nsynet/electronics_project2/Medtronic_PB560呼吸机开源资料(3D图纸_原理图_说明书_软件代码等)/Medtronic PB560 ventilator-system-file-set-1/Electrical Schematics/PB560 - Electrical Schematics/4096600E03001_CPU BOARD SCH.pdf

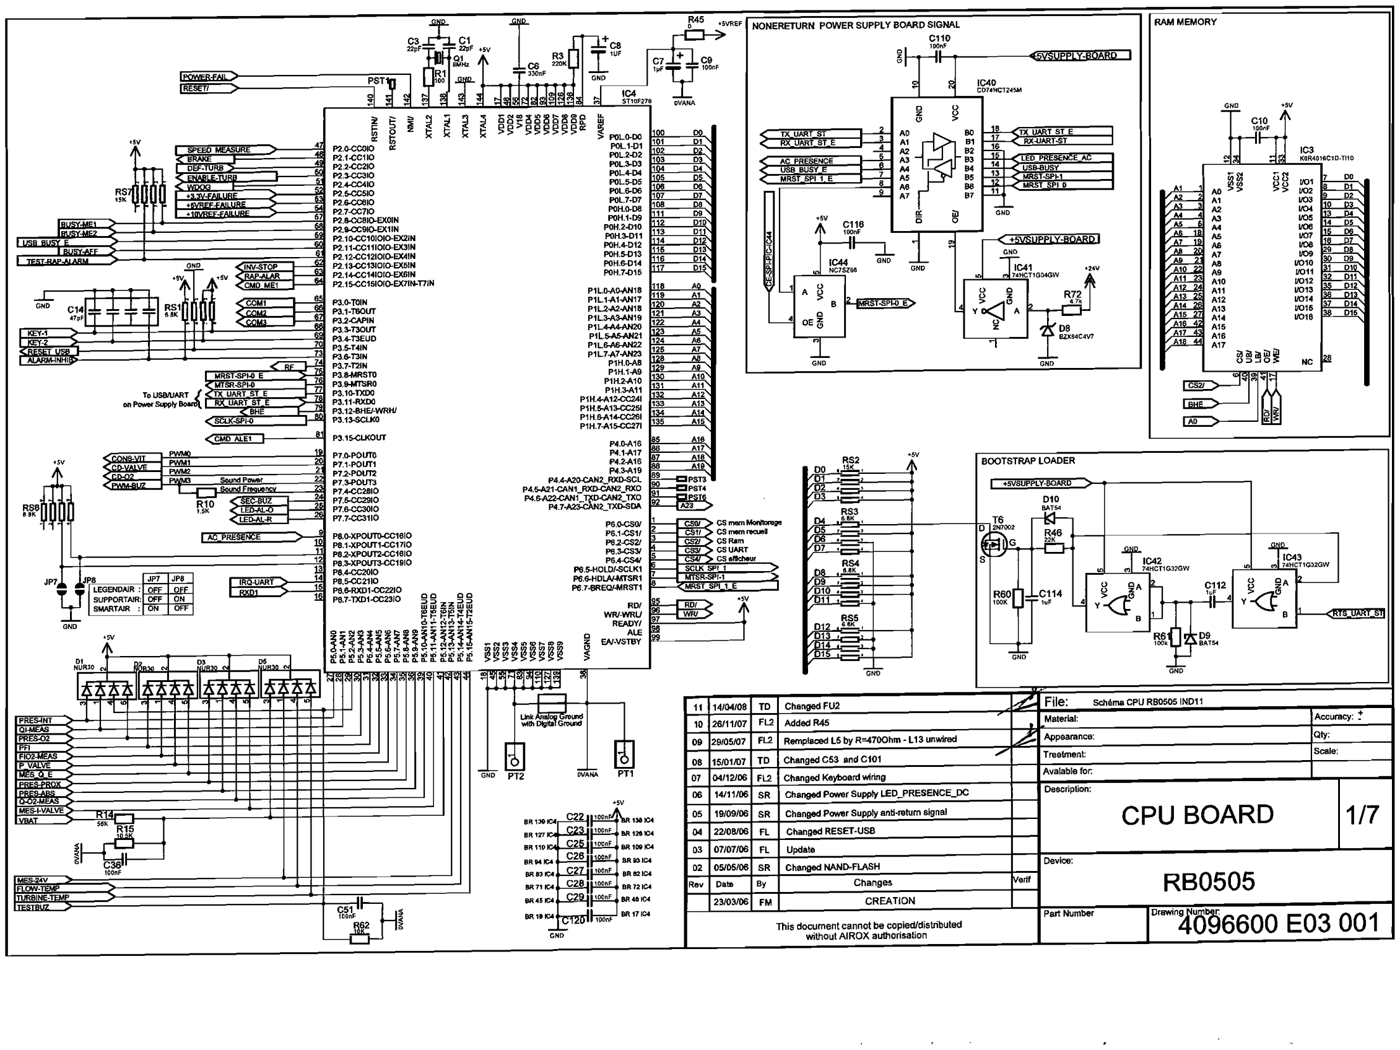
[picture p3: page 1]
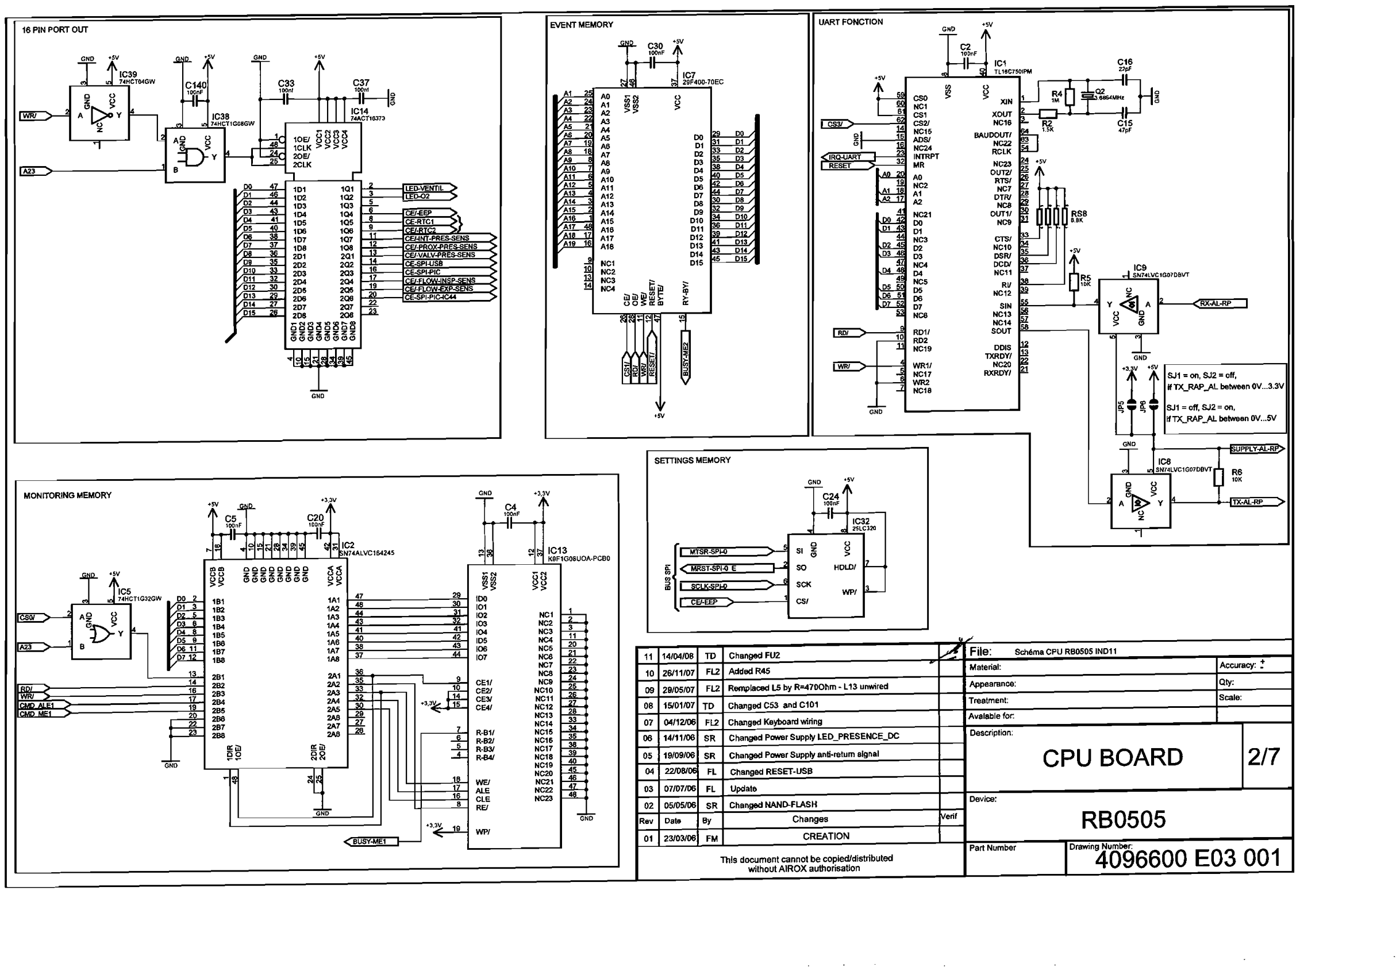
[picture p4: page 2]

1 100
105 lQ5
lm | | 1-
107 lQ7
108 | 108 201 | 2Ql
202 2-
203 | 2Q3 2 | 200
205 2W

MONITORING MEMORY

# CPU BOARD

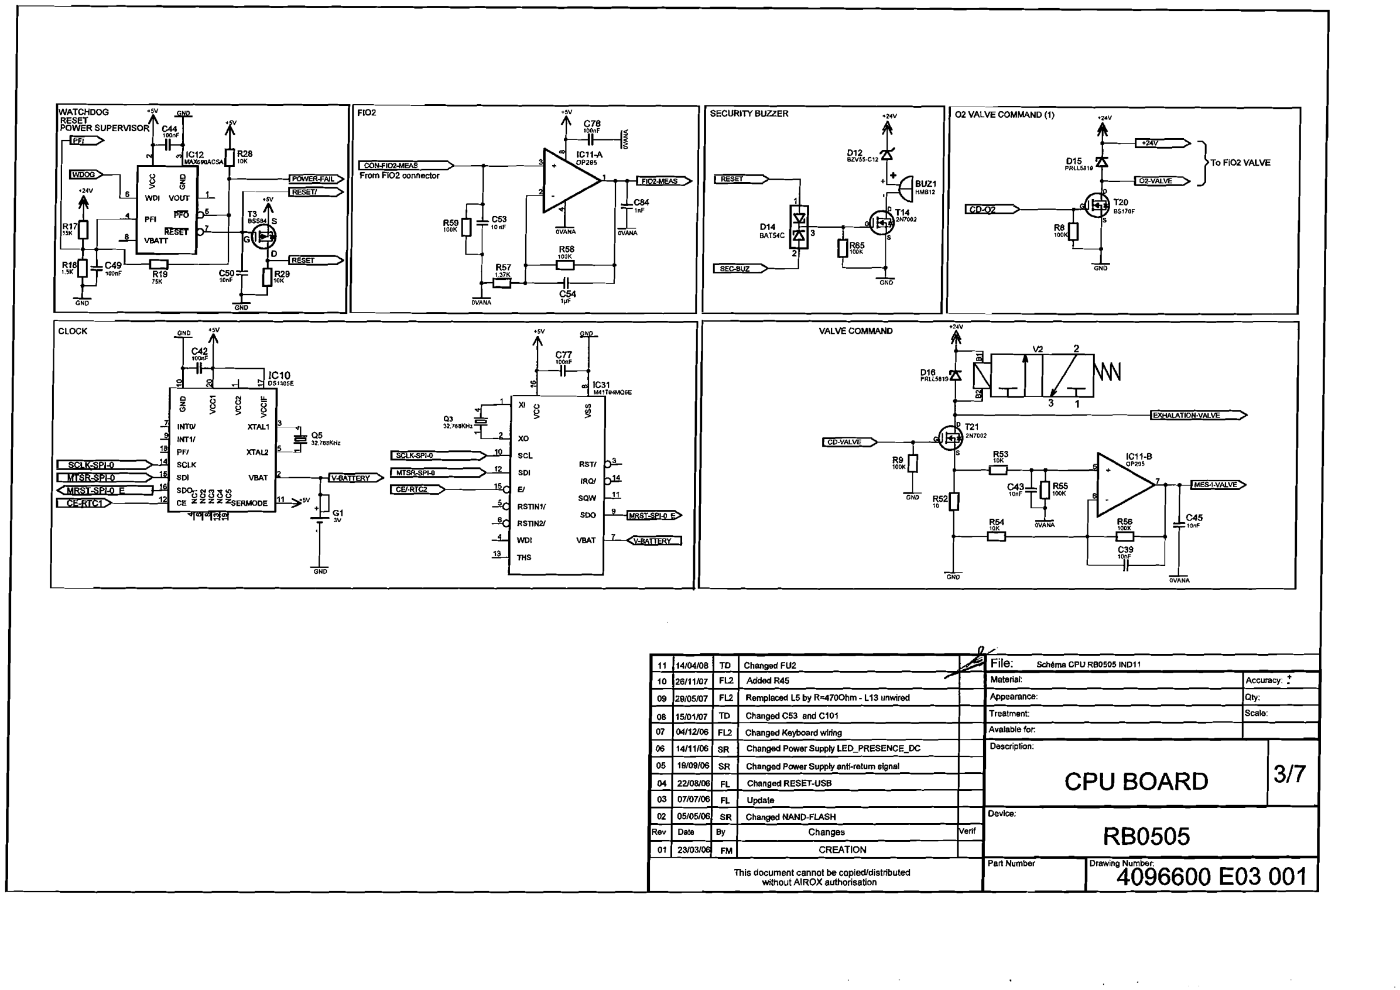
[picture p5: page 3]
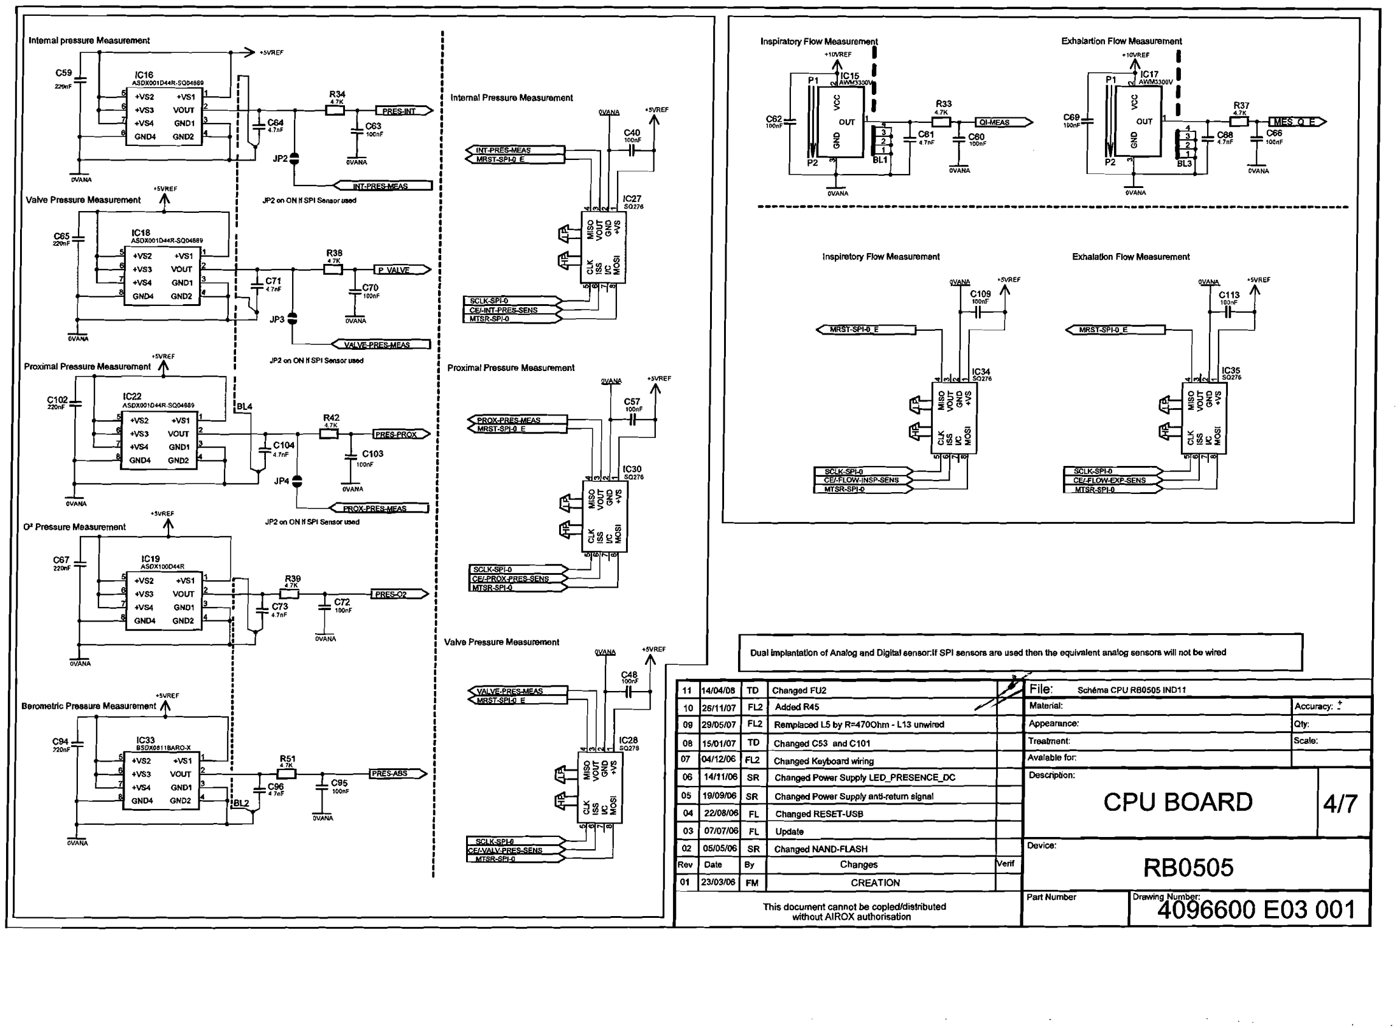
[picture p6: page 4]
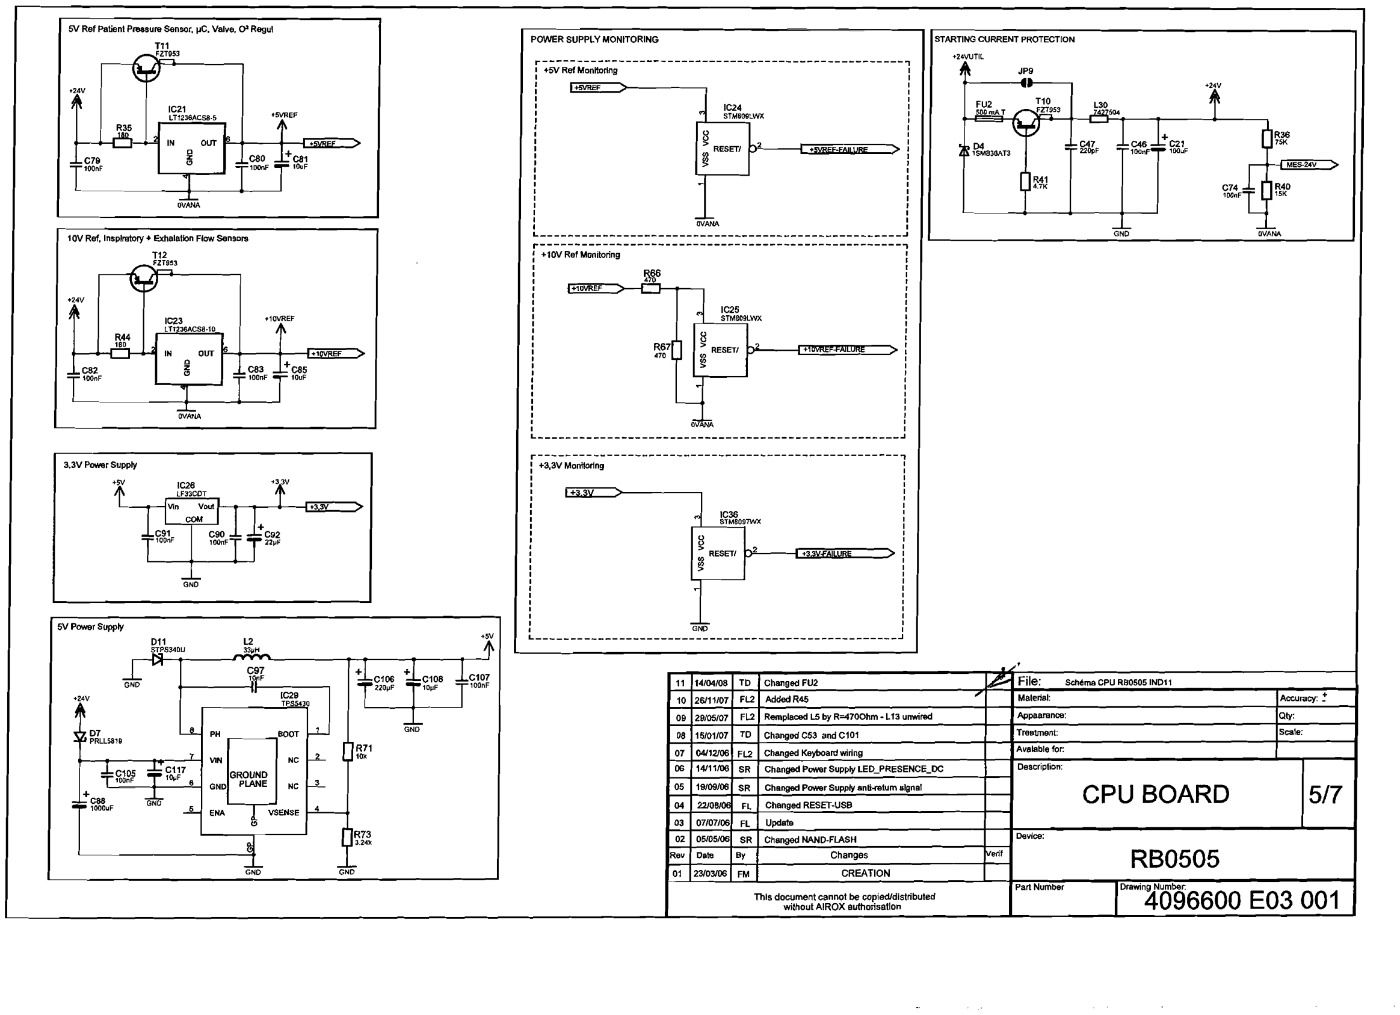
[picture p7: page 5]

( | 1 SV Rwf Paânt P-um | Senwrr. pC. Valve. W Rwgul | I
I I | I
1OV Rd. lnsplmtory + Exhalabn Flow Sanson | I
I | GND

POWER SUPPLY MONITORING

r----------------------------------------------------
: +1OV Re1 Monitoring | I

/?
File: | sdieme cpu ~eosos INDII
Maletisl: | (~ccuraq: f
OB 2BMSlo7 FL2 Remplad L5 by R4700hm - LI3 vmired | Appaaranm: | QtV:
08 15101107 TD Changed C53 and Cl01 | Trestmwnt: | Scdle:
07 04112106 FU | Chsnged Keyboaniwillng | Avalable for:
ffi lWlltC8 SR | Changed Paver Svpply LED-PRESENCE-DC | Description:
05 191081ffi SR | ChsM Power Supply anti-tum slgnsl
M WOBIffi FI. | Changed RESET-US0 | CPU BOARD | 517 -
03 07/07106 FL | UpdSl8 | 1 02 OWWffi SR Changed WD-FLASH | Cevice:
RBV Osie | By | Changes | vsdf
01 2YOYffi FM | CREATION
RB0505 Pari Number | Drawing Number

This document cannot be wpiedldistributed

without AIROX suihorisatlon | 1 4096600 E03 001

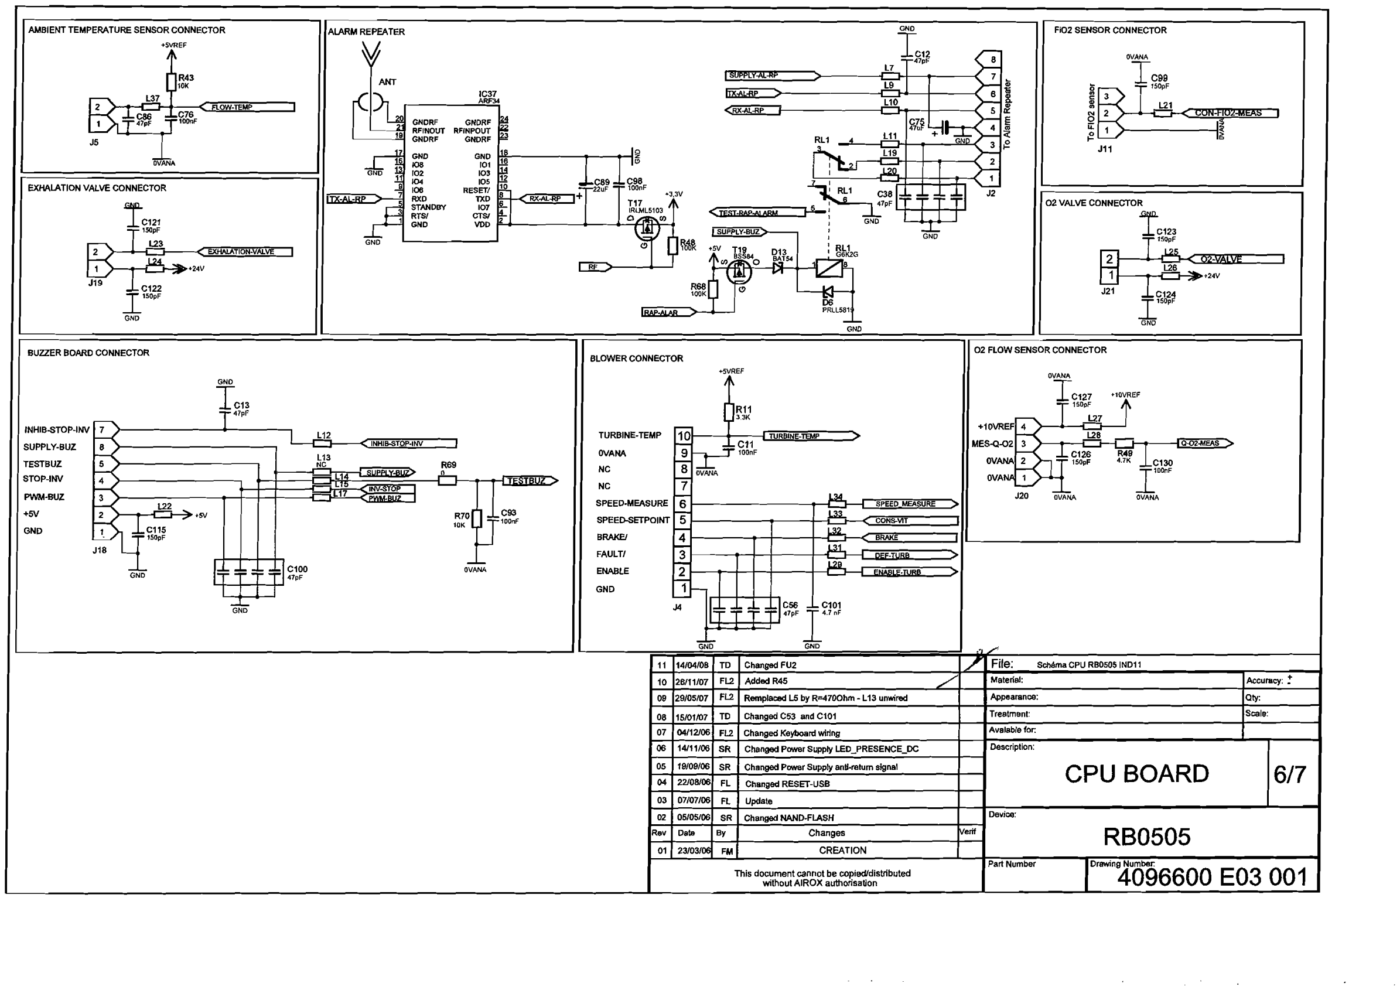
[picture p8: page 6]
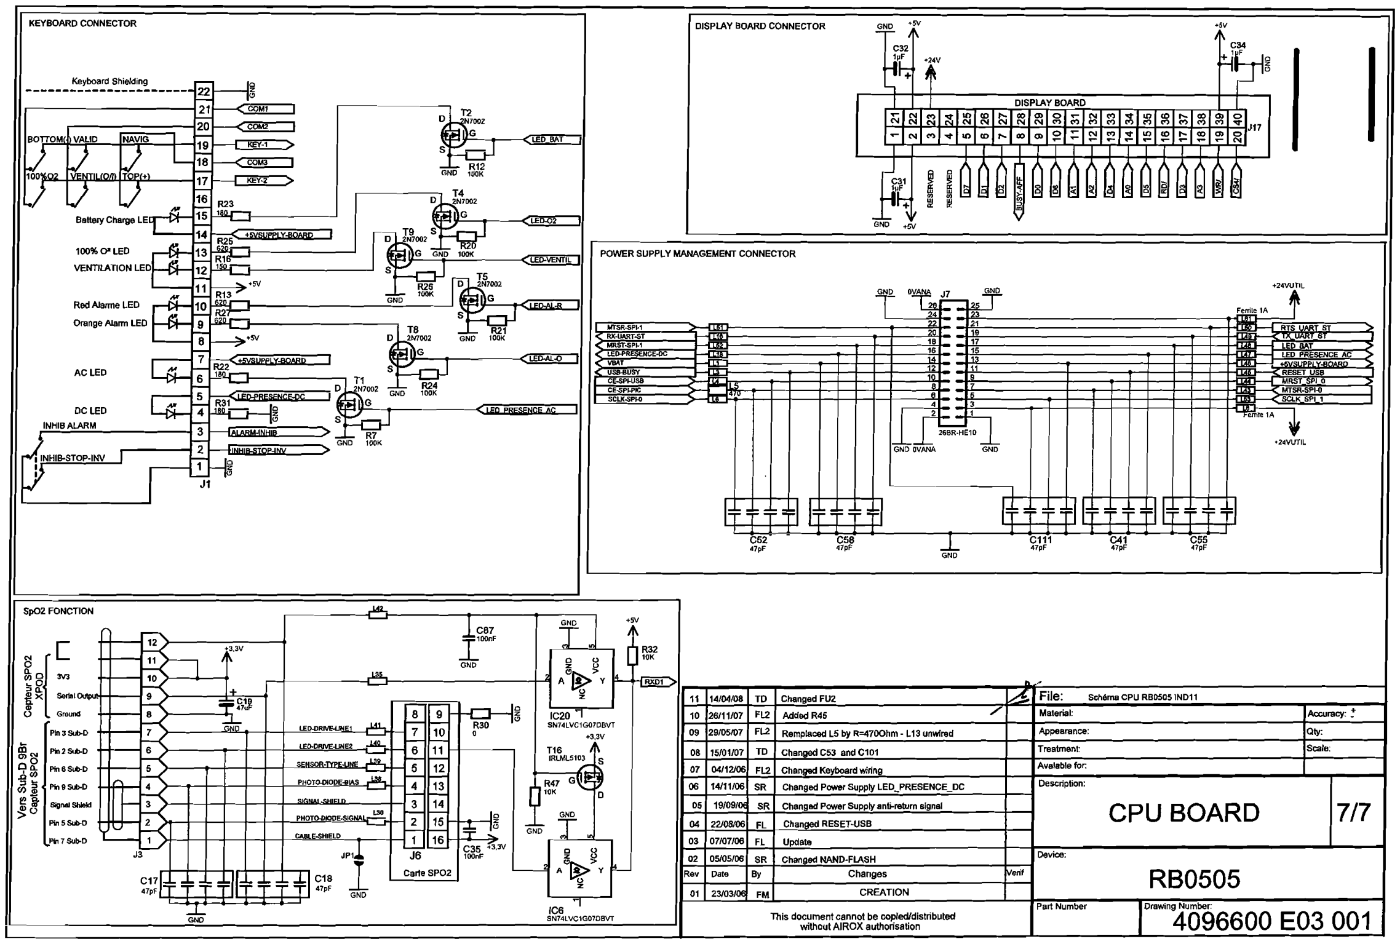
[picture p9: page 7]
