nsynet/electronics_project2/Medtronic_PB560呼吸机开源资料(3D图纸_原理图_说明书_软件代码等)/medtronic-pb560-ventilator-system-file-set-2/Electronic PCBAs/GR106769_CPU_PCBA/PCB/GR106772A00/Read-me.xls

 | Customer : |  | COVIDIEN
 | Designation : |  | CPU BOARD
 | Schem No :
 | Board No : |  | GR106772 | Ind. / Rev. | A
 | FEE File No : |  | CN004 | Ind. / Rev. | A
 | Artwork : Extended GERBER
 | Layers |  | Files
 | Parts Top |  | GR106772-A-CST.phd
 | Silkscreen Top |  | GR106772-A-SST.(phd,pdf)
 | Solder Paste Top |  | GR106772-A-SPT.phd
 | Solder Mask Top |  | GR106772-A-SMT.phd
 | Copper Top |  | GR106772-A-CLT.phd
 | Internal Copper 2 |  | GR106772-A-CL2.phd
 | Internal Copper 3 |  | GR106772-A-CL3.phd
 | Internal Copper 4 |  | GR106772-A-CL4.phd
 | Internal Copper 5 |  | GR106772-A-CL5.phd
 | Internal Copper 6
 | Internal Copper 7
 | Internal Copper 8
 | Internal Copper 9
 | Internal Copper 10
 | Internal Copper 11
 | Copper Bottom |  | GR106772-A-CLB.phd
 | Solder Mask Bottom |  | GR106772-A-SMB.phd
 | Solder Paste Bottom |  | GR106772-A-SPB.phd
 | Silkscreen Bottom |  | GR106772-A-SSB.(phd,pdf)
 | Parts Bottom |  | GR106772-A-CSB.phd
 | Outline |  | GR106772-A-OUT.phd
 | Holes |  | Non Plated Holes | Plated Holes
 | EXCELLON drill file |  | GR106772-A-NPTH.drd | GR106772-A-PTH.drd
 | Drill tool list |  | GR106772-A-NPTH.drl | GR106772-A-PTH.drl
 | Manufacturing |  | Files
 | Drill drawing |  | GR106772-PPD-A.(pdf,hpg,dxf)
 | Assembly drawing |  | GR106772-PEQ-A.(pdf,hpg,dxf)
 | Partlist |  | GR106772-A-partlist.doc
 | ASCII data |  | GR106772-A.(pcf,ftf)
 | IDF data |  | GR106772-A.(pro,brd)
 | Archive file Name : |  | GR106772-AI-A.zip
 |  | Files for manufacturing printed circuit |  |  | 2014-03-19
 |  |  |  |  | Page : 1/1
 |  | GR106772-A
France Etudes Electroniques Rue Jules Ferry 24130 - PRIGONRIEUX Tél: 05.53.24.63.11 Fax: 05.53.24.67.28 E-mail : fee@fee.fr
