nsynet/electronics_project2/Medtronic_PB560呼吸机开源资料(3D图纸_原理图_说明书_软件代码等)/medtronic-pb560-ventilator-system-file-set-2/Mechanical Part Drawings/4-007303-00/4-007303-00F00.pdf

REVISIONS

REV | DESCRIPTION
F | RELEASE/CHANGE PER EC107420

PROPRIETARY & CONFIDENTIAL: THIS DOCUMENT MAY NOT BE COPIED, DISCLOSED, OR USED IN WHOLE OR IN PART WITHOUT THE CONSENT OF MEDTRONIC
TITLE: DESCRIPTION SPECIFICATION BAG,8 X 10, PROTECTIVE | MEDTRONIC 6 1 3 5 G u n b a r r e l A v e n u e B o u l d e r , C o l o r a d o 8 0 3 0 1 © 2 018 M E D T R O N I C A L L R I G H T S R E S E R V E D .
DEC. | DEC. | DEC. | DRAWN: Karla Garcia DATE: 11/06/09 | SIZE | DRAWING NUMBER | REV.
.X ± | .XX ± | .XXX ± | CHECKED: J. Martinez DATE: 11/06/09 | A | 4-007303-00 | F
.1 | .01 | .001 | APPROVED: J. Martinez DATE: 11/06/09 | | SHEET 1 OF 1

GENERAL DIMENSIONAL
TOLERANCES

Template 10026665 Rev 200

## SPECIFICATION:

## BAG,8 X 10, PROTECTIVE

Description: BAG,8 X 10, PROTECTIVE

Material: Polyethylene bag

- Inside Dimensions: 8” (+/- 0.125”) x 10” (+/- 0.1875”)

Thickness: .00132” (+/- .000264”)

Skirt: 0.25” (+/-0.1875”)

Color: Clear

*Packaging:1750 Bags per roll
*Note: The precut is perform from corner to corner of the bag.

*Validated Suppliers for the Poly Bag:
Primary vendor: Southland Flex Products Corporation Secondary vendor: Automated PKG. systems.

The notes marked with the symbol *added in the specification for the TJ site.
- Key Inspection dimensions
