nsynet/electronics_project2/Medtronic_PB560呼吸机开源资料(3D图纸_原理图_说明书_软件代码等)/medtronic-pb560-ventilator-system-file-set-2/Electronic PCBAs/GR106769_CPU_PCBA/PCB/GR106772A00.pdf

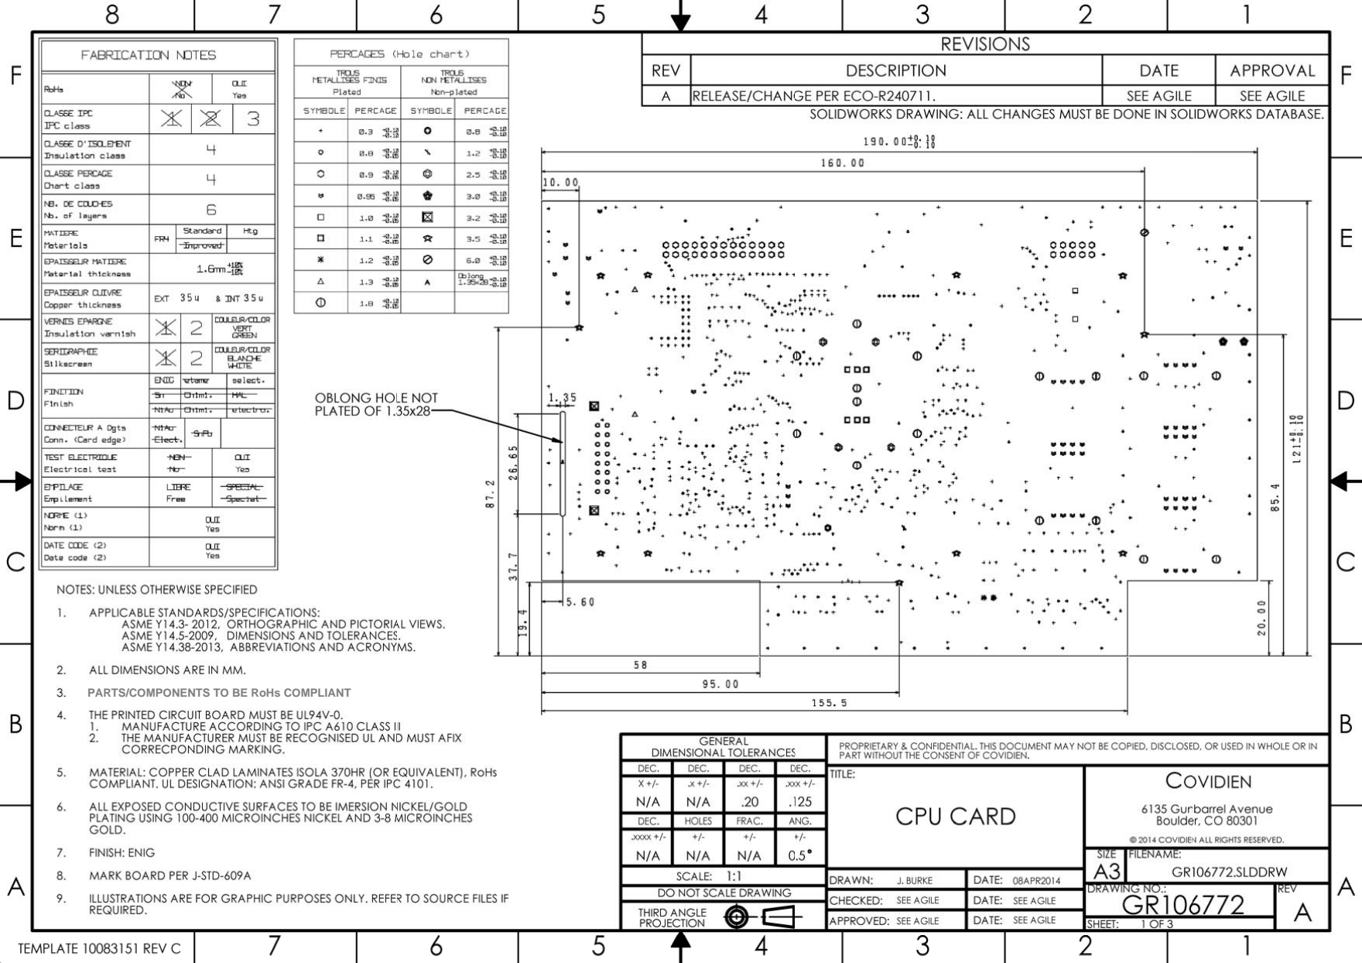
[picture p10: page 1]
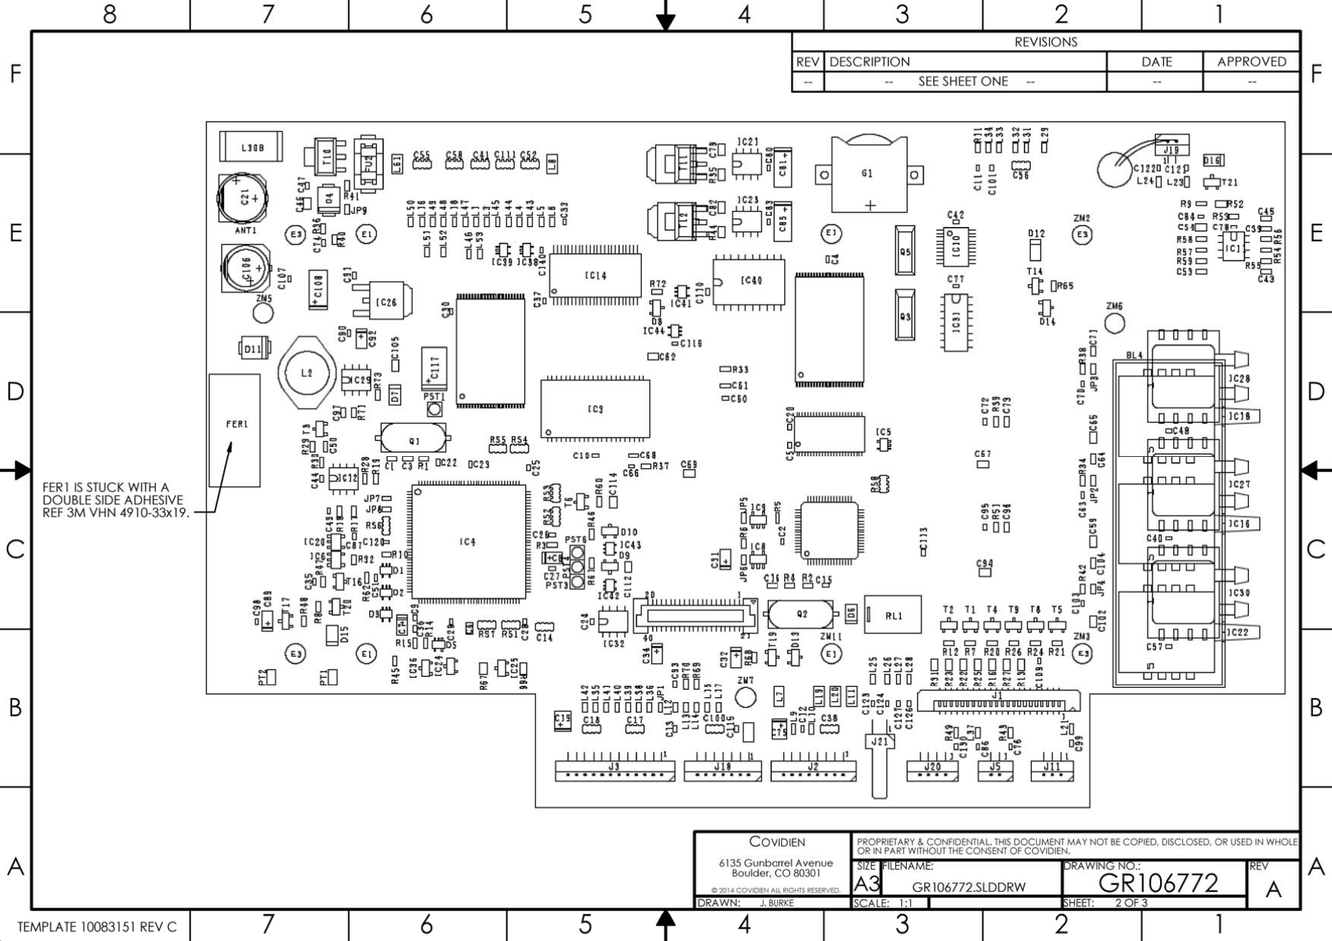
[picture p11: page 2]
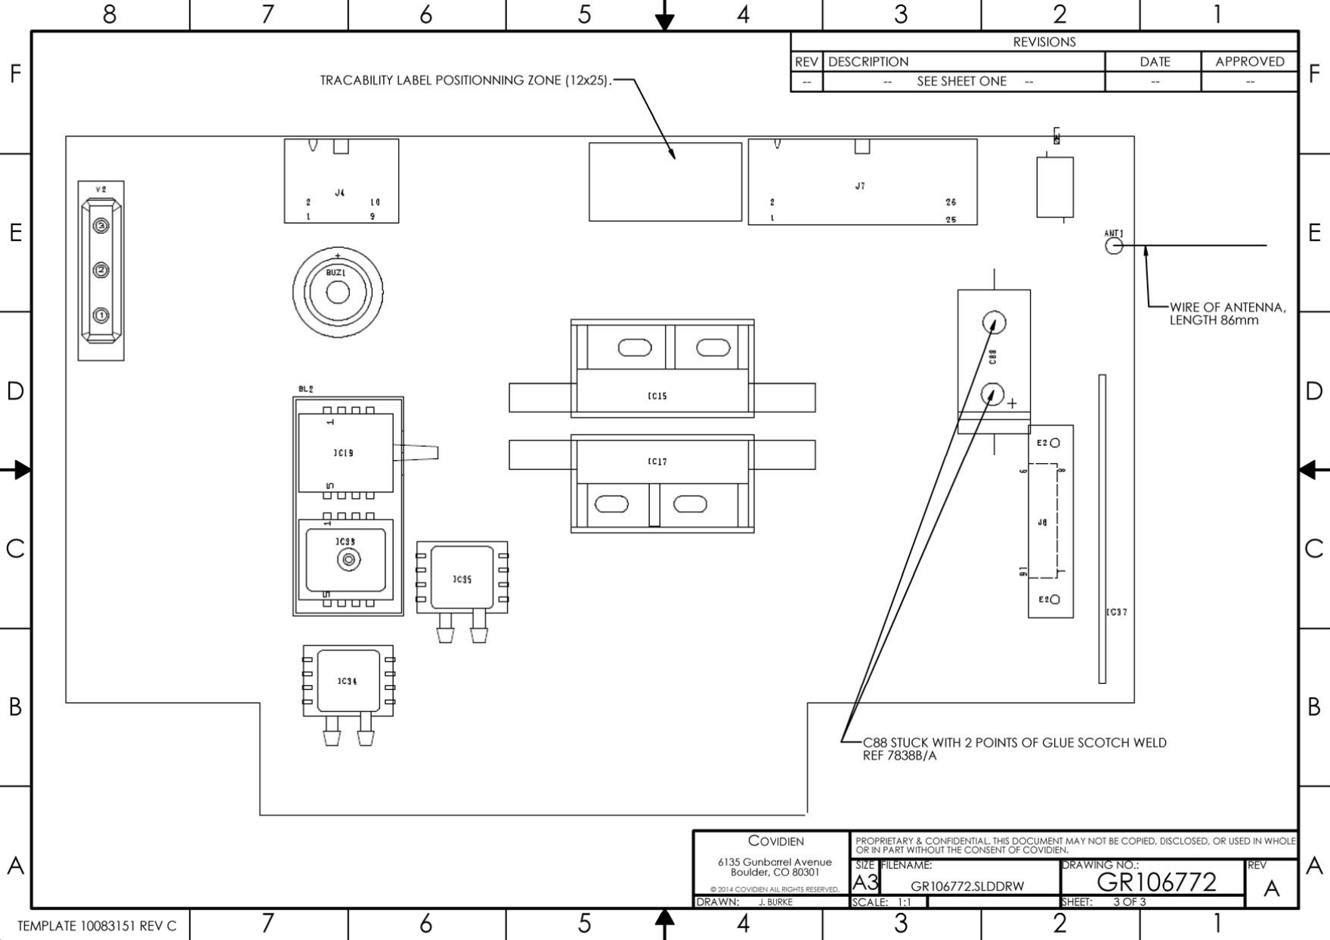
[picture p12: page 3]
