nsynet/electronics_project2/Medtronic_PB560呼吸机开源资料(3D图纸_原理图_说明书_软件代码等)/medtronic-pb560-ventilator-system-file-set-2/Electronic PCBAs/GR106769_CPU_PCBA/BOM/GR106769_CPU_PCBA_BOM.xls

Creator | Jenaro | Julio
Type
Description
Title Block
Item Number | Description | Subclass | Lifecycle Phase | Rev | Rev Incorp Date | Rev Release Date | Effectivity Date
GR106769 | CPU CARD | Part | Production | B ECO-R251873 | 20/Nov/2014 06:32:05 PM GMT | 25/Nov/2014 04:14:03 PM GMT | 30/Apr/2015 07:00:00 AM BST
Page Two
UOM | Additional Categories Part | Alternate Part(s) | Alternate FG Part(s) | Restricted Access | Vendor User Group | Data Classification | Attachment Destination | Created By | Create Date | Legacy Data Source | Divesture Destination
Each | PART CATEGORY|Pc Board |  |  |  |  | Confidential |  | Schilling, Sheila | 13/Feb/2014 03:52:48 PM GMT | Agile RMS
Page Three
Product Family(s) | Item Type | Lot Serial Control | Document Number | RoHS Compliant | Bio Approval Number | Integration Description | Project(s) | Notes | Handling/Storage | Legacy Number
 | Customized | None | NODOCUMENT | Unknown |  | CPU CARD | RSP - PB560-520 | Product Family : RSP - VENTILATOR SYSTEMS, Commodity Code: BPCS Add-Updt : FC02.17, Country of Origin: BPCS Add : FR = FRANCE, Shelf Life Days:BPCS Add-Updt : 0, Must Single Issue: BPCS Add : NO, Item Class: BPCS Add-Updt : GL-66 PB500 Series Ventilators/Gen 1, Controlled AML? : YES
BOM
Level | Attachments (Image) | Manufacturer (Image) | Pending Changes (Image) | Has Been Redlined (Image) | Has Quality(Image) | Bubble Number | Item Number | Item Description | Item Rev | Qty | UOM | Item Lifecycle Phase | BOM Notes | Ref Des | Component Effective From | Component Discontinue Date | Alternate Part(s) | Alternate FG Part(s) | Alternate Document(s) | Subclass | Sites | Planned? | Scrap Factor | OP # | Thumbnail | Attachments(Image) | Manufacture Part Has Redline | Mfr. Name | Mfr. Part Number | Mfr. Part Description | Mfr. Part Lifecycle Phase | Preferred Status | Sites | Reference Notes | RoHS Compliant? | RoHS Compliance Statement
1 | true | true | false | false | false | 0 | 10020993 | QUARTZ, 8 MHZ, 100PPM,SMD | C ECO-R252636 | 1 | Each | Production |  | Q1 |  |  |  |  |  | Part | CBRM |  | 1 |  |  | true | false | IQD | LFXTAL003151REEL |  | Active | Preferred |  |  | Yes | Legacy Inventory Status: Cleared
1 | true | true | false | false | false | 0 | 10020994 | DIODE ZENER, 500MW, 12V, SOD-80C | C ECO-R252636 | 1 | Each | Production |  | D12 |  |  |  |  |  | Part | CBRM |  | 1 |  |  | true | false | NXP SEMICONDUCTORS_RMS1 | BZV55-C12,115 |  | Active | Preferred |  | ROHS EXEMPT : 7(C)1 AND 5 (A) | Yes - by exemption | Legacy Inventory Status: Cleared
 |  |  |  |  |  |  |  |  |  |  |  |  |  |  |  |  |  |  |  |  |  |  |  |  |  | true | false | NXP SEMICONDUCTORS_RMS1 | BZV55-C12 | VOLTAGE REGULATOR DIODE | Active | Preferred |  | ROHS EXEMPT : 7(C)1 AND 5 (A) | Yes - by exemption | Legacy Inventory Status: Cleared
1 | true | true | true | false | false | 0 | 10022135 | CAPACITOR CERAMIC, 100NF, +/-10%, 50V, X7R,0805 | C ECO-R252633 | 6 | Each | Production |  | C46,C62,C69,C79,C82,C105 |  |  |  |  |  | Part | CBRM |  | 1 |  |  | true | false | YAGEO_RMS1 | 223858055649 | CAPACITOR, CERAMIC, MULTILAYER, 50 V, X7R, 0.1 UF, SURFACE MOUNT, 0805 | Active | Preferred |  | BRAND: PHYCOMP | Yes | Legacy Inventory Status: Cleared
 |  |  |  |  |  |  |  |  |  |  |  |  |  |  |  |  |  |  |  |  |  |  |  |  |  | true | false | MURATA MANUFACTURING CO., LTD. | GRM21BR71H104KA01L | MONOLITHIC CERAMIC CAPACITOR | Active | Preferred |  |  | Yes | Legacy Inventory Status: Cleared
 |  |  |  |  |  |  |  |  |  |  |  |  |  |  |  |  |  |  |  |  |  |  |  |  |  | true | false | YAGEO_RMS1 | 223858015649 | CAPACITOR, CERAMIC, MULTILAYER, 50 V, X7R, 0.1 UF, SURFACE MOUNT, 0805 | Active | Preferred |  | BRAND: PHYCOMP | Yes | Legacy Inventory Status: Cleared
 |  |  |  |  |  |  |  |  |  |  |  |  |  |  |  |  |  |  |  |  |  |  |  |  |  | true | false | SAMSUNG_RMS1 | CL21B104KBCNNNC | MULTILAYER CERAMIC CAPACITOR | Active | Preferred |  |  | Yes | Legacy Inventory Status: Cleared
 |  |  |  |  |  |  |  |  |  |  |  |  |  |  |  |  |  |  |  |  |  |  |  |  |  | true | false | YAGEO_RMS1 | CC0805KRX7R9BB104 | CAP CER .1UF 50V 10% X7R 0805 | Active | Preferred |  |  | Yes | Legacy Inventory Status: Cleared
 |  |  |  |  |  |  |  |  |  |  |  |  |  |  |  |  |  |  |  |  |  |  |  |  |  | true | false | AVX_RMS1 | 08055C104KAT2A | CAPACITOR CERAMIC, 100NF, +/-10%, 50V, X7R,0805, X7R DIELECTRIC | Active | Preferred |  |  | Yes | Legacy Inventory Status: Cleared
1 | true | true | false | false | false | 0 | 10022157 | TRANSISTOR, P CHANNEL, 50V, 0.13A, 5 OHM, SOT23 | C ECO-R252636 | 2 | Each | Production |  | T3,T19 |  |  |  |  |  | Part | CBRM |  | 1 |  |  | true | false | NXP SEMICONDUCTORS_RMS1 | BSS84 | MOSFET P CHANNEL | Active | Preferred |  |  | Yes | Legacy Inventory Status: Cleared
 |  |  |  |  |  |  |  |  |  |  |  |  |  |  |  |  |  |  |  |  |  |  |  |  |  | true | false | ON SEMICONDUCTOR_RMS1 | BSS84LT1G | POWER MOSFET | Active | Preferred |  |  | Yes | Legacy Inventory Status: Cleared
 |  |  |  |  |  |  |  |  |  |  |  |  |  |  |  |  |  |  |  |  |  |  |  |  |  | true | false | NXP SEMICONDUCTORS_RMS1 | BSS84,215 |  | Active | Preferred |  |  | Yes | Legacy Inventory Status: Cleared
1 | true | true | false | false | false | 0 | 10022505 | UART, LQFP64 | B ECO-R252636 | 1 | Each | Production |  | IC1 |  |  |  |  |  | Part | CBRM |  | 1 |  |  | true | false | TEXAS INSTRUMENTS_RMS1 | TL16C750IPM | UART | Active | Preferred |  | ROHS EXEMPT: 15 | Yes - by exemption | Legacy Inventory Status: Cleared
1 | true | true | true | false | false | 0 | 10022508 | CAPACITOR CERAMIC,10NF,+/-10%,50V,0603 | C ECO-R252633 | 6 | Each | Production |  | C39,C43,C45,C50,C53,C97 |  |  |  |  |  | Part | CBRM |  | 1 |  |  | true | false | YAGEO_RMS1 | 223858615636 | CAPACITOR, CERAMIC, MULTILAYER, 50 V, X7R, 0.01 UF, SURFACE MOUNT, 0603 | Active | Preferred |  | BRAND: PHYCOMP | Yes | Legacy Inventory Status: Cleared
 |  |  |  |  |  |  |  |  |  |  |  |  |  |  |  |  |  |  |  |  |  |  |  |  |  | true | false | YAGEO_RMS1 | 223858615536 | CAPACITOR, CERAMIC, MULTILAYER, 50 V, X7R, 0.01 UF, SURFACE MOUNT, 0603 | Active | Preferred |  | BRAND: PHYCOMP | Yes | Legacy Inventory Status: Cleared
 |  |  |  |  |  |  |  |  |  |  |  |  |  |  |  |  |  |  |  |  |  |  |  |  |  | true | false | KEMET_RMS1 | C0603C103K5RACTU | CERAMIC CHIP CAPACITOR | Active | Preferred |  |  | Yes | Legacy Inventory Status: Cleared
 |  |  |  |  |  |  |  |  |  |  |  |  |  |  |  |  |  |  |  |  |  |  |  |  |  | true | false | YAGEO_RMS1 | CC0603KRX7R9BB103 | CAPACITOR, CERAMIC, MULTILAYER, 50 V, X7R, 0.01 UF, SURFACE MOUNT, 0603 | Active | Preferred |  |  | Yes | Legacy Inventory Status: Cleared
1 | true | true | true | false | false | 0 | 10022510 | CAPACITOR,330NF,+/-10%,16V,0805,X7R | C ECO-R252633 | 1 | Each | Production |  | C6 |  |  |  |  |  | Part | CBRM |  | 1 |  |  | true | false | YAGEO_RMS1 | 222278015556 | CAPACITOR, CERAMIC, MULTILAYER, 16 V, X7R, 0.33 UF, SURFACE MOUNT, 0805 | Active | Preferred |  | BRAND: PHYCOMP | Yes | Legacy Inventory Status: Cleared
 |  |  |  |  |  |  |  |  |  |  |  |  |  |  |  |  |  |  |  |  |  |  |  |  |  | true | false | TDK_RMS1 | C2012X7R1C334KT | CERAMIC MULTILAYER CAPACITOR | Active | Preferred |  |  | Yes | Legacy Inventory Status: Cleared
 |  |  |  |  |  |  |  |  |  |  |  |  |  |  |  |  |  |  |  |  |  |  |  |  |  | true | false | KEMET_RMS1 | C0805C334K4RACTU | CERAMIC SURFACE MOUNT - X7R DIELECTRIC | Active | Preferred |  |  | Yes | Legacy Inventory Status: Cleared
 |  |  |  |  |  |  |  |  |  |  |  |  |  |  |  |  |  |  |  |  |  |  |  |  |  | true | false | YAGEO_RMS1 | 222278015656 | CAPACITOR, CERAMIC, MULTILAYER, 16 V, X7R, 0.33 UF, SURFACE MOUNT, 0805 | Active | Preferred |  | BRAND: PHYCOMP | Yes | Legacy Inventory Status: Cleared
 |  |  |  |  |  |  |  |  |  |  |  |  |  |  |  |  |  |  |  |  |  |  |  |  |  | true | false | YAGEO_RMS1 | CC0805KKX7R7BB334 | CAPACITOR, CERAMIC, MULTILAYER, 16 V, X7R, 0.33 UF, SURFACE MOUNT, 0805 | Active | Preferred |  |  | Yes | Legacy Inventory Status: Cleared
1 | true | true | false | false | false | 0 | 10022511 | TRANSCEIVER, 3.3V TO 5V,TSSOP | C ECO-R252636 | 1 | Each | Production |  | IC2 |  |  |  |  |  | Part | CBRM |  | 1 |  |  | true | false | TEXAS INSTRUMENTS_RMS1 | SN74ALVC164245DGGR |  | Active | Preferred |  | ROHS EXEMPT-15 | Yes - by exemption | Legacy Inventory Status: Cleared
 |  |  |  |  |  |  |  |  |  |  |  |  |  |  |  |  |  |  |  |  |  |  |  |  |  | true | false | TEXAS INSTRUMENTS_RMS1 | 74ALVC164245DGGTE4 | TRANSCEIVER | Active | Preferred |  | ROHS EXEMPT-15 | Yes - by exemption | Legacy Inventory Status: Cleared
 |  |  |  |  |  |  |  |  |  |  |  |  |  |  |  |  |  |  |  |  |  |  |  |  |  | true | false | TEXAS INSTRUMENTS_RMS1 | SN74ALVC164245DGGT | TRANSCEIVER 3.3V TO 5V | Active | Preferred |  | ROHS EXEMPT-15 | Yes - by exemption | Legacy Inventory Status: Cleared
 |  |  |  |  |  |  |  |  |  |  |  |  |  |  |  |  |  |  |  |  |  |  |  |  |  | true | false | TEXAS INSTRUMENTS_RMS1 | 74ALVC164245DGGRG4 |  | Active | Alternate |  | ROHS EXEMPT-15 | Yes - by exemption | Legacy Inventory Status: Cleared
1 | true | true | true | false | false | 0 | 10022542 | CONNECTOR, O2 VALVE, 2 CONTACTS | C ECO-R252633 | 1 | Each | Production |  | J21 |  |  |  |  |  | Part | CBRM |  | 1 |  |  | true | false | MOLEX_RMS1 | 22057028 |  | Active | Preferred |  |  | Yes | Legacy Inventory Status: Cleared
1 | true | true | false | false | false | 0 | 10022544 | RESISTOR, 470 OHM, 0.063W, +/-5% | C ECO-R252636 | 1 | Each | Production |  | L5 |  |  |  |  |  | Part | CBRM |  | 1 |  |  | true | false | YAGEO_RMS1 | 232270260471 | RESISTOR, METAL GLAZE/THICK FILM, 0.1 W, 5 %, 100 PPM, 470 OHM, SURFACE MOUNT, 0603 | Active | Preferred |  | BRAND: PHYCOMP. ROHS EXEMPT: 7(C)-1 | Yes - by exemption | Legacy Inventory Status: Cleared
 |  |  |  |  |  |  |  |  |  |  |  |  |  |  |  |  |  |  |  |  |  |  |  |  |  | true | false | VISHAY_RMS1 | CRCW0603470RJNEA | RESISTOR | Active | Preferred |  | ROHS EXEMPT: 7(C)-1 | Yes - by exemption | Legacy Inventory Status: Cleared
 |  |  |  |  |  |  |  |  |  |  |  |  |  |  |  |  |  |  |  |  |  |  |  |  |  | true | false | YAGEO_RMS1 | 232270260471L | RESISTOR, METAL GLAZE/THICK FILM, 0.1 W, 5 %, 100 PPM, 470 OHM, SURFACE MOUNT, 0603 | Active | Preferred |  | BRAND: PHYCOMP.ROHS EXEMPT: 7(C)-1 | Yes - by exemption | Legacy Inventory Status: Cleared
 |  |  |  |  |  |  |  |  |  |  |  |  |  |  |  |  |  |  |  |  |  |  |  |  |  | true | false | ASJ | CR16-471JL | THICK FILM CHIP RESISTOR | Active | Preferred |  | ROHS EXEMPT: 7(C)-1 | Yes - by exemption | Legacy Inventory Status: Cleared
 |  |  |  |  |  |  |  |  |  |  |  |  |  |  |  |  |  |  |  |  |  |  |  |  |  | true | false | YAGEO_RMS1 | RC0603JR-07470RL | RESISTOR, METAL GLAZE/THICK FILM, 0.1 W, 5 %, 100 PPM, 470 OHM, SURFACE MOUNT, 0603 | Active | Preferred |  | ROHS EXEMPT: 7(C)-1 | Yes - by exemption | Legacy Inventory Status: Cleared
1 | true | true | false | false | false | 0 | 10022607 | CAPACITOR,100NF,16V,+/-10%,X7R,0402 | D EC113997 | 45 | Each | Production |  | C2,C4,C5,C9,C10,C11,C20,C22,C23,C24,C25,C26,C27,C28,C29,C30,C33,C36,C37,C42,C44,C49,C51,C60,C63,C66,C70,C74,C76,C77,C78,C80,C83,C87,C90,C91,C93,C95,C98,C103,C107,C110,C116,C120,C140 |  |  |  |  |  | Part | CBRM |  | 1 |  |  | true | false | MURATA | GRM155R71C104JA88J | CAPACITOR, CERAMIC, MULTILAYER, 16V, X7R, 0.1UF, 0402 | Active | Preferred |  |  | Yes | CLEARED
 |  |  |  |  |  |  |  |  |  |  |  |  |  |  |  |  |  |  |  |  |  |  |  |  |  | true | false | YAGEO_RMS1 | CC0402KRX7R7BB104 | CAP CER 0.1uF 16V X7R 10% 0402 | Active | Preferred |  |  | RoHS3 Compliant | Cleared
 |  |  |  |  |  |  |  |  |  |  |  |  |  |  |  |  |  |  |  |  |  |  |  |  |  | true | false | YAGEO_RMS1 | 223878715649 | CAPACITOR, CERAMIC, MULTILAYER, 16 V, X7R, 0.1 UF, SURFACE MOUNT, 0402 | Active | Preferred |  | BRAND: PHYCOMP | Yes | Legacy Inventory Status: Cleared
 |  |  |  |  |  |  |  |  |  |  |  |  |  |  |  |  |  |  |  |  |  |  |  |  |  | true | false | MURATA MANUFACTURING CO., LTD. | GRM155R71C104KA88D | MONOLITHIC CERAMIC CAPACITOR | Active | Preferred |  |  | Yes | Legacy Inventory Status: Cleared
1 | false | true | false | false | false | 0 | 10022608 | CAPACITOR TANTALUM, 10UF, 25V, +/-10% | D EC074855 | 3 | Each | Production |  | C81,C85,C108 |  |  |  |  |  | Part | CBRM |  | 1 |  |  | true | false | KEMET | T491C106K025AT | Cap, Tantalum, Polarized, 25V, 10% +/-Tol, 10uF, Surface Mount, 2312 (Case C), EIA Metric 6032 | Active | Alternate |  |  | Yes | Cleared
 |  |  |  |  |  |  |  |  |  |  |  |  |  |  |  |  |  |  |  |  |  |  |  |  |  | true | false | KEMET | T495C106K025ATE275 | Cap, Tantalum, Polarized, 25V, 10% +/-Tol, 10uF, Surface Mount, 2312 (Case C), EIA Metric 6032 | Active | Preferred |  |  | Yes | Cleared
1 | true | true | false | false | false | 0 | 10022612 | MICROCONTROLLER, 16BITS, 512BYTE FLASH, 320KBYTE XFLASH | B ECO-R252636 | 1 | Each | Production |  | IC4 |  |  |  |  |  | Part | CBRM |  | 1 |  |  | true | false | STMICROELECTRONICS | ST10F276Z5T3 | 16-BIT MCU WITH MAC UNIT,832 KBYTE FLASH MEMORY,68 KBYTE RAM | Active | Preferred |  |  | Yes | Legacy Inventory Status: Cleared
1 | true | true | false | false | false | 0 | 10022613 | CAPACITOR CERAMIC,4.7NF,+/-10%,50V,0603 | C ECO-R252636 | 6 | Each | Production |  | C61,C64,C68,C71,C96,C104 |  |  |  |  |  | Part | CBRM |  | 1 |  |  | true | false | KEMET_RMS1 | C0603C472K5RACTU | CAP 4700PF 50V CERAMIC X7R 0603 | Active | Alternate |  |  | Yes | Legacy Inventory Status: Cleared
 |  |  |  |  |  |  |  |  |  |  |  |  |  |  |  |  |  |  |  |  |  |  |  |  |  | true | false | YAGEO_RMS1 | CC0603KRX7R9BB472 |  | Active | Preferred |  |  | Yes | Legacy Inventory Status: Cleared
1 | true | true | false | false | false | 0 | 10022617 | RESISTOR, 4.7 K OHM, 0.063W +/-5% | C ECO-R252636 | 8 | Each | Production |  | R33,R34,R37,R38,R41,R42,R51,R72 |  |  |  |  |  | Part | CBRM |  | 1 |  |  | true | false | ASJ | CR16-472JL | THICK FILM CHIP RESISTOR | Active | Preferred |  | ROHS EXEMPTION ; 7(C)-1 | Yes - by exemption | Legacy Inventory Status: Cleared
 |  |  |  |  |  |  |  |  |  |  |  |  |  |  |  |  |  |  |  |  |  |  |  |  |  | true | false | YAGEO_RMS1 | 232270260472L | RESISTOR, METAL GLAZE/THICK FILM, 0.1 W, 5 %, 100 PPM, 4700 OHM, SURFACE MOUNT, 0603 | Active | Preferred |  | BRAND: PHYCOMP.ROHS EXEMPTION ; 7(C)-1 | Yes - by exemption | Legacy Inventory Status: Cleared
 |  |  |  |  |  |  |  |  |  |  |  |  |  |  |  |  |  |  |  |  |  |  |  |  |  | true | false | YAGEO_RMS1 | RC0603JR-074K7L | RESISTOR, METAL GLAZE/THICK FILM, 0.1 W, 5 %, 100 PPM, 4700 OHM, SURFACE MOUNT, 0603 | Active | Preferred |  | ROHS EXEMPTION ; 7(C)-1 | Yes - by exemption | Legacy Inventory Status: Cleared
 |  |  |  |  |  |  |  |  |  |  |  |  |  |  |  |  |  |  |  |  |  |  |  |  |  | true | false | YAGEO_RMS1 | 232270260472 | RESISTOR, METAL GLAZE/THICK FILM, 0.1 W, 5 %, 100 PPM, 4700 OHM, SURFACE MOUNT, 0603 | Active | Preferred |  | BRAND: PHYCOMP.ROHS EXEMPTION ; 7(C)-1 | Yes - by exemption | Legacy Inventory Status: Cleared
1 | true | true | false | false | false | 0 | 10022622 | CAPACITOR ELECTROLYTIC, 220UF,16V+/-20% | C ECO-R252636 | 1 | Each | Production |  | C106 |  |  |  |  |  | Part | CBRM |  | 1 |  |  | true | false | PANASONIC_RMS1 | EEEFK1C221P | ALUMINUM ELETROLYTIC CAPACITORS/FK | Active | Preferred |  |  | Yes | Legacy Inventory Status: Cleared
 |  |  |  |  |  |  |  |  |  |  |  |  |  |  |  |  |  |  |  |  |  |  |  |  |  | true | false | ELNA AMERICA, INC. | RVD-16V221MG68U-R |  | Active | Preferred |  |  | Yes | Legacy Inventory Status: Cleared
 |  |  |  |  |  |  |  |  |  |  |  |  |  |  |  |  |  |  |  |  |  |  |  |  |  | true | false | ELNA AMERICA, INC. | RVZ-16V221MG68U | CHIP TYPE, LOW IMPEDANCE CAP. | Active | Preferred |  |  | Yes | Legacy Inventory Status: Cleared
1 | true | true | false | false | false | 0 | 10022623 | CAPACITOR,47 PF,+/-5%,50V,0402 | C ECO-R252636 | 4 | Each | Production |  | C12,C13,C15,C86 |  |  |  |  |  | Part | CBRM |  | 1 |  |  | true | false | SAMSUNG_RMS1 | CL05C470JB5NNNC | CAP CER 47PF 50V 5% NP0 0402 | Active | Preferred |  |  | Yes | Legacy Inventory Status: Cleared
 |  |  |  |  |  |  |  |  |  |  |  |  |  |  |  |  |  |  |  |  |  |  |  |  |  | true | false | KEMET_RMS1 | C0402C470J5GACTU | CAP,CER,SMT,0402,5%,50V,47PF | Active | Preferred |  | TAPE & REEL | Yes | Legacy Inventory Status: Cleared
 |  |  |  |  |  |  |  |  |  |  |  |  |  |  |  |  |  |  |  |  |  |  |  |  |  | true | false | MURATA MANUFACTURING CO., LTD. | GRM1555C1H470JZ01D | MONOLITHIC CERAMIC CAPACITOR | Active | Preferred |  |  | Yes | Legacy Inventory Status: Cleared
 |  |  |  |  |  |  |  |  |  |  |  |  |  |  |  |  |  |  |  |  |  |  |  |  |  | true | false | KEMET_RMS1 | C0402C470J5GAC | CAP,CER,SMT,0402,5%,50V,47PF | Active | Preferred |  |  | Yes | Legacy Inventory Status: Cleared
 |  |  |  |  |  |  |  |  |  |  |  |  |  |  |  |  |  |  |  |  |  |  |  |  |  | true | false | MURATA MANUFACTURING CO., LTD. | GRM1555C1H470JA01D | CAP CER 47PF 50V 5% NP0 0402 | Active | Preferred |  |  | Yes | Legacy Inventory Status: Cleared
1 | true | true | false | false | false | 0 | 10022632 | CAPACITOR CERAMIC,22PF,+/-5%,50V,0603 | C ECO-R252636 | 3 | Each | Production |  | C1,C3,C16 |  |  |  |  |  | Part | CBRM |  | 1 |  |  | true | false | SAMSUNG_RMS1 | CL10C220JB8NNNC | MULTILAYER CERAMIC CAPACITOR | Active | Preferred |  |  | Yes | Legacy Inventory Status: Cleared
 |  |  |  |  |  |  |  |  |  |  |  |  |  |  |  |  |  |  |  |  |  |  |  |  |  | true | false | YAGEO_RMS1 | CC0603JRNPO9BN220 | CAP CER 22PF 50V C0G 5% 0603 | Active | Preferred |  |  | RoHS3 Compliant | Cleared
 |  |  |  |  |  |  |  |  |  |  |  |  |  |  |  |  |  |  |  |  |  |  |  |  |  | true | false | YAGEO_RMS1 | 223886715229 | CAPACITOR, CERAMIC, MULTILAYER, 50 V, C0G, 0.000022 UF, SURFACE MOUNT, 0603 | Active | Preferred |  | BRAND: PHYCOMP | Yes | Legacy Inventory Status: Cleared
1 | true | true | false | false | false | 0 | 10022652 | DIODE SCHOTTKY, 30V, 200MA | C ECO-R252636 | 3 | Each | Production |  | D9,D10,D13 |  |  |  |  |  | Part | CBRM |  | 1 |  |  | true | false | NXP SEMICONDUCTORS_RMS1 | BAT54,215 |  | Active | Preferred |  |  | Yes | Legacy Inventory Status: Cleared
 |  |  |  |  |  |  |  |  |  |  |  |  |  |  |  |  |  |  |  |  |  |  |  |  |  | true | false | NXP SEMICONDUCTORS_RMS1 | BAT54 | SCHOTTKY BARRIER DOUBLE DIODE | Active | Preferred |  |  | Yes | Legacy Inventory Status: Cleared
1 | true | true | false | false | false | 0 | 10022653 | DIODE SCHOTTKY DOUBLE,30V, 200MA,SOT23 | C ECO-R252636 | 1 | Each | Production |  | D14 |  |  |  |  |  | Part | CBRM |  | 1 |  |  | true | false | NXP SEMICONDUCTORS_RMS1 | BAT54C,215 |  | Active | Preferred |  |  | Yes | Legacy Inventory Status: Cleared
 |  |  |  |  |  |  |  |  |  |  |  |  |  |  |  |  |  |  |  |  |  |  |  |  |  | true | false | NXP SEMICONDUCTORS_RMS1 | BAT54C | SCHOTTKY BARRIER DOUBLE DIODE | Active | Preferred |  |  | Yes | Legacy Inventory Status: Cleared
1 | true | true | false | false | false | 0 | 10022654 | DIODE TRANSIENT 600W,36V | C EC093850 | 1 | Each | Production |  | D4 |  |  |  |  |  | Part | CBRM |  | 1 |  |  | true | false | LITTLEFUSE | 1SMB36AT3G | ZENER TRANSIENT VOLTAGE SUPPRESSORS | Active | Preferred |  |  | Yes - by exemption | Cleared - Exemption 7a
 |  |  |  |  |  |  |  |  |  |  |  |  |  |  |  |  |  |  |  |  |  |  |  |  |  | true | false | ON SEMICONDUCTOR_RMS1 | 1SMB36AT3G | ZENER TRANSIENT VOLTAGE SUPPRESSORS | Active | Preferred |  | ROHS EXEMPT : 7(A) | Yes - by exemption | Legacy Inventory Status: Cleared
 |  |  |  |  |  |  |  |  |  |  |  |  |  |  |  |  |  |  |  |  |  |  |  |  |  | true | false | LITTLEFUSE | SZ1SMB36AT3G | ZENER TRANSIENT VOLTAGE SUPPRESSORS | Active | Preferred |  |  | Yes | Cleared
1 | true | true | false | false | false | 0 | 10022655 | DIODE ZENER, 0.35W,4.7V | C ECO-R252636 | 1 | Each | Production |  | D8 |  |  |  |  |  | Part | CBRM |  | 1 |  |  | true | false | NXP SEMICONDUCTORS_RMS1 | BZX84-C4V7 | VOLTAGE REGULATOR DIODE | Active | Preferred |  |  | Yes | Legacy Inventory Status: Cleared
 |  |  |  |  |  |  |  |  |  |  |  |  |  |  |  |  |  |  |  |  |  |  |  |  |  | true | false | NXP SEMICONDUCTORS_RMS1 | BZX84-C4V7,215 |  | Active | Preferred |  |  | Yes | Legacy Inventory Status: Cleared
1 | true | true | false | false | false | 0 | 10022656 | DIODE SCHOTTKY, 3A, 40V | B ECO-R252636 | 1 | Each | Production |  | D11 |  |  |  |  |  | Part | CBRM |  | 1 |  |  | true | false | STMICROELECTRONICS | STPS340U | POWER SCHOTTKY RECTIFIER | Active | Preferred |  | ROHS EXEMPT: 7(A) | Yes - by exemption | Legacy Inventory Status: Cleared
1 | true | true | false | false | false | 0 | 10022697 | RESISTOR,470 OHM, 0.125W,+/-1%, 0805 | C ECO-R252636 | 2 | Each | Production |  | R66,R67 |  |  |  |  |  | Part | CBRM |  | 1 |  |  | true | false | YAGEO_RMS1 | 232273464701L | RESISTOR, METAL GLAZE/THICK FILM, 0.125 W, 1 %, 100 PPM, 470 OHM, SURFACE MOUNT, 0805 | Active | Preferred |  | BRAND: PHYCOMP. ROHS EXEMPTION: 7(C)-1 | Yes - by exemption | Legacy Inventory Status: Cleared
 |  |  |  |  |  |  |  |  |  |  |  |  |  |  |  |  |  |  |  |  |  |  |  |  |  | true | false | VISHAY_RMS1 | CRCW0805470RFKEA | THICK FILM RECTANGULAR CHIP RESISTOR | Active | Preferred |  | ROHS EXEMPTION: 7(C)-1 | Yes - by exemption | Legacy Inventory Status: Cleared
 |  |  |  |  |  |  |  |  |  |  |  |  |  |  |  |  |  |  |  |  |  |  |  |  |  | true | false | YAGEO_RMS1 | 232273464701 | RESISTOR, METAL GLAZE/THICK FILM, 0.125 W, 1 %, 100 PPM, 470 OHM, SURFACE MOUNT, 0805 | Active | Preferred |  | BRAND: PHYCOMP.ROHS EXEMPTION: 7(C)-1 | Yes - by exemption | Legacy Inventory Status: Cleared
 |  |  |  |  |  |  |  |  |  |  |  |  |  |  |  |  |  |  |  |  |  |  |  |  |  | true | false | YAGEO_RMS1 | RC0805FR-07470RL | RESISTOR, METAL GLAZE/THICK FILM, 0.125 W, 1 %, 100 PPM, 470 OHM, SURFACE MOUNT, 0805 | Active | Preferred |  | ROHS EXEMPTION: 7(C)-1 | Yes - by exemption | Legacy Inventory Status: Cleared
 |  |  |  |  |  |  |  |  |  |  |  |  |  |  |  |  |  |  |  |  |  |  |  |  |  | true | false | ASJ | CR21-4700FL | THICK FILM CHIP RESISTOR | Active | Preferred |  | ROHS EXEMPTION: 7(C)-1 | Yes - by exemption | Legacy Inventory Status: Cleared
1 | true | true | false | false | false | 0 | 10022700 | RESISTOR,1.5K OHM,0.063W,+/-1%,0603 | C ECO-R252636 | 1 | Each | Production |  | R18 |  |  |  |  |  | Part | CBRM |  | 1 |  |  | true | false | YAGEO_RMS1 | 232270461502 | RESISTOR, METAL GLAZE/THICK FILM, 0.1 W, 1 %, 100 PPM, 1500 OHM, SURFACE MOUNT, 0603 | Active | Preferred |  | BRAND: PHYCOMP.ROHS EXEMPT: 7(C)-1 | Yes - by exemption | Legacy Inventory Status: Cleared
 |  |  |  |  |  |  |  |  |  |  |  |  |  |  |  |  |  |  |  |  |  |  |  |  |  | true | false | YAGEO_RMS1 | 232270461502L | RESISTOR, METAL GLAZE/THICK FILM, 0.1 W, 1 %, 100 PPM, 1500 OHM, SURFACE MOUNT, 0603 | Active | Preferred |  | BRAND: PHYCOMP.ROHS EXEMPT: 7(C)-1 | Yes - by exemption | Legacy Inventory Status: Cleared
 |  |  |  |  |  |  |  |  |  |  |  |  |  |  |  |  |  |  |  |  |  |  |  |  |  | true | false | KOA SPEER | RK73H1JTTD1501F | THICK FILM CHIP RESISTOR | Active | Preferred |  | ROHS EXEMPT : 5(A) | Yes - by exemption | Legacy Inventory Status: Cleared
 |  |  |  |  |  |  |  |  |  |  |  |  |  |  |  |  |  |  |  |  |  |  |  |  |  | true | false | YAGEO_RMS1 | RC0603FR-071K5L | RESISTOR, METAL GLAZE/THICK FILM, 0.1 W, 1 %, 100 PPM, 1500 OHM, SURFACE MOUNT, 0603 | Active | Preferred |  | ROHS EXEMPT: 7(C)-1 | Yes - by exemption | Legacy Inventory Status: Cleared
1 | true | true | false | false | false | 0 | 10022703 | FUSE, 500MA | B ECO-R252636 | 1 | Each | Production |  | FU2 |  |  |  |  |  | Part | CBRM |  | 1 |  |  | true | false | LITTELFUSE_RMS1 | 0154.500DRT | VERY FAST ACTING FUSE | Active | Preferred |  | ROHS EXEMPT 7(A) | Yes - by exemption | Legacy Inventory Status: Cleared
1 | true | true | false | false | false | 0 | 10022705 | IC,16 BIT D TYPE 3STATE OP, LATCHES,SSOP | C ECO-R252636 | 1 | Each | Production |  | IC14 |  |  |  |  |  | Part | CBRM |  | 1 |  |  | true | false | TEXAS INSTRUMENTS_RMS1 | 74ACT16373DLR |  | Active | Preferred |  | ROHS EXEMPT: 15 | Yes - by exemption | Legacy Inventory Status: Cleared
 |  |  |  |  |  |  |  |  |  |  |  |  |  |  |  |  |  |  |  |  |  |  |  |  |  | true | false | TEXAS INSTRUMENTS_RMS1 | 74ACT16373DL | 16BIT D TYPE TRANSPARENT LATCHES | Active | Preferred |  | ROHS EXEMPT: 15 | Yes - by exemption | Legacy Inventory Status: Cleared
1 | true | true | false | false | false | 0 | 10022706 | IC AIR FLOW SENSOR,(0-1 LITRE) | A ECO-R252636 | 2 | Each | Production |  | IC15,IC17 |  |  |  |  |  | Part | CBRM |  | 1 |  |  | true | false | HONEYWELL_RMS1 | AWM3300V | AIRFLOW SENSOR | Active | Preferred |  |  | Yes | Legacy Inventory Status: Cleared
 |  |  |  |  |  |  |  |  |  |  |  |  |  |  |  |  |  |  |  |  |  |  |  |  |  | true | false | HONEYWELL_RMS1 | FBAL001DU | AIR FLOW SENSOR | Active | Preferred |  | CUSTOMISED | Yes | Legacy Inventory Status: Cleared
1 | true | true | false | false | false | 0 | 10022731 | RESISTOR,3.3K OHM,0.063W,+/-1%,0603 | C ECO-R252636 | 1 | Each | Production |  | R11 |  |  |  |  |  | Part | CBRM |  | 1 |  |  | true | false | YAGEO_RMS1 | RC0603FR-073K3L | RESISTOR, METAL GLAZE/THICK FILM, 0.1 W, 1 %, 100 PPM, 3300 OHM, SURFACE MOUNT, 0603 | Active | Preferred |  | ROHS EXEMPT : 7(C)-1 | Yes - by exemption | Legacy Inventory Status: Cleared
 |  |  |  |  |  |  |  |  |  |  |  |  |  |  |  |  |  |  |  |  |  |  |  |  |  | true | false | YAGEO_RMS1 | 232270463302 | RESISTOR, METAL GLAZE/THICK FILM, 0.1 W, 1 %, 100 PPM, 3300 OHM, SURFACE MOUNT, 0603 | Active | Preferred |  | BRAND: PHYCOMP. ROHS EXEMPT : 7(C)-1 | Yes - by exemption | Legacy Inventory Status: Cleared
 |  |  |  |  |  |  |  |  |  |  |  |  |  |  |  |  |  |  |  |  |  |  |  |  |  | true | false | BOURNS_RMS1 | CR0603-FX-3301ELF | CHIP RESISTOR | Active | Preferred |  | ROHS EXEMPT : 7(C)-1 | Yes - by exemption | Legacy Inventory Status: Cleared
 |  |  |  |  |  |  |  |  |  |  |  |  |  |  |  |  |  |  |  |  |  |  |  |  |  | true | false | YAGEO_RMS1 | 232270463302L | RESISTOR, METAL GLAZE/THICK FILM, 0.1 W, 1 %, 100 PPM, 3300 OHM, SURFACE MOUNT, 0603 | Active | Preferred |  | BRAND: PHYCOMP.ROHS EXEMPT : 7(C)-1 | Yes - by exemption | Legacy Inventory Status: Cleared
1 | true | true | false | false | false | 0 | 10022732 | RESISTOR,100 K OHM, 0.063W +/-5% | C ECO-R252636 | 16 | Each | Production |  | R7,R8,R9,R12,R20,R21,R24,R26,R48,R55,R56,R59,R60,R61,R65,R68 |  |  |  |  |  | Part | CBRM |  | 1 |  |  | true | false | YAGEO_RMS1 | 232270260104L | RESISTOR, METAL GLAZE/THICK FILM, 0.1 W, 5 %, 100 PPM, 100000 OHM, SURFACE MOUNT, 0603 | Active | Preferred |  | BRAND: PHYCOMP.ROHS EXEMPT : 7(C)-1 | Yes - by exemption | Legacy Inventory Status: Cleared
 |  |  |  |  |  |  |  |  |  |  |  |  |  |  |  |  |  |  |  |  |  |  |  |  |  | true | false | YAGEO_RMS1 | 232270260104 | RESISTOR, METAL GLAZE/THICK FILM, 0.1 W, 5 %, 100 PPM, 100000 OHM, SURFACE MOUNT, 0603 | Active | Preferred |  | BRAND: PHYCOMP.ROHS EXEMPT : 7(C)-1 | Yes - by exemption | Legacy Inventory Status: Cleared
 |  |  |  |  |  |  |  |  |  |  |  |  |  |  |  |  |  |  |  |  |  |  |  |  |  | true | false | YAGEO_RMS1 | RC0603JR-07100KL | RESISTOR, METAL GLAZE/THICK FILM, 0.1 W, 5 %, 100 PPM, 100000 OHM, SURFACE MOUNT, 0603 | Active | Preferred |  | ROHS EXEMPT : 7(C)-1 | Yes - by exemption | 2011/65/EU compliant with 7(c)-I exemption and the exemption will expired in 21 July 2021 for medical devices.
 |  |  |  |  |  |  |  |  |  |  |  |  |  |  |  |  |  |  |  |  |  |  |  |  |  | true | false | PANASONIC_RMS1 | ERJ3GEYJ104V | THICK FILM CHIP RESISTOR | Active | Preferred |  | ROHS EXEMPT : 7(C)-1 | Yes | Legacy Inventory Status: Cleared
1 | true | true | false | false | false | 0 | 10022736 | RESISTOR,1M OHM,0.063W,+/-1%,0603 | C ECO-R252636 | 1 | Each | Production |  | R4 |  |  |  |  |  | Part | CBRM |  | 1 |  |  | true | false | YAGEO_RMS1 | 232270461005L | RESISTOR, METAL GLAZE/THICK FILM, 0.1 W, 1 %, 100 PPM, 1000000 OHM, SURFACE MOUNT, 0603 | Active | Preferred |  | BRAND: PHYCOMP.ROHS EXEMPT 7(C)-1 | Yes - by exemption | Legacy Inventory Status: Cleared
 |  |  |  |  |  |  |  |  |  |  |  |  |  |  |  |  |  |  |  |  |  |  |  |  |  | true | false | YAGEO_RMS1 | RC0603FR-071ML | RESISTOR, METAL GLAZE/THICK FILM, 0.1 W, 1 %, 100 PPM, 1000000 OHM, SURFACE MOUNT, 0603 | Active | Preferred |  | ROHS EXEMPT 7(C)-1 | Yes | Legacy Inventory Status: Cleared
 |  |  |  |  |  |  |  |  |  |  |  |  |  |  |  |  |  |  |  |  |  |  |  |  |  | true | false | VISHAY_RMS1 | CRCW06031M00FKEA | THICK FILM RECTANGULAR CHIP RESISTOR | Active | Preferred |  | ROHS EXEMPT 7(C)-1 | Yes | Legacy Inventory Status: Cleared
 |  |  |  |  |  |  |  |  |  |  |  |  |  |  |  |  |  |  |  |  |  |  |  |  |  | true | false | YAGEO_RMS1 | 232270461005 | RESISTOR, METAL GLAZE/THICK FILM, 0.1 W, 1 %, 100 PPM, 1000000 OHM, SURFACE MOUNT, 0603 | Active | Preferred |  | BRAND: PHYCOMP.ROHS EXEMPT 7(C)-1 | Yes - by exemption | Legacy Inventory Status: Cleared
1 | true | true | false | false | false | 0 | 10022879 | OCTAL BUS TRANSCEIVER | C ECO-R252636 | 1 | Each | Production |  | IC40 |  |  |  |  |  | Part | CBRM |  | 1 |  |  | true | false | TEXAS INSTRUMENTS_RMS1 | CD74HCT245M96 |  | Active | Preferred |  | ROHS EXEMPTION : 15 | Yes - by exemption | Legacy Inventory Status: Cleared
 |  |  |  |  |  |  |  |  |  |  |  |  |  |  |  |  |  |  |  |  |  |  |  |  |  | true | false | TEXAS INSTRUMENTS_RMS1 | CD74HCT245M | CMOS LOGIC OCTAL-BUS TRANSCEIVER | Active | Preferred |  | ROHS EXEMPTION : 15 | Yes - by exemption | Legacy Inventory Status: Cleared
1 | true | true | false | false | false | 0 | 10022884 | LITHIUM, 3V, 35MAH | C ECO-R252636 | 1 | Each | Production |  | G1 |  |  |  |  |  | Part | CBRM |  | 1 |  |  | true | false | SONY_RMS1 | CR1220-B1A | COIN CELL BATTERY | Active | Preferred |  | ROHS OUT OF SCOPE.NO ROHS EVIDENCE REQUIRED. | N/A | Legacy Inventory Status: Cleared
 |  |  |  |  |  |  |  |  |  |  |  |  |  |  |  |  |  |  |  |  |  |  |  |  |  | true | false | MAXELL | CR1220 |  | Active | Preferred |  | ROHS OUT OF SCOPE.NO ROHS EVIDENCE REQUIRED. | Yes | Legacy Inventory Status: Cleared
 |  |  |  |  |  |  |  |  |  |  |  |  |  |  |  |  |  |  |  |  |  |  |  |  |  | true | false | VARTA (917650) | CR 1220 | BATTERY | Active | Preferred |  | ROHS OUT OF SCOPE.NO ROHS EVIDENCE REQUIRED. | N/A | Legacy Inventory Status: Cleared
1 | true | true | false | false | false | 0 | 10022892 | REGULATOR 3.3 V 2% 500MA LOW DROPOUT,DPACK | B ECO-R252636 | 1 | Each | Production |  | IC26 |  |  |  |  |  | Part | CBRM |  | 1 |  |  | true | false | ST MICROELECTRONIC | LF33CDT | VERY LOW DROP VOLTAGE REGULATOR | Active | Preferred |  | ROHS EXEMPT : 7A | Yes - by exemption | Legacy Inventory Status: Cleared
 |  |  |  |  |  |  |  |  |  |  |  |  |  |  |  |  |  |  |  |  |  |  |  |  |  | true | false | STMICROELECTRONICS | LF33CDT-TR | VERY LOW DROP VOLTAGE REGULATOR | Active | Preferred |  | ROHS EXEMPT : 7A | Yes - by exemption | Legacy Inventory Status: Cleared
1 | true | true | false | false | false | 0 | 10022895 | REGULATOR, 5.5V TO 36V,3A | C ECO-R252636 | 1 | Each | Production |  | IC29 |  |  |  |  |  | Part | CBRM |  | 1 |  |  | true | false | TEXAS INSTRUMENTS_RMS1 | TPS 5430 DDA | 3A, WIDE INPUT RANGE, CONVERTER | Active | Preferred |  | ROHS EXEMPT 15 | Yes - by exemption | Legacy Inventory Status: Cleared
 |  |  |  |  |  |  |  |  |  |  |  |  |  |  |  |  |  |  |  |  |  |  |  |  |  | true | false | TEXAS INSTRUMENTS_RMS1 | TPS5430DDAR |  | Active | Preferred |  | ROHS EXEMPT 15 | Yes - by exemption | Legacy Inventory Status: Cleared
1 | true | true | false | false | false | 0 | 10022905 | IC,BUS SWITCH,SC70 | B ECO-R252636 | 1 | Each | Production |  | IC44 |  |  |  |  |  | Part | CBRM |  | 1 |  |  | true | false | FAIRCHILD SEMICONDUCTOR_RMS1 | NC7SZ66P5X | BUS SWITCH | Active | Preferred |  |  | Yes | Legacy Inventory Status: Cleared
1 | true | true | false | false | false | 0 | 10022907 | SMD FERRITE 200MA | B ECO-R252636 | 36 | Each | Production |  | L1,L3,L4,L6,L9,L10,L12,L14,L15,L16,L17,L18,L21,L23,L24,L25,L26,L29,L31,L32,L33,L34,L35,L37,L42,L43,L44,L45,L46,L47,L48,L49,L50,L51,L52,L53 |  |  |  |  |  | Part | CBRM |  | 1 |  |  | true | false | WURTH ELEKTRONIK GMBH | 74279266 | MULTILAYER-SMD-FERRITE | Active | Preferred |  | ROHS EXEMPT : 7(C)-1 | Yes | Legacy Inventory Status: Cleared
1 | true | true | false | false | false | 0 | 10022908 | INDUCTOR,33UH +/-10% | B ECO-R252636 | 1 | Each | Production |  | L2 |  |  |  |  |  | Part | CBRM |  | 1 |  |  | true | false | WURTH ELEKTRONIK GMBH | 74456133 | POWER CHOKE | Active | Preferred |  | ROHS EXEMPT: 7(C)-1 | Yes - by exemption | Legacy Inventory Status: Cleared
1 | true | true | false | false | false | 0 | 10022911 | SMD FERRITE, 1A,1206 | B ECO-R252636 | 7 | Each | Production |  | L7,L8,L11,L19,L20,L22,L61 |  |  |  |  |  | Part | CBRM |  | 1 |  |  | true | false | WURTH ELEKTRONIK GMBH | 74279218 | MULTILAYER-SMD-FERRITE | Active | Preferred |  | ROHS EXEMPT: 7(C)-1 | Yes | Legacy Inventory Status: Cleared
1 | true | true | true | false | false | 0 | 10022924 | TEST POINT | B ECO-R252633 | 2 | Each | Production |  | PT1,PT2 |  |  |  |  |  | Part | CBRM |  | 1 |  |  | true | false | NICOMATIC_RMS1 | C12000B | TEST POINT | Active | Preferred |  |  | Yes | Legacy Inventory Status: Cleared
 |  |  |  |  |  |  |  |  |  |  |  |  |  |  |  |  |  |  |  |  |  |  |  |  |  | true | false | KEYSTONE ELECTRONICS CORP | 5015 | PC TEST POINT MINIATURE SMT | Active | Preferred |  |  | Yes | Legacy Inventory Status: Cleared
1 | true | true | false | false | false | 0 | 10022933 | RSPTRANSISTOR MOSFET, P CHANNEL, 30V,0.6A | B ECO-R252636 | 1 | Each | Production |  | T17 |  |  |  |  |  | Part | CBRM |  | 1 |  |  | true | false | INTERNATIONAL RECTIFIER_RMS1 | IRLML5103TRPBF | POWER MOSFET | Active | Preferred |  | TAPE & REEL. ROHS EXEMPT: 7 (A) | Yes - by exemption | Legacy Inventory Status: Cleared
1 | true | true | false | false | false | 0 | 10022956 | TRANSISTOR, MOSFET, N-CHANNEL, 60V, 0.5A.SOT23 | B ECO-R252636 | 1 | Each | Production |  | T20 |  |  |  |  |  | Part | CBRM |  | 1 |  |  | true | false | FAIRCHILD SEMICONDUCTOR_RMS1 | MMBF170 | MOSFET N-CH 60V 500MA SOT-23 | Active | Preferred |  |  | Yes | Legacy Inventory Status: Cleared
 |  |  |  |  |  |  |  |  |  |  |  |  |  |  |  |  |  |  |  |  |  |  |  |  |  | true | false | DIODES INC_RMS1 | MMBF170-7-F | N-CHANNEL MOSFET | Active | Preferred |  | ROHS EXEMPT: 7(A) | Yes - by exemption | Legacy Inventory Status: Cleared
1 | false | true | false | false | false | 0 | 10022959 | CAPACITOR TANTALUM, 1UF,35V, +/-10% | D EC074855 | 5 | Each | Production |  | C7,C8,C31,C32,C34 |  |  |  |  |  | Part | CBRM |  | 1 |  |  | true | false | KEMET | T491A105M035AT | Cap, Tantalum, Polarized, 35V, 20% +/-Tol, 1uF, Surface Mount, 1206 (Case A), EIA Metric 3216 | Active | Alternate |  |  | Yes | Cleared
 |  |  |  |  |  |  |  |  |  |  |  |  |  |  |  |  |  |  |  |  |  |  |  |  |  | true | false | KEMET | T495A105K035ATE3K0 | Cap, Tantalum, Polarized, 35V, 10% +/-Tol, 1uF, Surface Mount, 1206 (Case A), EIA Metric 3216 | Active | Preferred |  |  | Yes | Cleared
1 | true | true | false | false | false | 0 | 10022960 | IC, 2 INPUT OR-GATE,SOT353 | C ECO-R252636 | 3 | Each | Production |  | IC5,IC42,IC43 |  |  |  |  |  | Part | CBRM |  | 1 |  |  | true | false | NXP SEMICONDUCTORS_RMS1 | 74HCT1G32GW | 2 INPUT OR-GATE | Active | Preferred |  |  | Yes | Legacy Inventory Status: Cleared
 |  |  |  |  |  |  |  |  |  |  |  |  |  |  |  |  |  |  |  |  |  |  |  |  |  | true | false | NXP SEMICONDUCTORS_RMS1 | 74HCT1G32GW,125 |  | Active | Preferred |  |  | Yes | Legacy Inventory Status: Cleared
1 | false | true | false | false | false | 0 | 10022961 | IC, FLASH MEMORY,TSOP48 | B ECO-R261408 | 1 | Each | Production |  | IC7 |  |  |  |  |  | Part | CBRM |  | 1 |  |  | true | false | Macronix | MX29F400CBTI-70GTR | FLASH MEMORY 5V | Active | Preferred |  |  | Yes | CLEARED
 |  |  |  |  |  |  |  |  |  |  |  |  |  |  |  |  |  |  |  |  |  |  |  |  |  | true | false | Macronix | MX29F400CBTI-70G | FLASH MEMORY 5V | Active | Preferred |  |  | Yes | CLEARED
 |  |  |  |  |  |  |  |  |  |  |  |  |  |  |  |  |  |  |  |  |  |  |  |  |  | true | false | STMICROELECTRONICS | M29F400BB-70N6F | FLASH MEMORY | Active | Preferred |  |  | Yes | Legacy Inventory Status: Cleared
 |  |  |  |  |  |  |  |  |  |  |  |  |  |  |  |  |  |  |  |  |  |  |  |  |  | true | false | SPANSION LLC | AM29F400BB-70EF | CMOS 5 VOLT BOOT SECTOR FLASH MEMORY | Active | Preferred |  |  | Yes | Legacy Inventory Status: Cleared
 |  |  |  |  |  |  |  |  |  |  |  |  |  |  |  |  |  |  |  |  |  |  |  |  |  | true | false | STMICROELECTRONICS | M29F400BB-70N6E | FLASH MEMORY | Active | Preferred |  |  | Yes | Legacy Inventory Status: Cleared
 |  |  |  |  |  |  |  |  |  |  |  |  |  |  |  |  |  |  |  |  |  |  |  |  |  | true | false | SPANSION LLC | AM29F400BB-70EK | CMOS 5V BOOT SECTOR FLASH MEMORY | Active | Preferred |  |  | Yes | Legacy Inventory Status: Cleared
1 | false | true | false | false | false | 0 | 10022962 | CAPACITOR TANALUM, 47UF, 10V +/-10% | C EC074855 | 2 | Each | Production |  | C19,C75 |  |  |  |  |  | Part | CBRM |  | 1 |  |  | true | false | KEMET | T495B476K010ATE500 | Cap, Tantalum, Polarized, 10V, 10% +/-Tol, 47uF, Surface Mount, Case B, EIA Metric 3528 | Active | Preferred |  |  | Yes | Cleared
1 | true | true | false | false | false | 0 | 10022963 | CAPACITOR ELECTROLYTIC, 100UF, 35V +/-20% | B ECO-R252636 | 1 | Each | Production |  | C21 |  |  |  |  |  | Part | CBRM |  | 1 |  |  | true | false | MULTICOMP (920630) | MCRH35V107M8X11 | ELECTROLYTIC CAPACITOR | Active | Preferred |  |  | Yes | Legacy Inventory Status: Cleared
 |  |  |  |  |  |  |  |  |  |  |  |  |  |  |  |  |  |  |  |  |  |  |  |  |  | true | false | LELON | RXW101M1V-SA-0811 | ALUMINIUM ELECTROLYTIC CAPACITOR | Active | Preferred |  |  | Yes | Legacy Inventory Status: Cleared
1 | true | true | false | false | false | 0 | 10022964 | BUFFER WITH OPEN DRAIN OUTPUT,SOT23 | C ECO-R252636 | 3 | Each | Production |  | IC8,IC9,IC20 |  |  |  |  |  | Part | CBRM |  | 1 |  |  | true | false | TEXAS INSTRUMENTS_RMS1 | SN74LVC1G07DBVT | SINGLE BUFFER DRIVER | Active | Preferred |  | ROHS EXEMPT-15 | Yes - by exemption | Legacy Inventory Status: Cleared
 |  |  |  |  |  |  |  |  |  |  |  |  |  |  |  |  |  |  |  |  |  |  |  |  |  | true | false | NXP SEMICONDUCTORS_RMS1 | 74LVC1G07GV,125 |  | Active | Preferred |  |  | Yes | Legacy Inventory Status: Cleared
 |  |  |  |  |  |  |  |  |  |  |  |  |  |  |  |  |  |  |  |  |  |  |  |  |  | true | false | NXP SEMICONDUCTORS_RMS1 | 74LVC1G07GV | BUFFER WITH OPEN DRAIN OUTPUT | Active | Preferred |  |  | Yes | Legacy Inventory Status: Cleared
1 | true | true | false | false | false | 0 | 10022965 | IC,REALTIMECLOCK, TSSOP | C ECO-R252636 | 1 | Each | Production |  | IC10 |  |  |  |  |  | Part | CBRM |  | 1 |  |  | true | false | MAXIM_RMS1 | DS1305E+ |  | Active | Alternate |  |  | Yes | Legacy Inventory Status: Cleared
 |  |  |  |  |  |  |  |  |  |  |  |  |  |  |  |  |  |  |  |  |  |  |  |  |  | true | false | MAXIM_RMS1 | DS1305E+T&R |  | Active | Preferred |  |  | Yes | Legacy Inventory Status: Cleared
1 | true | true | false | false | false | 0 | 10022966 | CAPACITOR CERAMIC, 220PF, 50V,+/-5%, NPO,0402 | C ECO-R252636 | 1 | Each | Production |  | C47 |  |  |  |  |  | Part | CBRM |  | 1 |  |  | true | false | YAGEO_RMS1 | 223886915221 | CAPACITOR, CERAMIC, MULTILAYER, 50 V, C0G, 0.00022 UF, SURFACE MOUNT, 0402 | Active | Preferred |  | BRAND: PHYCOMP | Yes | Legacy Inventory Status: Cleared
 |  |  |  |  |  |  |  |  |  |  |  |  |  |  |  |  |  |  |  |  |  |  |  |  |  | true | false | MURATA MANUFACTURING CO., LTD. | GRM1555C1H221JA01D | MONOLITHIC CERAMIC CAPACITOR | Active | Preferred |  |  | Yes | Legacy Inventory Status: Cleared
 |  |  |  |  |  |  |  |  |  |  |  |  |  |  |  |  |  |  |  |  |  |  |  |  |  | true | false | YAGEO_RMS1 | CC0402JRNPO9BN221 | CAPACITOR, CERAMIC, MULTILAYER, 50 V, C0G, 0.00022 UF, SURFACE MOUNT, 0402 | Active | Preferred |  |  | Yes | Legacy Inventory Status: Cleared
1 | true | true | false | false | false | 0 | 10022967 | CAPACITOR CERAMIC,1UF,16V,+/-10%, 0805 | D ECO-R252636 | 3 | Each | Production |  | C54,C112,C114 |  |  |  |  |  | Part | CBRM |  | 1 |  |  | true | false | KEMET_RMS1 | C0805C105Z4VACTU | CERAMIC CHIP CAPACITOR | Active | Preferred |  |  | Yes | Legacy Inventory Status: Cleared
 |  |  |  |  |  |  |  |  |  |  |  |  |  |  |  |  |  |  |  |  |  |  |  |  |  | true | false | KEMET_RMS1 | C0805C105Z4VAC | CERAMIC SURFACE MOUNT | Active | Preferred |  |  | Yes | Legacy Inventory Status: Cleared
 |  |  |  |  |  |  |  |  |  |  |  |  |  |  |  |  |  |  |  |  |  |  |  |  |  | true | false | YAGEO_RMS1 | CC0805ZRY5V7BB105 | CAPACITOR, CERAMIC, MULTILAYER, 16 V, Y5V, 1 UF, SURFACE MOUNT, 0805 | Active | Preferred |  |  | Yes | Legacy Inventory Status: Cleared
 |  |  |  |  |  |  |  |  |  |  |  |  |  |  |  |  |  |  |  |  |  |  |  |  |  | true | false | MURATA_RMS1 | GRM216B31C105KA87D | MONOLITHIC CERAMIC CAPACITOR | Active | Preferred |  |  | Yes | Legacy Inventory Status: Cleared
1 | true | true | false | false | false | 0 | 10022968 | CAP CERAMIC,220NF,25V,X7R,+/-10%,0805 | B ECO-R252636 | 4 | Each | Production |  | C59,C65,C94,C102 |  |  |  |  |  | Part | CBRM |  | 1 |  |  | true | false | AVX_RMS1 | 08053C224KAZ2A | SMT MULTILAYER CAPACITOR | Active | Preferred |  |  | Yes | Legacy Inventory Status: Cleared
 |  |  |  |  |  |  |  |  |  |  |  |  |  |  |  |  |  |  |  |  |  |  |  |  |  | true | false | KEMET_RMS1 | C0805C224K3RAC | CERAMIC CHIP CAPACITOR | Active | Preferred |  |  | Yes | Legacy Inventory Status: Cleared
 |  |  |  |  |  |  |  |  |  |  |  |  |  |  |  |  |  |  |  |  |  |  |  |  |  | true | false | AVX_RMS1 | 08053C224KAT2A | X7R DIELECTRIC | Active | Preferred |  |  | Yes | Legacy Inventory Status: Cleared
 |  |  |  |  |  |  |  |  |  |  |  |  |  |  |  |  |  |  |  |  |  |  |  |  |  | true | false | KEMET_RMS1 | C0805C224K3RACTU | CERAMIC CHIP CAPACITOR | Active | Preferred |  |  | Yes | Legacy Inventory Status: Cleared
1 | true | true | false | false | false | 0 | 10022969 | DOUBLE AMPLIFIER RAIL TO RAIL, SO8 | C ECO-R252636 | 1 | Each | Production |  | IC11 |  |  |  |  |  | Part | CBRM |  | 1 |  |  | true | false | ANALOG DEVICES, INC. | OP295GSZ-REEL7 | IC OPAMP GP R-R 85KHZ DUAL 8SOIC | Active | Preferred |  |  | Yes | Legacy Inventory Status: Cleared
 |  |  |  |  |  |  |  |  |  |  |  |  |  |  |  |  |  |  |  |  |  |  |  |  |  | true | false | ANALOG DEVICES, INC. | OP295GSZ | IC OPAMP DUAL RAIL-RAIL 8SOIC | Active | Preferred |  |  | Yes | Legacy Inventory Status: Cleared
1 | true | true | false | false | false | 0 | 10022970 | IC,MICROPROCESSOR SUPERVISOR CIRCUIT,SO8 | C ECO-R252636 | 1 | Each | Production |  | IC12 |  |  |  |  |  | Part | CBRM |  | 1 |  |  | true | false | MAXIM_RMS1 | MAX690ACSA+T |  | Active | Preferred |  |  | Yes | Legacy Inventory Status: Cleared
 |  |  |  |  |  |  |  |  |  |  |  |  |  |  |  |  |  |  |  |  |  |  |  |  |  | true | false | MAXIM_RMS1 | MAX690ACSA+ | MICROPROCESSOR SUPERVISORY CIRCUIT | Active | Alternate |  |  | Yes | Legacy Inventory Status: Cleared
1 | true | true | false | false | false | 0 | 10022971 | CAPACITOR CERAMIC, 1NF,50V,+/-10%, 0402 | C ECO-R252636 | 1 | Each | Production |  | C84 |  |  |  |  |  | Part | CBRM |  | 1 |  |  | true | false | YAGEO_RMS1 | CC0402KRX7R9BB102* | CAPACITOR, CERAMIC, MULTILAYER, 50 V, X7R, 0.001 UF, SURFACE MOUNT, 0402 | Active | Preferred |  |  | Yes | Legacy Inventory Status: Cleared
 |  |  |  |  |  |  |  |  |  |  |  |  |  |  |  |  |  |  |  |  |  |  |  |  |  | true | false | YAGEO_RMS1 | 223858715623 | CAPACITOR, CERAMIC, MULTILAYER, 50 V, X7R, 0.001 UF, SURFACE MOUNT, 0402 | Active | Preferred |  | BRAND: PHYCOMP | Yes | Legacy Inventory Status: Cleared
 |  |  |  |  |  |  |  |  |  |  |  |  |  |  |  |  |  |  |  |  |  |  |  |  |  | true | false | KEMET_RMS1 | C0402C102K5RACTU | CAP, CER, 0.001UF, 50V, 10%, X7R, 0402 | Active | Preferred |  |  | Yes | Legacy Inventory Status: Cleared
 |  |  |  |  |  |  |  |  |  |  |  |  |  |  |  |  |  |  |  |  |  |  |  |  |  | true | false | YAGEO_RMS1 | 223858715523 | CAPACITOR, CERAMIC, MULTILAYER, 50 V, X7R, 0.001 UF, SURFACE MOUNT, 0402 | Active | Preferred |  | BRAND: PHYCOMP | Yes | Legacy Inventory Status: Cleared
1 | false | true | false | false | false | 0 | 10022973 | CAPACITOR TANTALUM, 22UF, 10V,+/-10% | C EC074855 | 2 | Each | Production |  | C89,C92 |  |  |  |  |  | Part | CBRM |  | 1 |  |  | true | false | KEMET | T495A226K010ATE1K2 | Cap, Tantalum, Polarized, 10V, 10% +/-Tol, 22uF, Surface Mount, Case A, EIA Metric 3216 | Active | Preferred |  |  | Yes | Cleared
1 | true | true | false | false | false | 0 | 10022974 | RESET CIRCUIT, SUPERVISOR VOLTAGE 5V,SOT23 | B ECO-R252636 | 2 | Each | Production |  | IC24,IC25 |  |  |  |  |  | Part | CBRM |  | 1 |  |  | true | false | STMICROELECTRONICS | STM809LWX6F | RESET CIRCUIT | Active | Preferred |  |  | Yes | Legacy Inventory Status: Cleared
1 | true | true | false | false | false | 0 | 10022975 | CAPACITOR CERAMIC, 150PF,50V,+/-5,NPO, 0402 | C ECO-R252636 | 6 | Each | Production |  | C99,C115,C121,C122,C123,C124 |  |  |  |  |  | Part | CBRM |  | 1 |  |  | true | false | YAGEO_RMS1 | CC0402JRNPO9BN151 | CAP CER 150PF 50V C0G/NPO 0402 | Active | Preferred |  |  | Yes | Cleared
 |  |  |  |  |  |  |  |  |  |  |  |  |  |  |  |  |  |  |  |  |  |  |  |  |  | true | false | KEMET_RMS1 | C0402C151J5GACTU | CERAMIC CHIP CAPACITOR | Active | Preferred |  |  | Yes | Legacy Inventory Status: Cleared
 |  |  |  |  |  |  |  |  |  |  |  |  |  |  |  |  |  |  |  |  |  |  |  |  |  | true | false | YAGEO_RMS1 | 223886915151 | CAPACITOR, CERAMIC, MULTILAYER, 50 V, C0G, 0.00015 UF, SURFACE MOUNT, 0402 | Active | Preferred |  | BRAND: PHYCOMP | Yes | Legacy Inventory Status: Cleared
1 | true | true | false | false | false | 0 | 10022976 | CAPACITOR CERAMIC,4.7NF,25V,+/-10%,0402 | B ECO-R252636 | 1 | Each | Production |  | C101 |  |  |  |  |  | Part | CBRM |  | 1 |  |  | true | false | KYOCERA_RMS1 | CM05X7R472K25AT | MULTILAYER CERAMIC CAPACITOR | Active | Preferred |  |  | Yes | Legacy Inventory Status: Cleared
 |  |  |  |  |  |  |  |  |  |  |  |  |  |  |  |  |  |  |  |  |  |  |  |  |  | true | false | KEMET_RMS1 | C0402C472K3RACTU | CERAMIC CHIP CAPACITOR | Active | Preferred |  |  | Yes | Legacy Inventory Status: Cleared
 |  |  |  |  |  |  |  |  |  |  |  |  |  |  |  |  |  |  |  |  |  |  |  |  |  | true | false | AVX_RMS1 | 04023C472KAT2A | CERAMIC CAPACITOR X7R | Active | Preferred |  |  | Yes | Legacy Inventory Status: Cleared
1 | false | true | false | false | false | 0 | 10022978 | CAPACITOR TANTALUM,10UF, 50V,+/-10% | D EC074855 | 1 | Each | Production |  | C117 |  |  |  |  |  | Part | CBRM |  | 1 |  |  | true | false | AVX CORPORATION | TAJD106K050RNJ | CAPACITOR TANTALUM,10UF, 50V,+/-10% | Active | Preferred |  |  | Yes | Cleared
1 | true | true | false | false | false | 0 | 10023039 | IC,REFERENCE VOLTAGE 5V FIXED - 10 MA,SO8 | B ECO-R252636 | 1 | Each | Production |  | IC21 |  |  |  |  |  | Part | CBRM |  | 1 |  |  | true | false | LINEAR TECHNOLOGY_RMS1 | LT1236CCS8-5#TRPBF | PRECISION REFERENCE | Active | Preferred |  |  | Yes | Legacy Inventory Status: Cleared
1 | true | true | false | false | false | 0 | 10023040 | IC,REFERENCE VOLTAGE 10V FIXED - 10 MA,SO8 | B ECO-R252636 | 1 | Each | Production |  | IC23 |  |  |  |  |  | Part | CBRM |  | 1 |  |  | true | false | LINEAR TECHNOLOGY_RMS1 | LT1236CCS8-10#TRPBF | PRECISION REFERENCE | Active | Preferred |  |  | Yes | Legacy Inventory Status: Cleared
1 | true | true | false | false | false | 0 | 10023041 | IC, SUPERVISOR VOLTAGE 3.3 V,SOT23 | B ECO-R252636 | 1 | Each | Production |  | IC36 |  |  |  |  |  | Part | CBRM |  | 1 |  |  | true | false | STMICROELECTRONICS | STM809TWX6F | RESET CIRCUIT | Active | Preferred |  |  | Yes | Legacy Inventory Status: Cleared
1 | true | true | false | false | false | 0 | 10023117 | IC, PRESSURE TRANSDUCER,(-10/+100 MBAR) | B ECO-R252636 | 3 | Each | Production |  | IC16,IC18,IC22 |  |  |  |  |  | Part | CBRM |  | 1 |  |  | true | false | SENSYM_RMS1 | ASDX001D44R-SQ04689 | PRESSURE TRANSDUCER | Active | Preferred |  |  | Yes | Legacy Inventory Status: Cleared
 |  |  |  |  |  |  |  |  |  |  |  |  |  |  |  |  |  |  |  |  |  |  |  |  |  | true | false | HONEYWELL_RMS1 | XZ209766-ASDX | IC DIFFERENTIAL PRESSURE SENSOR WITH ANALOGUE OUTPUT -10 TO 100 MBAR | Active | Alternate |  |  | Yes | Legacy Inventory Status: Cleared
1 | true | true | false | false | false | 0 | 10023118 | IC, INVERTER,SOT353 | C ECO-R252636 | 2 | Each | Production |  | IC39,IC41 |  |  |  |  |  | Part | CBRM |  | 1 |  |  | true | false | NXP SEMICONDUCTORS_RMS1 | 74HCT1G04GW,125 |  | Active | Preferred |  |  | Yes | Legacy Inventory Status: Cleared
 |  |  |  |  |  |  |  |  |  |  |  |  |  |  |  |  |  |  |  |  |  |  |  |  |  | true | false | NXP SEMICONDUCTORS_RMS1 | 74HCT1G04GW | INVERTER | Active | Preferred |  |  | Yes | Legacy Inventory Status: Cleared
1 | true | true | false | false | false | 0 | 10023119 | 2 INPUT AND-GATE,SOT353 | C ECO-R252636 | 1 | Each | Production |  | IC38 |  |  |  |  |  | Part | CBRM |  | 1 |  |  | true | false | NXP SEMICONDUCTORS_RMS1 | 74HCT1G08GW,125 |  | Active | Preferred |  |  | Yes | Legacy Inventory Status: Cleared
 |  |  |  |  |  |  |  |  |  |  |  |  |  |  |  |  |  |  |  |  |  |  |  |  |  | true | false | NXP SEMICONDUCTORS_RMS1 | 74HCT1G08GW | 2-INPUT AND-GATE | Active | Preferred |  |  | Yes | Legacy Inventory Status: Cleared
1 | true | true | false | false | false | 0 | 10023158 | EEPROM, SOIC8 | A ECO-R252636 | 1 | Each | Production |  | IC32 |  |  |  |  |  | Part | CBRM |  | 1 |  |  | true | false | MICROCHIP TECHNOLOGY_RMS1 | 25LC320-I/SN | EEPROM | Active | Preferred |  | ROHS COMPLIANT | Yes | Legacy Inventory Status: Cleared
 |  |  |  |  |  |  |  |  |  |  |  |  |  |  |  |  |  |  |  |  |  |  |  |  |  | true | false | MICROCHIP TECHNOLOGY_RMS1 | 25LC320T-E/SN | EEPROM | Active | Preferred |  | ROHS COMPLIANT | Yes | Legacy Inventory Status: Cleared
 |  |  |  |  |  |  |  |  |  |  |  |  |  |  |  |  |  |  |  |  |  |  |  |  |  | true | false | MICROCHIP TECHNOLOGY_RMS1 | 25LC320T-I/SN | EEPROM | Active | Preferred |  | ROHS COMPLIANT | Yes | Legacy Inventory Status: Cleared
 |  |  |  |  |  |  |  |  |  |  |  |  |  |  |  |  |  |  |  |  |  |  |  |  |  | true | false | MICROCHIP TECHNOLOGY_RMS1 | 25LC320-E/SN | EEPROM | Active | Preferred |  | ROHS COMPLIANT | Yes | Legacy Inventory Status: Cleared
1 | true | true | false | false | false | 0 | 10023159 | IC, BAROMETRIC PRESSURE SENSOR | B ECO-R252636 | 1 | Each | Production |  | IC33 |  |  |  |  |  | Part | CBRM |  | 1 |  |  | true | false | HONEYWELL_RMS1 | XZ209330-ASDX | IC ABSOLUTE PRESSURE SENSOR WITH ANALOGUE OUTPUT 600 TO 1100 MBAR | Active | Preferred |  |  | Yes | Legacy Inventory Status: Cleared
 |  |  |  |  |  |  |  |  |  |  |  |  |  |  |  |  |  |  |  |  |  |  |  |  |  | true | false | SENSORTECHNICS | BSDX0611BARO-X | PRESSURE TRANSDUCER | Active | Preferred |  |  | Yes | Legacy Inventory Status: Cleared
1 | true | true | false | false | false | 0 | 10023185 | RESISTANCE, 0 OHM,0603 | C ECO-R252636 | 4 | Each | Production |  | JP1,JP6,R45,R69 |  |  |  |  |  | Part | CBRM |  | 1 |  |  | true | false | YAGEO_RMS1 | RC0603JR-070RL | RES 0.0 OHM 1/10W 0603 SMD | Active | Preferred |  | ROHS EXEMPT: 7(C)-1 | RoHS3 Compliant with exemptions | RoHS3 Compliant with exemptions
 |  |  |  |  |  |  |  |  |  |  |  |  |  |  |  |  |  |  |  |  |  |  |  |  |  | true | false | YAGEO_RMS1 | 232270296001 | JUMPER, METAL GLAZE/THICK FILM, 0.1 W, 0 OHM, SURFACE MOUNT, 0603 | Active | Preferred |  | BRAND: PHYCOMP.ROHS EXEMPT: 7(C)-1 | Yes - by exemption | Legacy Inventory Status: Cleared
 |  |  |  |  |  |  |  |  |  |  |  |  |  |  |  |  |  |  |  |  |  |  |  |  |  | true | false | YAGEO_RMS1 | 232270296001L | JUMPER, METAL GLAZE/THICK FILM, 0.1 W, 0 OHM, SURFACE MOUNT, 0603 | Active | Preferred |  | BRAND: PHYCOMP. ROHS EXEMPT: 7(C)-1 | RoHS3 Compliant with exemptions | RoHS3 Compliant with exemptions
 |  |  |  |  |  |  |  |  |  |  |  |  |  |  |  |  |  |  |  |  |  |  |  |  |  | true | false | ASJ | CR16000ZL | THICK FILM CHIP RESISTOR | Active | Preferred |  | ROHS EXEMPT: 7(C)-1 | Yes - by exemption | Legacy Inventory Status: Cleared
 |  |  |  |  |  |  |  |  |  |  |  |  |  |  |  |  |  |  |  |  |  |  |  |  |  | true | false | KAMAYA (049580) | RMC1/16JPTP | JUMPER | Active | Preferred |  | ROHS EXEMPT: 7(C)-1 | Yes - by exemption | Legacy Inventory Status: Cleared
1 | true | true | false | false | false | 0 | 10023186 | FERRITE, 2.5, 3A | B ECO-R252636 | 1 | Each | Production |  | L30 |  |  |  |  |  | Part | CBRM |  | 1 |  |  | true | false | WURTH ELEKTRONIK GMBH | 7427512 | 5 HOLE SMD FERRITE BEAD | Active | Preferred |  | ROHS EXEMPT: 7(C)-1 | Yes - by exemption | Legacy Inventory Status: Cleared
 |  |  |  |  |  |  |  |  |  |  |  |  |  |  |  |  |  |  |  |  |  |  |  |  |  | true | false | WURTH ELEKTRONIK GMBH | 7427504 | 6 HOLE FERRITE BEAD | Obsolete | Preferred |  | ROHS EXEMPT: 7(C)-1 | Yes - by exemption | Legacy Inventory Status: Cleared
1 | true | true | false | false | false | 0 | 10023187 | RESISTOR 1.5K OHM, 0603, +/-5% | C ECO-R252636 | 2 | Each | Production |  | R2,R10 |  |  |  |  |  | Part | CBRM |  | 1 |  |  | true | false | YAGEO_RMS1 | 232270260152L | RESISTOR, METAL GLAZE/THICK FILM, 0.1 W, 5 %, 100 PPM, 1500 OHM, SURFACE MOUNT, 0603 | Active | Preferred |  | BRAND: PHYCOMP. ROHS EXEMPT: 7(C)-1 | Yes - by exemption | Legacy Inventory Status: Cleared
 |  |  |  |  |  |  |  |  |  |  |  |  |  |  |  |  |  |  |  |  |  |  |  |  |  | true | false | YAGEO_RMS1 | 232270260152 | RESISTOR, METAL GLAZE/THICK FILM, 0.1 W, 5 %, 100 PPM, 1500 OHM, SURFACE MOUNT, 0603 | Active | Preferred |  | BRAND: PHYCOMP. ROHS EXEMPT: 7(C)-1 | Yes - by exemption | Legacy Inventory Status: Cleared
 |  |  |  |  |  |  |  |  |  |  |  |  |  |  |  |  |  |  |  |  |  |  |  |  |  | true | false | YAGEO_RMS1 | RC0603JR-071K5L | RESISTOR, METAL GLAZE/THICK FILM, 0.1 W, 5 %, 100 PPM, 1500 OHM, SURFACE MOUNT, 0603 | Active | Preferred |  | ROHS EXEMPT: 7(C)-1 | Yes - by exemption | Legacy Inventory Status: Cleared
 |  |  |  |  |  |  |  |  |  |  |  |  |  |  |  |  |  |  |  |  |  |  |  |  |  | true | false | KOA SPEER | RK73B1JTTD152J | THICK FILM CHIP RESISTOR | Active | Preferred |  | ROHS EXEMPT: 5A | Yes | Legacy Inventory Status: Cleared
1 | true | true | false | false | false | 0 | 10023188 | RESISTOR, 220 K OHM, 0603,+/-5% | C ECO-R252636 | 1 | Each | Production |  | R3 |  |  |  |  |  | Part | CBRM |  | 1 |  |  | true | false | YAGEO_RMS1 | 232270260224 | RESISTOR, METAL GLAZE/THICK FILM, 0.1 W, 5 %, 100 PPM, 220000 OHM, SURFACE MOUNT, 0603 | Active | Preferred |  | BRAND: PHYCOMP.ROHS EXEMPT : 7(C)-1 | Yes - by exemption | Legacy Inventory Status: Cleared
 |  |  |  |  |  |  |  |  |  |  |  |  |  |  |  |  |  |  |  |  |  |  |  |  |  | true | false | YAGEO_RMS1 | 232270260224L | RESISTOR, METAL GLAZE/THICK FILM, 0.1 W, 5 %, 100 PPM, 220000 OHM, SURFACE MOUNT, 0603 | Active | Preferred |  | BRAND: PHYCOMP.ROHS EXEMPT : 7(C)-1 | Yes - by exemption | Legacy Inventory Status: Cleared
 |  |  |  |  |  |  |  |  |  |  |  |  |  |  |  |  |  |  |  |  |  |  |  |  |  | true | false | KOA SPEER | RK73B1JTTD224J | THICK FILM CHIP RESISTOR | Active | Preferred |  | ROHS EXEMPT : 5(A) | Yes - by exemption | Legacy Inventory Status: Cleared
 |  |  |  |  |  |  |  |  |  |  |  |  |  |  |  |  |  |  |  |  |  |  |  |  |  | true | false | YAGEO_RMS1 | RC0603JR-07220KL | RESISTOR, METAL GLAZE/THICK FILM, 0.1 W, 5 %, 100 PPM, 220000 OHM, SURFACE MOUNT, 0603 | Active | Preferred |  | ROHS EXEMPT : 7(C)-1 | Yes - by exemption | Legacy Inventory Status: Cleared
1 | true | true | false | false | false | 0 | 10023189 | RESISTOR, 100 OHM, 0.063W +/-5% | C ECO-R252636 | 1 | Each | Production |  | R1 |  |  |  |  |  | Part | CBRM |  | 1 |  |  | true | false | YAGEO_RMS1 | RC0603JR-07100RL | RES 100 OHM 1/10W 5% 0603 SMD | Active | Preferred |  | ROHS EXEMPT : 7(C)-1 | Yes - by exemption | 2011/65/EU compliant with 7(c)-I exemption and the exemption will expired in 21 July 2021 for medical devices.
 |  |  |  |  |  |  |  |  |  |  |  |  |  |  |  |  |  |  |  |  |  |  |  |  |  | true | false | YAGEO_RMS1 | 232270260101 | RESISTOR, METAL GLAZE/THICK FILM, 0.1 W, 5 %, 100 PPM, 100 OHM, SURFACE MOUNT, 0603 | Active | Preferred |  | BRAND: PHYCOMP. ROHS EXEMPT : 7(C)-1 | Yes - by exemption | Legacy Inventory Status: Cleared
 |  |  |  |  |  |  |  |  |  |  |  |  |  |  |  |  |  |  |  |  |  |  |  |  |  | true | false | ASJ | CR16-101JL | THICK FILM CHIP RESISTOR | Active | Preferred |  | ROHS EXEMPT : 7(C)-1 | Yes - by exemption | Legacy Inventory Status: Cleared
 |  |  |  |  |  |  |  |  |  |  |  |  |  |  |  |  |  |  |  |  |  |  |  |  |  | true | false | YAGEO_RMS1 | 232270260101L | RESISTOR, METAL GLAZE/THICK FILM, 0.1 W, 5 %, 100 PPM, 100 OHM, SURFACE MOUNT, 0603 | Active | Preferred |  | BRAND: PHYCOMP. ROHS EXEMPT : 7(C)-1 | Yes - by exemption | Legacy Inventory Status: Cleared
1 | true | true | false | false | false | 0 | 10023190 | RESISTOR, 620 OHM, 0.125W,+/-5%,0805 | B ECO-R252636 | 3 | Each | Production |  | R13,R25,R27 |  |  |  |  |  | Part | CBRM |  | 1 |  |  | true | false | MULTICOMP (920630) | MC 0.1W 0805 5% 620R | THICK FILM CHIP RESISTOR | Active | Preferred |  |  | Yes | Legacy Inventory Status: Cleared
1 | true | true | false | false | false | 0 | 10023235 | RESISTOR, 56K OHM, 0603, +/-1% | C ECO-R252636 | 1 | Each | Production |  | R14 |  |  |  |  |  | Part | CBRM |  | 1 |  |  | true | false | YAGEO_RMS1 | 232270465603 | RESISTOR, METAL GLAZE/THICK FILM, 0.1 W, 1 %, 100 PPM, 56000 OHM, SURFACE MOUNT, 0603 | Active | Preferred |  | BRAND: PHYCOMP. ROHS EXEMPT : 7(C)-1 | Yes - by exemption | Legacy Inventory Status: Cleared
 |  |  |  |  |  |  |  |  |  |  |  |  |  |  |  |  |  |  |  |  |  |  |  |  |  | true | false | ASJ | CR16-5602FL | THICK FILM CHIP RESISTOR | Active | Preferred |  | ROHS EXEMPT : 7(C)-1 | Yes - by exemption | Legacy Inventory Status: Cleared
 |  |  |  |  |  |  |  |  |  |  |  |  |  |  |  |  |  |  |  |  |  |  |  |  |  | true | false | YAGEO_RMS1 | 232270465603L | RESISTOR, METAL GLAZE/THICK FILM, 0.1 W, 1 %, 100 PPM, 56000 OHM, SURFACE MOUNT, 0603 | Active | Preferred |  | BRAND: PHYCOMP. ROHS EXEMPT : 7(C)-1 | Yes - by exemption | Legacy Inventory Status: Cleared
 |  |  |  |  |  |  |  |  |  |  |  |  |  |  |  |  |  |  |  |  |  |  |  |  |  | true | false | YAGEO_RMS1 | RC0603FR-0756KL | RESISTOR, METAL GLAZE/THICK FILM, 0.1 W, 1 %, 100 PPM, 56000 OHM, SURFACE MOUNT, 0603 | Active | Preferred |  | ROHS EXEMPT : 7(C)-1 | Yes - by exemption | Legacy Inventory Status: Cleared
1 | true | true | false | false | false | 0 | 10023237 | RESISTOR, 150 OHM, 0805, +/-5% | C ECO-R252636 | 1 | Each | Production |  | R16 |  |  |  |  |  | Part | CBRM |  | 1 |  |  | true | false | YAGEO_RMS1 | 232273061151 | RESISTOR, METAL GLAZE/THICK FILM, 0.125 W, 5 %, 100 PPM, 150 OHM, SURFACE MOUNT, 0805 | Active | Preferred |  | BRAND: PHYCOMP. ROHS EXEMPT : 7(C)-1 | Yes - by exemption | Legacy Inventory Status: Cleared
 |  |  |  |  |  |  |  |  |  |  |  |  |  |  |  |  |  |  |  |  |  |  |  |  |  | true | false | YAGEO_RMS1 | 232273061151L | RESISTOR, METAL GLAZE/THICK FILM, 0.125 W, 5 %, 100 PPM, 150 OHM, SURFACE MOUNT, 0805 | Active | Preferred |  | BRAND: PHYCOMP. ROHS EXEMPT : 7(C)-1 | Yes - by exemption | Legacy Inventory Status: Cleared
 |  |  |  |  |  |  |  |  |  |  |  |  |  |  |  |  |  |  |  |  |  |  |  |  |  | true | false | ASJ | CR21-151JL | THICK FILM CHIP RESISTOR | Active | Preferred |  | ROHS EXEMPT : 7(C)-1 | Yes - by exemption | Legacy Inventory Status: Cleared
 |  |  |  |  |  |  |  |  |  |  |  |  |  |  |  |  |  |  |  |  |  |  |  |  |  | true | false | YAGEO_RMS1 | RC0805JR-07150RL | RESISTOR, METAL GLAZE/THICK FILM, 0.125 W, 5 %, 100 PPM, 150 OHM, SURFACE MOUNT, 0805 | Active | Preferred |  | ROHS EXEMPT : 7(C)-1 | Yes - by exemption | Legacy Inventory Status: Cleared
1 | true | true | false | false | false | 0 | 10023238 | RESISTOR, 15K OHM, 0603, +/-1% | D ECO-R252636 | 2 | Each | Production |  | R17,R40 |  |  |  |  |  | Part | CBRM |  | 1 |  |  | true | false | ASJ | CR16153FL |  | Active | Preferred |  | ROHS EXEMPT : 7(C)1 | Yes - by exemption | Legacy Inventory Status: Cleared
 |  |  |  |  |  |  |  |  |  |  |  |  |  |  |  |  |  |  |  |  |  |  |  |  |  | true | false | VISHAY_RMS1 | CRCW060315K0FKEA | THICK FILM RECTANGULAR CHIP RESISTOR | Active | Preferred |  | ROHS EXEMPT : 7(C)1 | Yes | Legacy Inventory Status: Cleared
 |  |  |  |  |  |  |  |  |  |  |  |  |  |  |  |  |  |  |  |  |  |  |  |  |  | true | false | YAGEO_RMS1 | 232270461503L | RESISTOR, METAL GLAZE/THICK FILM, 0.1 W, 1 %, 100 PPM, 15000 OHM, SURFACE MOUNT, 0603 | Active | Preferred |  | BRAND: PHYCOMP. ROHS EXEMPT : 7(C)1 | Yes - by exemption | Legacy Inventory Status: Cleared
 |  |  |  |  |  |  |  |  |  |  |  |  |  |  |  |  |  |  |  |  |  |  |  |  |  | true | false | YAGEO_RMS1 | RC0603FR-0715KL | RESISTOR, METAL GLAZE/THICK FILM, 0.1 W, 1 %, 100 PPM, 15000 OHM, SURFACE MOUNT, 0603 | Active | Preferred |  | ROHS EXEMPT : 7(C)1 | Yes - by exemption | Legacy Inventory Status: Cleared
 |  |  |  |  |  |  |  |  |  |  |  |  |  |  |  |  |  |  |  |  |  |  |  |  |  | true | false | YAGEO_RMS1 | 232270461503 | RESISTOR, METAL GLAZE/THICK FILM, 0.1 W, 1 %, 100 PPM, 15000 OHM, SURFACE MOUNT, 0603 | Active | Preferred |  | BRAND: PHYCOMP. ROHS EXEMPT : 7(C)1 | Yes - by exemption | Legacy Inventory Status: Cleared
1 | true | true | false | false | false | 0 | 10023239 | RESISTOR, 75K OHM, 0603, +/-1% | B ECO-R252636 | 2 | Each | Production |  | R19,R36 |  |  |  |  |  | Part | CBRM |  | 1 |  |  | true | false | MULTICOMP (920630) | MC 0.063W 0603 1% 75K | THICK FILM CHIP RESISTOR | Active | Preferred |  |  | Yes | Legacy Inventory Status: Cleared
1 | true | true | false | false | false | 0 | 10023240 | RESISTOR, 180 OHM, 0805, +/-5% | C ECO-R252636 | 5 | Each | Production |  | R22,R23,R31,R35,R44 |  |  |  |  |  | Part | CBRM |  | 1 |  |  | true | false | YAGEO_RMS1 | 232273061181 | RESISTOR, METAL GLAZE/THICK FILM, 0.125 W, 5 %, 100 PPM, 180 OHM, SURFACE MOUNT, 0805 | Active | Preferred |  | BRAND: PHYCOMP. ROHS EXEMPT: 7(C)-1 | Yes - by exemption | Legacy Inventory Status: Cleared
 |  |  |  |  |  |  |  |  |  |  |  |  |  |  |  |  |  |  |  |  |  |  |  |  |  | true | false | KOA SPEER | RK73B2ATTD181J | THICK FILM CHIP RESISTOR | Active | Preferred |  | ROHS EXEMPT: 5(A) | Yes - by exemption | Legacy Inventory Status: Cleared
 |  |  |  |  |  |  |  |  |  |  |  |  |  |  |  |  |  |  |  |  |  |  |  |  |  | true | false | YAGEO_RMS1 | 232273061181L | RESISTOR, METAL GLAZE/THICK FILM, 0.125 W, 5 %, 100 PPM, 180 OHM, SURFACE MOUNT, 0805 | Active | Preferred |  | BRAND: PHYCOMP. ROHS EXEMPT: 7(C)-1 | Yes - by exemption | Legacy Inventory Status: Cleared
 |  |  |  |  |  |  |  |  |  |  |  |  |  |  |  |  |  |  |  |  |  |  |  |  |  | true | false | YAGEO_RMS1 | RC0805JR-07180RL | RESISTOR, METAL GLAZE/THICK FILM, 0.125 W, 5 %, 100 PPM, 180 OHM, SURFACE MOUNT, 0805 | Active | Preferred |  | ROHS EXEMPT: 7(C)-1 | Yes - by exemption | Legacy Inventory Status: Cleared
1 | true | true | false | false | false | 0 | 10023242 | RESISTOR 10 OHM, 0.125W, +/-5%,0805 | C ECO-R252636 | 1 | Each | Production |  | R52 |  |  |  |  |  | Part | CBRM |  | 1 |  |  | true | false | YAGEO_RMS1 | RC0805JR-0710RL | RESISTOR, METAL GLAZE/THICK FILM, 0.125 W, 5 %, 200 PPM, 10 OHM, SURFACE MOUNT, 0805 | Active | Preferred |  | ROHS EXEMPT: 7(C)-1 | Yes - by exemption | Legacy Inventory Status: Cleared
 |  |  |  |  |  |  |  |  |  |  |  |  |  |  |  |  |  |  |  |  |  |  |  |  |  | true | false | KOA SPEER | RK73B2ATTD100J | THICK FILM CHIP RESISTOR | Active | Preferred |  | ROHS EXEMPT: 5 (A) | Yes | Legacy Inventory Status: Cleared
 |  |  |  |  |  |  |  |  |  |  |  |  |  |  |  |  |  |  |  |  |  |  |  |  |  | true | false | YAGEO_RMS1 | 232273061109L | RESISTOR, METAL GLAZE/THICK FILM, 0.125 W, 5 %, 200 PPM, 10 OHM, SURFACE MOUNT, 0805 | Active | Preferred |  | BRAND: PHYCOMP. ROHS EXEMPT: 7(C)-1 | Yes - by exemption | Legacy Inventory Status: Cleared
 |  |  |  |  |  |  |  |  |  |  |  |  |  |  |  |  |  |  |  |  |  |  |  |  |  | true | false | YAGEO_RMS1 | 232273061109 | RESISTOR, METAL GLAZE/THICK FILM, 0.125 W, 5 %, 200 PPM, 10 OHM, SURFACE MOUNT, 0805 | Active | Preferred |  | BRAND: PHYCOMP. ROHS EXEMPT: 7(C)-1 | Yes - by exemption | Legacy Inventory Status: Cleared
1 | true | true | false | false | false | 0 | 10023243 | RSP TRANSISTOR, BIPOLAR, PNP, 100V, 5A, SOT223 | B ECO-R252636 | 3 | Each | Production |  | T10,T11,T12 |  |  |  |  |  | Part | CBRM |  | 1 |  |  | true | false | ZETEX | FZT953 | 60 TO 100V PNP TRANSISTOR | Active | Preferred |  | ROHS EXEMPT: 7(A) | Yes - by exemption | Legacy Inventory Status: Cleared
 |  |  |  |  |  |  |  |  |  |  |  |  |  |  |  |  |  |  |  |  |  |  |  |  |  | true | false | ZETEX | FZT953TA | TRANSISTOR | Active | Preferred |  | ROHS EXEMPT: 7(A) | Yes - by exemption | Legacy Inventory Status: Cleared
1 | true | true | false | false | false | 0 | 10023244 | BUZZER, 12V, 30MA, 85DB | B ECO-R252636 | 1 | Each | Production |  | BUZ1 |  |  |  |  |  | Part | CBRM |  | 1 |  |  | true | false | STAR MICRONICS INC. | HMB-12 | MAGNETIC BUZZER | Active | Preferred |  |  | Yes | Legacy Inventory Status: Cleared
1 | true | true | false | false | false | 0 | 10023250 | CRYSTAL QUARTZ 32.768KHZ | C ECO-R252636 | 1 | Each | Production |  | Q5 |  |  |  |  |  | Part | CBRM |  | 1 |  |  | true | false | IQD | LFXTAL003000REEL | CRYSTAL QUARTZ 32.768KHZ | Active | Preferred |  |  | Yes | Legacy Inventory Status: Cleared
1 | true | true | false | false | false | 0 | 10023251 | MEMORY NAND FLASH, 1G, 2.7 TO 3.6V, BUS X 8,TSOP | E ECO-R252636 | 1 | Each | Production |  | IC13 |  |  |  |  |  | Part | CBRM |  | 1 |  |  | true | false | SAMSUNG_RMS1 | K9F1G08U0C-PIB0T |  | Active | Preferred |  | ROHS COMPLIANT | Yes | Legacy Inventory Status: Cleared
 |  |  |  |  |  |  |  |  |  |  |  |  |  |  |  |  |  |  |  |  |  |  |  |  |  | true | false | SAMSUNG_RMS1 | K9F1G08U0C-PCB0T00 |  | Active | Preferred |  | ROHS COMPLIANT | Yes | Legacy Inventory Status: Cleared
 |  |  |  |  |  |  |  |  |  |  |  |  |  |  |  |  |  |  |  |  |  |  |  |  |  | true | false | SAMSUNG_RMS1 | K9F1G08U0C-PCB0T |  | Active | Preferred |  | ROHS COMPLIANT | Yes | Legacy Inventory Status: Cleared
 |  |  |  |  |  |  |  |  |  |  |  |  |  |  |  |  |  |  |  |  |  |  |  |  |  | true | false | NUMONYX_RMS1 | NAND01GW3B2BN6F |  | Active | Alternate |  | ROHS COMPLIANT | Yes | Legacy Inventory Status: Cleared
1 | true | true | false | false | false | 0 | 10023252 | RELAY,LOW VOLTAGE 1A COIL 5VDC | D ECO-R252636 | 1 | Each | Production |  | RL1 |  |  |  |  |  | Part | CBRM |  | 1 |  |  | true | false | OMRON ELECTRONICS INC | G6K-2G-TR 5 VDC |  | Active | Preferred |  |  | Yes | Legacy Inventory Status: Cleared
 |  |  |  |  |  |  |  |  |  |  |  |  |  |  |  |  |  |  |  |  |  |  |  |  |  | true | false | OMRON ELECTRONICS INC | G6K-2G 5 VDC |  | Active | Alternate |  |  | Yes | Legacy Inventory Status: Cleared
1 | true | true | false | false | false | 0 | 10023253 | RESISTOR ARRAY, 6.8K OHM, +/-5%, 1206 | D ECO-R252636 | 6 | Each | Production |  | RS1,RS3,RS4,RS5,RS6,RS8 |  |  |  |  |  | Part | CBRM |  | 1 |  |  | true | false | BI TECHNOLOGIES CORPORATION | BCN164AB682J7 | RESISTOR ARRAY | Active | Preferred |  | ROHS EXEMPT: 7(C)-1 | Yes - by exemption | Legacy Inventory Status: Cleared
 |  |  |  |  |  |  |  |  |  |  |  |  |  |  |  |  |  |  |  |  |  |  |  |  |  | true | false | YAGEO_RMS1 | TC164-JR-076K8L | RESISTOR, NETWORK, FILM, ISOLATED, 0.0625 W, SURFACE MOUNT | Active | Preferred |  | ROHS EXEMPT: 7(C)-1 | Yes - by exemption | Legacy Inventory Status: Cleared
 |  |  |  |  |  |  |  |  |  |  |  |  |  |  |  |  |  |  |  |  |  |  |  |  |  | true | false | YAGEO_RMS1 | 235003410682 | RESISTOR, NETWORK, FILM, ISOLATED, SURFACE MOUNT | Active | Preferred |  | BRAND: PHYCOMP. ROHS EXEMPT: 7(C)-1 | Yes - by exemption | Legacy Inventory Status: Cleared
 |  |  |  |  |  |  |  |  |  |  |  |  |  |  |  |  |  |  |  |  |  |  |  |  |  | true | false | BOURNS_RMS1 | CAY16-682J4LF | CHIP RESISTOR ARRAY | Active | Preferred |  | ROHS EXEMPT: 7(C)-1 | Yes - by exemption | Legacy Inventory Status: Cleared
 |  |  |  |  |  |  |  |  |  |  |  |  |  |  |  |  |  |  |  |  |  |  |  |  |  | true | false | YAGEO_RMS1 | 235003410682L | RESISTOR, NETWORK, FILM, ISOLATED, 0.0625 W, SURFACE MOUNT | Active | Preferred |  | BRAND: PHYCOMP.ROHS EXEMPT: 7(C)-1 | Yes - by exemption | Legacy Inventory Status: Cleared
1 | true | true | false | false | false | 0 | 10023254 | RSP RESISTOR ARRAY, 15K OHM,+/-5%, 1206 | C ECO-R252636 | 2 | Each | Production |  | RS2,RS7 |  |  |  |  |  | Part | CBRM |  | 1 |  |  | true | false | BOURNS_RMS1 | CAY16-153J4LF | CHIP RESISTOR ARRAY | Active | Preferred |  | ROHS EXEMPT: 7(C)-1 | Yes - by exemption | Legacy Inventory Status: Cleared
 |  |  |  |  |  |  |  |  |  |  |  |  |  |  |  |  |  |  |  |  |  |  |  |  |  | true | false | YAGEO_RMS1 | 235003510153L | RESISTOR, NETWORK, FILM, ISOLATED, 0.0625 W, SURFACE MOUNT | Active | Preferred |  | BRAND: PHYCOMP.ROHS EXEMPT: 7(C)-1 | Yes - by exemption | Legacy Inventory Status: Cleared
 |  |  |  |  |  |  |  |  |  |  |  |  |  |  |  |  |  |  |  |  |  |  |  |  |  | true | false | YAGEO_RMS1 | 235003510153 | RESISTOR, NETWORK, FILM, ISOLATED, SURFACE MOUNT | Active | Preferred |  | BRAND: PHYCOMP. ROHS EXEMPT: 7(C)-1 | Yes - by exemption | Legacy Inventory Status: Cleared
 |  |  |  |  |  |  |  |  |  |  |  |  |  |  |  |  |  |  |  |  |  |  |  |  |  | true | false | BI TECHNOLOGIES CORPORATION | BCN164AB153J7 | CHIP RESISTOR ARRAY | Active | Preferred |  | ROHS EXEMPT: 7(C)-1 | Yes - by exemption | Legacy Inventory Status: Cleared
 |  |  |  |  |  |  |  |  |  |  |  |  |  |  |  |  |  |  |  |  |  |  |  |  |  | true | false | YAGEO_RMS1 | YC164-JR-0715KL | RESISTOR, NETWORK, FILM, ISOLATED, 0.0625 W, SURFACE MOUNT | Active | Preferred |  | ROHS EXEMPT: 7(C)-1 | Yes - by exemption | Legacy Inventory Status: Cleared
1 | true | true | false | false | false | 0 | 10023291 | CRYSTAL, QUARTZ, 3.6864MHZ | D ECO-R252636 | 1 | Each | Production |  | Q2 |  |  |  |  |  | Part | CBRM |  | 1 |  |  | true | false | IQD | LFXTAL003260REEL |  | Active | Preferred |  |  | Yes | Legacy Inventory Status: Cleared
1 | true | true | false | false | false | 0 | 10023295 | FLAT FERRITE CORE | B ECO-R252636 | 1 | Each | Production |  | FER1 |  |  |  |  |  | Part | CBRM |  | 1 |  |  | true | false | WURTH ELEKTRONIK GMBH | 7427221 | FLAT FERRITE CORE | Active | Preferred |  | ROHS EXEMPTION:-7(C)-1 | Yes - by exemption | Legacy Inventory Status: Cleared
1 | true | true | false | false | false | 0 | 10025112 | 3 WAY, PROPORTIONAL VALVE | B ECO-R252636 | 1 | Each | Production |  | V2 |  |  |  |  |  | Part | CBRM |  | 1 |  |  | true | false | FAS | S142.0048A | 3 WAY PROPORTIONAL VALVE | Active | Preferred |  |  | Yes | Legacy Inventory Status: Cleared
1 | true | true | false | false | false | 0 | 10052329 | HEADER CONNECTOR, RIGHT ANGLE, 10 PINS | B ECO-R252636 | 1 | Each | Production |  | J4 |  |  |  |  |  | Part | CBRM |  | 1 |  |  | true | false | FCI/BERG | 75867-101LF |  | Active | Preferred |  |  | Yes | Legacy Inventory Status: Cleared
 |  |  |  |  |  |  |  |  |  |  |  |  |  |  |  |  |  |  |  |  |  |  |  |  |  | true | false | FCI/BERG | 88874-010LF |  | Active | Preferred |  |  | Yes | Legacy Inventory Status: Cleared
1 | true | true | false | false | false | 0 | 10052331 | HEADER CONNECTOR, RIGHT ANGLE, 26 PINS | B ECO-R252636 | 1 | Each | Production |  | J7 |  |  |  |  |  | Part | CBRM |  | 1 |  |  | true | false | FCI/BERG | 75867-105LF |  | Active | Preferred |  |  | Yes | Legacy Inventory Status: Cleared
 |  |  |  |  |  |  |  |  |  |  |  |  |  |  |  |  |  |  |  |  |  |  |  |  |  | true | false | FCI/BERG | 88874-026LF |  | Active | Preferred |  |  | Yes | Legacy Inventory Status: Cleared
1 | true | true | true | false | false | 0 | 10095973 | CAPACITOR ARRAY, 47PF, 50V, +/-10%,NPO,0612 | A ECO-R252633 | 11 | Each | Production |  | C14,C17,C18,C38,C41,C52,C55,C56,C58,C100,C111 |  |  |  |  |  | Part | CBRM |  | 1 |  |  | true | false | YAGEO_RMS1 | 225514611532 | ISOLATED C NETWORK, 50V, C0G, 0.000047UF, SURFACE MOUNT, CHIP-8 | Active | Preferred |  | BRAND: PHYCOMP | Yes | Legacy Inventory Status: Cleared
1 | true | true | true | false | false | 0 | 10095983 | RESISTOR, 22 K OHM,0.063W, +/-1%,0603 | A ECO-R252633 | 1 | Each | Production |  | R46 |  |  |  |  |  | Part | CBRM |  | 1 |  |  | true | false | YAGEO_RMS1 | RC0603FR-0722KL | RESISTOR, METAL GLAZE/THICK FILM, 0.1 W, 1 %, 100 PPM, 22000 OHM, SURFACE MOUNT, 0603 | Active | Preferred |  | ROHS EXEMPTION: 7( C )-1 ELECTRICAL AND ELECTRONIC COMPONENTS CONTAINING LEAD IN A GLASS. | Yes | Legacy Inventory Status: Cleared
 |  |  |  |  |  |  |  |  |  |  |  |  |  |  |  |  |  |  |  |  |  |  |  |  |  | true | false | ASJ | CR16-2202FL | THICK FILM CHIP RESISTOR | Active | Preferred |  | ROHS EXEMPTION: 7( C )-1 ELECTRICAL AND ELECTRONIC COMPONENTS CONTAINING LEAD IN A GLASS. | Yes - by exemption | Legacy Inventory Status: Cleared
 |  |  |  |  |  |  |  |  |  |  |  |  |  |  |  |  |  |  |  |  |  |  |  |  |  | true | false | YAGEO_RMS1 | 232270462203L* | RESISTOR, METAL GLAZE/THICK FILM, 0.1 W, 1 %, 100 PPM, 22000 OHM, SURFACE MOUNT, 0603 | Active | Preferred |  | BRAND: PHYCOMP. ROHS EXEMPTION: 7( C )-1 ELECTRICAL AND ELECTRONIC COMPONENTS CONTAINING LEAD IN A GLASS. | Yes - by exemption | Legacy Inventory Status: Cleared
1 | true | true | false | false | false | 0 | 10097252 | CAPACITOR ELECTROLYTIC, 1000UF,35V,+/-20% | A ECO-R252636 | 1 | Each | Production |  | C88 |  |  |  |  |  | Part | CBRM |  | 1 |  |  | true | false | ILLINOIS CAPACITOR, INC. | 108TTA035M |  | Active | Preferred |  |  | Yes | Legacy Inventory Status: Cleared
 |  |  |  |  |  |  |  |  |  |  |  |  |  |  |  |  |  |  |  |  |  |  |  |  |  | true | false | MULTICOMP (920630) | MCLV102M1VB-1327-RH |  | Active | Preferred |  |  | Yes | Legacy Inventory Status: Cleared
1 | true | true | false | false | false | 0 | 10097253 | DIODE SCHOTTKY, 40V, 1A | A ECO-R252636 | 4 | Each | Production |  | D6,D7,D15,D16 |  |  |  |  |  | Part | CBRM |  | 1 |  |  | true | false | DIODES INC_RMS1 | 1N5819HW-7-F | SURFACE MOUNT SCHOTTKY BARRIER RECTIFIER | Active | Preferred |  | ROHS EXEMPT: 7(A) | Yes | Legacy Inventory Status: Cleared
1 | true | true | false | false | false | 0 | 10097255 | STATIC RAM, 256K X 16 BIT, TSOP2 | A ECO-R252636 | 1 | Each | Production |  | IC3 |  |  |  |  |  | Part | CBRM |  | 1 |  |  | true | false | SAMSUNG_RMS1 | K6R4016C1D-UI10T | ASYNC FAST SRAM | Active | Preferred |  |  | Yes | Legacy Inventory Status: Cleared
1 | true | true | false | false | false | 0 | 10097256 | CONNECTOR, 22 CONTACTS | B ECO-R252636 | 1 | Each | Production |  | J1 |  |  |  |  |  | Part | CBRM |  | 1 |  |  | true | false | MOLEX_RMS1 | 0526102272 | CONNECTOR | Active | Preferred |  |  | Yes | Legacy Inventory Status: Cleared
 |  |  |  |  |  |  |  |  |  |  |  |  |  |  |  |  |  |  |  |  |  |  |  |  |  | true | false | MOLEX_RMS1 | 0526102271 | CONNECTOR | Active | Preferred |  |  | Yes | Legacy Inventory Status: Cleared
1 | true | true | false | false | false | 0 | 10097257 | CONNECTOR, 8 CONTACTS | A ECO-R252636 | 1 | Each | Production |  | J2 |  |  |  |  |  | Part | CBRM |  | 1 |  |  | true | false | J.S.T. CORPORATION | B8B-ZR-SM4-TF (LF)(SN) | CONNECTOR | Active | Preferred |  |  | Yes | Legacy Inventory Status: Cleared
1 | true | true | false | false | false | 0 | 10097259 | CONNECTOR, SPO2, 12 CONTACTS | A ECO-R252636 | 1 | Each | Production |  | J3 |  |  |  |  |  | Part | CBRM |  | 1 |  |  | true | false | J.S.T. CORPORATION | B12B-ZR-SM4-TF (LF)(SN) | CONNECTOR | Active | Preferred |  |  | Yes | Legacy Inventory Status: Cleared
1 | true | true | false | false | false | 0 | 10097260 | CONNECTOR, TEMPERATURE MEASURE, 2 CONTACTS | A ECO-R252636 | 2 | Each | Production |  | J5,J19 |  |  |  |  |  | Part | CBRM |  | 1 |  |  | true | false | J.S.T. CORPORATION | B2B-ZR-SM4-TF (LF)(SN) | CONNECTOR | Active | Preferred |  |  | Yes | Legacy Inventory Status: Cleared
1 | true | true | false | false | false | 0 | 10097262 | CONNECTOR,FIO2, 3 CONTACTS | A ECO-R252636 | 1 | Each | Production |  | J11 |  |  |  |  |  | Part | CBRM |  | 1 |  |  | true | false | J.S.T. CORPORATION | B3B-ZR-SM4-TF (LF)(SN) | ZH CONNECTOR | Active | Preferred |  |  | Yes | Legacy Inventory Status: Cleared
1 | true | true | false | false | false | 0 | 10097263 | CONNECTOR, 40 CONTACTS | A ECO-R252636 | 1 | Each | Production |  | J17 |  |  |  |  |  | Part | CBRM |  | 1 |  |  | true | false | TYCO ELECTRONICS | 5177983-1 | 0.8MM FREE HEIGHT CONNECTOR | Active | Preferred |  |  | Yes | Legacy Inventory Status: Cleared
 |  |  |  |  |  |  |  |  |  |  |  |  |  |  |  |  |  |  |  |  |  |  |  |  |  | true | false | TYCO ELECTRONICS | 5177985-1 |  | Active | Alternate |  |  | Yes | Legacy Inventory Status: Cleared
1 | true | true | false | false | false | 0 | 10097265 | CONNECTOR, BUZZER CARD, 7 CONTACTS | A ECO-R252636 | 1 | Each | Production |  | J18 |  |  |  |  |  | Part | CBRM |  | 1 |  |  | true | false | J.S.T. CORPORATION | B7B-ZR-SM4-TF (LF)(SN) | ZH CONNECTOR | Active | Preferred |  |  | Yes | Legacy Inventory Status: Cleared
1 | true | true | false | false | false | 0 | 10097266 | RESISTOR,10K OHM, 0.063W,+/-5%,0603 | A ECO-R252636 | 10 | Each | Production |  | R5,R6,R28,R29,R32,R43,R53,R54,R62,R70 |  |  |  |  |  | Part | CBRM |  | 1 |  |  | true | false | YAGEO_RMS1 | 232270260103L | RESISTOR, METAL GLAZE/THICK FILM, 0.1 W, 5 %, 100 PPM, 10000 OHM, SURFACE MOUNT, 0603 | Active | Preferred |  | BRAND: PHYCOMP.ROHS EXMEPT: 7(C)-1 | Yes - by exemption | Legacy Inventory Status: Cleared
 |  |  |  |  |  |  |  |  |  |  |  |  |  |  |  |  |  |  |  |  |  |  |  |  |  | true | false | YAGEO_RMS1 | 232270260103 | RESISTOR, METAL GLAZE/THICK FILM, 0.1 W, 5 %, 100 PPM, 10000 OHM, SURFACE MOUNT, 0603 | Active | Preferred |  | BRAND: PHYCOMP.ROHS EXMEPT: 7(C)-1 | Yes - by exemption | Legacy Inventory Status: Cleared
 |  |  |  |  |  |  |  |  |  |  |  |  |  |  |  |  |  |  |  |  |  |  |  |  |  | true | false | VISHAY_RMS1 | CRCW060310K0JNEA | THICK FILM RECTANGULAR CHIP RESISTOR | Active | Preferred |  | ROHS EXMEPT: 7(C)-1 | Yes - by exemption | Legacy Inventory Status: Cleared
 |  |  |  |  |  |  |  |  |  |  |  |  |  |  |  |  |  |  |  |  |  |  |  |  |  | true | false | ASJ | CR16-103JL | THICK FILM CHIP RESISTOR | Active | Preferred |  | ROHS EXMEPT: 7(C)-1 | Yes - by exemption | Legacy Inventory Status: Cleared
 |  |  |  |  |  |  |  |  |  |  |  |  |  |  |  |  |  |  |  |  |  |  |  |  |  | true | false | YAGEO_RMS1 | RC0603JR-0710KL | RESISTOR, METAL GLAZE/THICK FILM, 0.1 W, 5 %, 100 PPM, 10000 OHM, SURFACE MOUNT, 0603 | Active | Preferred |  | ROHS EXMEPT: 7(C)-1 | Yes - by exemption | Legacy Inventory Status: Cleared
1 | true | true | false | false | false | 0 | 10097268 | RESISTOR, 10.5K OHM, 0603, +/-0.1% | A ECO-R252636 | 1 | Each | Production |  | R15 |  |  |  |  |  | Part | CBRM |  | 1 |  |  | true | false | SUSUMU CO. | RG1608P-1052-B-T5 |  | Active | Preferred |  |  | Yes | Legacy Inventory Status: Cleared
 |  |  |  |  |  |  |  |  |  |  |  |  |  |  |  |  |  |  |  |  |  |  |  |  |  | true | false | WELWYN | PCF0603R-10K5BI | PRECISION SURFACE MOUNT RESISTOR | Active | Preferred |  |  | Yes | Legacy Inventory Status: Cleared
1 | true | true | false | false | false | 0 | 10097270 | RESISTOR,1.37K OHM,0.063W,+/-0.1%,0603 | A ECO-R252636 | 1 | Each | Production |  | R57 |  |  |  |  |  | Part | CBRM |  | 1 |  |  | true | false | SUSUMU CO. | RG1608P-1371-B-T5 |  | Active | Preferred |  |  | Yes | Legacy Inventory Status: Cleared
 |  |  |  |  |  |  |  |  |  |  |  |  |  |  |  |  |  |  |  |  |  |  |  |  |  | true | false | TYCO ELECTRONICS | 3-1879219-4 | THIN FILM PRECISION CHIP RESISTOR | Active | Preferred |  |  | Yes | Legacy Inventory Status: Cleared
 |  |  |  |  |  |  |  |  |  |  |  |  |  |  |  |  |  |  |  |  |  |  |  |  |  | true | false | TYCO ELECTRONICS | CPF0603B-1K37E | THIN FILM PRECISION CHIP RESISTOR | Active | Preferred |  |  | Yes | Legacy Inventory Status: Cleared
 |  |  |  |  |  |  |  |  |  |  |  |  |  |  |  |  |  |  |  |  |  |  |  |  |  | true | false | VISHAY_RMS1 | TNPW06031K37BEEA | PRECISION CHIP RESISTOR | Active | Preferred |  | ROHS EXEMPT: 7(C)-1 | Yes - by exemption | Legacy Inventory Status: Cleared
 |  |  |  |  |  |  |  |  |  |  |  |  |  |  |  |  |  |  |  |  |  |  |  |  |  | true | false | WELWYN | PCF0603R-1K37BI | PRECISION SURFACE MOUNT RESISTOR | Active | Preferred |  |  | Yes | Legacy Inventory Status: Cleared
1 | true | true | false | false | false | 0 | 10097271 | RESISTOR, 100K OHM, 0.063W,+/-0.1%,0603 | A ECO-R252636 | 1 | Each | Production |  | R58 |  |  |  |  |  | Part | CBRM |  | 1 |  |  | true | false | SUSUMU CO. | RG1608P-104-B-T5 | RES SMD 100K OHM 0.1% 1/10W 0603 | Active | Preferred |  |  | RoHS3 Compliant | Legacy Inventory Status: Cleared
 |  |  |  |  |  |  |  |  |  |  |  |  |  |  |  |  |  |  |  |  |  |  |  |  |  | true | false | WELWYN | PCF0603R-100KBI | LOW VALUE FLAT CHIP RESISTOR | Active | Preferred |  |  | Yes | Legacy Inventory Status: Cleared
 |  |  |  |  |  |  |  |  |  |  |  |  |  |  |  |  |  |  |  |  |  |  |  |  |  | true | false | YAGEO_RMS1 | RT0603BRD07100KL | RESISTOR, THIN FILM, 0.1 W, 0.1 %, 25 PPM, 100000 OHM, SURFACE MOUNT, 0603 | Active | Preferred |  | ROHS EXEMPT: 7(C)-1 | Yes - by exemption | Legacy Inventory Status: Cleared
1 | true | true | false | false | false | 0 | 10097272 | RESISTOR, PRECISION,10K OHM, 0.063W,+/-0.1%,0603 | A ECO-R252636 | 1 | Each | Production |  | R71 |  |  |  |  |  | Part | CBRM |  | 1 |  |  | true | false | SUSUMU CO | RG1608P-103-B-T5 | RES 10.0K OHM 1/10W .1% 0603 SMD | Active | Preferred |  |  | Yes | Legacy Inventory Status: Cleared
 |  |  |  |  |  |  |  |  |  |  |  |  |  |  |  |  |  |  |  |  |  |  |  |  |  | true | false | WELWYN | PCF0603R-10KBI | PRECISION SURFACE MOUNT RESISTOR | Active | Preferred |  |  | Yes | Legacy Inventory Status: Cleared
 |  |  |  |  |  |  |  |  |  |  |  |  |  |  |  |  |  |  |  |  |  |  |  |  |  | true | false | YAGEO_RMS1 | RT0603BRB0710K |  | Active | Preferred |  | ROHS EXEMPT:7(C)-1 | Yes - by exemption | Legacy Inventory Status: Cleared
 |  |  |  |  |  |  |  |  |  |  |  |  |  |  |  |  |  |  |  |  |  |  |  |  |  | true | false | YAGEO_RMS1 | RT0603BRB0710KL |  | Active | Preferred |  | ROHS EXEMPT:7(C)-1 | Yes - by exemption | Legacy Inventory Status: Cleared
1 | true | true | false | false | false | 0 | 10097273 | RESISTOR,PRECISION, 3.24K OHM, 0.063W,+/-0.1%,0603 | A ECO-R252636 | 1 | Each | Production |  | R73 |  |  |  |  |  | Part | CBRM |  | 1 |  |  | true | false | SUSUMU CO | RG1608P-3241-B-T5 |  | Active | Preferred |  |  | Yes | Legacy Inventory Status: Cleared
 |  |  |  |  |  |  |  |  |  |  |  |  |  |  |  |  |  |  |  |  |  |  |  |  |  | true | false | WELWYN | PCF0603R-3K24BI | PRECISION SURFACE MOUNT RESISTOR | Active | Preferred |  |  | Yes | Legacy Inventory Status: Cleared
 |  |  |  |  |  |  |  |  |  |  |  |  |  |  |  |  |  |  |  |  |  |  |  |  |  | true | false | WELWYN | PCF0603R-3K24BT1 | PRECISION SURFACE MOUNT RESISTOR | Active | Preferred |  |  | Yes | Legacy Inventory Status: Cleared
 |  |  |  |  |  |  |  |  |  |  |  |  |  |  |  |  |  |  |  |  |  |  |  |  |  | true | false | YAGEO_RMS1 | RT0603BRD073K24L |  | Active | Preferred |  | ROHS EXMEPT: 7(C)-1 | Yes - by exemption | Legacy Inventory Status: Cleared
1 | true | true | false | false | false | 0 | 10097274 | TRANSISTOR MOSFET N CHANNEL 60V, 0.18A | A ECO-R252636 | 9 | Each | Production |  | T1,T2,T4,T5,T6,T8,T9,T14,T21 |  |  |  |  |  | Part | CBRM |  | 1 |  |  | true | false | ON SEMICONDUCTOR_RMS1 | 2N7002LT1G | SMALL SIGNAL MOSFET | Active | Preferred |  |  | RoHS3 Compliant | Cleared
 |  |  |  |  |  |  |  |  |  |  |  |  |  |  |  |  |  |  |  |  |  |  |  |  |  | true | false | NXP SEMICONDUCTORS_RMS1 | 2N7002,215 |  | Active | Preferred |  |  | Yes | Legacy Inventory Status: Cleared
 |  |  |  |  |  |  |  |  |  |  |  |  |  |  |  |  |  |  |  |  |  |  |  |  |  | true | false | NXP SEMICONDUCTORS_RMS1 | 2N7002 | N-CHANNEL TRENCHMOS FET | Active | Preferred |  |  | Yes | Legacy Inventory Status: Cleared
1 | true | true | false | false | false | 0 | 10099516 | LARGE CYLINDRICAL HEAD DOMED 6 LOBES INTERNAL STAINLESS M3X5 | A ECO-R252636 | 8 | Each | Production |  |  |  |  |  |  |  | Part | CBRM |  | 1 |  |  | true | false | BOSSARD | 3061604 |  | Active | Preferred |  |  | Yes | Legacy Inventory Status: Cleared
1 | true | true | false | false | false | 0 | 10099517 | SCREW,LG CYLNDRL HEAD DOMED,6 LOBES,STNLS,M3*8 | A ECO-R252636 | 8 | Each | Production |  |  |  |  |  |  |  | Part | CBRM |  | 1 |  |  | true | false | BOSSARD | 1983385 |  | Active | Preferred |  |  | Yes | Legacy Inventory Status: Cleared
1 | true | true | false | false | false | 0 | 10099518 | WASHER, NFE 25513, 3X6 | A ECO-R252636 | 4 | Each | Production |  |  |  |  |  |  |  | Part | CBRM |  | 1 |  |  | true | false | BOSSARD | 8026807 |  | Active | Preferred |  |  | Yes | Legacy Inventory Status: Cleared
1 | true | true | false | false | false | 0 | 10099519 | SCREW,LG CYLNDRL HEAD DOMED,6 LOBES,STNLS,M2,5*8 | A ECO-R252636 | 4 | Each | Production |  |  |  |  |  |  |  | Part | CBRM |  | 1 |  |  | true | false | BOSSARD | 3108703 |  | Active | Preferred |  |  | Yes | Legacy Inventory Status: Cleared
1 | true | true | false | false | false | 0 | 10099520 | STAINLESS STEEL HEXAGONAL NUT, M2.5 | A ECO-R252636 | 4 | Each | Production |  |  |  |  |  |  |  | Part | CBRM |  | 1 |  |  | true | false | BOSSARD | 1241427 |  | Active | Preferred |  |  | Yes | Legacy Inventory Status: Cleared
1 | true | true | false | false | false | 0 | 10099521 | TOOTH LOCK WASHER, DEC 2.5 | A ECO-R252636 | 4 | Each | Production |  |  |  |  |  |  |  | Part | CBRM |  | 1 |  |  | true | false | BOSSARD | 1228919 |  | Active | Preferred |  |  | Yes | Legacy Inventory Status: Cleared
1 | true | true | false | false | false | 0 | 10103067 | TAMPER PROOF VARNISH, ROHS | A ECO-R252636 | 1 | Each | Production |  |  |  |  |  |  |  | Part | CBRM |  | 1 |  |  | true | false | LOCTITE (HENKEL CORPORATION) | 7400 |  | Active | Alternate |  |  | Yes | Legacy Inventory Status: Cleared
1 | true | false | false | false | false | 0 | 10125623 | SCHEMATIC DIAGRAM CPU CARD | A ECO-R256396 | 1 |  | Production |  |  |  |  |  |  |  | Document | CBRM |  | 1
1 | true | true | false | false | false | 0 | 4096600.M00.002 | EMC CASING - CASE 2 PRESSURE SENSORS | A ECO-R252636 | 1 | Each | Production |  | BL2 |  |  |  |  |  | Part | CBRM |  | 1 |  |  | true | false | SUZHOU ACE SHEET MATEL MANUFACTURING CO., LTD | 4096600.M00.002 | EMC CASING - CASE 2 PRESSURE SENSORS (CUSTOM PART) | Active | Preferred |  | CUSTOM PART PER COVIDIEN DRAWING 4096600.M00.002 | Yes | Legacy Inventory Status: Cleared
1 | true | true | false | false | false | 0 | 4096600.M00.003 | EMC CASING - CASE 3 PRESSURE SENSORS | A ECO-R252636 | 1 | Each | Production |  | BL4 |  |  |  |  |  | Part | CBRM |  | 1 |  |  | true | false | SUZHOU ACE SHEET MATEL MANUFACTURING CO., LTD | 4096600.M00.003 | EMC CASING - CASE 3 PRESSURE SENSORS (CUSTOM PART) | Active | Preferred |  | CUSTOM PART PER COVIDIEN DRAWING 4096600.M00.003 | Yes | Legacy Inventory Status: Cleared
1 | true | true | false | false | false | 0 | 4096600.M00.023 | EMC,FLOW SENSOR HOUSING,IC15 & IC17 | A ECO-R252636 | 2 | Each | Production |  | BL1,BL3 |  |  |  |  |  | Part | CBRM |  | 1 |  |  | true | false | SUZHOU ACE SHEET MATEL MANUFACTURING CO., LTD | 4096600.M00.023 | EMC,FLOW SENSOR HOUSING,IC15 & IC17 (CUSTOM PART) | Active | Preferred |  | CUSTOM PART PER COVIDIEN DRAWING 4096600.M00.023 | Yes | Legacy Inventory Status: Cleared
1 | true | true | false | false | false | 0 | GR106772 | PRINTED CIRCUIT, CPU BOARD RB0505 | A MC002637 | 1 | Each | Production |  |  |  |  |  |  |  | Part | CBRM |  | 1 |  |  | true | false | TTM | GR106772 |  | Active | Preferred |  |  | Yes | Legacy Inventory Status: Cleared
1 | true | true | false | false | false | 1 | 10025113 | DOUBLE SIDED TAPE, ADHESIVE, 0.01M | C ECO-R252636 | 1 | Meter | Production |  |  |  |  |  |  |  | Part | CBRM |  | 1 |  |  | true | false | 3M_RMS1 | VHB4910-33X19 | ACRYLIC FOAM TAPE | Active | Preferred |  |  | Yes | Legacy Inventory Status: Cleared
1 | true | true | false | false | false | 2 | 10023293 | PLASTIC SPACER 2M3 LG8 | C ECO-R252636 | 4 | Each | Production |  |  |  |  |  |  |  | Part | CBRM |  | 1 |  |  | true | false | SKIFFY LTD | 302 3080 599 35 | HEXAGONAL SPACER | Active | Preferred |  |  | Yes | Legacy Inventory Status: Cleared
 |  |  |  |  |  |  |  |  |  |  |  |  |  |  |  |  |  |  |  |  |  |  |  |  |  | true | false | RICHCO INC._RMS1 | HTSN-M3-8-6-1 | PLASTIC SPACER 2M3 LG8 | Active | Preferred |  |  | Yes | Legacy Inventory Status: Cleared
1 | true | true | false | false | false | 4 | 10023294 | PLASTIC SPACER, 2 M3 LG12 | B ECO-R252636 | 4 | Each | Production |  |  |  |  |  |  |  | Part | CBRM |  | 1 |  |  | true | false | SKIFFY LTD | 302 3120 599 35 | HEXAGONAL SPACER | Active | Preferred |  |  | Yes | Legacy Inventory Status: Cleared
 |  |  |  |  |  |  |  |  |  |  |  |  |  |  |  |  |  |  |  |  |  |  |  |  |  | true | false | RICHCO, INC. | HTSN-M3-12-6-1 | PLASTIC SPACER | Active | Preferred |  |  | Yes | Legacy Inventory Status: Cleared
1 | true | true | false | false | false | 11 | 10022161 | ADHESIVE | A ECO-R252636 | 1 | Each | Production |  |  |  |  |  |  |  | Part | CBRM |  | 1 |  |  | true | false | 3M_RMS1 | 7838 B/A | STRUCTURAL ADHESIVE | Active | Preferred |  |  | Yes | Legacy Inventory Status: Cleared
1 | true | true | true | false | false | 12 | 3838600 | PC BOARD TRACABILITY LABEL | C ECO-R252633 | 1 | Each | Production |  |  |  |  |  |  |  | Part | CBRM |  | 1 |  |  | true | false | BRADY_RMS1 | 3838600-H | B-727 LABEL, POLYIMIDE, GLOSSY WHITE THERMAL TRANSFER PRINTABLE LABEL STOCK | Active | Preferred |  | CUSTOM LABEL PER COVIDIEN DRAWING 3838600 | Yes | Legacy Inventory Status: Cleared
1 | true | true | false | false | false | 13 | 10022885 | COIN CELL BATTERY RETAINER | B ECO-R252636 | 1 | Each | Production |  |  |  |  |  |  |  | Part | CBRM |  | 1 |  |  | true | false | KEYSTONE ELECTRONICS CORP | 3000 | LITHIUM COIN CELL BATTERY RETAINER | Active | Preferred |  |  | Yes | Legacy Inventory Status: Cleared
1 | true | true | false | false | false | 14 | 3821600 | DISPLAY ASSEMBLY | D ECO-R252636 | 1 | Each | Production |  |  |  |  |  |  |  | Part | CBRM |  | 1 |  |  | true | false | CLAIRITEC | 3821600 | DISPLAY ASSEMBLY (CUSTOM PART) | Active | Preferred |  | CUSTOM PART PER COVIDIEN DRAWING 3821600 | Yes | Legacy Inventory Status: Cleared
1 | true | true | false | false | false | 15 | 10029086 | LOW STATIC POLYIMIDE FILM TAPE, REF: 5419 | C ECO-R252636 | 50 | Millimeter | Production |  |  |  |  |  |  |  | Part | CBRM |  | 1 |  |  | true | false | 3M_RMS1 | 5419 |  | Active | Preferred |  |  | Yes | Legacy Inventory Status: Cleared
Manufacturers
Attachments(Image) | Manufacture Part Has Redline | Mfr. Name | Mfr. Part Number | Mfr. Part Description | Mfr. Part Lifecycle Phase | Preferred Status | Sites | Reference Notes | RoHS Compliant? | RoHS Compliance Statement
true | false | JABIL SUPPLIER - SHANGHAI UPP CO.,LTD.(LOC) | GR106769 |  | Active | Preferred |  | CUSTOM PART PER COVIDIEN P/N GR106769 | Yes | Legacy Inventory Status: Cleared
Attachments
Is Checked Out | Has Been Redlined | Filename | File Description | File Size | File Type | Attachment Type | Modified Date | Last View Date | Checkout User | Checkout Date | Checkout Location | Checkin User | Folder Number | Folder Version
false | false | GR106769A00.pdf | Redlines From Rev A to B | 100801 | pdf |  | 13/Jun/2015 12:31:02 PM BST | 13/Jun/2015 12:31:02 PM BST |  |  |  | Migration, Data | FF0006927423 | 1
false | false | GR106769_B_ECO-R251873.pdf | RMS Historical PDF - ECO-R251873 | 123533 | pdf |  | 18/Aug/2015 01:00:55 PM BST | 18/Aug/2015 01:00:55 PM BST |  |  |  | Migration, Data | FF0009980892 | 1
false | false | GR106769B00.pdf | Approved Rev B | 91078 | pdf |  | 13/Jun/2015 12:31:03 PM BST | 22/Jul/2015 10:41:27 AM BST |  |  |  | Migration, Data | FF0006927424 | 1
false | false | GR106769B00.zip | Approved Rev B - Source Files | 7273921 | zip |  | 13/Jun/2015 12:31:03 PM BST | 13/Jun/2015 12:31:03 PM BST |  |  |  | Migration, Data | FF0006927425 | 1
