nsynet/electronics_project2/Medtronic_PB560呼吸机开源资料(3D图纸_原理图_说明书_软件代码等)/medtronic-pb560-ventilator-system-file-set-2/3D CAD Models/PB560 Assy/702-09 Entretoise AV Legendair.SLDPRT

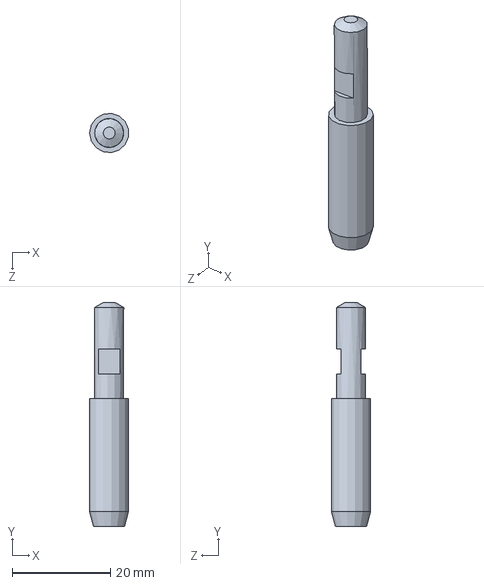
[picture p27: CAD file, 2023-12-02]
Medtronic_PB560呼吸机开源资料(3D图纸_原理图_说明书_软件代码等)/medtronic-pb560-ventilator-system-file-set-2/3D CAD Models/PB560 Assy/702-09 Entretoise AV Legendair.SLDPRT
7.91 x 45.5 x 7.96 mm
