nsynet/electronics_project2/Medtronic_PB560呼吸机开源资料(3D图纸_原理图_说明书_软件代码等)/medtronic-pb560-ventilator-system-file-set-2/3D CAD Models/PB560 Assy/Extruded housing.SLDPRT

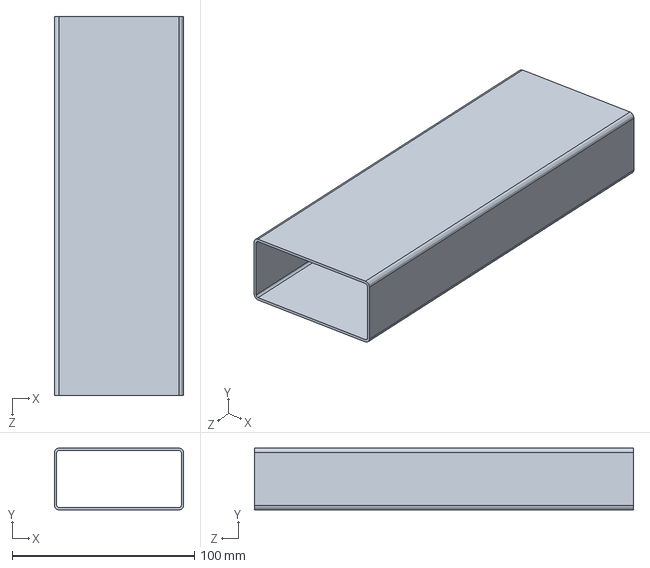
[picture p29: CAD file, 2023-12-02]
Medtronic_PB560呼吸机开源资料(3D图纸_原理图_说明书_软件代码等)/medtronic-pb560-ventilator-system-file-set-2/3D CAD Models/PB560 Assy/Extruded housing.SLDPRT
71.0 x 34.0 x 208.0 mm
