nsynet/electronics_project2/Medtronic_PB560呼吸机开源资料(3D图纸_原理图_说明书_软件代码等)/medtronic-pb560-ventilator-system-file-set-2/3D CAD Models/PB560 Assy/transfo.SLDPRT

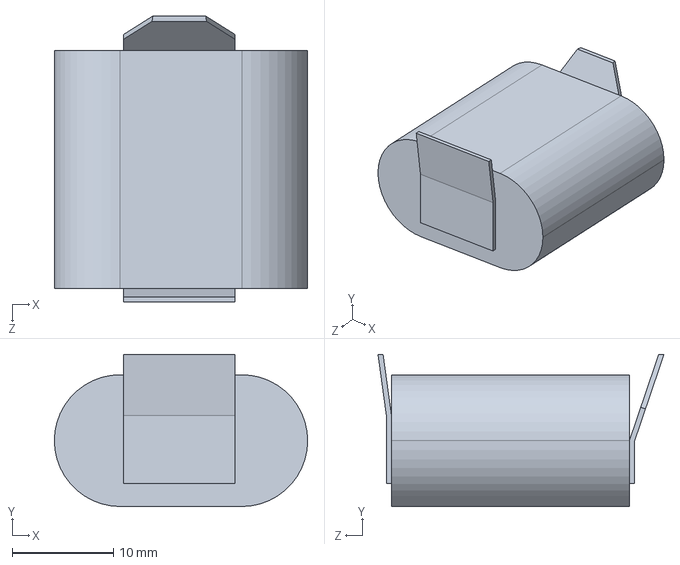
[picture p30: CAD file, 2023-12-02]
Medtronic_PB560呼吸机开源资料(3D图纸_原理图_说明书_软件代码等)/medtronic-pb560-ventilator-system-file-set-2/3D CAD Models/PB560 Assy/transfo.SLDPRT
25.0 x 15.0 x 28.2 mm
