nsynet/electronics_project2/Medtronic_PB560呼吸机开源资料(3D图纸_原理图_说明书_软件代码等)/medtronic-pb560-ventilator-system-file-set-2/Electronic PCBAs/GR106769_CPU_PCBA/3D_Model/GR106769B00/condensateur C88.SLDPRT

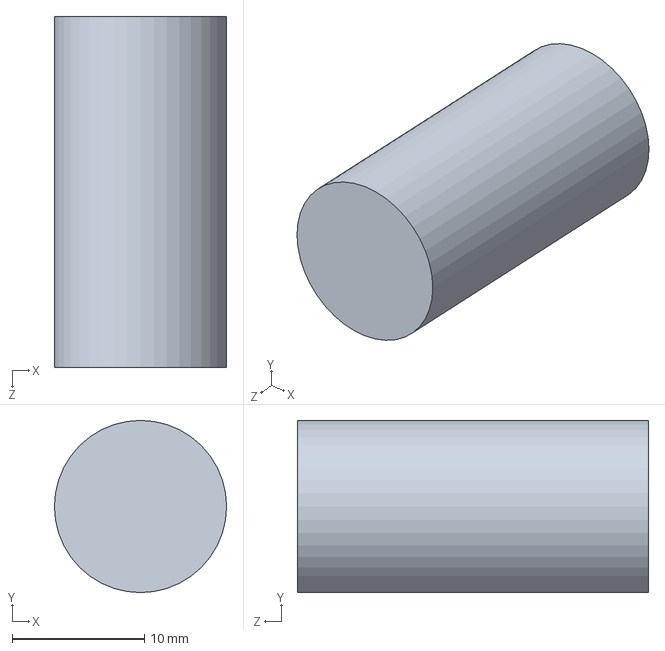
[picture p31: CAD file, 2023-12-02]
Medtronic_PB560呼吸机开源资料(3D图纸_原理图_说明书_软件代码等)/medtronic-pb560-ventilator-system-file-set-2/Electronic PCBAs/GR106769_CPU_PCBA/3D_Model/GR106769B00/condensateur C88.SLDPRT
13.0 x 13.0 x 26.5 mm
