nsynet/electronics_project2/Medtronic_PB560呼吸机开源资料(3D图纸_原理图_说明书_软件代码等)/medtronic-pb560-ventilator-system-file-set-2/Electronic PCBAs/GR106769_CPU_PCBA/3D_Model/GR106769B00/capteurpressionASDX001D44R.SLDPRT

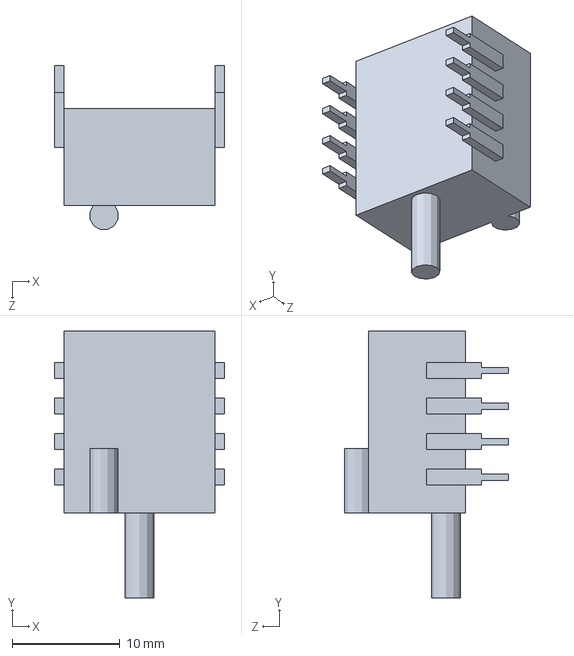
[picture p33: CAD file, 2023-12-02]
Medtronic_PB560呼吸机开源资料(3D图纸_原理图_说明书_软件代码等)/medtronic-pb560-ventilator-system-file-set-2/Electronic PCBAs/GR106769_CPU_PCBA/3D_Model/GR106769B00/capteurpressionASDX001D44R.SLDPRT
15.8 x 24.8 x 15.2 mm
