nsynet/electronics_project2/Medtronic_PB560呼吸机开源资料(3D图纸_原理图_说明书_软件代码等)/medtronic-pb560-ventilator-system-file-set-2/3D CAD Models/PB560 Assy/tuyau pression prox1.6x4.8.SLDPRT

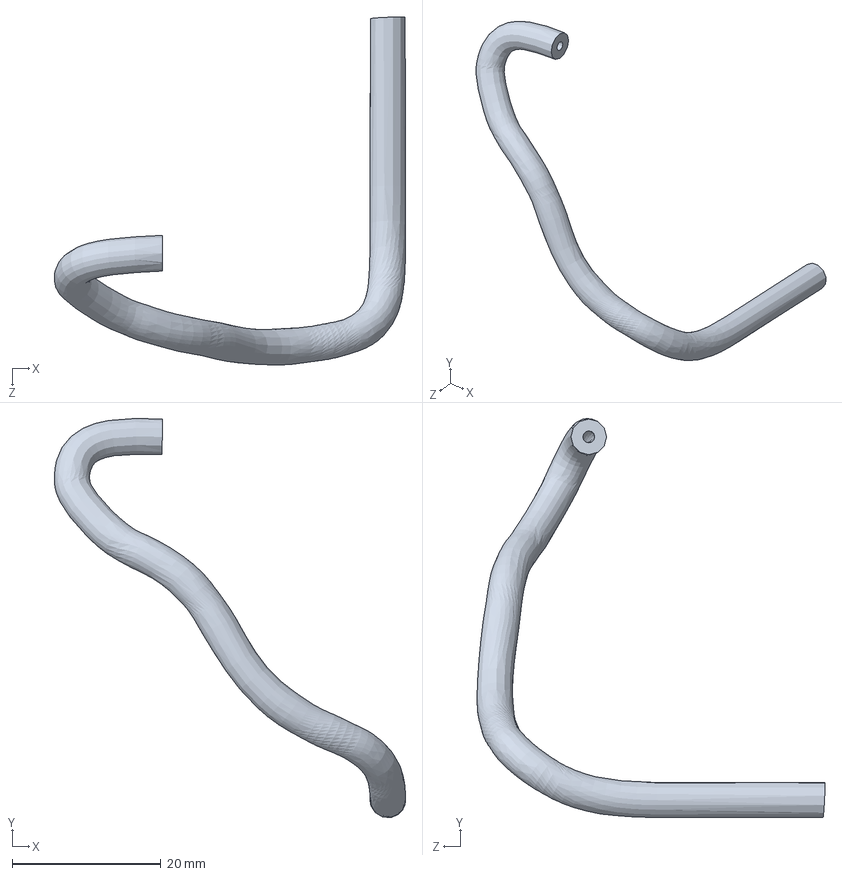
[picture p36: CAD file, 2023-12-02]
Medtronic_PB560呼吸机开源资料(3D图纸_原理图_说明书_软件代码等)/medtronic-pb560-ventilator-system-file-set-2/3D CAD Models/PB560 Assy/tuyau pression prox1.6x4.8.SLDPRT
47.2 x 53.6 x 46.8 mm
