nsynet/electronics_project2/Medtronic_PB560呼吸机开源资料(3D图纸_原理图_说明书_软件代码等)/medtronic-pb560-ventilator-system-file-set-2/3D CAD Models/PB560 Assy/Vis TCB M3-12 hexalobes acier zingué.sldprt

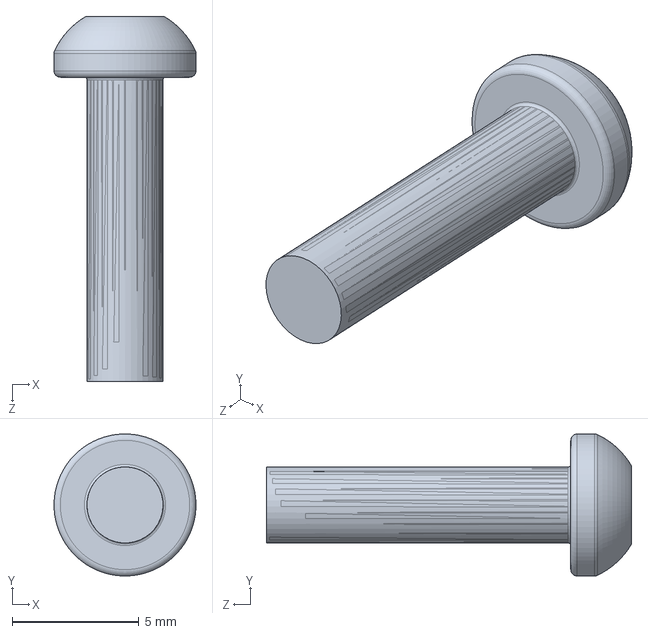
[picture p52: CAD file, 2023-12-02]
Medtronic_PB560呼吸机开源资料(3D图纸_原理图_说明书_软件代码等)/medtronic-pb560-ventilator-system-file-set-2/3D CAD Models/PB560 Assy/Vis TCB M3-12 hexalobes acier zingué.sldprt
5.60 x 5.60 x 14.4 mm
