nsynet/electronics_project2/Medtronic_PB560呼吸机开源资料(3D图纸_原理图_说明书_软件代码等)/medtronic-pb560-ventilator-system-file-set-2/3D CAD Models/PB560 Assy/tuyau sortie vanne pilot1.6x4.8.SLDPRT

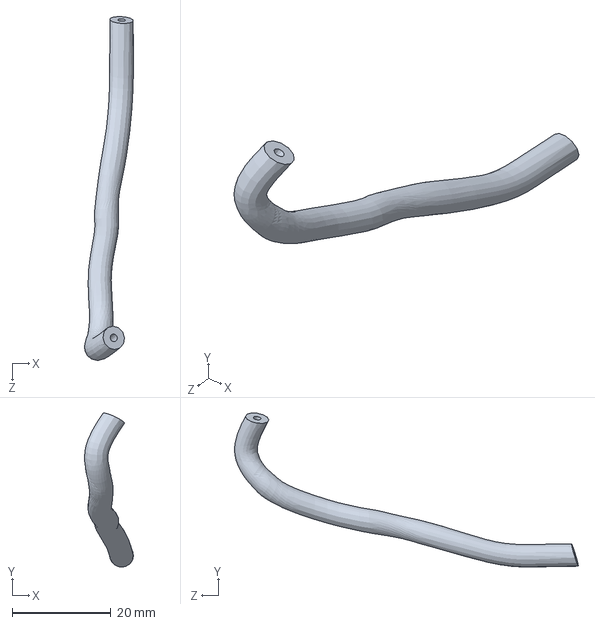
[picture p60: CAD file, 2023-12-02]
Medtronic_PB560呼吸机开源资料(3D图纸_原理图_说明书_软件代码等)/medtronic-pb560-ventilator-system-file-set-2/3D CAD Models/PB560 Assy/tuyau sortie vanne pilot1.6x4.8.SLDPRT
9.88 x 31.1 x 69.5 mm
