nsynet/electronics_project2/Medtronic_PB560呼吸机开源资料(3D图纸_原理图_说明书_软件代码等)/medtronic-pb560-ventilator-system-file-set-2/3D CAD Models/PB560 Assy/PRECI-DIP 811-S1-002-30-014101.SLDPRT

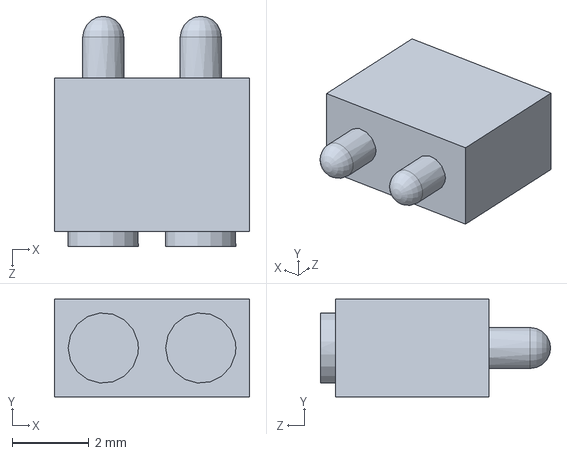
[picture p79: CAD file, 2023-12-02]
Medtronic_PB560呼吸机开源资料(3D图纸_原理图_说明书_软件代码等)/medtronic-pb560-ventilator-system-file-set-2/3D CAD Models/PB560 Assy/PRECI-DIP 811-S1-002-30-014101.SLDPRT
5.08 x 2.54 x 6.00 mm
