nsynet/electronics_project2/Medtronic_PB560呼吸机开源资料(3D图纸_原理图_说明书_软件代码等)/medtronic-pb560-ventilator-system-file-set-2/3D CAD Models/PB560 Assy/INGUN GKS 913 305 230 A 15 02 S.SLDPRT

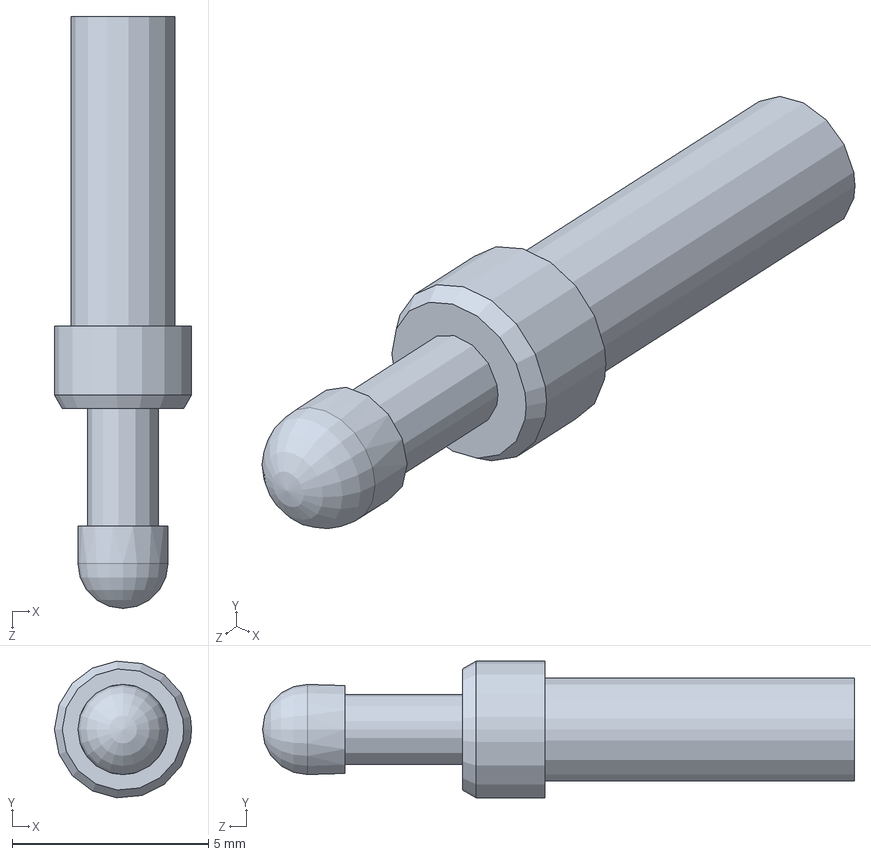
[picture p99: CAD file, 2023-12-02]
Medtronic_PB560呼吸机开源资料(3D图纸_原理图_说明书_软件代码等)/medtronic-pb560-ventilator-system-file-set-2/3D CAD Models/PB560 Assy/INGUN GKS 913 305 230 A 15 02 S.SLDPRT
3.50 x 3.49 x 15.1 mm
