nsynet/electronics_project2/Medtronic_PB560呼吸机开源资料(3D图纸_原理图_说明书_软件代码等)/medtronic-pb560-ventilator-system-file-set-2/Mechanical Part Drawings/10079556/10079556B00.PDF

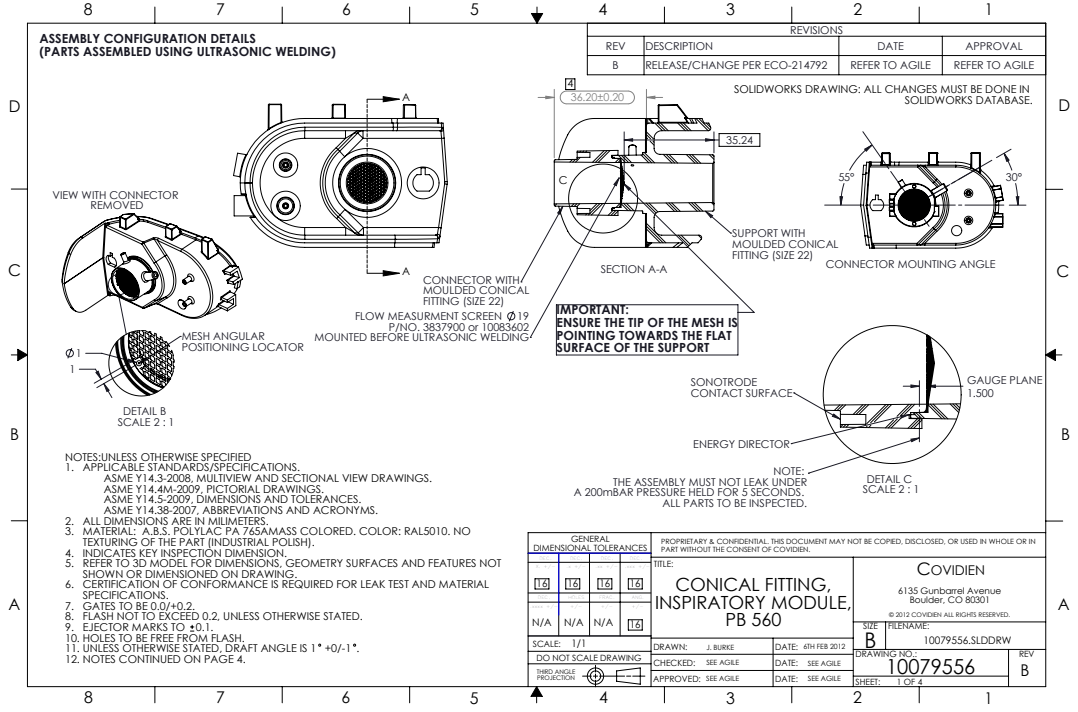
[picture p112: page 1]
SECTION A-A; CONNECTOR WITH MOULDED CONICAL FITTING (SIZE 22); SUPPORT WITH MOULDED CONICAL FITTING (SIZE 22); DETAIL B SCALE 2 : 1; MESH ANGULAR POSITIONING LOCATOR; GAUGE PLANE; DETAIL C SCALE 2 : 1; CONTACT SURFACE; ENERGY DIRECTOR; SOLIDWORKS DATABASE.; 9. EJECTOR MARKS TO; J. BURKE; 6TH FEB 2012; THIRD ANGLE; SHEET:; DATE:; DRAWING NO.:; SEE AGILE; .xxxx +/-

ASSEMBLY CONFIGURATION DETAILS
(PARTS ASSEMBLED USING ULTRASONIC WELDING)

REVISIONS

REV | DESCRIPTION | DATE | APPROVAL
B | RELEASE/CHANGE PER ECO-214792 | REFER TO AGILE | REFER TO AGILE

SOLIDWORKS DRAWING: ALL CHANGES MUST BE DONE IN

VIEW WITH CONNECTOR
REMOVED

CONNECTOR MOUNTING ANGLE

IMPORTANT:
ENSURE THE TIP OF THE MESH IS
POINTING TOWARDS THE FLAT
SURFACE OF THE SUPPORT

FLOW MEASURMENT SCREEN 19
MOUNTED BEFORE ULTRASONIC WELDING

NOTES:UNLESS OTHERWISE SPECIFIED
1. APPLICABLE STANDARDS/SPECIFICATIONS.
ASME Y14.3-2008, MULTIVIEW AND SECTIONAL VIEW DRAWINGS.
ASME Y14.4M-2009, PICTORIAL DRAWINGS.
ASME Y14.5-2009, DIMENSIONS AND TOLERANCES.
ASME Y14.38-2007, ABBREVIATIONS AND ACRONYMS.
2. ALL DIMENSIONS ARE IN MILIMETERS.
3. MATERIAL: A.B.S. POLYLAC PA 765AMASS COLORED. COLOR: RAL5010. NO
TEXTURING OF THE PART (INDUSTRIAL POLISH).
4. INDICATES KEY INSPECTION DIMENSION.
5. REFER TO 3D MODEL FOR DIMENSIONS, GEOMETRY SURFACES AND FEATURES NOT
SHOWN OR DIMENSIONED ON DRAWING.
6. CERTIFICATION OF CONFORMANCE IS REQUIRED FOR LEAK TEST AND MATERIAL
SPECIFICATIONS.
7. GATES TO BE 0.0/+0.2.
8. FLASH NOT TO EXCEED 0.2, UNLESS OTHERWISE STATED.
10. HOLES TO BE FREE FROM FLASH.
11. UNLESS OTHERWISE STATED, DRAFT ANGLE IS 1 +0/-1 . 12. NOTES CONTINUED ON PAGE 4.

THE ASSEMBLY MUST NOT LEAK UNDER
A 200mBAR PRESSURE HELD FOR 5 SECONDS.

ALL PARTS TO BE INSPECTED.

GENERAL DIMENSIONAL TOLERANCES | PROPRIETARY & CONFIDENTIAL. THIS DOCUMENT MAY NOT BE COPIED, DISCLOSED, OR USED IN WHOLE OR IN PART WITHOUT THE CONSENT OF COVIDIEN.

DEC. X. +/- | DEC. DEC. DEC. .x +/-.xx +/-.xxx +/-

TITLE: CONICAL FITTING, INSPIRATORY MODULE, PB 560 | COVIDIEN 6135 Gunbarrel Avenue Boulder, CO 80301 © 2012 COVIDIEN ALL RIGHTS RESERVED.

SIZE B | FILENAME: 10079556.SLDDRW

DO NOT SCALE DRAWING | | REV B

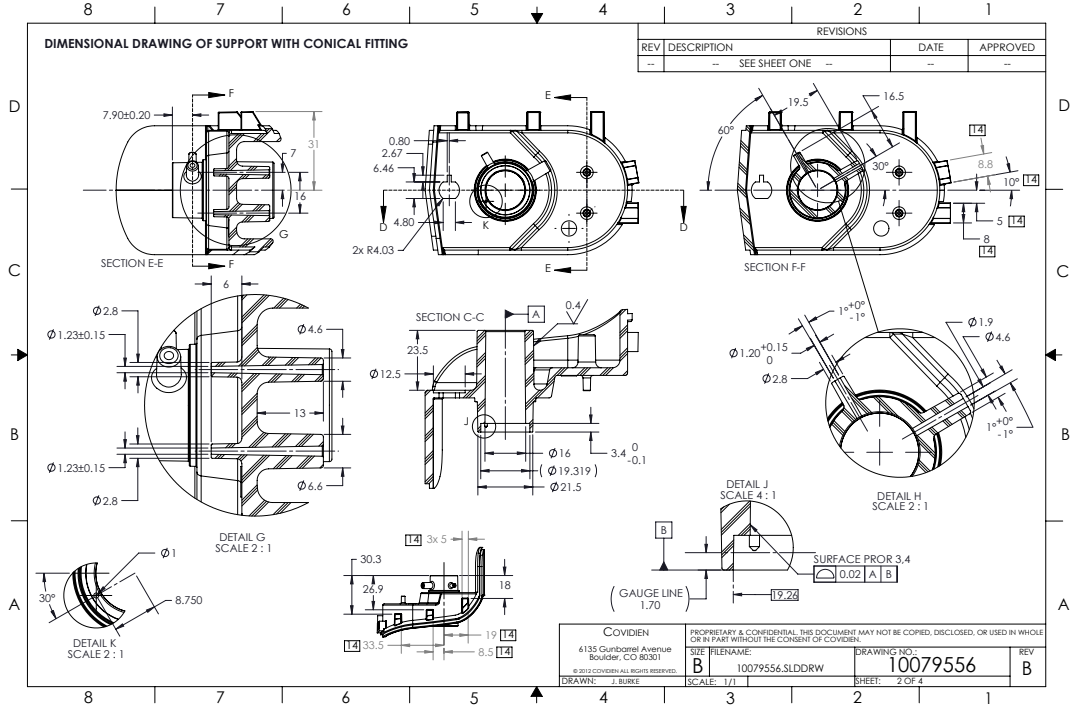
[picture p113: page 2]
SECTION C-C; SECTION E-E; SECTION F-F; DETAIL G SCALE 2 : 1; DETAIL H SCALE 2 : 1; GAUGE LINE; DETAIL J SCALE 4 : 1; SURFACE PROR 3,4; DETAIL K SCALE 2 : 1

DIMENSIONAL DRAWING OF SUPPORT WITH CONICAL FITTING

REV | DESCRIPTION | DATE | APPROVED
-- | --SEE SHEET ONE -- | -- | --

COVIDIEN 6135 Gunbarrel Avenue Boulder, CO 80301 © 2012 COVIDIEN ALL RIGHTS RESERVED. | PROPRIETARY & CONFIDENTIAL. THIS DOCUMENT MAY NOT BE COPIED, DISCLOSED, OR USED IN WHOLE OR IN PART WITHOUT THE CONSENT OF COVIDIEN.

SIZE | FILENAME: 10079556.SLDDRW | DRAWING NO.: | REV B

DRAWN: J. BURKE | SCALE: 1/1 | | SHEET: 2 OF 4

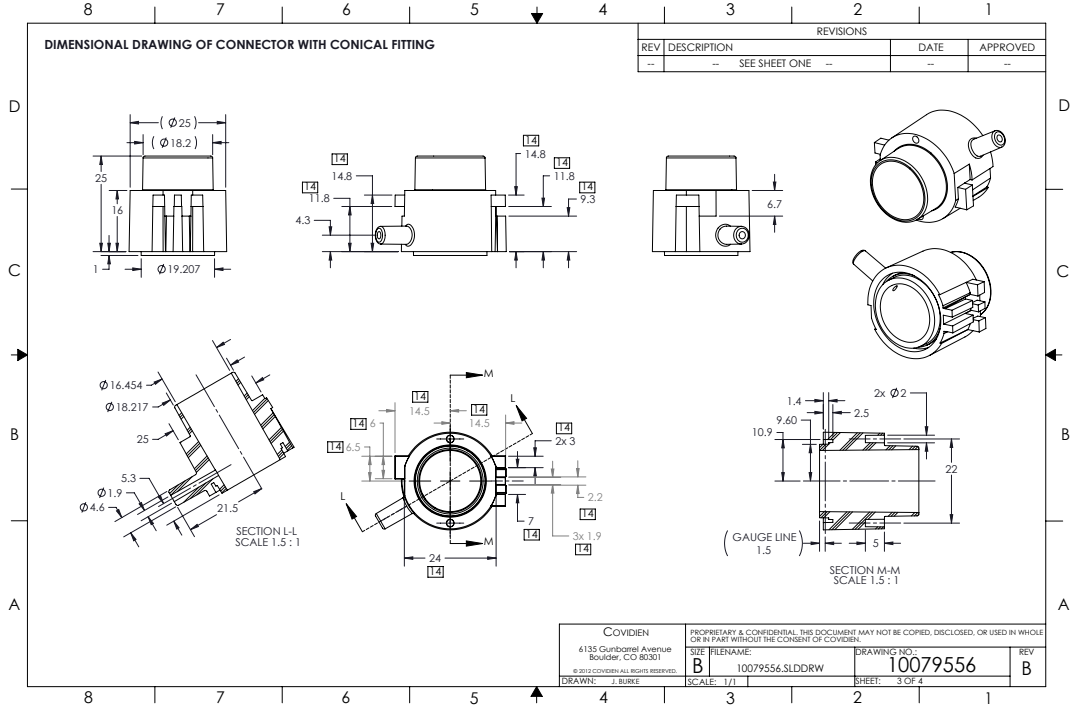
[picture p114: page 3]
SEE SHEET ONE --; GAUGE LINE; SECTION M-M SCALE 1.5 : 1; SECTION L-L SCALE 1.5 : 1

DIMENSIONAL DRAWING OF CONNECTOR WITH CONICAL FITTING

COVIDIEN 6135 Gunbarrel Avenue | PROPRIETARY & CONFIDENTIAL. THIS DOCUMENT MAY NOT BE COPIED, DISCLOSED, OR USED IN WHOLE OR IN PART WITHOUT THE CONSENT OF COVIDIEN.

SIZE | FILENAME: | DRAWING NO.: | REV

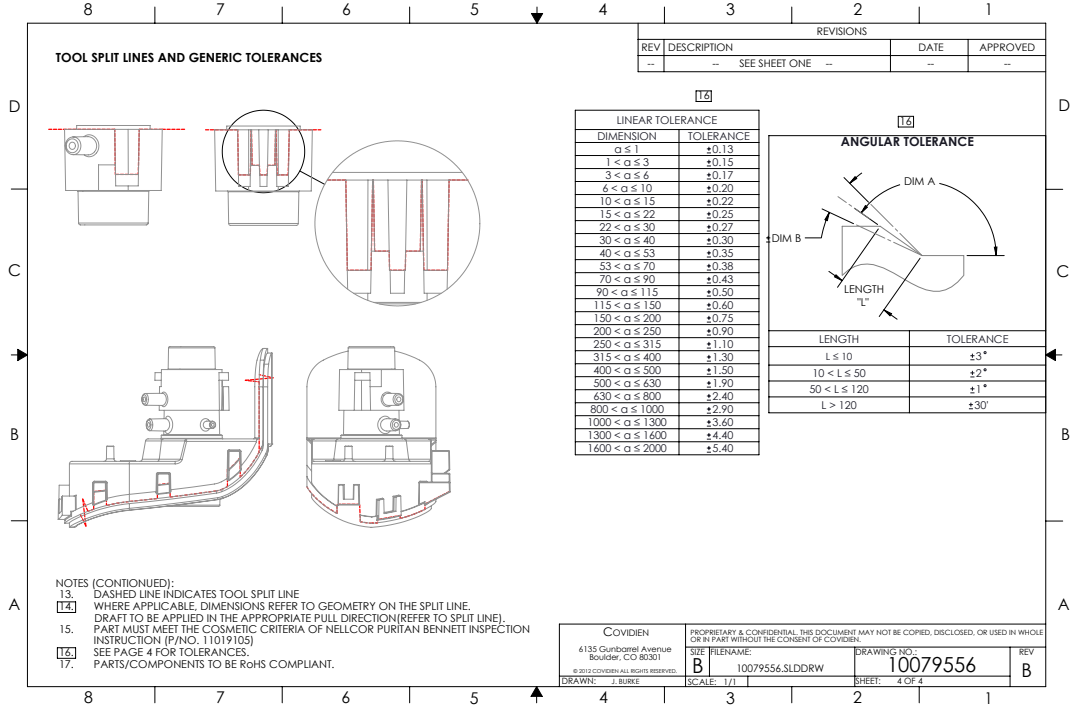
[picture p115: page 4]
DIM A; DIM B; SEE SHEET ONE --; LINEAR TOLERANCE; ANGULAR TOLERANCE

TOOL SPLIT LINES AND GENERIC TOLERANCES

NOTES (CONTIONUED):
13. DASHED LINE INDICATES TOOL SPLIT LINE

14. WHERE APPLICABLE, DIMENSIONS REFER TO GEOMETRY ON THE SPLIT LINE.
DRAFT TO BE APPLIED IN THE APPROPRIATE PULL DIRECTION(REFER TO SPLIT LINE).
15. PART MUST MEET THE COSMETIC CRITERIA OF NELLCOR PURITAN BENNETT INSPECTION
INSTRUCTION (P/NO. 11019105)
16. SEE PAGE 4 FOR TOLERANCES.
17. PARTS/COMPONENTS TO BE RoHS COMPLIANT.

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

SIZE | FILENAME: | DRAWING NO.: | REV
