nsynet/electronics_project2/Medtronic_PB560呼吸机开源资料(3D图纸_原理图_说明书_软件代码等)/medtronic-pb560-ventilator-system-file-set-2/Mechanical Part Drawings/3822800/3822800A00.PDF

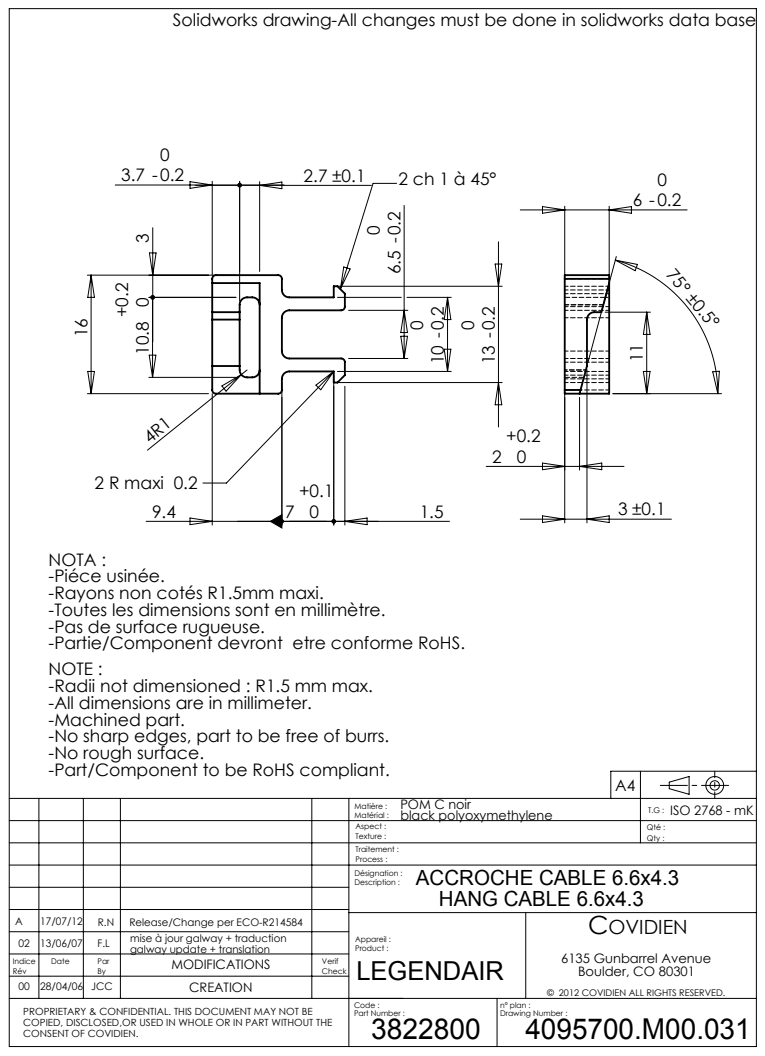
[picture p136: page 1]
6135 Gunbarrel Avenue Boulder, CO 80301; 2 R maxi 0.2; Texture :; Aspect :; ISO 2768 - mK; Qty :; Qté :; Process :; Drawing Number :; n° plan :; Part Number :; Product :; Description :; Matérial :; 17/07/12 R.N Release/Change per ECO-R214584; POM C noir; Code :; Appareil :; Désignation :; Traitement :; Matière :; ACCROCHE CABLE 6.6x4.3; black polyoxymethylene; HANG CABLE 6.6x4.3

Solidworks drawing-All changes must be done in solidworks data base

NOTA :
-Piéce usinée.
-Rayons non cotés R1.5mm maxi.
-Toutes les dimensions sont en millimètre.
-Pas de surface rugueuse.
-Partie/Component devront etre conforme RoHS.
NOTE :
-Radii not dimensioned : R1.5 mm max.
-All dimensions are in millimeter.
-Machined part.
-No sharp edges, part to be free of burrs.
-No rough surface.
-Part/Component to be RoHS compliant.

mise à jour galway + traduction 02 13/06/07 F.L
00 28/04/06 JCC
PROPRIETARY & CONFIDENTIAL. THIS DOCUMENT MAY NOT BE
COPIED, DISCLOSED,OR USED IN WHOLE OR IN PART WITHOUT THE
CONSENT OF COVIDIEN.

galway update + translation

© 2012 COVIDIEN ALL RIGHTS RESERVED.
