nsynet/electronics_project2/Medtronic_PB560呼吸机开源资料(3D图纸_原理图_说明书_软件代码等)/medtronic-pb560-ventilator-system-file-set-2/Mechanical Part Drawings/3823200/3823200B00.PDF

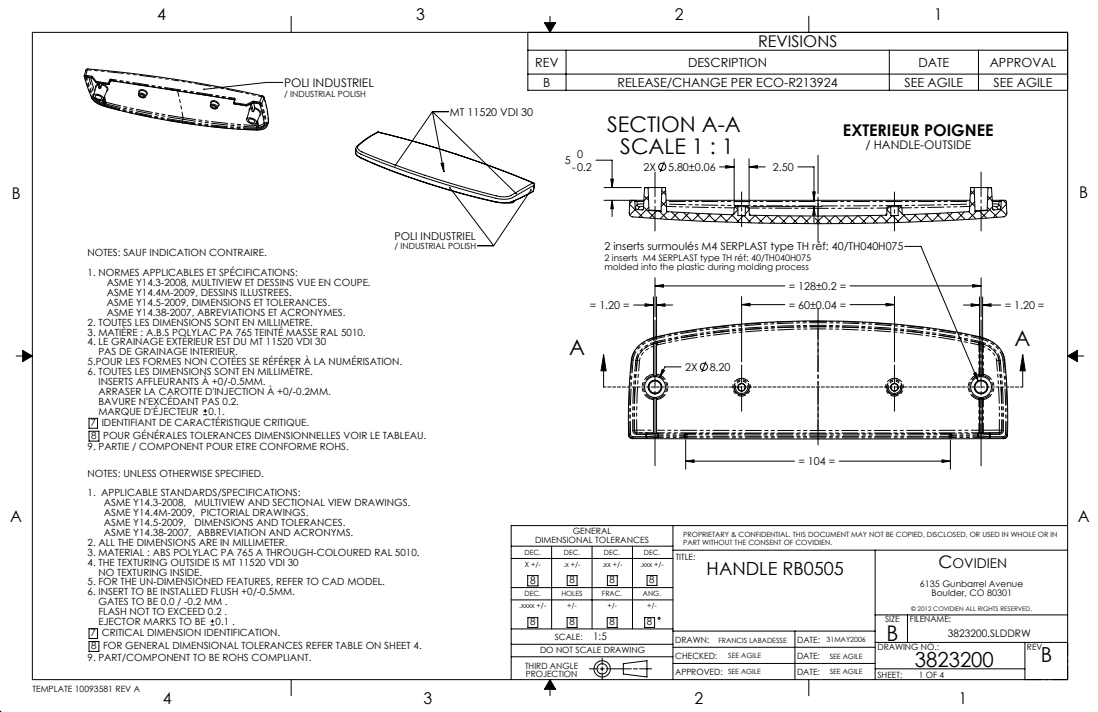
[picture p138: page 1]
SECTION A-A SCALE 1 : 1; POLI INDUSTRIEL / INDUSTRIAL POLISH; MT 11520 VDI 30; EXTERIEUR POIGNEE / HANDLE-OUTSIDE; MARQUE D'ÉJECTEUR; IDENTIFIANT DE CARACTÉRISTIQUE CRITIQUE.; POUR GÉNÉRALES TOLERANCES DIMENSIONNELLES VOIR LE TABLEAU.; EJECTOR MARKS TO BE; CRITICAL DIMENSION IDENTIFICATION.; FOR GENERAL DIMENSIONAL TOLERANCES REFER TABLE ON SHEET 4.; 2 TEMPLATE 10093581 REV A; .xxxx +/-; THIRD ANGLE; .xxx +/-; SHEET:; DATE:; DRAWING NO.:; DIMENSIONAL TOLERANCES

REVISIONS

REV | DESCRIPTION | DATE | APPROVAL
B | RELEASE/CHANGE PER ECO-R213924 | SEE AGILE | SEE AGILE

2 inserts surmoulés M4 SERPLAST type TH réf: 40/TH040H075
2 inserts M4 SERPLAST type TH réf: 40/TH040H075
molded into the plastic during molding process

NOTES: SAUF INDICATION CONTRAIRE.
1. NORMES APPLICABLES ET SPÉCIFICATIONS:
ASME Y14.3-2008, MULTIVIEW ET DESSINS VUE EN COUPE.
ASME Y14.4M-2009, DESSINS ILLUSTREES.
ASME Y14.5-2009, DIMENSIONS ET TOLERANCES.
ASME Y14.38-2007, ABREVIATIONS ET ACRONYMES.
2. TOUTES LES DIMENSIONS SONT EN MILLIMETRE.
3. MATIÈRE : A.B.S POLYLAC PA 765 TEINTÉ MASSE RAL 5010.
4. LE GRAINAGE EXTÉRIEUR EST DU MT 11520 VDI 30
PAS DE GRAINAGE INTERIEUR.
5.POUR LES FORMES NON COTÉES SE RÉFÉRER À LA NUMÉRISATION.
6. TOUTES LES DIMENSIONS SONT EN MILLIMÈTRE.
INSERTS AFFLEURANTS À +0/-0.5MM.
ARRASER LA CAROTTE D'INJECTION À +0/-0.2MM.
BAVURE N'EXCÉDANT PAS 0.2.
9. PARTIE / COMPONENT POUR ETRE CONFORME ROHS.

NOTES: UNLESS OTHERWISE SPECIFIED.
1. APPLICABLE STANDARDS/SPECIFICATIONS:
ASME Y14.3-2008, MULTIVIEW AND SECTIONAL VIEW DRAWINGS.
ASME Y14.4M-2009, PICTORIAL DRAWINGS.
ASME Y14.5-2009, DIMENSIONS AND TOLERANCES.
ASME Y14.38-2007, ABBREVIATION AND ACRONYMS.
2. ALL THE DIMENSIONS ARE IN MILLIMETER.
3. MATERIAL : ABS POLYLAC PA 765 A THROUGH-COLOURED RAL 5010.
4. THE TEXTURING OUTSIDE IS MT 11520 VDI 30
NO TEXTURING INSIDE.
5. FOR THE UN-DIMENSIONED FEATURES, REFER TO CAD MODEL.
6. INSERT TO BE INSTALLED FLUSH +0/-0.5MM.
GATES TO BE 0.0 / -0.2 MM .
FLASH NOT TO EXCEED 0.2 .
9. PART/COMPONENT TO BE ROHS COMPLIANT.

PROPRIETARY & CONFIDENTIAL. THIS DOCUMENT MAY NOT BE COPIED, DISCLOSED, OR USED IN WHOLE OR IN
PART WITHOUT THE CONSENT OF COVIDIEN.

TITLE: HANDLE RB0505 | COVIDIEN 6135 Gunbarrel Avenue Boulder, CO 80301 © 2012 COVIDIEN ALL RIGHTS RESERVED. B 8

SIZE | FILENAME: 3823200.SLDDRW

1:5 SCALE: | DRAWN: FRANCIS LABADESSE CHECKED: SEE AGILE APPROVED: SEE AGILE | 31MAY2006 DATE: SEE AGILE DATE: SEE AGILE
DO NOT SCALE DRAWING | | | 3823200 | REV B

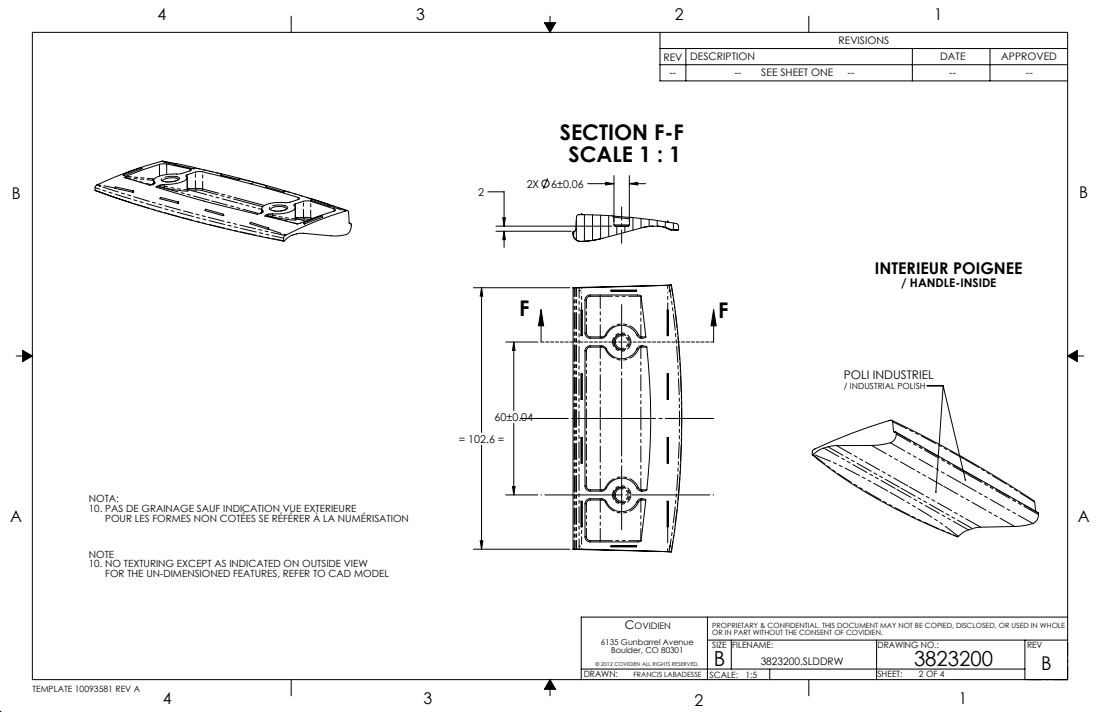
[picture p139: page 2]
SECTION F-F SCALE 1 : 1; POLI INDUSTRIEL / INDUSTRIAL POLISH; INTERIEUR POIGNEE / HANDLE-INSIDE; TEMPLATE 10093581 REV A

REV | DESCRIPTION | DATE | APPROVED
-- | --SEE SHEET ONE -- | -- | --

NOTA:
10. PAS DE GRAINAGE SAUF INDICATION VUE EXTERIEURE
POUR LES FORMES NON COTÉES SE RÉFÉRER À LA NUMÉRISATION

NOTE
10. NO TEXTURING EXCEPT AS INDICATED ON OUTSIDE VIEW
FOR THE UN-DIMENSIONED FEATURES, REFER TO CAD MODEL

COVIDIEN 6135 Gunbarrel Avenue Boulder, CO 80301 © 2012 COVIDIEN ALL RIGHTS RESERVED. | PROPRIETARY & CONFIDENTIAL. THIS DOCUMENT MAY NOT BE COPIED, DISCLOSED, OR USED IN WHOLE OR IN PART WITHOUT THE CONSENT OF COVIDIEN.

SIZE B | FILENAME: 3823200.SLDDRW | DRAWING NO.: 3823200 | REV B

DRAWN: FRANCIS LABADESSE | SCALE: 1:5 | | SHEET: 2 OF 4

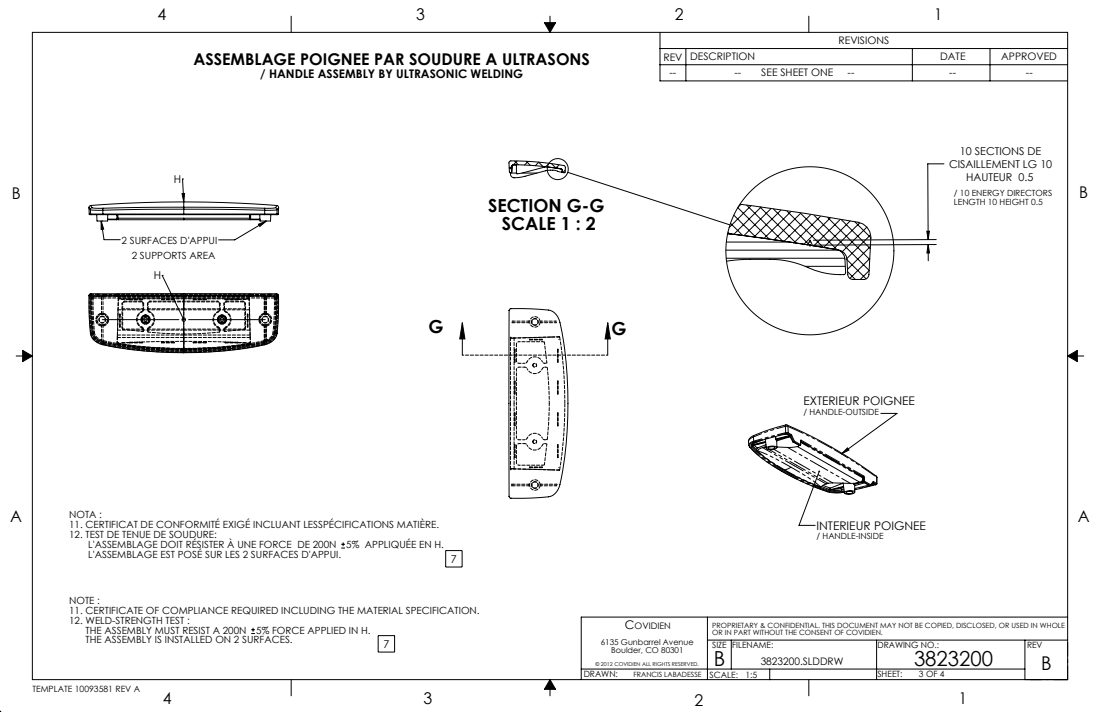
[picture p140: page 3]
SECTION G-G SCALE 1 : 2; HAUTEUR 0.5; 10 SECTIONS DE CISAILLEMENT LG 10; / 10 ENERGY DIRECTORS LENGTH 10 HEIGHT 0.5; EXTERIEUR POIGNEE / HANDLE-OUTSIDE; INTERIEUR POIGNEE / HANDLE-INSIDE; 2 SURFACES D'APPUI 2 SUPPORTS AREA; THE ASSEMBLY MUST RESIST A 200N; 5% FORCE APPLIED IN H.; L'ASSEMBLAGE DOIT RÉSISTER À UNE FORCE DE 200N; 5% APPLIQUÉE EN H.; L'ASSEMBLAGE EST POSÉ SUR LES 2 SURFACES D'APPUI.; SEE SHEET ONE --

ASSEMBLAGE POIGNEE PAR SOUDURE A ULTRASONS

/ HANDLE ASSEMBLY BY ULTRASONIC WELDING

NOTA :
11. CERTIFICAT DE CONFORMITÉ EXIGÉ INCLUANT LESSPÉCIFICATIONS MATIÈRE.
12. TEST DE TENUE DE SOUDURE:

NOTE :
11. CERTIFICATE OF COMPLIANCE REQUIRED INCLUDING THE MATERIAL SPECIFICATION.
12. WELD-STRENGTH TEST :
THE ASSEMBLY IS INSTALLED ON 2 SURFACES.

COVIDIEN 6135 Gunbarrel Avenue Boulder, CO 80301 | PROPRIETARY & CONFIDENTIAL. THIS DOCUMENT MAY NOT BE COPIED, DISCLOSED, OR USED IN WHOLE OR IN PART WITHOUT THE CONSENT OF COVIDIEN.

SIZE B | FILENAME: | DRAWING NO.: 3823200 | REV

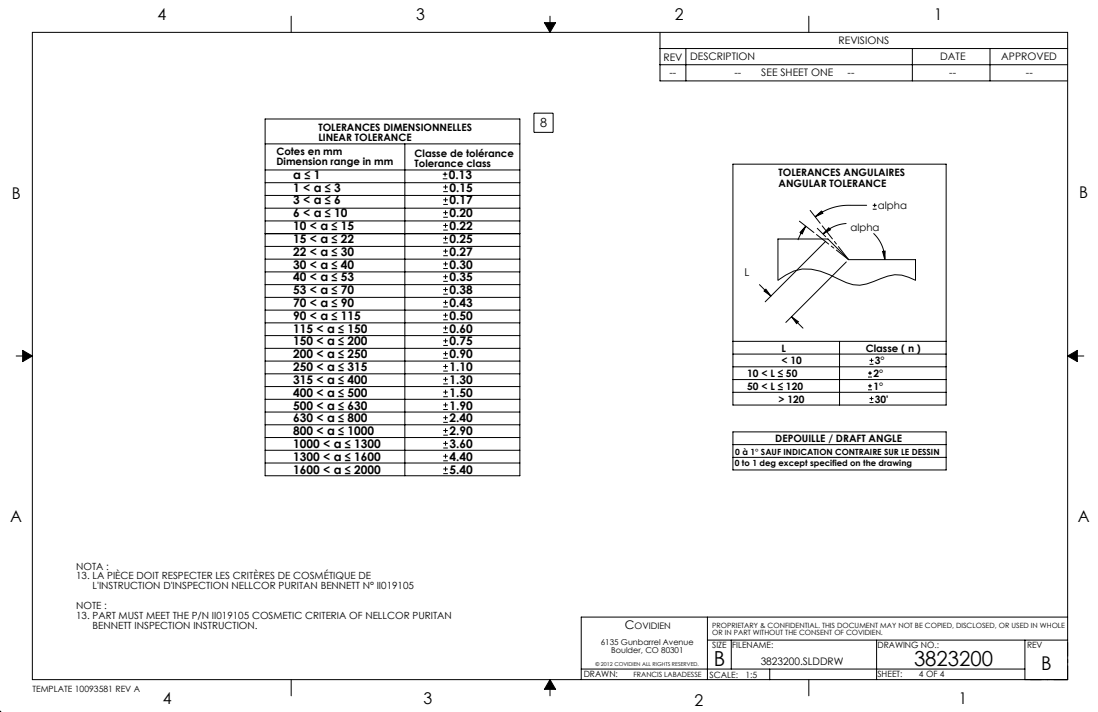
[picture p141: page 4]
L Classe ( n ); TOLERANCES ANGULAIRES ANGULAR TOLERANCE; SEE SHEET ONE --

TOLERANCES DIMENSIONNELLES
LINEAR TOLERANCE
Cotes en mm
Dimension range in mm

Classe de tolérance
Tolerance class

DEPOUILLE / DRAFT ANGLE

0 à 1° SAUF INDICATION CONTRAIRE SUR LE DESSIN
0 to 1 deg except specified on the drawing

NOTA :
13. LA PIÈCE DOIT RESPECTER LES CRITÈRES DE COSMÉTIQUE DE
L'INSTRUCTION D'INSPECTION NELLCOR PURITAN BENNETT N° II019105
NOTE :
13. PART MUST MEET THE P/N II019105 COSMETIC CRITERIA OF NELLCOR PURITAN
BENNETT INSPECTION INSTRUCTION.

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

SIZE B | FILENAME: | DRAWING NO.: 3823200 | REV
