nsynet/electronics_project2/Medtronic_PB560呼吸机开源资料(3D图纸_原理图_说明书_软件代码等)/medtronic-pb560-ventilator-system-file-set-2/Mechanical Part Drawings/3827900/3827900B00.PDF

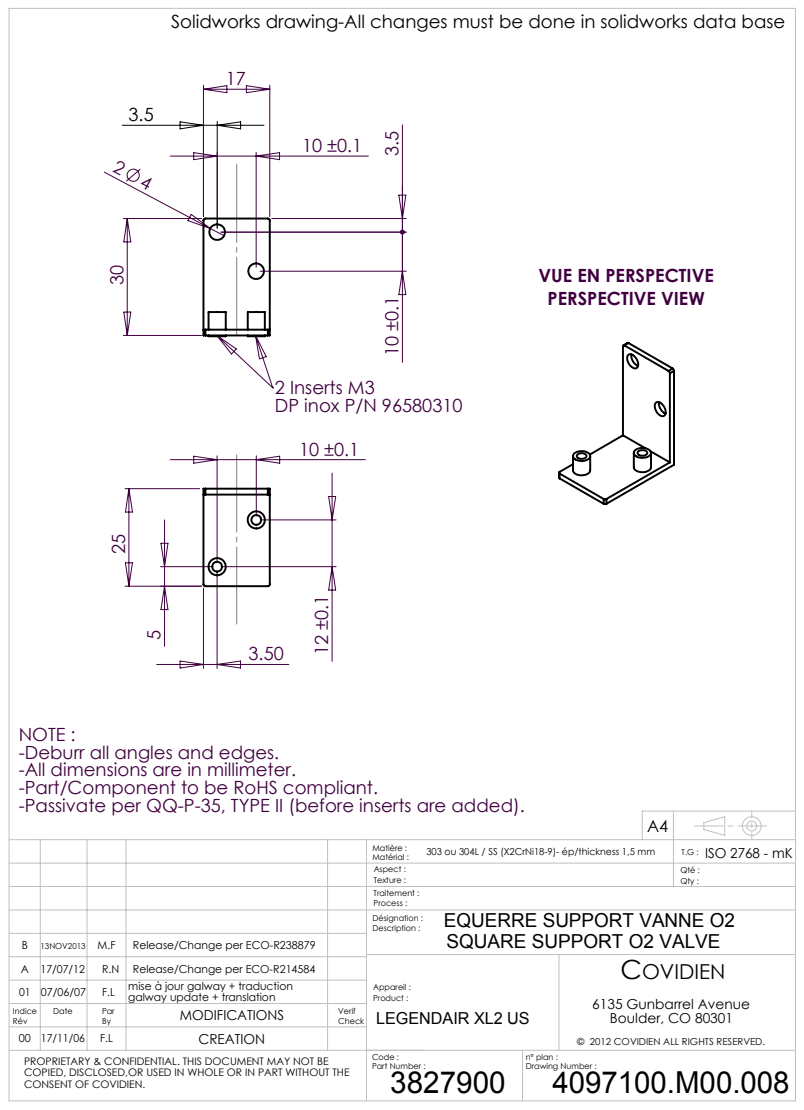
[picture p153: page 1]
6135 Gunbarrel Avenue Boulder, CO 80301; 2 Inserts M3 DP inox P/N 96580310 10 ±0.1 12 ±0.1; EQUERRE SUPPORT VANNE O2; LEGENDAIR XL2 US; Matière :; Traitement :; Désignation :; Appareil :; Code :; Matérial :; Description :; Product :; Part Number :; n° plan : Drawing Number :; Process :; Qté : Qty :; ISO 2768 - mK; Aspect : Texture :; Release/Change per ECO-R238879; SQUARE SUPPORT O2 VALVE

Solidworks drawing-All changes must be done in solidworks data base

VUE EN PERSPECTIVE
PERSPECTIVE VIEW

NOTE :
-Deburr all angles and edges.
-All dimensions are in millimeter.
-Part/Component to be RoHS compliant.
-Passivate per QQ-P-35, TYPE II (before inserts are added).

303 ou 304L / SS (X2CrNi18-9)- ép/thickness 1,5 mm

B 13NOV2013 M.F
01 07/06/07 F.L mise à jour galway + traduction
PROPRIETARY & CONFIDENTIAL. THIS DOCUMENT MAY NOT BE
COPIED, DISCLOSED,OR USED IN WHOLE OR IN PART WITHOUT THE
CONSENT OF COVIDIEN.

Release/Change per ECO-R214584
galway update + translation
Par

© 2012 COVIDIEN ALL RIGHTS RESERVED.
