nsynet/electronics_project2/Medtronic_PB560呼吸机开源资料(3D图纸_原理图_说明书_软件代码等)/medtronic-pb560-ventilator-system-file-set-2/Mechanical Part Drawings/3829000/3829000C00.PDF

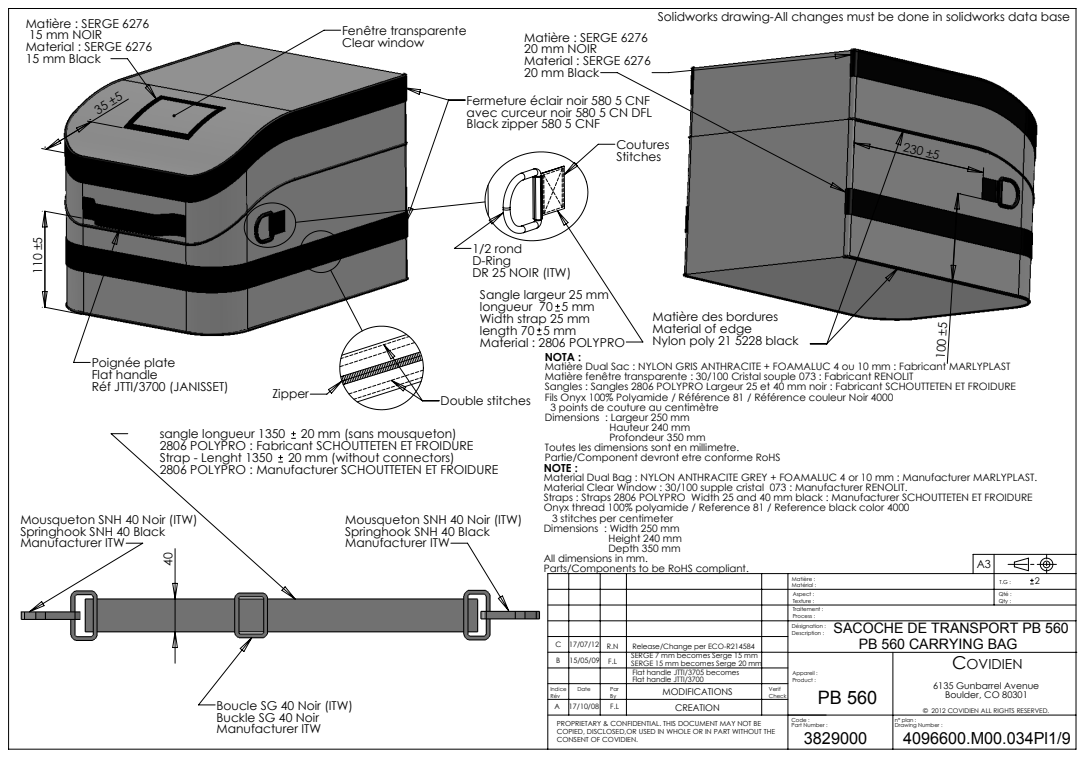
[picture p154: page 1]
Matière : SERGE 6276 15 mm NOIR Material : SERGE 6276 15 mm Black; Fenêtre transparente Clear window; Matière : SERGE 6276 20 mm NOIR Material : SERGE 6276 20 mm Black; sangle longueur 1350; 20 mm (sans mousqueton); Strap - Lenght 1350; 20 mm (without connectors); longueur 70; length 70; Height 240 mm Depth 350 mm; Hauteur 240 mm Profondeur 350 mm; Désignation :; Release/Change per ECO-R214584; Description :; Qté : Qty :

Solidworks drawing-All changes must be done in solidworks data base

Fermeture éclair noir 580 5 CNF
avec curceur noir 580 5 CN DFL
Black zipper 580 5 CNF

1/2 rond
D-Ring
DR 25 NOIR (ITW)
Sangle largeur 25 mm
Width strap 25 mm
Material : 2806 POLYPRO

Matière des bordures
Material of edge
Nylon poly 21 5228 black

NOTA :
Matière Dual Sac : NYLON GRIS ANTHRACITE + FOAMALUC 4 ou 10 mm : Fabricant MARLYPLAST
Matière fenêtre transparente : 30/100 Cristal souple 073 : Fabricant RENOLIT
Sangles : Sangles 2806 POLYPRO Largeur 25 et 40 mm noir : Fabricant SCHOUTTETEN ET FROIDURE
Fils Onyx 100% Polyamide / Référence 81 / Référence couleur Noir 4000
3 points de couture au centimètre
Dimensions : Largeur 250 mm

Poignée plate
Flat handle
Réf JTTI/3700 (JANISSET)

Double stitches Zipper

2806 POLYPRO : Fabricant SCHOUTTETEN ET FROIDURE
2806 POLYPRO : Manufacturer SCHOUTTETEN ET FROIDURE

Toutes les dimensions sont en millimetre.
Partie/Component devront etre conforme RoHS
NOTE :
Material Dual Bag : NYLON ANTHRACITE GREY + FOAMALUC 4 or 10 mm : Manufacturer MARLYPLAST.
Material Clear Window : 30/100 supple cristal 073 : Manufacturer RENOLIT.
Straps : Straps 2806 POLYPRO Width 25 and 40 mm black : Manufacturer SCHOUTTETEN ET FROIDURE
Onyx thread 100% polyamide / Reference 81 / Reference black color 4000
3 stitches per centimeter
Dimensions : Width 250 mm

Mousqueton SNH 40 Noir (ITW)
Springhook SNH 40 Black
Manufacturer ITW

All dimensions in mm.
Parts/Components to be RoHS compliant.

Matière :
Matérial :
Aspect :
Texture :
Traitement :
Process :
SACOCHE DE TRANSPORT PB 560
PB 560 CARRYING BAG

SERGE 7 mm becomes Serge 15 mm
SERGE 15 mm becomes Serge 20 mm
Flat handle JTTI/3705 becomes
Flat handle JTTI/3700
Par

Appareil : Product : PB 560 | COVIDIEN 6135 Gunbarrel Avenue Boulder, CO 80301 © 2012 COVIDIEN ALL RIGHTS RESERVED.

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

Boucle SG 40 Noir (ITW)
Buckle SG 40 Noir

Code : Part Number : 3829000 | n° plan : Drawing Number : 4096600.M00.034Pl1/9

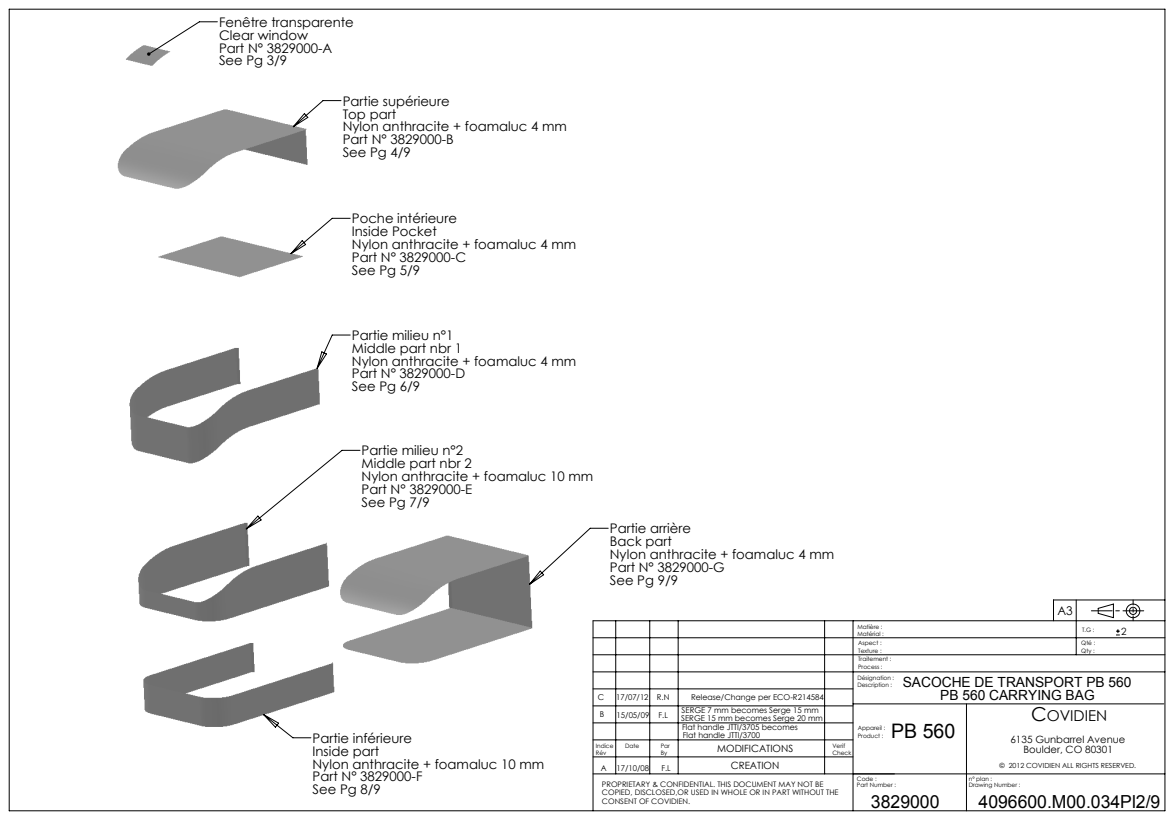
[picture p155: page 2]
6135 Gunbarrel Avenue Boulder, CO 80301; Fenêtre transparente Clear window Part N° 3829000-A See Pg 3/9; Désignation :; Appareil :; Release/Change per ECO-R214584; Description :; Product :; Qté : Qty :

Partie supérieure
Top part
Nylon anthracite + foamaluc 4 mm
Part N° 3829000-B
See Pg 4/9

Poche intérieure
Inside Pocket
Part N° 3829000-C
See Pg 5/9

Partie milieu n°1
Middle part nbr 1
Part N° 3829000-D
See Pg 6/9

Partie milieu n°2
Middle part nbr 2
Nylon anthracite + foamaluc 10 mm
Part N° 3829000-E
See Pg 7/9

Partie arrière
Back part
Part N° 3829000-G
See Pg 9/9

Matière :
Matérial :
Aspect :
Texture :
Traitement :
Process :
SACOCHE DE TRANSPORT PB 560
PB 560 CARRYING BAG

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

Partie inférieure
Inside part
Part N° 3829000-F
See Pg 8/9

© 2012 COVIDIEN ALL RIGHTS RESERVED.

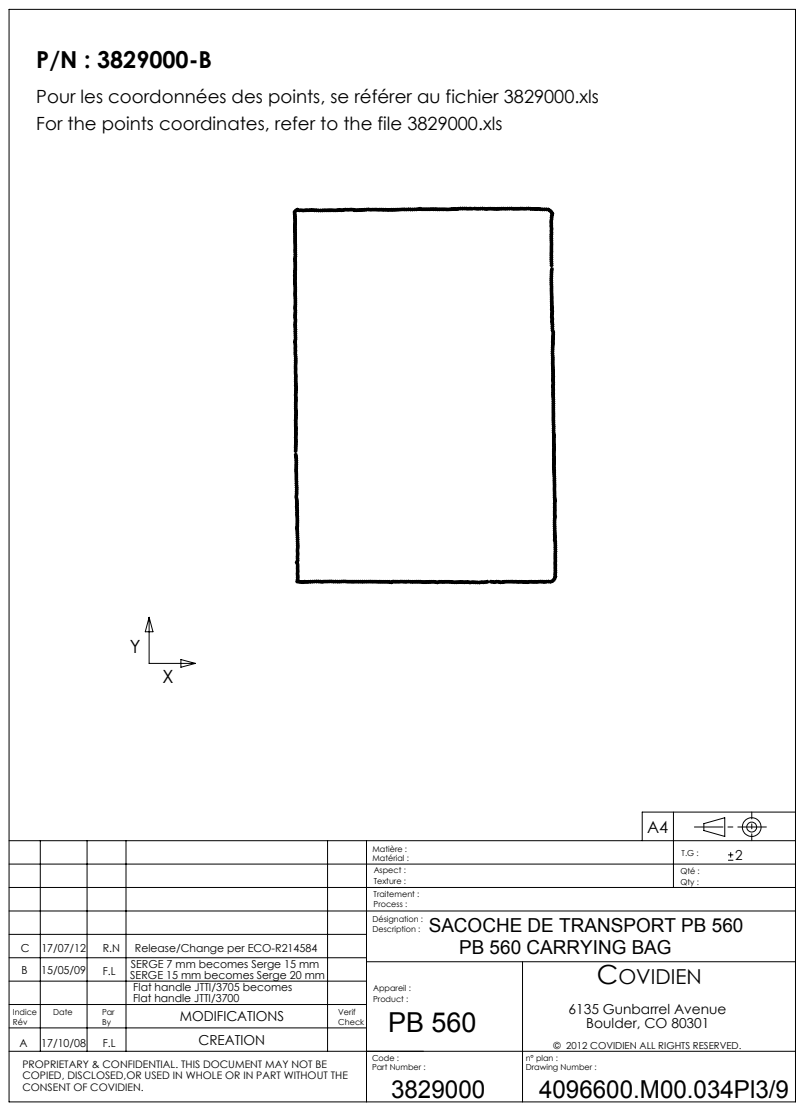
[picture p156: page 3]
6135 Gunbarrel Avenue Boulder, CO 80301; Désignation :; Appareil :; Description :; Product :; Qté : Qty :

Pour les coordonnées des points, se référer au fichier 3829000.xls
For the points coordinates, refer to the file 3829000.xls

Matière :
Matérial :
Aspect :
Texture :
Traitement :
Process :
SACOCHE DE TRANSPORT PB 560
PB 560 CARRYING BAG

C 17/07/12 R.N Release/Change per ECO-R214584

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

© 2012 COVIDIEN ALL RIGHTS RESERVED.

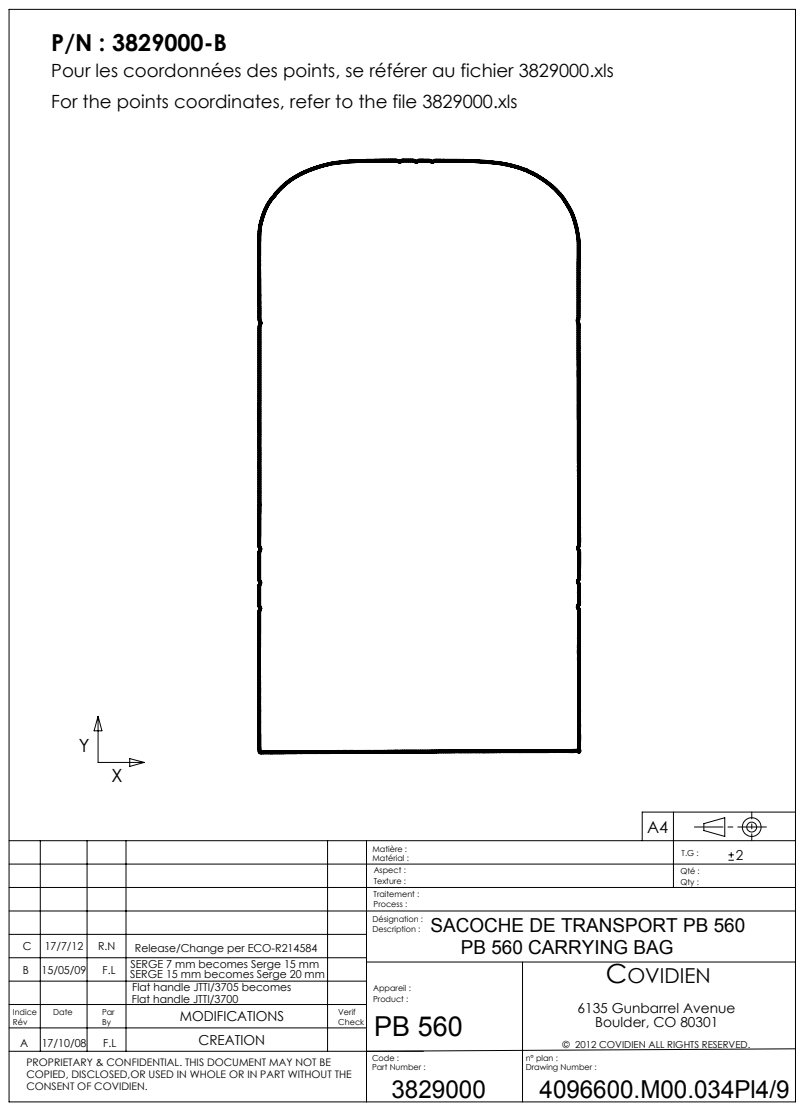
[picture p157: page 4]
6135 Gunbarrel Avenue Boulder, CO 80301; Désignation :; Appareil :; Release/Change per ECO-R214584; Description :; Product :; Qté : Qty :

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

Matière :
Matérial :
Aspect :
Texture :
Traitement :
Process :
SACOCHE DE TRANSPORT PB 560
PB 560 CARRYING BAG

SERGE 7 mm becomes Serge 15 mm B 15/05/09 F.L

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

© 2012 COVIDIEN ALL RIGHTS RESERVED.

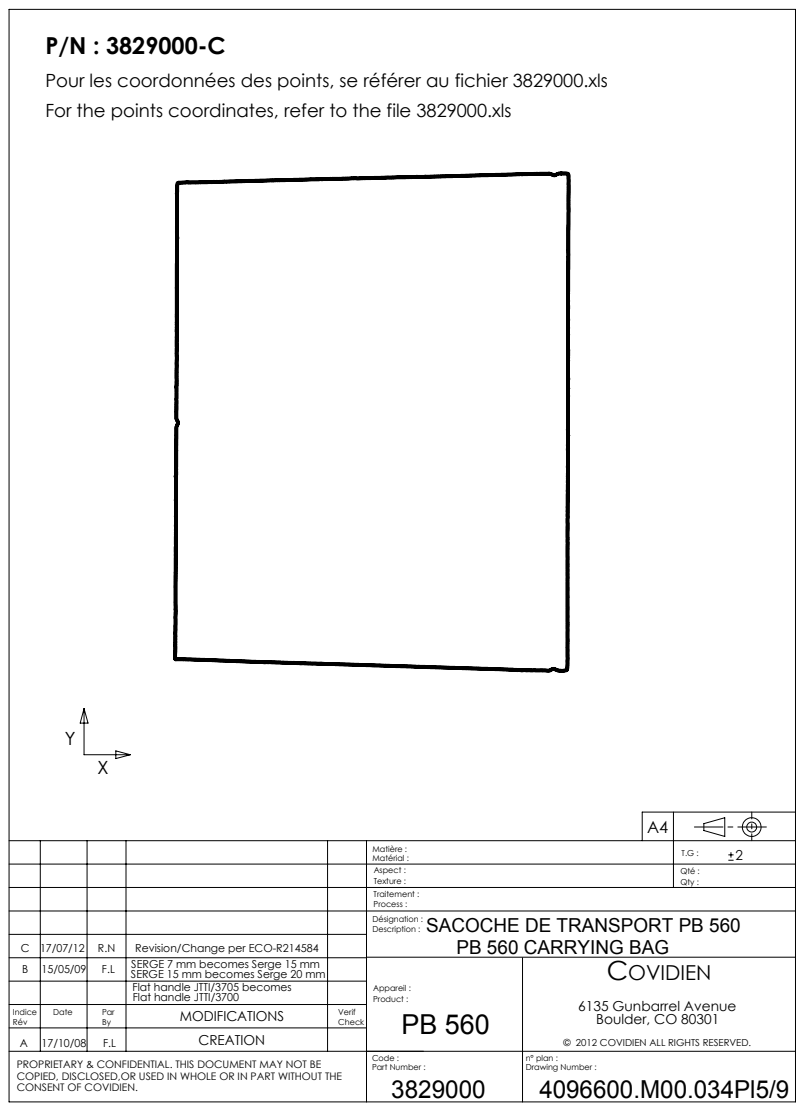
[picture p158: page 5]
6135 Gunbarrel Avenue Boulder, CO 80301; Désignation :; Appareil :; Revision/Change per ECO-R214584; Description :; Product :; Qté : Qty :

For the points coordinates, refer to the file 3829000.xls

Matière :
Matérial :
Aspect :
Texture :
Traitement :
Process :
SACOCHE DE TRANSPORT PB 560
PB 560 CARRYING BAG

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

© 2012 COVIDIEN ALL RIGHTS RESERVED.

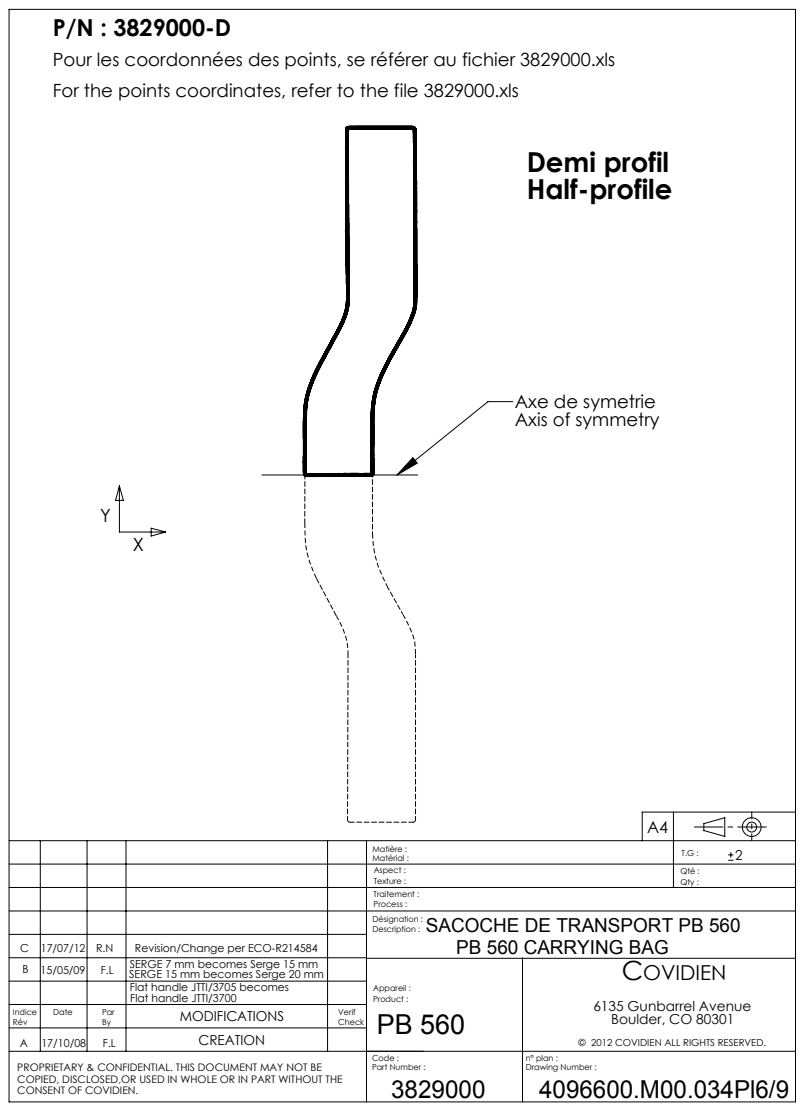
[picture p159: page 6]
6135 Gunbarrel Avenue Boulder, CO 80301; Demi profil; Désignation :; Appareil :; Description :; Product :; Qté : Qty :

For the points coordinates, refer to the file 3829000.xls

Axe de symetrie
Axis of symmetry

Matière :
Matérial :
Aspect :
Texture :
Traitement :
Process :
SACOCHE DE TRANSPORT PB 560
PB 560 CARRYING BAG

Revision/Change per ECO-R214584
SERGE 7 mm becomes Serge 15 mm
SERGE 15 mm becomes Serge 20 mm
Flat handle JTTI/3705 becomes
Flat handle JTTI/3700
Par

© 2012 COVIDIEN ALL RIGHTS RESERVED.

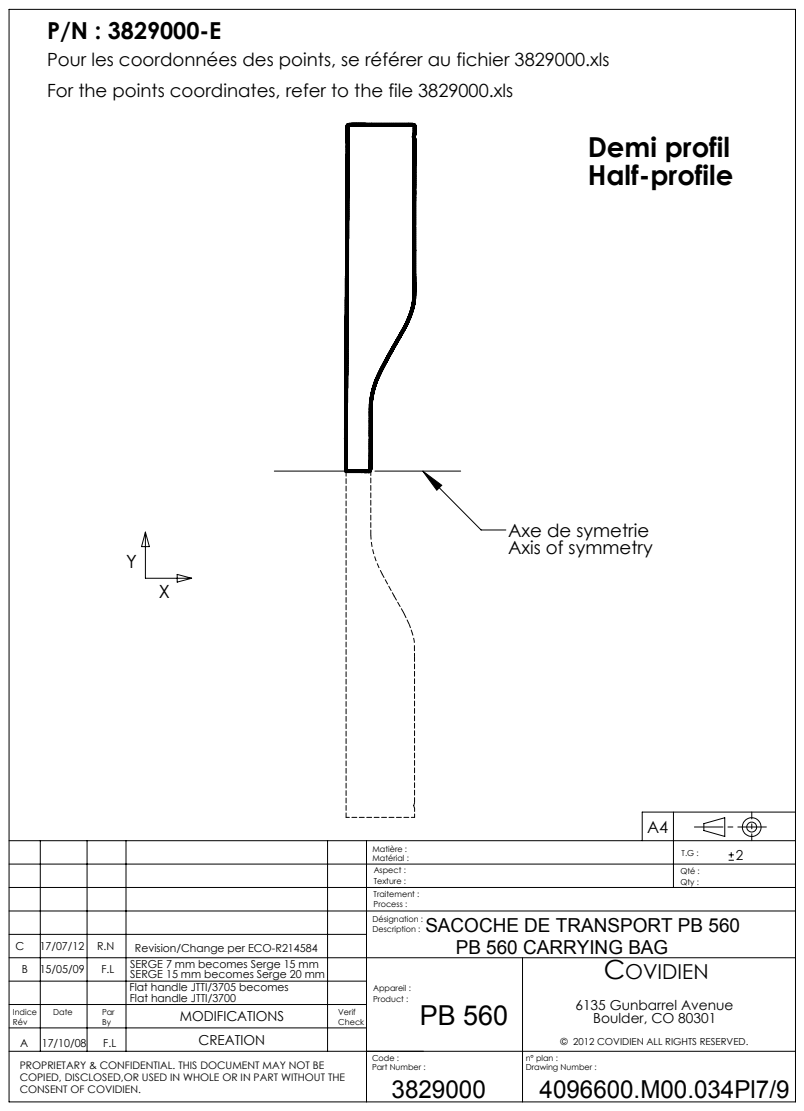
[picture p160: page 7]
6135 Gunbarrel Avenue Boulder, CO 80301; Demi profil; Désignation :; Appareil :; Revision/Change per ECO-R214584; Description :; Product :; Qté : Qty :

For the points coordinates, refer to the file 3829000.xls

Axe de symetrie
Axis of symmetry

Matière :
Matérial :
Aspect :
Texture :
Traitement :
Process :
SACOCHE DE TRANSPORT PB 560
PB 560 CARRYING BAG

SERGE 7 mm becomes Serge 15 mm B 15/05/09 F.L

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

© 2012 COVIDIEN ALL RIGHTS RESERVED.

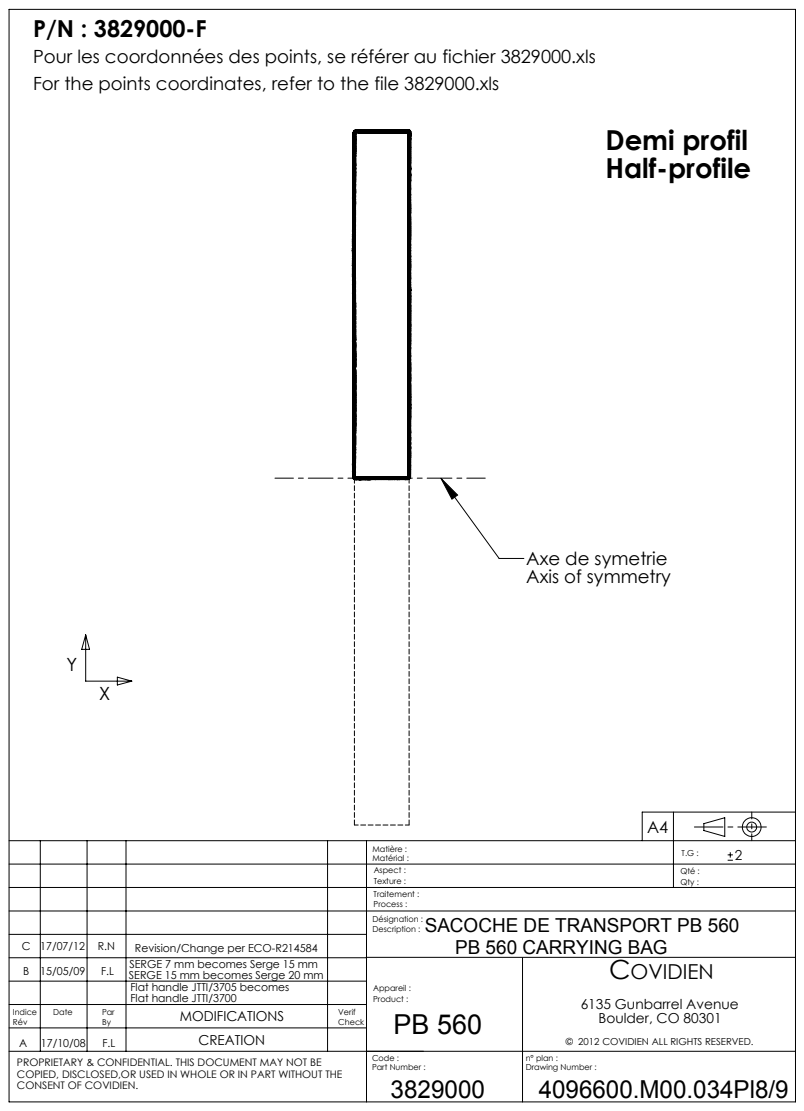
[picture p161: page 8]
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

For the points coordinates, refer to the file 3829000.xls

Axe de symetrie
Axis of symmetry

Matière :
Matérial :
Aspect :
Texture :
Traitement :
Process :
SACOCHE DE TRANSPORT PB 560
PB 560 CARRYING BAG

SERGE 7 mm becomes Serge 15 mm B 15/05/09 F.L

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

© 2012 COVIDIEN ALL RIGHTS RESERVED.

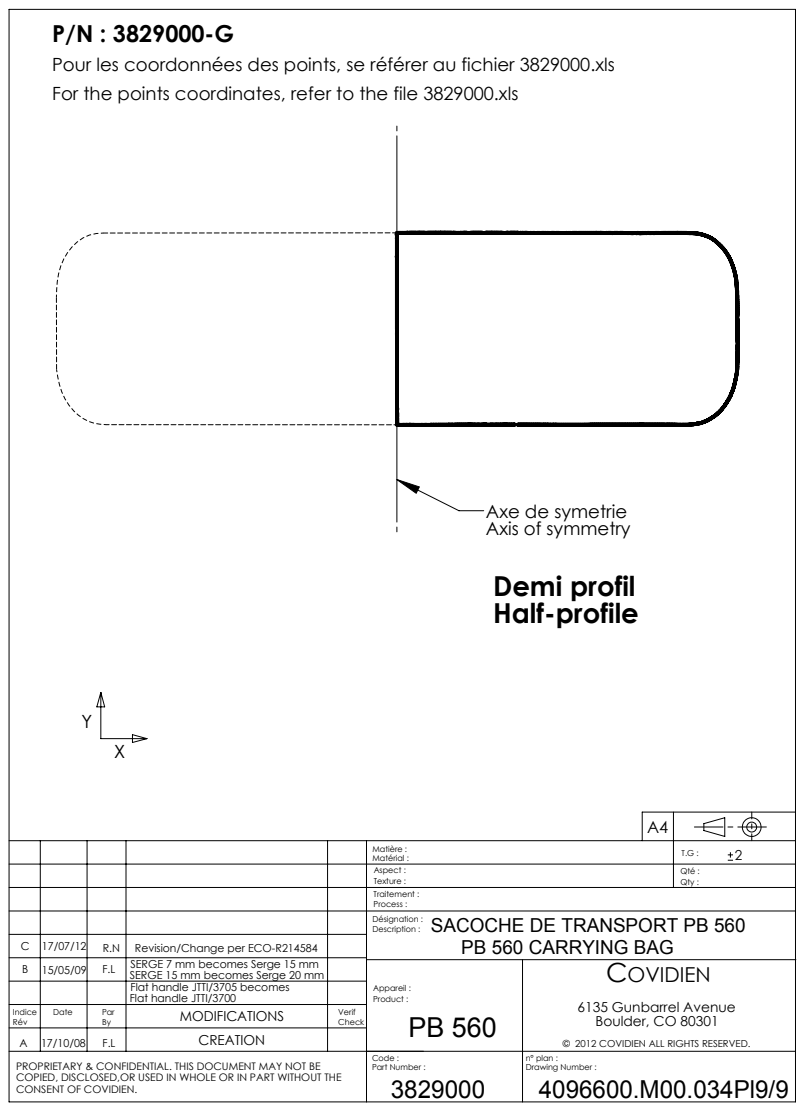
[picture p162: page 9]
6135 Gunbarrel Avenue Boulder, CO 80301; Désignation :; Appareil :; Description :; Product :; Qté : Qty :

For the points coordinates, refer to the file 3829000.xls

Axe de symetrie
Axis of symmetry
Demi profil
Half-profile

Matière :
Matérial :
Aspect :
Texture :
Traitement :
Process :
SACOCHE DE TRANSPORT PB 560
PB 560 CARRYING BAG

C 17/07/12 R.N Revision/Change per ECO-R214584

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

© 2012 COVIDIEN ALL RIGHTS RESERVED.
