nsynet/electronics_project2/Medtronic_PB560呼吸机开源资料(3D图纸_原理图_说明书_软件代码等)/medtronic-pb560-ventilator-system-file-set-2/Electronic PCBAs/10096315_Blower_Driver_PCBA/PCBA/10096315A00.PDF

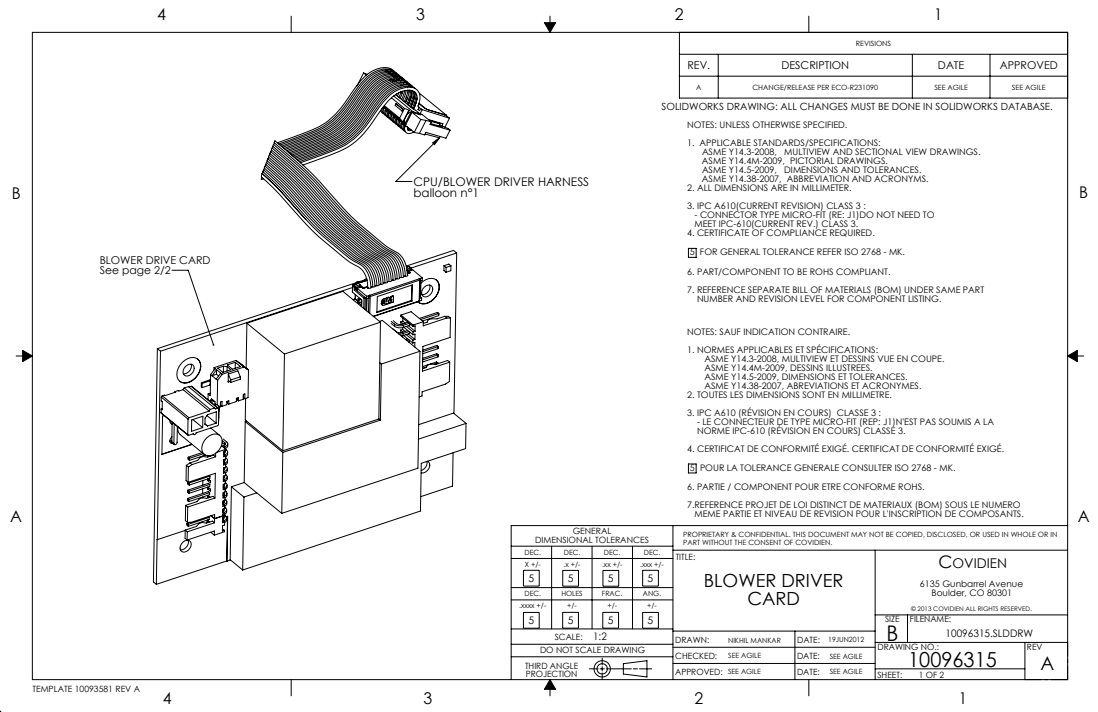
[picture p163: page 1]
POUR LA TOLERANCE GENERALE CONSULTER ISO 2768 - MK.; FOR GENERAL TOLERANCE REFER ISO 2768 - MK.; 2 TEMPLATE 10093581 REV A; .xxxx +/-; THIRD ANGLE; .xxx +/-; SHEET:; DATE:; DRAWING NO.:; DIMENSIONAL TOLERANCES

REVISIONS

REV. | DESCRIPTION | DATE | APPROVED

A | CHANGE/RELEASE PER ECO-R231090 | SEE AGILE | SEE AGILE

SOLIDWORKS DRAWING: ALL CHANGES MUST BE DONE IN SOLIDWORKS DATABASE.
NOTES: UNLESS OTHERWISE SPECIFIED.
1. APPLICABLE STANDARDS/SPECIFICATIONS:
ASME Y14.3-2008, MULTIVIEW AND SECTIONAL VIEW DRAWINGS.
ASME Y14.4M-2009, PICTORIAL DRAWINGS.
ASME Y14.5-2009, DIMENSIONS AND TOLERANCES.
ASME Y14.38-2007, ABBREVIATION AND ACRONYMS.
2. ALL DIMENSIONS ARE IN MILLIMETER.
3. IPC A610(CURRENT REVISION) CLASS 3 :
- CONNECTOR TYPE MICRO-FIT (RE: J1)DO NOT NEED TO
MEET IPC-610(CURRENT REV.) CLASS 3.
4. CERTIFICATE OF COMPLIANCE REQUIRED.
6. PART/COMPONENT TO BE ROHS COMPLIANT.
7. REFERENCE SEPARATE BILL OF MATERIALS (BOM) UNDER SAME PART
NUMBER AND REVISION LEVEL FOR COMPONENT LISTING.

CPU/BLOWER DRIVER HARNESS
balloon n°1

BLOWER DRIVE CARD
See page 2/2

NOTES: SAUF INDICATION CONTRAIRE.
1. NORMES APPLICABLES ET SPÉCIFICATIONS:
ASME Y14.3-2008, MULTIVIEW ET DESSINS VUE EN COUPE.
ASME Y14.4M-2009, DESSINS ILLUSTREES.
ASME Y14.5-2009, DIMENSIONS ET TOLERANCES.
ASME Y14.38-2007, ABREVIATIONS ET ACRONYMES.
2. TOUTES LES DIMENSIONS SONT EN MILLIMETRE.
3. IPC A610 (RÉVISION EN COURS) CLASSE 3 :
- LE CONNECTEUR DE TYPE MICRO-FIT (REP: J1)N'EST PAS SOUMIS A LA
NORME IPC-610 (RÉVISION EN COURS) CLASSE 3.
4. CERTIFICAT DE CONFORMITÉ EXIGÉ. CERTIFICAT DE CONFORMITÉ EXIGÉ.
6. PARTIE / COMPONENT POUR ETRE CONFORME ROHS.
7.REFERENCE PROJET DE LOI DISTINCT DE MATERIAUX (BOM) SOUS LE NUMERO
MEME PARTIE ET NIVEAU DE REVISION POUR L'INSCRIPTION DE COMPOSANTS.

PROPRIETARY & CONFIDENTIAL. THIS DOCUMENT MAY NOT BE COPIED, DISCLOSED, OR USED IN WHOLE OR IN
PART WITHOUT THE CONSENT OF COVIDIEN.

TITLE: BLOWER DRIVER CARD | COVIDIEN 6135 Gunbarrel Avenue Boulder, CO 80301 © 2013 COVIDIEN ALL RIGHTS RESERVED.

SIZE B | FILENAME: 10096315.SLDDRW

1:2 SCALE: | DRAWN: NIKHIL MANKAR CHECKED: SEE AGILE APPROVED: SEE AGILE | 19JUN2012 DATE: SEE AGILE DATE: SEE AGILE
DO NOT SCALE DRAWING | | | 10096315 | REV A

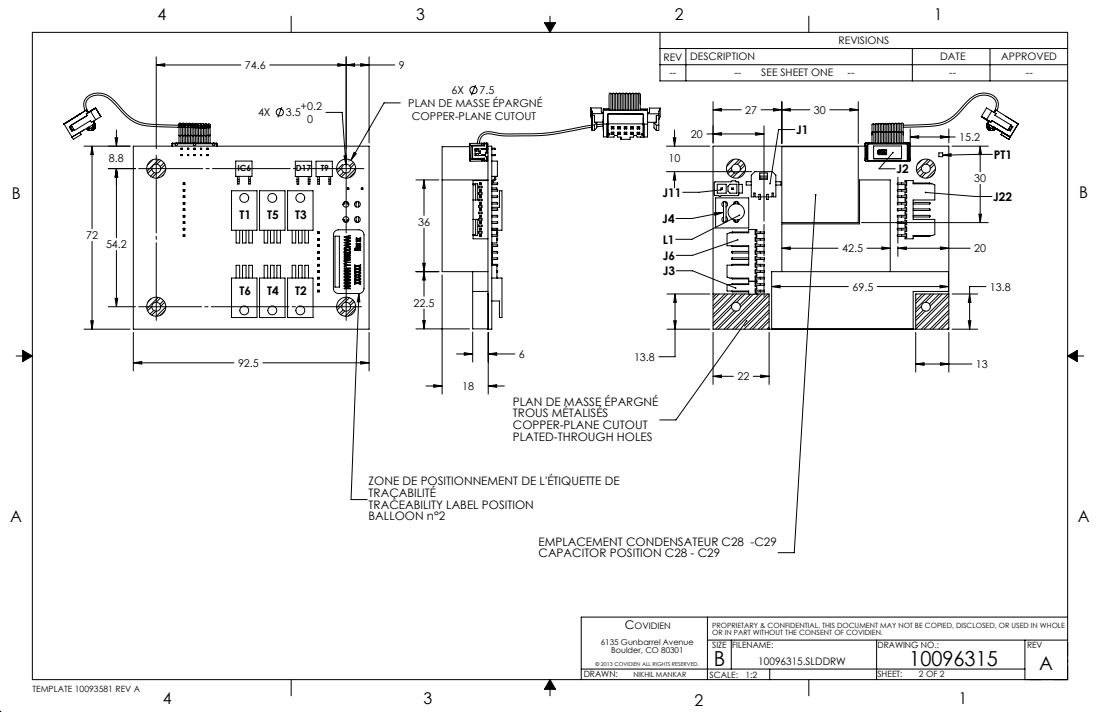
[picture p164: page 2]

REVISIONS

REV | DESCRIPTION | DATE | APPROVED
-- | --SEE SHEET ONE -- | -- | --

PLAN DE MASSE ÉPARGNÉ
COPPER-PLANE CUTOUT

TROUS MÉTALISÉS
PLATED-THROUGH HOLES

ZONE DE POSITIONNEMENT DE L'ÉTIQUETTE DE
TRAÇABILITÉ
TRACEABILITY LABEL POSITION
BALLOON n°2

COVIDIEN 6135 Gunbarrel Avenue Boulder, CO 80301 © 2013 COVIDIEN ALL RIGHTS RESERVED. | PROPRIETARY & CONFIDENTIAL. THIS DOCUMENT MAY NOT BE COPIED, DISCLOSED, OR USED IN WHOLE OR IN PART WITHOUT THE CONSENT OF COVIDIEN.

SIZE B | FILENAME: 10096315.SLDDRW | DRAWING NO.: 10096315 | REV A

DRAWN: NIKHIL MANKAR | SCALE: 1:2 | | SHEET: 2 OF 2
