nsynet/electronics_project2/Medtronic_PB560呼吸机开源资料(3D图纸_原理图_说明书_软件代码等)/medtronic-pb560-ventilator-system-file-set-2/Electronic PCBAs/10096510_Battery_Connection_PCBA/PCBA/10096510A00.PDF

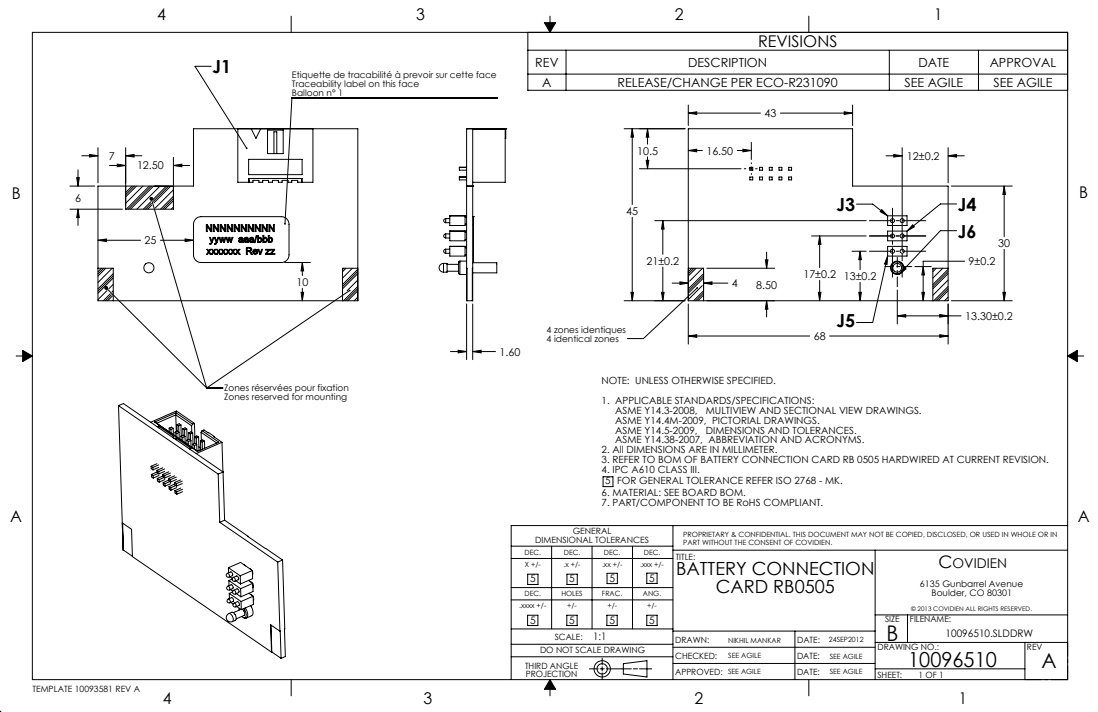
[picture p165: page 1]
Etiquette de tracabilité à prevoir sur cette face; 4 zones identiques 4 identical zones; FOR GENERAL TOLERANCE REFER ISO 2768 - MK.; 2 TEMPLATE 10093581 REV A; .xxxx +/-; THIRD ANGLE; .xxx +/-; SHEET:; DATE:; DRAWING NO.:; DIMENSIONAL TOLERANCES; 6135 Gunbarrel Avenue Boulder, CO 80301

REVISIONS

REV | DESCRIPTION | DATE | APPROVAL
A | RELEASE/CHANGE PER ECO-R231090 | SEE AGILE | SEE AGILE

Traceability label on this face
Balloon n° 1

NOTE: UNLESS OTHERWISE SPECIFIED.
1. APPLICABLE STANDARDS/SPECIFICATIONS:
ASME Y14.3-2008, MULTIVIEW AND SECTIONAL VIEW DRAWINGS.
ASME Y14.4M-2009, PICTORIAL DRAWINGS.
ASME Y14.5-2009, DIMENSIONS AND TOLERANCES.
ASME Y14.38-2007, ABBREVIATION AND ACRONYMS.
2. All DIMENSIONS ARE IN MILLIMETER.
3. REFER TO BOM OF BATTERY CONNECTION CARD RB 0505 HARDWIRED AT CURRENT REVISION.
4. IPC A610 CLASS III.
6. MATERIAL: SEE BOARD BOM.
7. PART/COMPONENT TO BE RoHS COMPLIANT.

Zones réservées pour fixation
Zones reserved for mounting

PROPRIETARY & CONFIDENTIAL. THIS DOCUMENT MAY NOT BE COPIED, DISCLOSED, OR USED IN WHOLE OR IN
PART WITHOUT THE CONSENT OF COVIDIEN.
TITLE:
BATTERY CONNECTION
CARD RB0505

© 2013 COVIDIEN ALL RIGHTS RESERVED.
SIZE
FILENAME:
10096510.SLDDRW

1:1 SCALE: | DRAWN: NIKHIL MANKAR CHECKED: SEE AGILE APPROVED: SEE AGILE | 24SEP2012 DATE: SEE AGILE DATE: SEE AGILE
DO NOT SCALE DRAWING | | | 10096510 | REV A
