nsynet/electronics_project2/Medtronic_PB560呼吸机开源资料(3D图纸_原理图_说明书_软件代码等)/medtronic-pb560-ventilator-system-file-set-2/Electronic PCBAs/10106052_PowerPack_PCBA/3D_Model/10106054A00.PDF

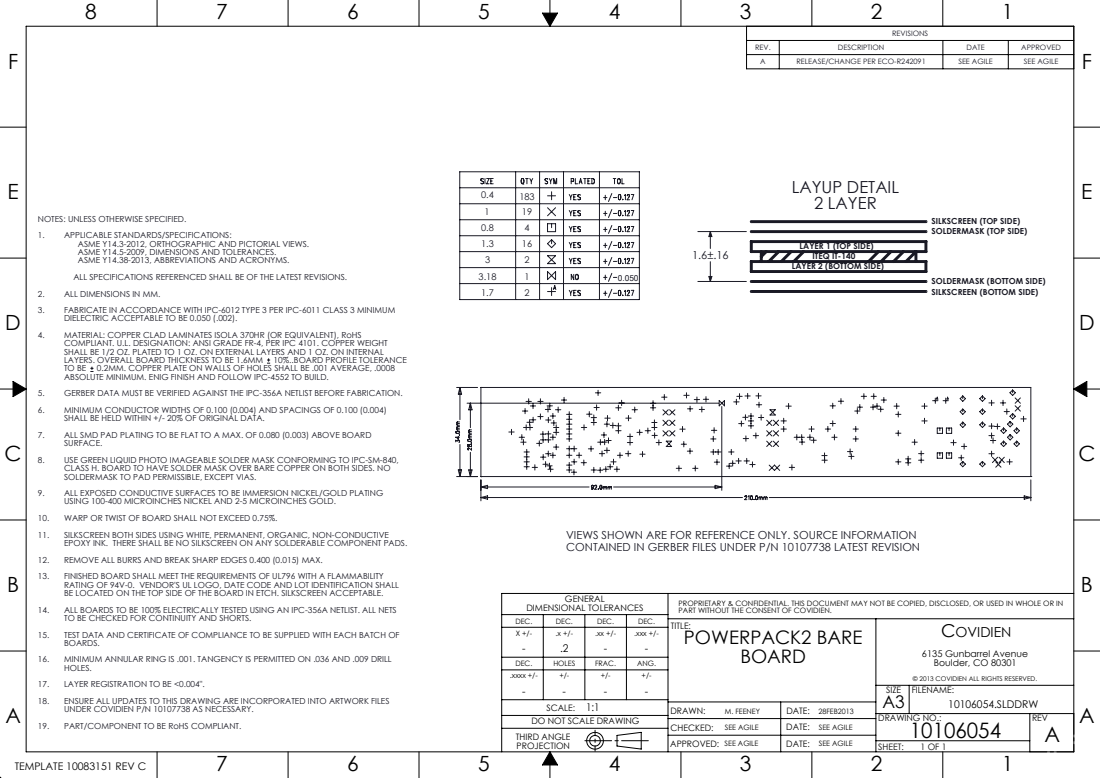
[picture p166: page 1]
LAYUP DETAIL 2 LAYER; 6135 Gunbarrel Avenue Boulder, CO 80301; © 2013 COVIDIEN ALL RIGHTS RESERVED.; DIMENSIONAL TOLERANCES; SEE AGILE; DRAWING NO.:; SHEET:; .xxx +/-; THIRD ANGLE; DO NOT SCALE DRAWING; M. FEENEY; 28FEB2013; .xxxx +/-; TEMPLATE 10083151 REV C

REV. | DESCRIPTION | DATE | APPROVED
A | RELEASE/CHANGE PER ECO-R242091 | SEE AGILE | SEE AGILE

NOTES: UNLESS OTHERWISE SPECIFIED.
1. APPLICABLE STANDARDS/SPECIFICATIONS:

SILKSCREEN (TOP SIDE)
SOLDERMASK (TOP SIDE)

ASME Y14.3-2012, ORTHOGRAPHIC AND PICTORIAL VIEWS.
ASME Y14.5-2009, DIMENSIONS AND TOLERANCES.
ASME Y14.38-2013, ABBREVIATIONS AND ACRONYMS.
ALL SPECIFICATIONS REFERENCED SHALL BE OF THE LATEST REVISIONS.
4. MATERIAL: COPPER CLAD LAMINATES ISOLA 370HR (OR EQUIVALENT), RoHS
COMPLIANT. U.L. DESIGNATION: ANSI GRADE FR-4, PER IPC 4101. COPPER WEIGHT
SHALL BE 1/2 OZ. PLATED TO 1 OZ. ON EXTERNAL LAYERS AND 1 OZ. ON INTERNAL
LAYERS. OVERALL BOARD THICKNESS TO BE 1.6MM 10%..BOARD PROFILE TOLERANCE
TO BE 0.2MM. COPPER PLATE ON WALLS OF HOLES SHALL BE .001 AVERAGE, .0008
ABSOLUTE MINIMUM. ENIG FINISH AND FOLLOW IPC-4552 TO BUILD.
5. GERBER DATA MUST BE VERIFIED AGAINST THE IPC-356A NETLIST BEFORE FABRICATION.
6. MINIMUM CONDUCTOR WIDTHS OF 0.100 (0.004) AND SPACINGS OF 0.100 (0.004)
SHALL BE HELD WITHIN +/- 20% OF ORIGINAL DATA.
7. ALL SMD PAD PLATING TO BE FLAT TO A MAX. OF 0.080 (0.003) ABOVE BOARD
SURFACE.
8. USE GREEN LIQUID PHOTO IMAGEABLE SOLDER MASK CONFORMING TO IPC-SM-840,
CLASS H. BOARD TO HAVE SOLDER MASK OVER BARE COPPER ON BOTH SIDES. NO
SOLDERMASK TO PAD PERMISSIBLE, EXCEPT VIAS.
9. ALL EXPOSED CONDUCTIVE SURFACES TO BE IMMERSION NICKEL/GOLD PLATING
USING 100-400 MICROINCHES NICKEL AND 2-5 MICROINCHES GOLD.
10. WARP OR TWIST OF BOARD SHALL NOT EXCEED 0.75%.
11. SILKSCREEN BOTH SIDES USING WHITE, PERMANENT, ORGANIC, NON-CONDUCTIVE
EPOXY INK. THERE SHALL BE NO SILKSCREEN ON ANY SOLDERABLE COMPONENT PADS.
12. REMOVE ALL BURRS AND BREAK SHARP EDGES 0.400 (0.015) MAX.
13. FINISHED BOARD SHALL MEET THE REQUIREMENTS OF UL796 WITH A FLAMMABILITY
RATING OF 94V-0. VENDOR'S UL LOGO, DATE CODE AND LOT IDENTIFICATION SHALL
BE LOCATED ON THE TOP SIDE OF THE BOARD IN ETCH. SILKSCREEN ACCEPTABLE.
14. ALL BOARDS TO BE 100% ELECTRICALLY TESTED USING AN IPC-356A NETLIST. ALL NETS
TO BE CHECKED FOR CONTINUITY AND SHORTS.
15. TEST DATA AND CERTIFICATE OF COMPLIANCE TO BE SUPPLIED WITH EACH BATCH OF
BOARDS.
16. MINIMUM ANNULAR RING IS .001. TANGENCY IS PERMITTED ON .036 AND .009 DRILL
HOLES.
17. LAYER REGISTRATION TO BE <0.004".
18. ENSURE ALL UPDATES TO THIS DRAWING ARE INCORPORATED INTO ARTWORK FILES
19. PART/COMPONENT TO BE RoHS COMPLIANT.

LAYER 1 (TOP SIDE)
ITEQ IT-140
LAYER 2 (BOTTOM SIDE)

SOLDERMASK (BOTTOM SIDE)
SILKSCREEN (BOTTOM SIDE)

2. ALL DIMENSIONS IN MM.
3. FABRICATE IN ACCORDANCE WITH IPC-6012 TYPE 3 PER IPC-6011 CLASS 3 MINIMUM
DIELECTRIC ACCEPTABLE TO BE 0.050 (.002).

VIEWS SHOWN ARE FOR REFERENCE ONLY. SOURCE INFORMATION
CONTAINED IN GERBER FILES UNDER P/N 10107738 LATEST REVISION

PROPRIETARY & CONFIDENTIAL. THIS DOCUMENT MAY NOT BE COPIED, DISCLOSED, OR USED IN WHOLE OR IN
PART WITHOUT THE CONSENT OF COVIDIEN.
TITLE:
POWERPACK2 BARE
BOARD

UNDER COVIDIEN P/N 10107738 AS NECESSARY.
