nsynet/electronics_project2/Medtronic_PB560呼吸机开源资料(3D图纸_原理图_说明书_软件代码等)/medtronic-pb560-ventilator-system-file-set-2/Electronic PCBAs/10106052_PowerPack_PCBA/PCB/10107738A00.pdf

# COVIDIEN

# Powerpack2 Board, 10106054 Rev A

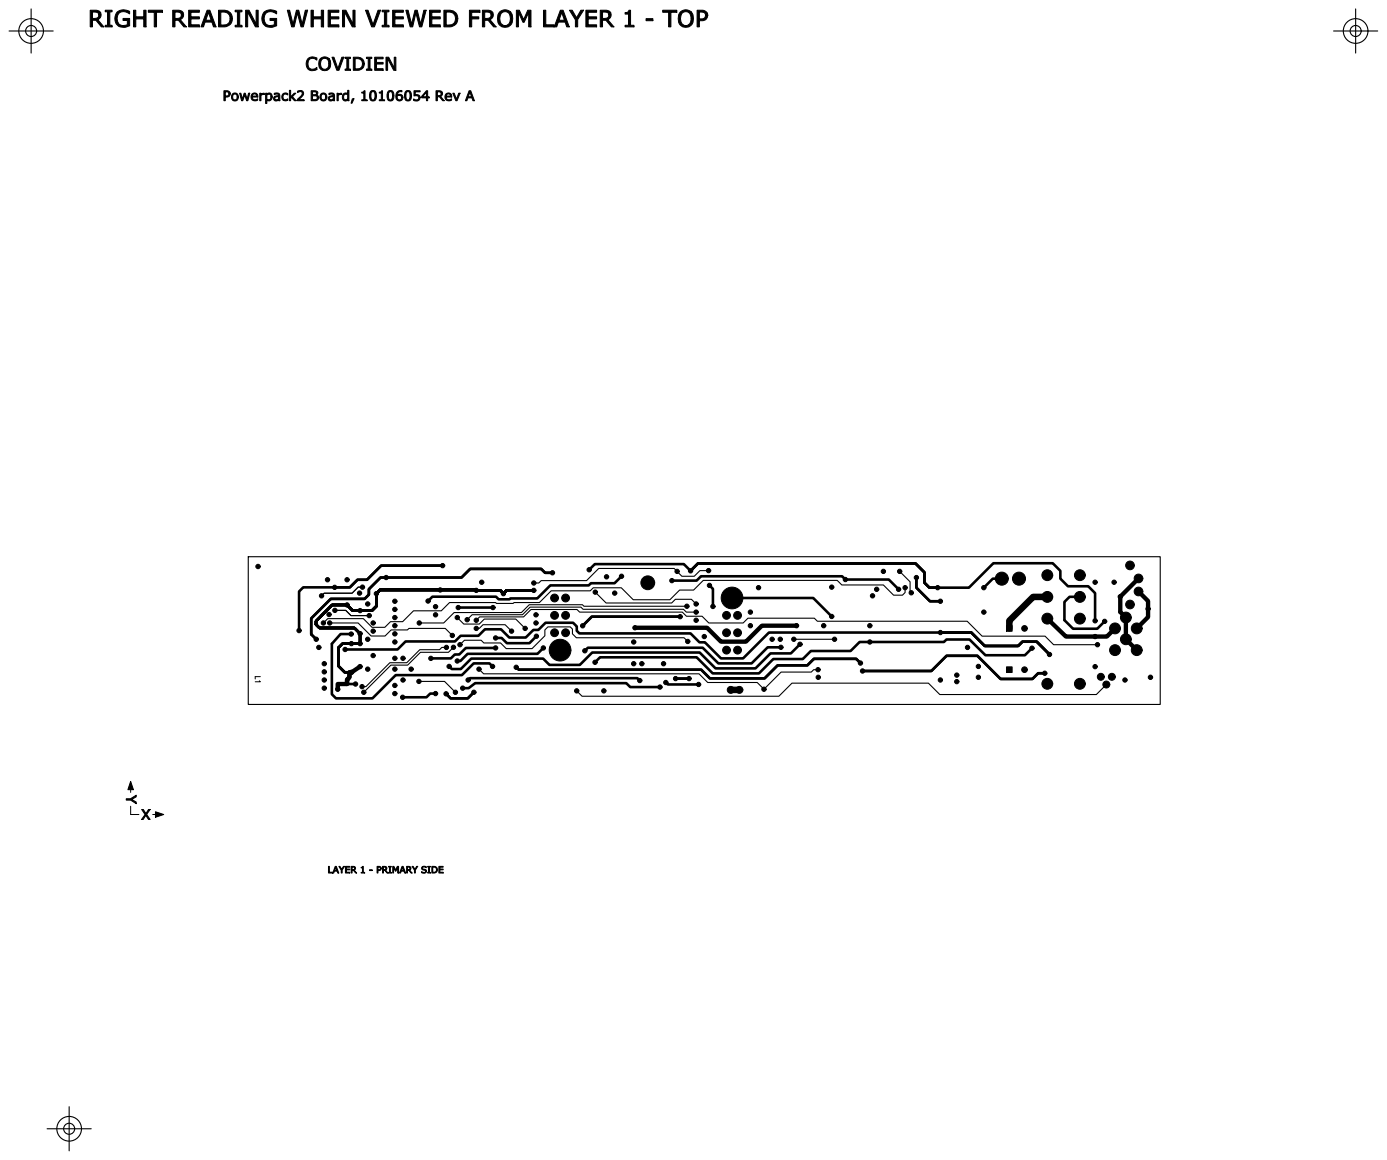
[picture p167: page 1]
FL1xCB FL1xCG¹FL1xCG² FL1xCG³ FL1xPSG; RL1RL1x11 RL1x12 RL1x14 RL1x21 RL1x22 RL1x24 RL1xA²; RL1xA¹; STAR1 STAR¹x1 STAR¹x2; C8C⁸x1; C⁸x2; C9C⁹x1; C⁹x2; U6U⁶x1 U⁶x2 U⁶x3; FID1FID¹x1; FID2FID²x1; TXTXx1; RXRXx1

RIGHT READING WHEN VIEWED FROM LAYER 1 - TOP

LAYER 1 - PRIMARY SIDE

# COVIDIEN

# Powerpack2 Board, 10106054 Rev A

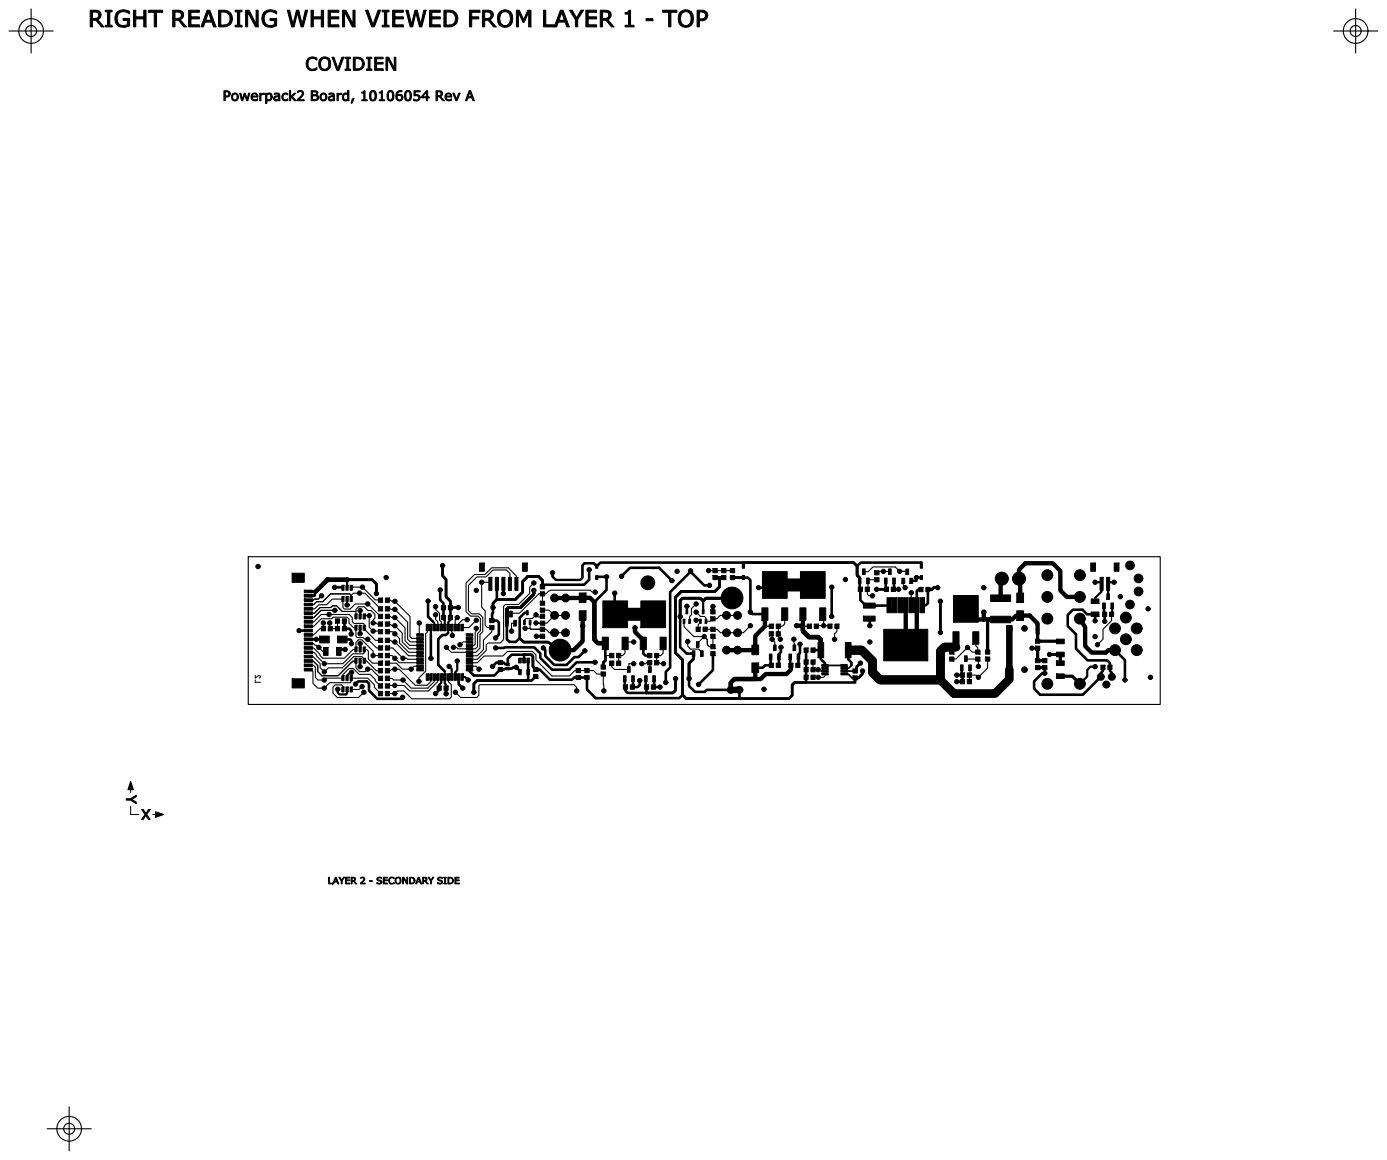
[picture p168: page 2]

RIGHT READING WHEN VIEWED FROM LAYER 1 - TOP

# COVIDIEN

# Powerpack2 Board, 10106054 Rev A

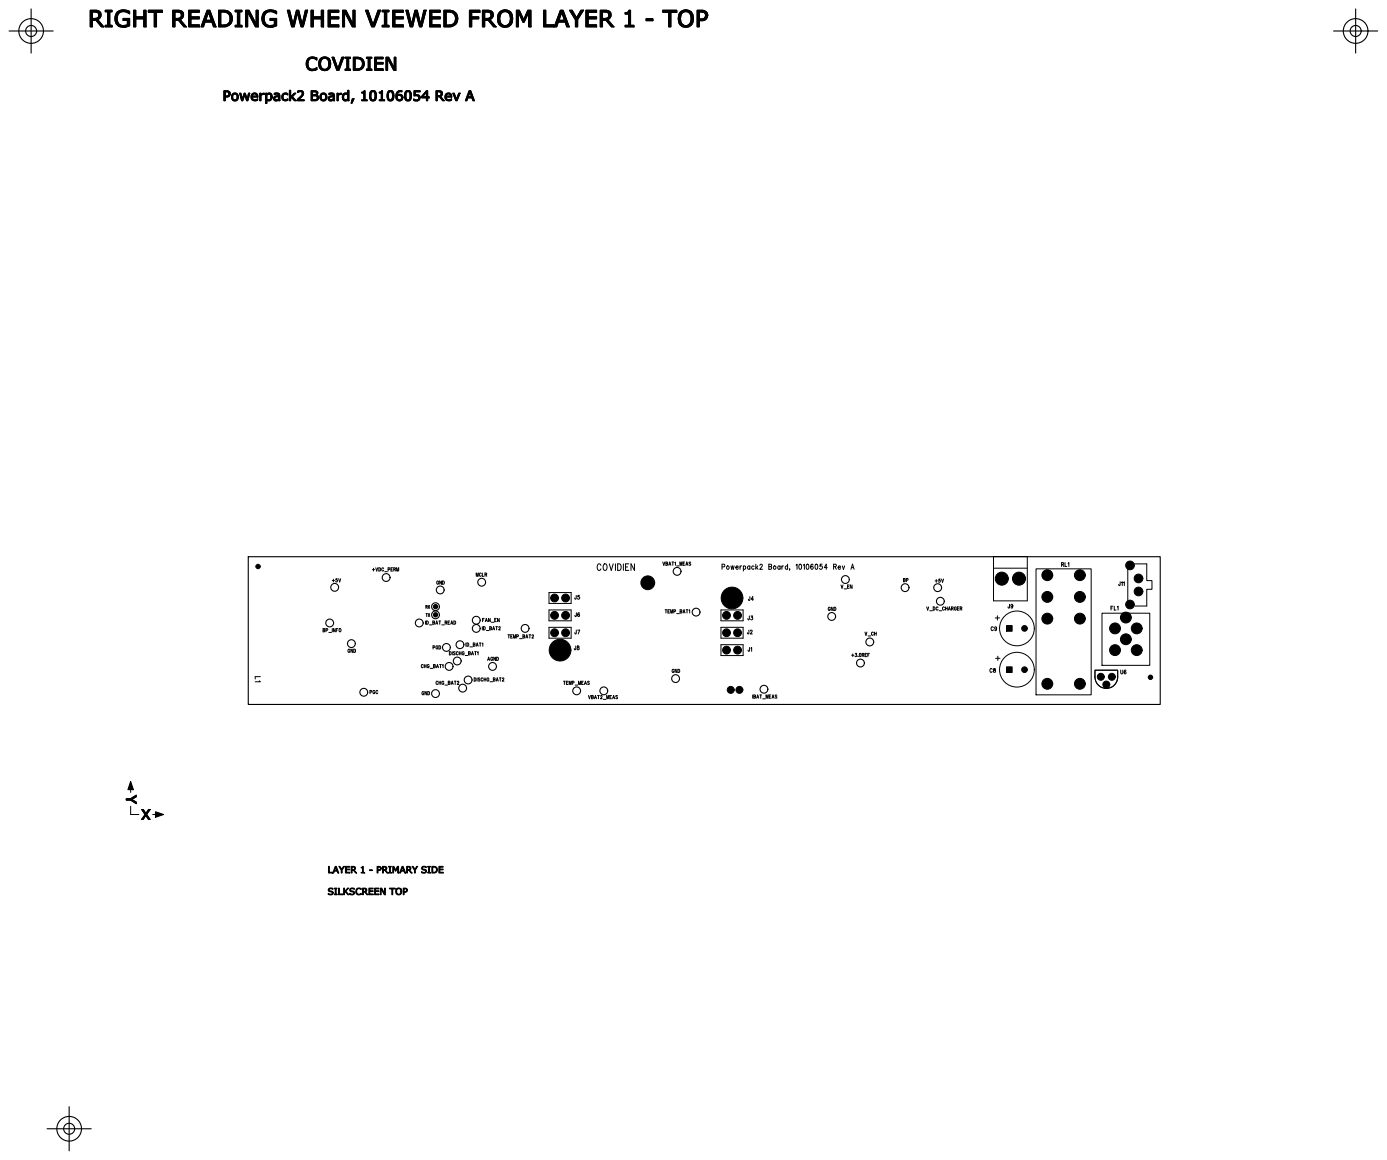
[picture p169: page 3]

RIGHT READING WHEN VIEWED FROM LAYER 1 - TOP

# COVIDIEN

# Powerpack2 Board, 10106054 Rev A

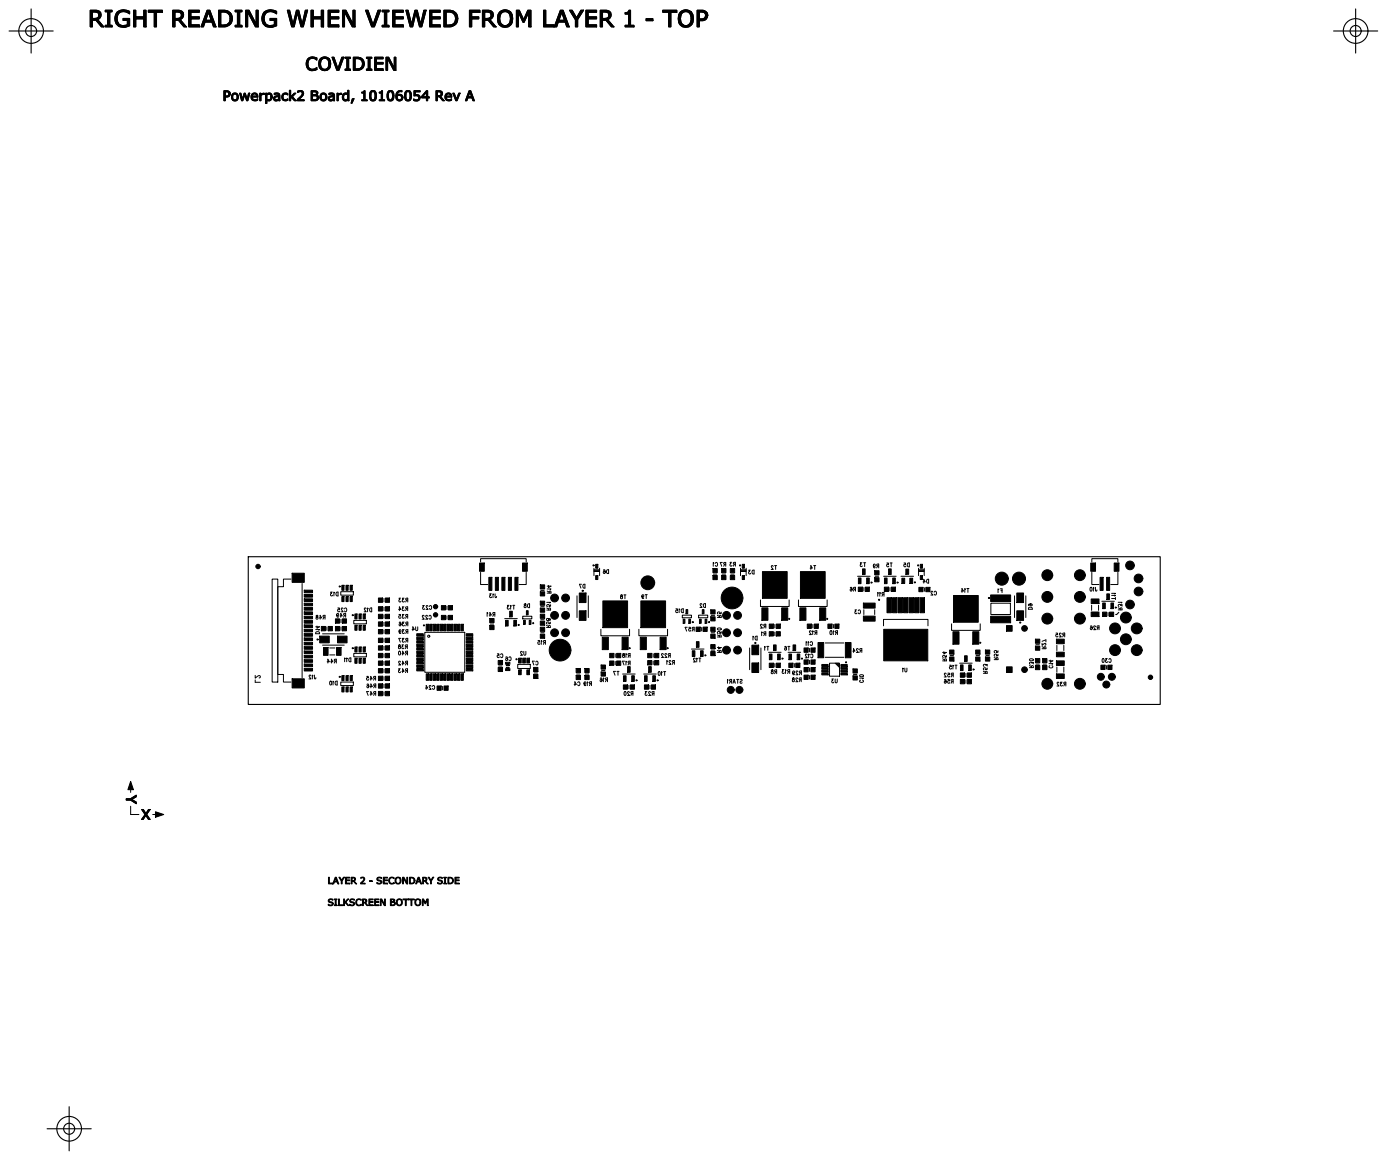
[picture p170: page 4]

RIGHT READING WHEN VIEWED FROM LAYER 1 - TOP

# COVIDIEN

# Powerpack2 Board, 10106054 Rev A

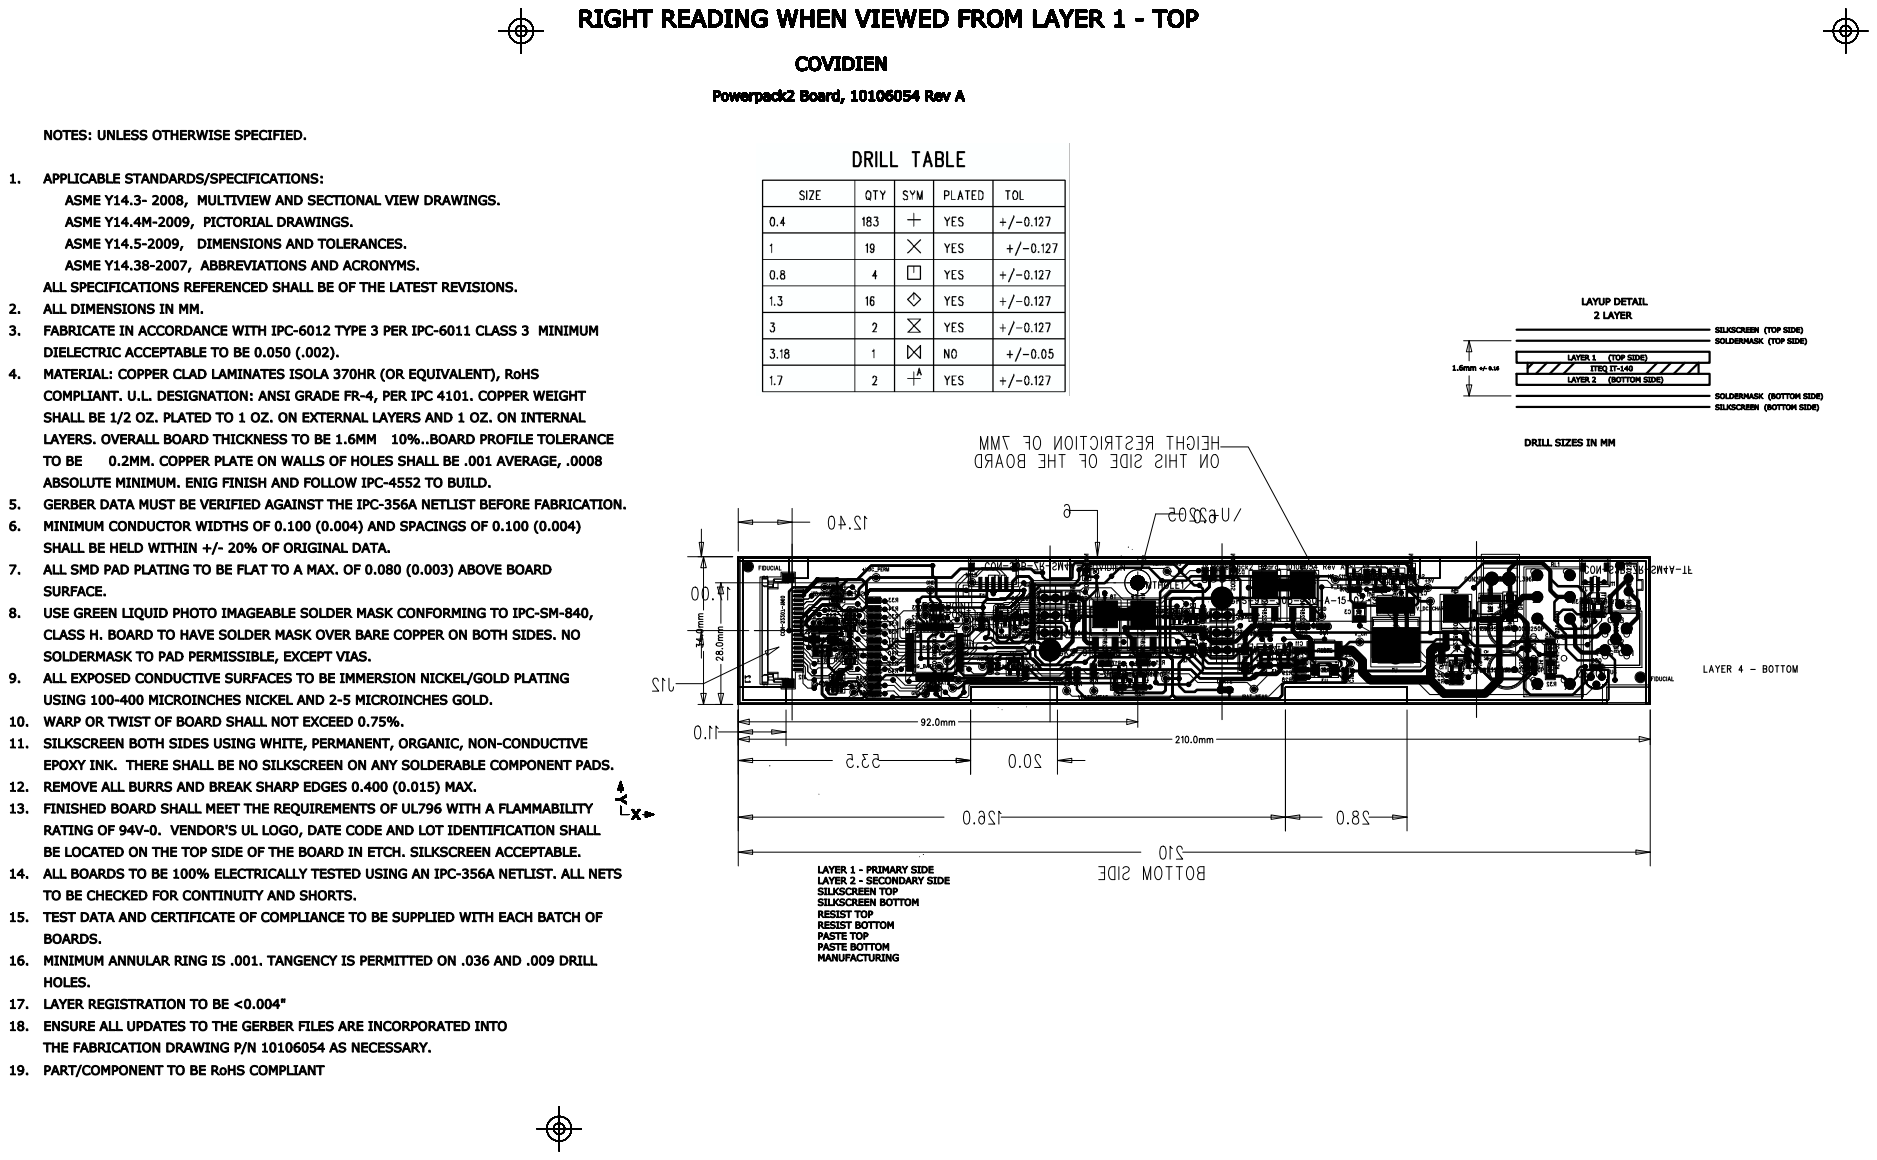
[picture p171: page 5]

RIGHT READING WHEN VIEWED FROM LAYER 1 - TOP

NOTES: UNLESS OTHERWISE SPECIFIED.

ASME Y14.3- 2008, MULTIVIEW AND SECTIONAL VIEW DRAWINGS.

ASME Y14.38-2007, ABBREVIATIONS AND ACRONYMS.

ALL SPECIFICATIONS REFERENCED SHALL BE OF THE LATEST REVISIONS.

ALL DIMENSIONS IN MM.

FABRICATE IN ACCORDANCE WITH IPC-6012 TYPE 3 PER IPC-6011 CLASS 3 MINIMUM

DIELECTRIC ACCEPTABLE TO BE 0.050 (.002).

MATERIAL: COPPER CLAD LAMINATES ISOLA 370HR (OR EQUIVALENT), RoHS

COMPLIANT. U.L. DESIGNATION: ANSI GRADE FR-4, PER IPC 4101. COPPER WEIGHT

SHALL BE 1/2 OZ. PLATED TO 1 OZ. ON EXTERNAL LAYERS AND 1 OZ. ON INTERNAL

LAYERS. OVERALL BOARD THICKNESS TO BE 1.6MM

DRILL SIZES IN MM

0.2MM. COPPER PLATE ON WALLS OF HOLES SHALL BE .001 AVERAGE, .0008

ABSOLUTE MINIMUM. ENIG FINISH AND FOLLOW IPC-4552 TO BUILD.

GERBER DATA MUST BE VERIFIED AGAINST THE IPC-356A NETLIST BEFORE FABRICATION.

MINIMUM CONDUCTOR WIDTHS OF 0.100 (0.004) AND SPACINGS OF 0.100 (0.004)

SHALL BE HELD WITHIN +/- 20% OF ORIGINAL DATA.

ALL SMD PAD PLATING TO BE FLAT TO A MAX. OF 0.080 (0.003) ABOVE BOARD

USE GREEN LIQUID PHOTO IMAGEABLE SOLDER MASK CONFORMING TO IPC-SM-840,

CLASS H. BOARD TO HAVE SOLDER MASK OVER BARE COPPER ON BOTH SIDES. NO

SOLDERMASK TO PAD PERMISSIBLE, EXCEPT VIAS.

ALL EXPOSED CONDUCTIVE SURFACES TO BE IMMERSION NICKEL/GOLD PLATING

USING 100-400 MICROINCHES NICKEL AND 2-5 MICROINCHES GOLD.

WARP OR TWIST OF BOARD SHALL NOT EXCEED 0.75%.

SILKSCREEN BOTH SIDES USING WHITE, PERMANENT, ORGANIC, NON-CONDUCTIVE

EPOXY INK. THERE SHALL BE NO SILKSCREEN ON ANY SOLDERABLE COMPONENT PADS.

REMOVE ALL BURRS AND BREAK SHARP EDGES 0.400 (0.015) MAX.

FINISHED BOARD SHALL MEET THE REQUIREMENTS OF UL796 WITH A FLAMMABILITY

RATING OF 94V-0. VENDOR'S UL LOGO, DATE CODE AND LOT IDENTIFICATION SHALL

BE LOCATED ON THE TOP SIDE OF THE BOARD IN ETCH. SILKSCREEN ACCEPTABLE.

ALL BOARDS TO BE 100% ELECTRICALLY TESTED USING AN IPC-356A NETLIST. ALL NETS

TO BE CHECKED FOR CONTINUITY AND SHORTS.

TEST DATA AND CERTIFICATE OF COMPLIANCE TO BE SUPPLIED WITH EACH BATCH OF

MINIMUM ANNULAR RING IS .001. TANGENCY IS PERMITTED ON .036 AND .009 DRILL

LAYER REGISTRATION TO BE <0.004"

18. ENSURE ALL UPDATES TO THE GERBER FILES ARE INCORPORATED INTO

THE FABRICATION DRAWING P/N 10106054 AS NECESSARY.

19. PART/COMPONENT TO BE RoHS COMPLIANT
