nsynet/electronics_project2/Medtronic_PB560呼吸机开源资料(3D图纸_原理图_说明书_软件代码等)/medtronic-pb560-ventilator-system-file-set-2/Electronic PCBAs/10106052_PowerPack_PCBA/PCBA/10106052C00.PDF

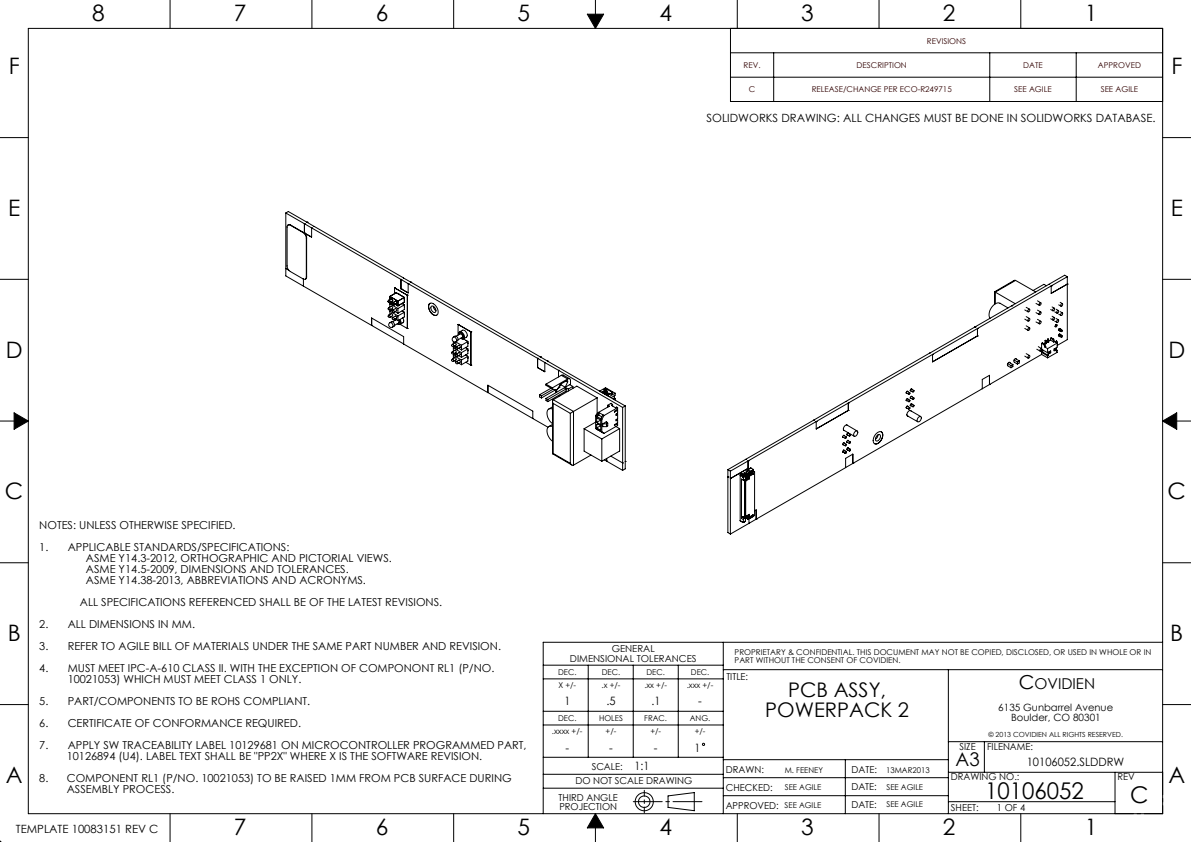
[picture p172: page 1]
6135 Gunbarrel Avenue Boulder, CO 80301; DIMENSIONAL TOLERANCES; SEE AGILE; DRAWING NO.:; SHEET:; .xxx +/-; THIRD ANGLE; DO NOT SCALE DRAWING; M. FEENEY; 13MAR2013; .xxxx +/-; TEMPLATE 10083151 REV C

REV. | DESCRIPTION | DATE | APPROVED

C | RELEASE/CHANGE PER ECO-R249715 | SEE AGILE | SEE AGILE

SOLIDWORKS DRAWING: ALL CHANGES MUST BE DONE IN SOLIDWORKS DATABASE.

NOTES: UNLESS OTHERWISE SPECIFIED.
1. APPLICABLE STANDARDS/SPECIFICATIONS:

ASME Y14.3-2012, ORTHOGRAPHIC AND PICTORIAL VIEWS.
ASME Y14.5-2009, DIMENSIONS AND TOLERANCES.
ASME Y14.38-2013, ABBREVIATIONS AND ACRONYMS.
ALL SPECIFICATIONS REFERENCED SHALL BE OF THE LATEST REVISIONS.
2. ALL DIMENSIONS IN MM.
3. REFER TO AGILE BILL OF MATERIALS UNDER THE SAME PART NUMBER AND REVISION.
4. MUST MEET IPC-A-610 CLASS II. WITH THE EXCEPTION OF COMPONONT RL1 (P/NO.
10021053) WHICH MUST MEET CLASS 1 ONLY.
5. PART/COMPONENTS TO BE ROHS COMPLIANT.
6. CERTIFICATE OF CONFORMANCE REQUIRED.
7. APPLY SW TRACEABILITY LABEL 10129681 ON MICROCONTROLLER PROGRAMMED PART,
10126894 (U4). LABEL TEXT SHALL BE "PP2X" WHERE X IS THE SOFTWARE REVISION.
8. COMPONENT RL1 (P/NO. 10021053) TO BE RAISED 1MM FROM PCB SURFACE DURING
ASSEMBLY PROCESS.

PROPRIETARY & CONFIDENTIAL. THIS DOCUMENT MAY NOT BE COPIED, DISCLOSED, OR USED IN WHOLE OR IN
PART WITHOUT THE CONSENT OF COVIDIEN.
TITLE:
PCB ASSY,
POWERPACK 2

© 2013 COVIDIEN ALL RIGHTS RESERVED.
SIZE
FILENAME:
10106052.SLDDRW

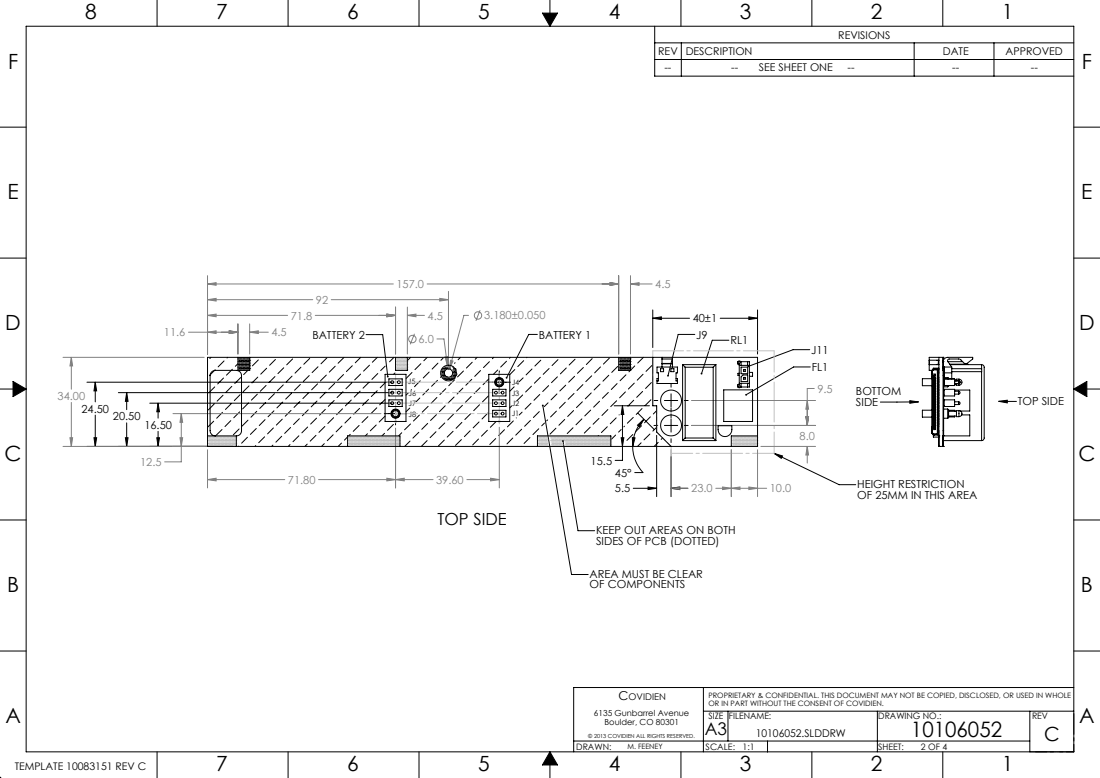
[picture p173: page 2]

REV | DESCRIPTION | DATE | APPROVED
-- | --SEE SHEET ONE -- | -- | --

HEIGHT RESTRICTION
OF 25MM IN THIS AREA

KEEP OUT AREAS ON BOTH
SIDES OF PCB (DOTTED)

AREA MUST BE CLEAR
OF COMPONENTS

COVIDIEN 6135 Gunbarrel Avenue Boulder, CO 80301 © 2013 COVIDIEN ALL RIGHTS RESERVED. | PROPRIETARY & CONFIDENTIAL. THIS DOCUMENT MAY NOT BE COPIED, DISCLOSED, OR USED IN WHOLE OR IN PART WITHOUT THE CONSENT OF COVIDIEN.

SIZE A3 | FILENAME: 10106052.SLDDRW | DRAWING NO.: | REV C

DRAWN: M. FEENEY | SCALE: 1:1 | | SHEET: 2 OF 4

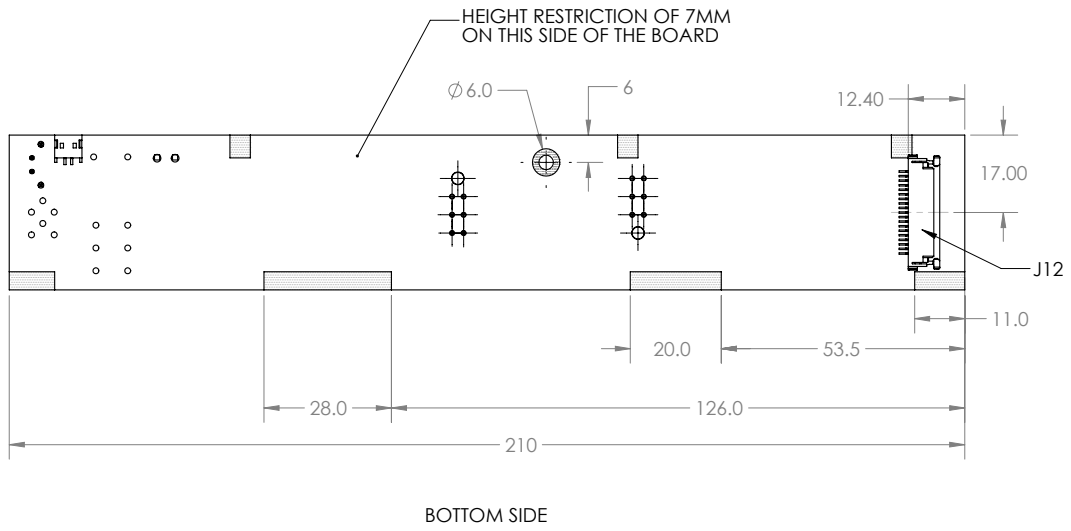
[picture p174: page 3]
BOTTOM SIDE; 6135 Gunbarrel Avenue; SEE SHEET ONE --

HEIGHT RESTRICTION OF 7MM
ON THIS SIDE OF THE BOARD

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

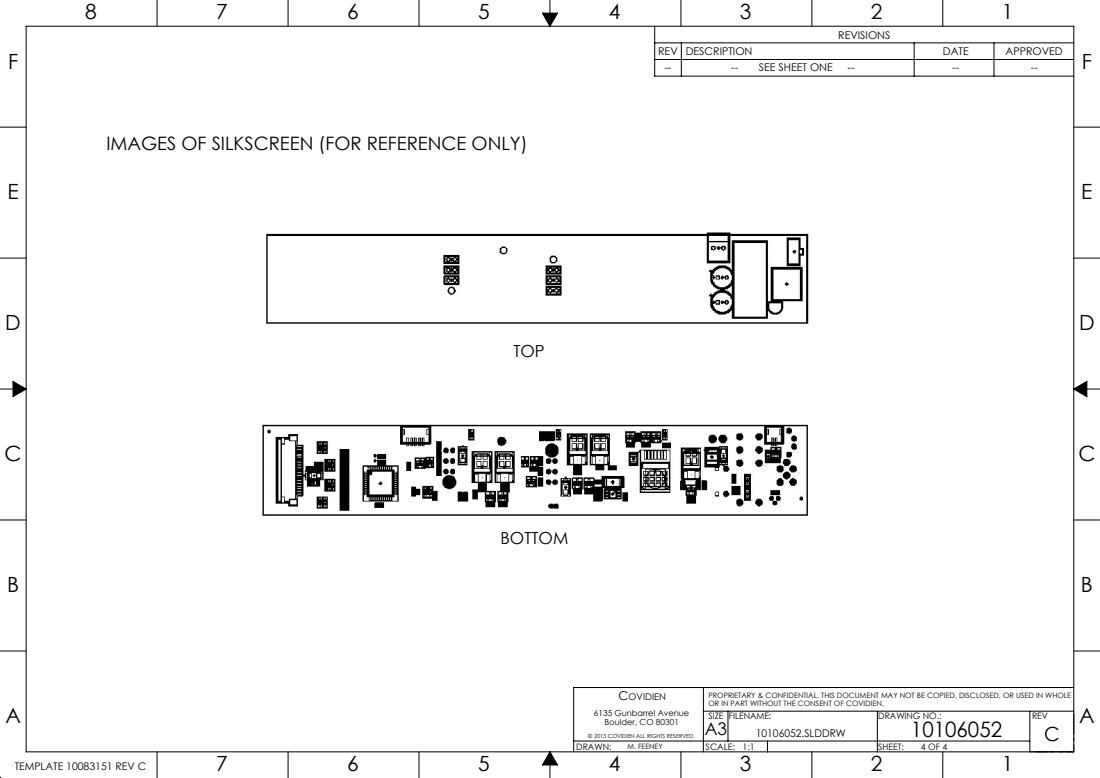
[picture p175: page 4]
6135 Gunbarrel Avenue; SEE SHEET ONE --

IMAGES OF SILKSCREEN (FOR REFERENCE ONLY)

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
