nsynet/electronics_project2/Medtronic_PB560呼吸机开源资料(3D图纸_原理图_说明书_软件代码等)/medtronic-pb560-ventilator-system-file-set-2/Electronic PCBAs/GR106768_Buzzer_PCBA/PCB/GR106771A00.pdf

F

E

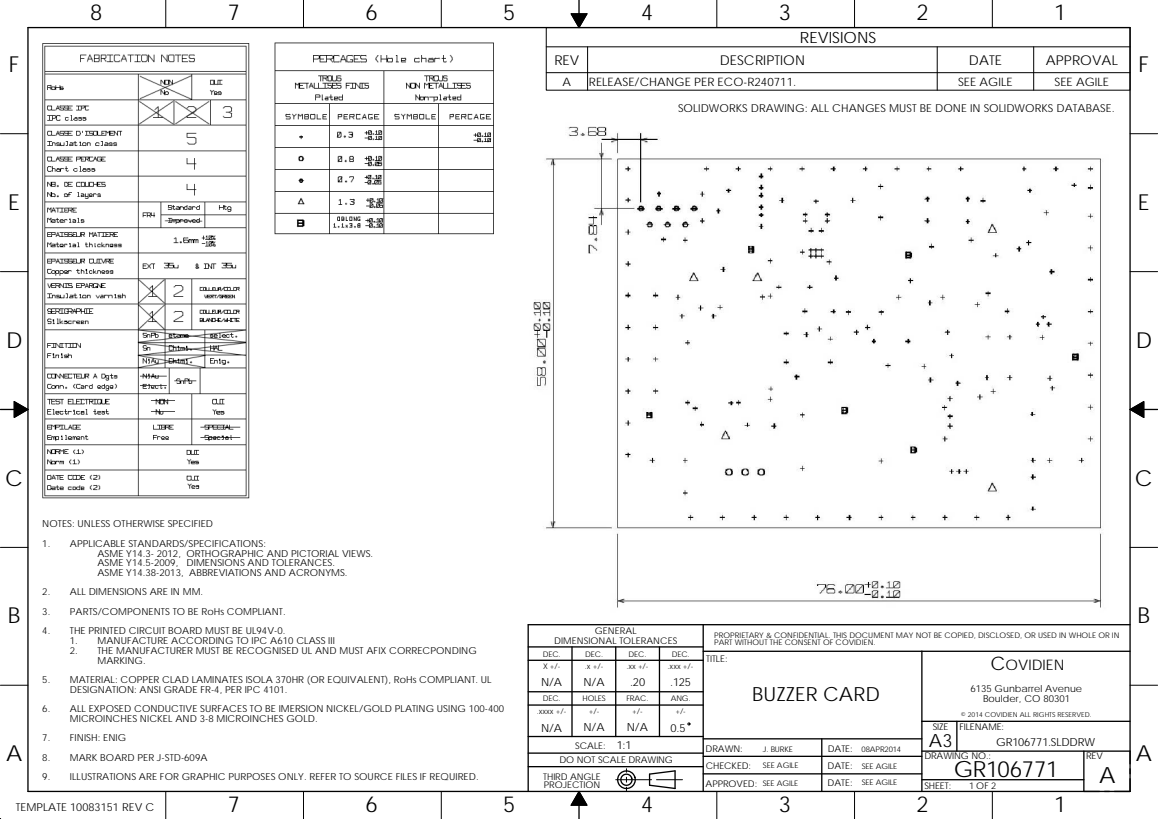
[picture p176: page 1]
DATE:; SEE AGILE; SHEET:; APPROVED:; PROJECTION; THIRD ANGLE; TEMPLATE 10083151 REV C; REVISIONS; REV; DESCRIPTION; DATE; APPROVAL; RELEASE/CHANGE PER ECO-R240711.

SOLIDWORKS DRAWING: ALL CHANGES MUST BE DONE IN SOLIDWORKS DATABASE.

NOTES: UNLESS OTHERWISE SPECIFIED
1. APPLICABLE STANDARDS/SPECIFICATIONS:

ASME Y14.3- 2012, ORTHOGRAPHIC AND PICTORIAL VIEWS.
ASME Y14.5-2009, DIMENSIONS AND TOLERANCES.
ASME Y14.38-2013, ABBREVIATIONS AND ACRONYMS.

2. ALL DIMENSIONS ARE IN MM.
3. PARTS/COMPONENTS TO BE RoHs COMPLIANT.
4. THE PRINTED CIRCUIT BOARD MUST BE UL94V-0.
1. MANUFACTURE ACCORDING TO IPC A610 CLASS III
2. THE MANUFACTURER MUST BE RECOGNISED UL AND MUST AFIX CORRECPONDING
MARKING.

GENERAL | PROPRIETARY & CONFIDENTIAL. THIS DOCUMENT MAY NOT BE COPIED, DISCLOSED, OR USED IN WHOLE OR IN DIMENSIONAL TOLERANCES PART WITHOUT THE CONSENT OF COVIDIEN.

DEC. | DEC. | DEC. | DEC.
X +/-N/A | .x +/-N/A | .xx +/-.20 | .xxx +/-.125

TITLE: BUZZER CARD | COVIDIEN 6135 Gunbarrel Avenue Boulder, CO 80301 © 2014 COVIDIEN ALL RIGHTS RESERVED.

5. MATERIAL: COPPER CLAD LAMINATES ISOLA 370HR (OR EQUIVALENT), RoHs COMPLIANT. UL
DESIGNATION: ANSI GRADE FR-4, PER IPC 4101.
6. ALL EXPOSED CONDUCTIVE SURFACES TO BE IMERSION NICKEL/GOLD PLATING USING 100-400
MICROINCHES NICKEL AND 3-8 MICROINCHES GOLD.
7. FINISH: ENIG

DEC. | HOLES | FRAC. | ANG.
.xxxx +/-N/A | +/-N/A | +/-N/A | +/-0.5

SIZE A3 | FILENAME: GR106771.SLDDRW

SCALE: 1:1 | DRAWN: J. BURKE | DATE: 08APR2014
DO NOT SCALE DRAWING | CHECKED: SEE AGILE | DATE: SEE AGILE | DRAWING NO.: GR106771 | REV A

8. MARK BOARD PER J-STD-609A
9. ILLUSTRATIONS ARE FOR GRAPHIC PURPOSES ONLY. REFER TO SOURCE FILES IF REQUIRED.

E

F

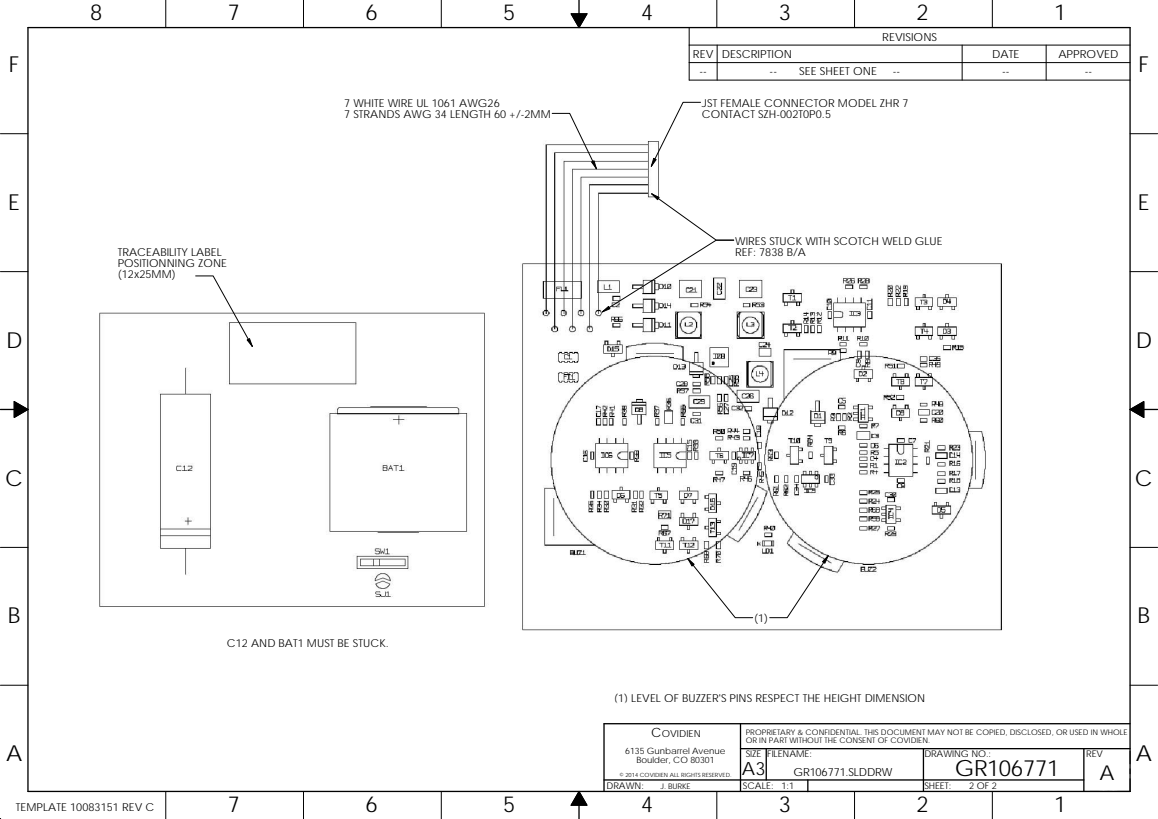
[picture p177: page 2]
TRACEABILITY LABEL POSITIONNING ZONE (12x25MM); TEMPLATE 10083151 REV C

REVISIONS

REV | DESCRIPTION | DATE | APPROVED
-- | --SEE SHEET ONE -- | -- | --

7 WHITE WIRE UL 1061 AWG26
7 STRANDS AWG 34 LENGTH 60 +/-2MM

JST FEMALE CONNECTOR MODEL ZHR 7
CONTACT SZH-002T0P0.5

WIRES STUCK WITH SCOTCH WELD GLUE
REF: 7838 B/A

C12 AND BAT1 MUST BE STUCK.
REFER TO DRAWING 40966.E04.000.

(1) LEVEL OF BUZZER'S PINS RESPECT THE HEIGHT DIMENSION
FOR BUZZERS ASSEBMLYING. REFER TO DRAWING 40966.E04.000

COVIDIEN 6135 Gunbarrel Avenue Boulder, CO 80301 © 2014 COVIDIEN ALL RIGHTS RESERVED. | PROPRIETARY & CONFIDENTIAL. THIS DOCUMENT MAY NOT BE COPIED, DISCLOSED, OR USED IN WHOLE OR IN PART WITHOUT THE CONSENT OF COVIDIEN.

SIZE A3 | FILENAME: GR106771.SLDDRW | DRAWING NO.: GR106771 | REV A

DRAWN: J. BURKE | SCALE: 1:1 | | SHEET: 2 OF 2
