nsynet/electronics_project2/Medtronic_PB560呼吸机开源资料(3D图纸_原理图_说明书_软件代码等)/medtronic-pb560-ventilator-system-file-set-2/Electronic PCBAs/GR106768_Buzzer_PCBA/PCBA/GR106768B00.pdf

## REVISIONS

REV | DESCRIPTION | DATE | APPROVAL

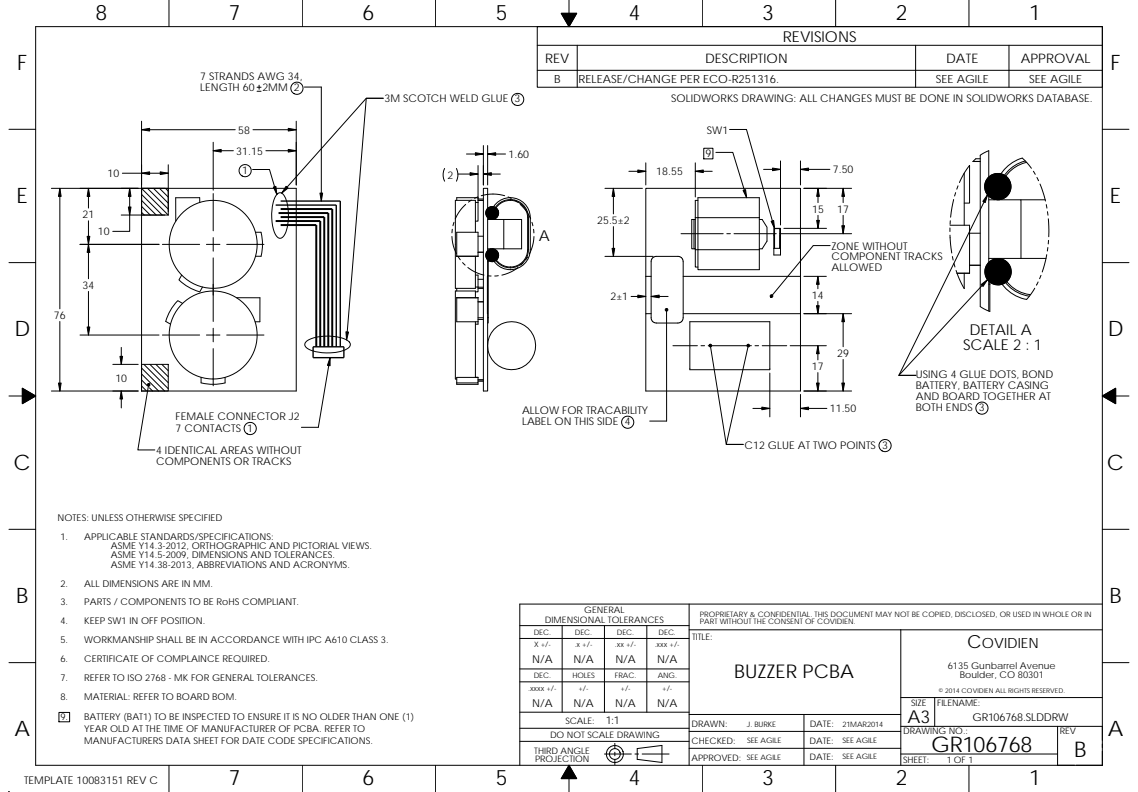
[picture p178: page 1]
LENGTH 60; 7 STRANDS AWG 34, 2; RELEASE/CHANGE PER ECO-R251316.; SEE AGILE; DATE:; APPROVED:; SHEET:; PROJECTION; TEMPLATE 10083151 REV C; THIRD ANGLE; ALLOWED; COMPONENT TRACKS; ZONE WITHOUT; SCALE 2 : 1; DETAIL A

3M SCOTCH WELD GLUE 3

SOLIDWORKS DRAWING: ALL CHANGES MUST BE DONE IN SOLIDWORKS DATABASE.

USING 4 GLUE DOTS, BOND
BATTERY, BATTERY CASING
AND BOARD TOGETHER AT
BOTH ENDS 3

ALLOW FOR TRACABILITY
LABEL ON THIS SIDE 4

FEMALE CONNECTOR J2
7 CONTACTS 1
4 IDENTICAL AREAS WITHOUT
COMPONENTS OR TRACKS

C12 GLUE AT TWO POINTS 3

NOTES: UNLESS OTHERWISE SPECIFIED
1. APPLICABLE STANDARDS/SPECIFICATIONS:

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

2. ALL DIMENSIONS ARE IN MM.

3. PARTS / COMPONENTS TO BE RoHS COMPLIANT.
4. KEEP SW1 IN OFF POSITION.
5. WORKMANSHIP SHALL BE IN ACCORDANCE WITH IPC A610 CLASS 3.
6. CERTIFICATE OF COMPLAINCE REQUIRED.
7. REFER TO ISO 2768 - MK FOR GENERAL TOLERANCES.
8. MATERIAL: REFER TO BOARD BOM.
9. BATTERY (BAT1) TO BE INSPECTED TO ENSURE IT IS NO OLDER THAN ONE (1)

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

DEC. | DEC. | DEC. | DEC.
X +/-N/A | .x +/-N/A | .xx +/-N/A | .xxx +/-N/A

TITLE: BUZZER PCBA | COVIDIEN 6135 Gunbarrel Avenue Boulder, CO 80301 © 2014 COVIDIEN ALL RIGHTS RESERVED.

DEC. | HOLES | FRAC. | ANG.
.xxxx +/-N/A | +/-N/A | +/-N/A | +/-N/A
DO NOT SCALE DRAWING | | | DRAWING NO.: GR106768 | REV B

SIZE A3 | FILENAME: GR106768.SLDDRW

SCALE: 1:1 | DRAWN: J. BURKE | DATE: 21MAR2014

YEAR OLD AT THE TIME OF MANUFACTURER OF PCBA. REFER TO
MANUFACTURERS DATA SHEET FOR DATE CODE SPECIFICATIONS.

CHECKED: SEE AGILE | DATE: SEE AGILE
