nsynet/electronics_project2/Medtronic_PB560呼吸机开源资料(3D图纸_原理图_说明书_软件代码等)/medtronic-pb560-ventilator-system-file-set-2/Electronic PCBAs/GR106769_CPU_PCBA/PCBA/GR106769B00.pdf

D

## DETAIL C-C

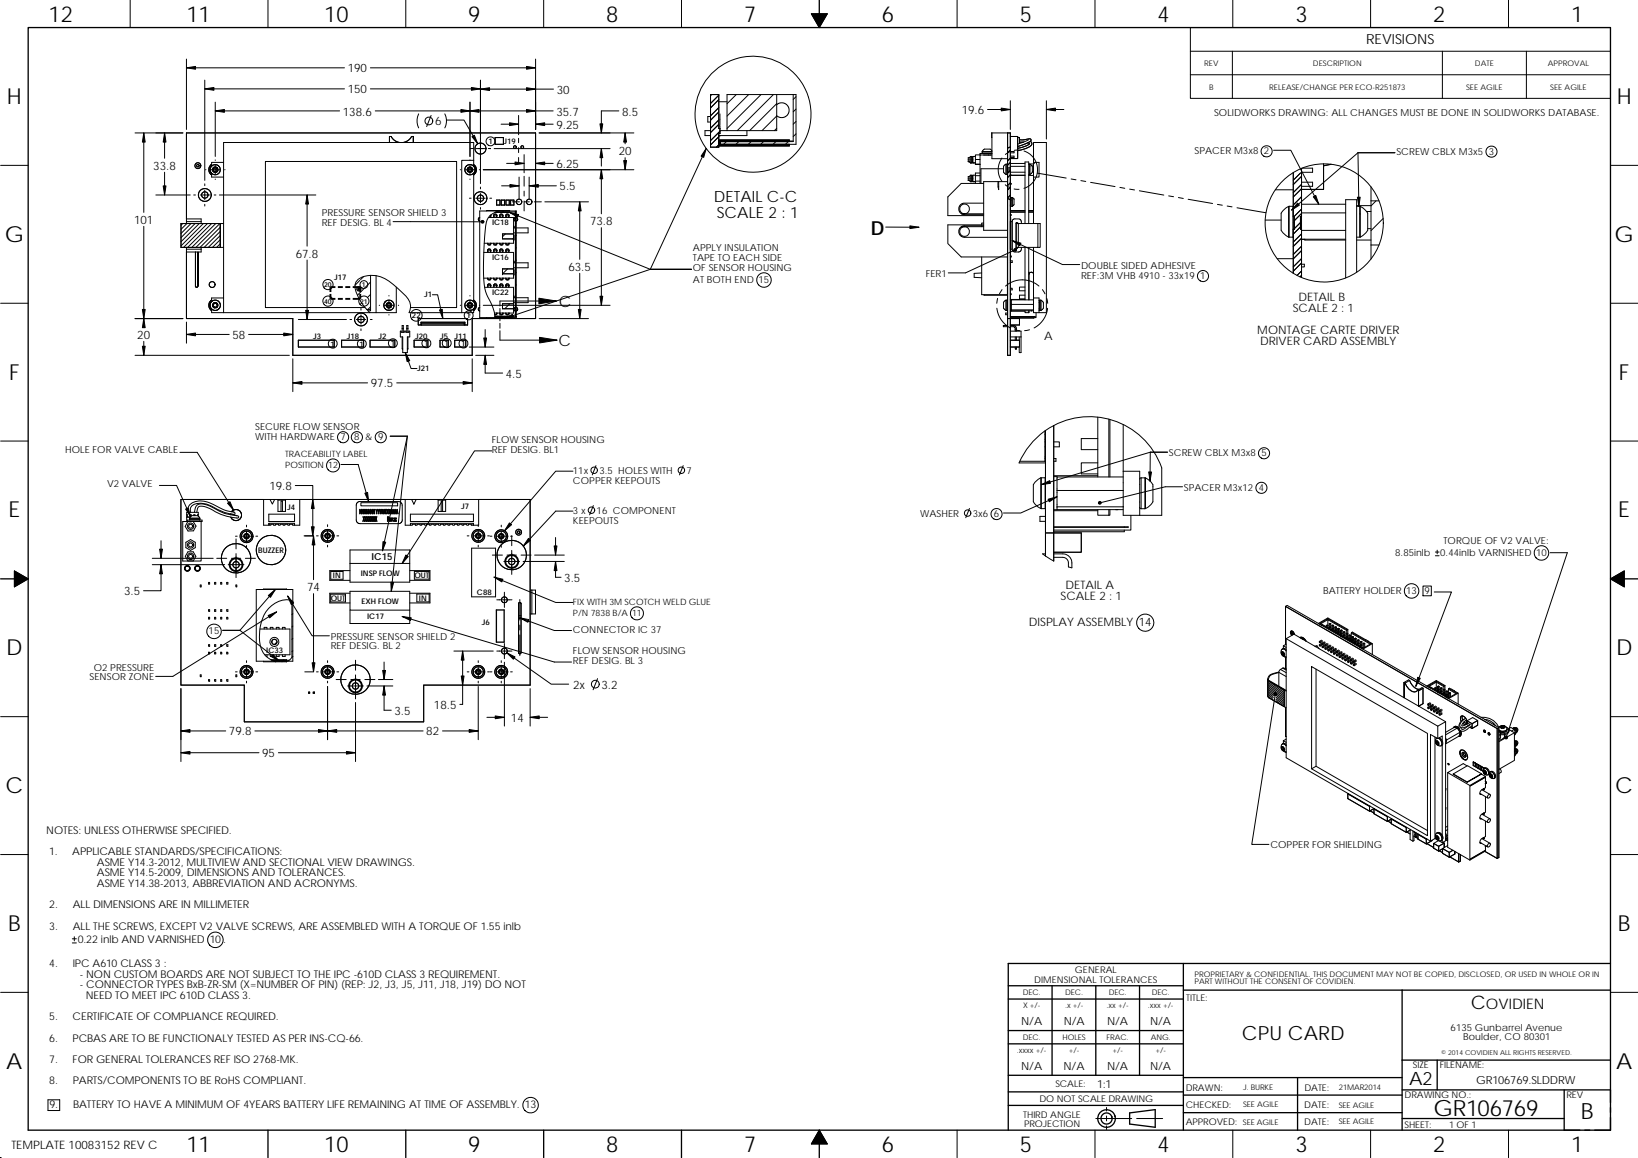
[picture p179: page 1]

SOLIDWORKS DRAWING: ALL CHANGES MUST BE DONE IN SOLIDWORKS DATABASE.

APPLY INSULATION
TAPE TO EACH SIDE
OF SENSOR HOUSING
AT BOTH END

HOLE FOR VALVE CABLE

FIX WITH 3M SCOTCH WELD GLUE
CONNECTOR IC 37
FLOW SENSOR HOUSING
REF DESIG. BL 3

NOTES: UNLESS OTHERWISE SPECIFIED.
1. APPLICABLE STANDARDS/SPECIFICATIONS:

ASME Y14.3-2012, MULTIVIEW AND SECTIONAL VIEW DRAWINGS.
ASME Y14.5-2009, DIMENSIONS AND TOLERANCES.
ASME Y14.38-2013, ABBREVIATION AND ACRONYMS.

2. ALL DIMENSIONS ARE IN MILLIMETER

3. ALL THE SCREWS, EXCEPT V2 VALVE SCREWS, ARE ASSEMBLED WITH A TORQUE OF 1.55 inlb
0.22 inlb AND VARNISHED 10 .
4. IPC A610 CLASS 3 :
- NON CUSTOM BOARDS ARE NOT SUBJECT TO THE IPC -610D CLASS 3 REQUIREMENT.
- CONNECTOR TYPES BxB-ZR-SM (X=NUMBER OF PIN) (REP: J2, J3, J5, J11, J18, J19) DO NOT
NEED TO MEET IPC 610D CLASS 3.
5. CERTIFICATE OF COMPLIANCE REQUIRED.
6. PCBAS ARE TO BE FUNCTIONALY TESTED AS PER INS-CQ-66.

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

DEC. | DEC. | DEC. | DEC.
X +/-N/A | .x +/-N/A | .xx +/-N/A | .xxx +/-N/A

TITLE: CPU CARD | COVIDIEN 6135 Gunbarrel Avenue Boulder, CO 80301 © 2014 COVIDIEN ALL RIGHTS RESERVED.

DEC. | HOLES | FRAC. | ANG.
.xxxx +/-N/A | +/-N/A | +/-N/A | +/-N/A
DO NOT SCALE DRAWING | CHECKED: SEE AGILE | DATE: SEE AGILE | DRAWING NO.: GR106769

7. FOR GENERAL TOLERANCES REF ISO 2768-MK.
8. PARTS/COMPONENTS TO BE RoHS COMPLIANT.

SIZE A2 | FILENAME: GR106769.SLDDRW

SCALE: 1:1 | DRAWN: J. BURKE | DATE: 21MAR2014

BATTERY TO HAVE A MINIMUM OF 4YEARS BATTERY LIFE REMAINING AT TIME OF ASSEMBLY.
