nsynet/electronics_project2/Medtronic_PB560呼吸机开源资料(3D图纸_原理图_说明书_软件代码等)/medtronic-pb560-ventilator-system-file-set-2/Mechanical Part Drawings/2982400/72SP - Supporting Documentation/1400-10010_SCH-LegendSchematicV4.3.PDF

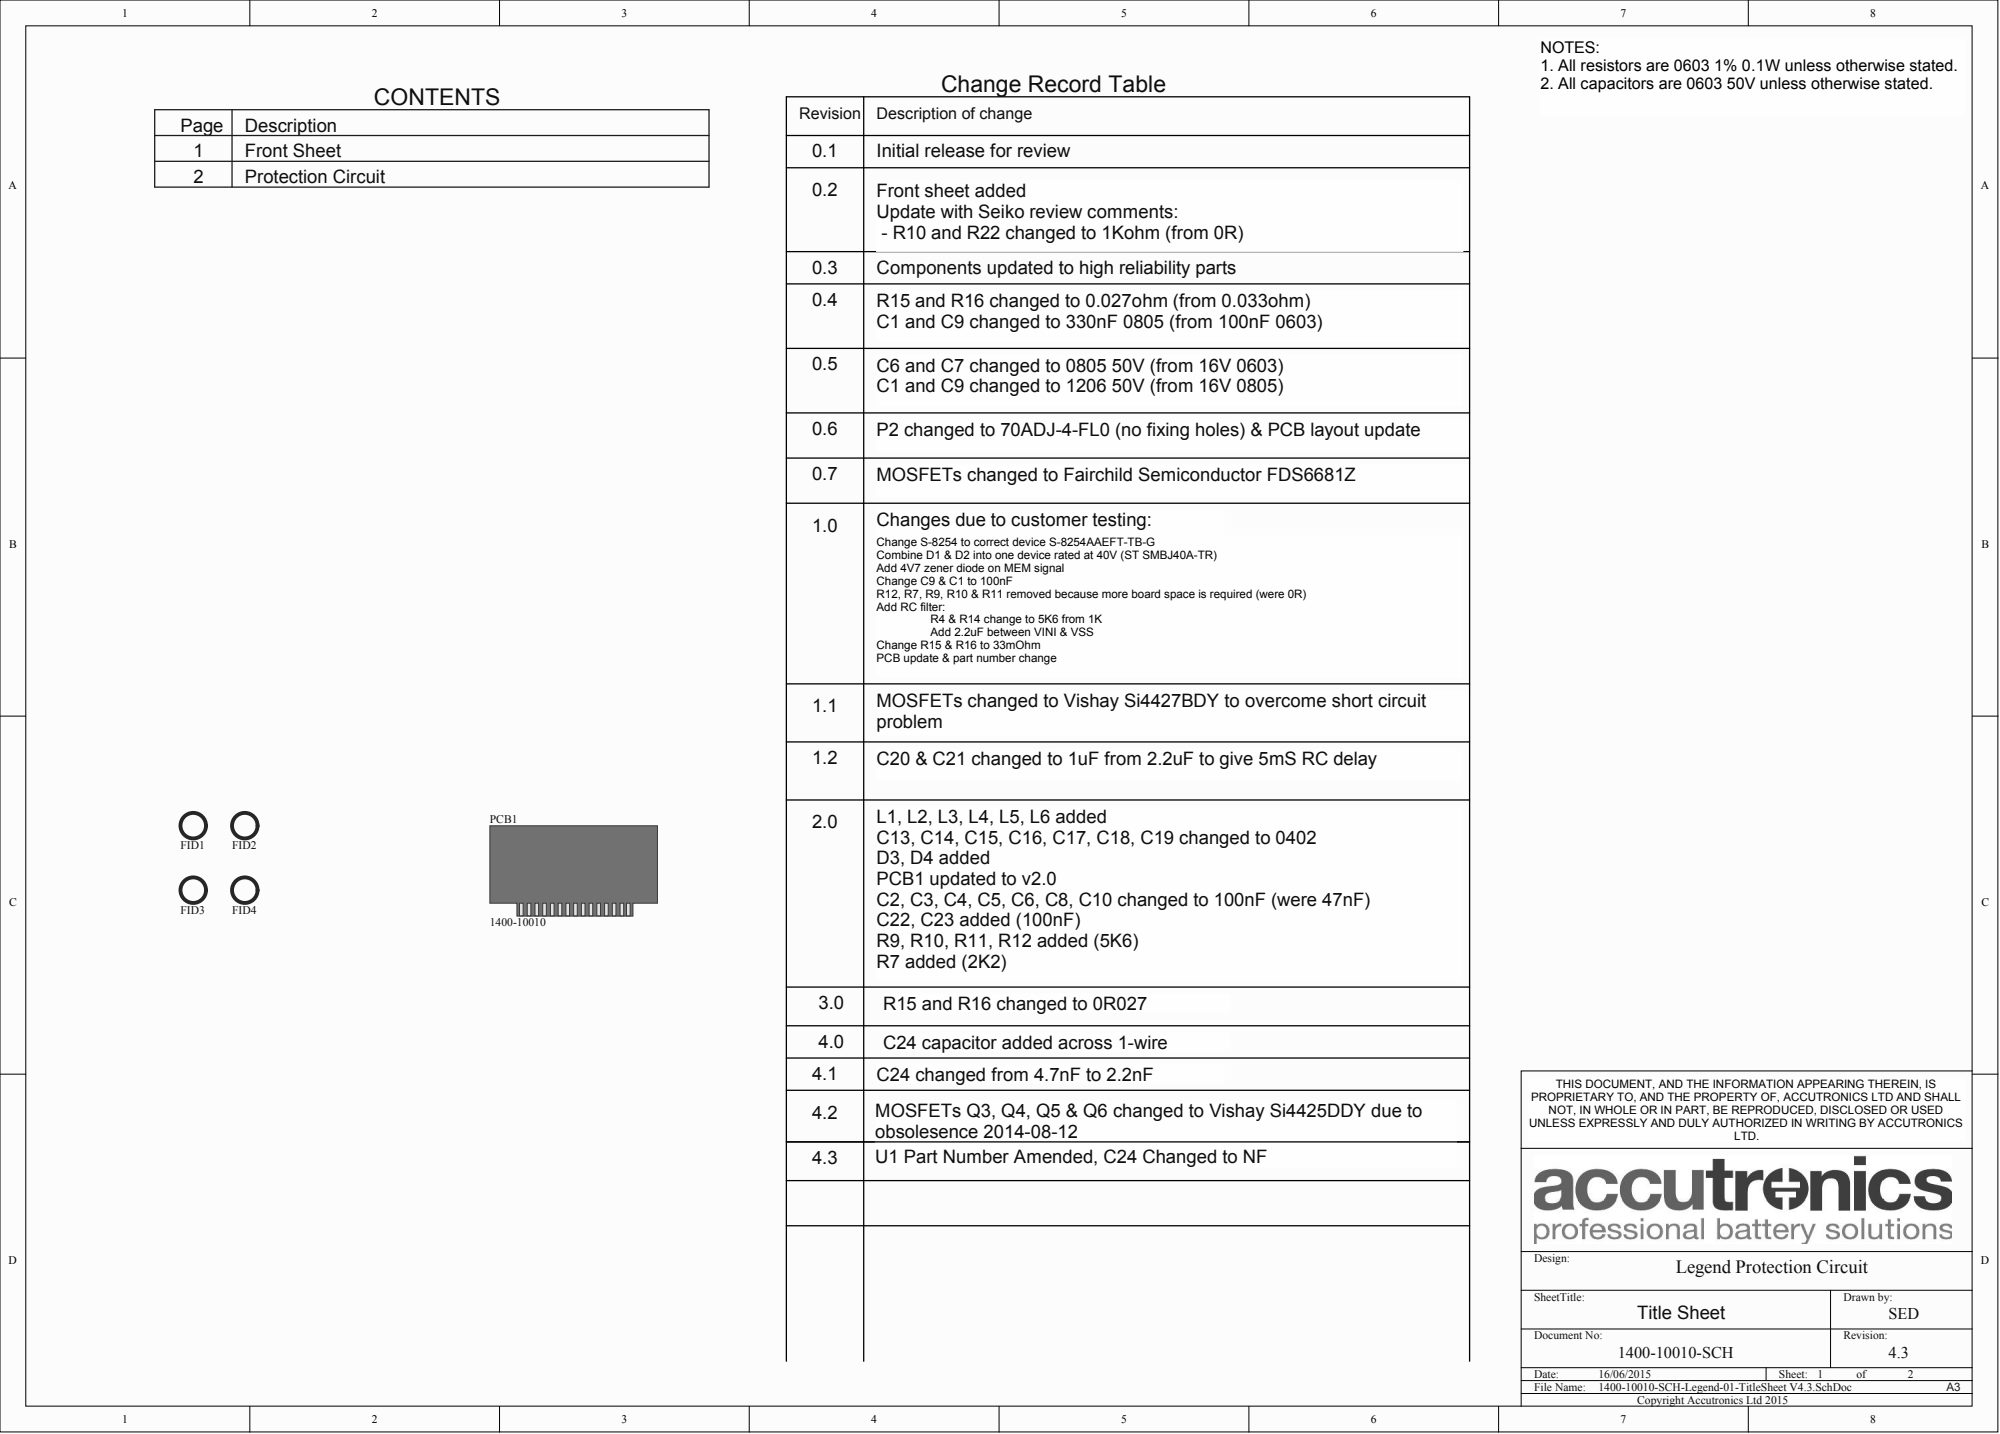
[picture p180: page 1]

NOTES:
1. All resistors are 0603 1% 0.1W unless otherwise stated.
2. All capacitors are 0603 50V unless otherwise stated.

Update
- R10 and R22 changed to 1Kohm (from 0R)

with Seiko review com

C1 and C9 changed to 330nF 0805 (from 100nF 0603)

C6 and C7 changed to 0805 50V (from 16V 0603)
C1 and C9 changed to 1206 50V (from 16V 0805)

fixing holes) & PCB layout update

Change S-8254 to correct device S-8254AAEFT-TB-G
Combine D1 & D2 into one device rated at 40V (ST SMBJ40A-TR)
Add 4V7 zener diode on MEM signal
Change C9 & C1 to 100nF
R12, R7, R9, R10 & R11 removed because more board space is required (were 0R)
Add RC filter:

R4 & R14 change to 5K6 from 1K
Add 2.2uF between VINI & VSS

Change R15 & R16 to 33mOhm
PCB update & part number change

MOSFETs changed to Vishay Si4427BDY to overcome short circuit
problem

from 2.2uF to give 5mS RC delay

C24 capacitor added across 1-wire

THIS DOCUMENT, AND THE INFORMATION APPEARING THEREIN, IS
PROPRIETARY TO, AND THE PROPERTY OF, ACCUTRONICS LTD AND SHALL
NOT, IN WHOLE OR IN PART, BE REPRODUCED, DISCLOSED OR USED
UNLESS EXPRESSLY AND DULY AUTHORIZED IN WRITING BY ACCUTRONICS

File Name: 1400-10010-SCH-Legend-01-TitleSheet V4.3.SchDoc

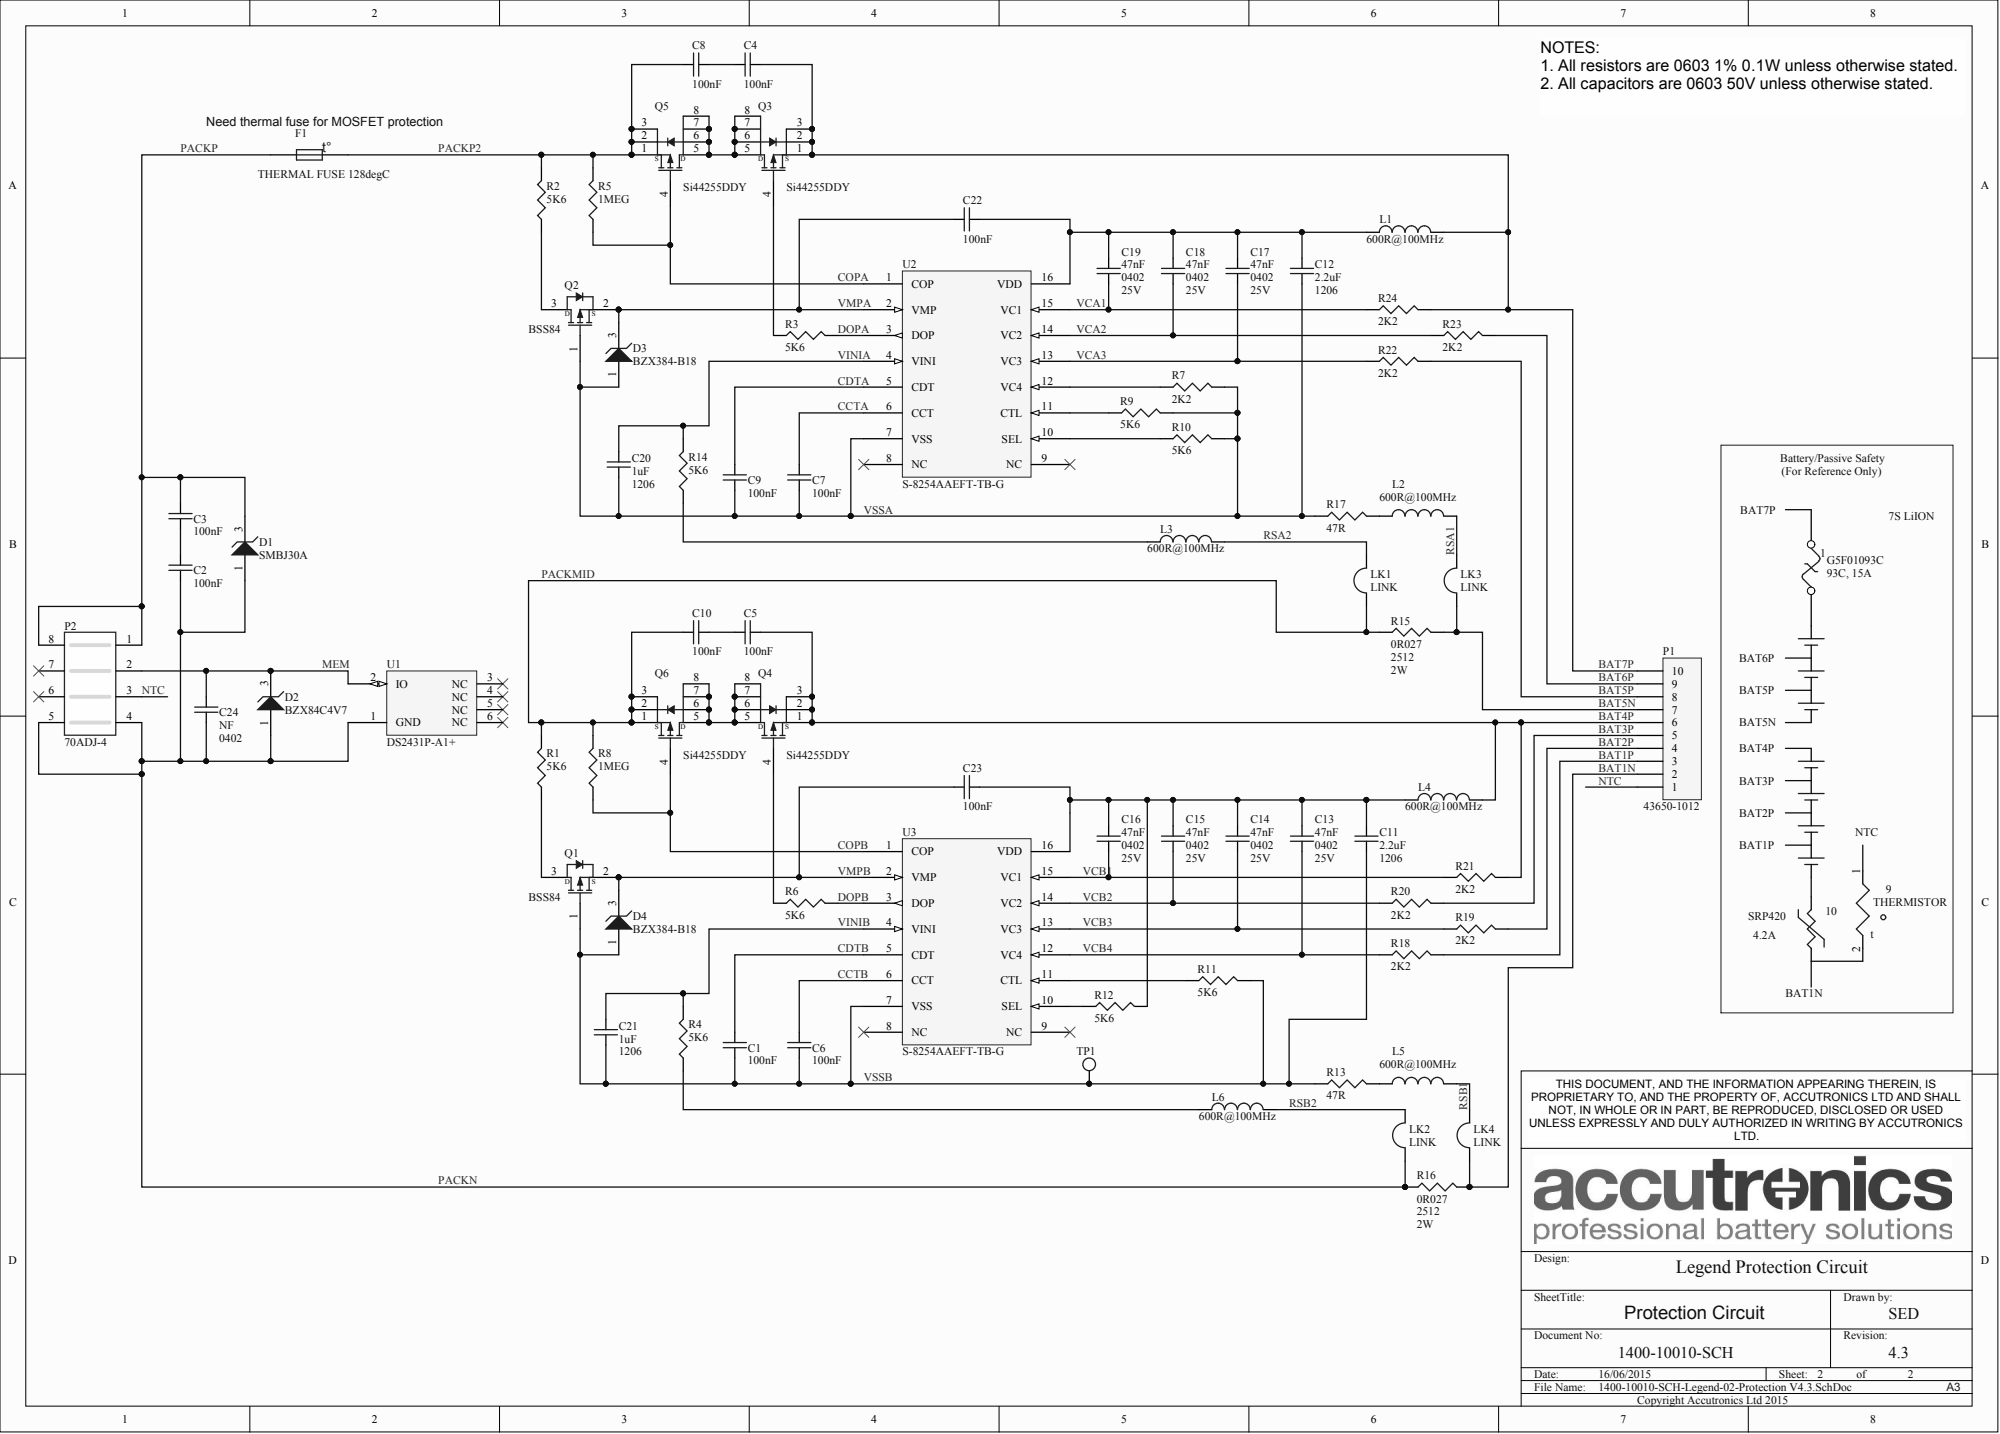
[picture p181: page 2]
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

Need thermal fuse for MOSFET protection

COP 1

VMPA | VMP 2 | VC1 | 15
VINIA | DOP 3 VINI 4 VC4 SEL | VCA2 | | 2K2 | R23

CCTA | CCT 6 | 10

VSS 7

BAT1P

R21 | | BAT1N

COP 1 | VC2 VC3 VC4

VINIB | DOP 3 VINI 4 | 14 VCB2 13 VCB3

CDTB | | CDT 5 | 12 VCB4

CCTB | | CCT 6

VSS 7 | TP1

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

File Name: 1400-10010-SCH-Legend-02-Protection V4.3.SchDoc
