nsynet/electronics_project2/Medtronic_PB560呼吸机开源资料(3D图纸_原理图_说明书_软件代码等)/medtronic-pb560-ventilator-system-file-set-2/Mechanical Part Drawings/2970900/2970900A00.PDF

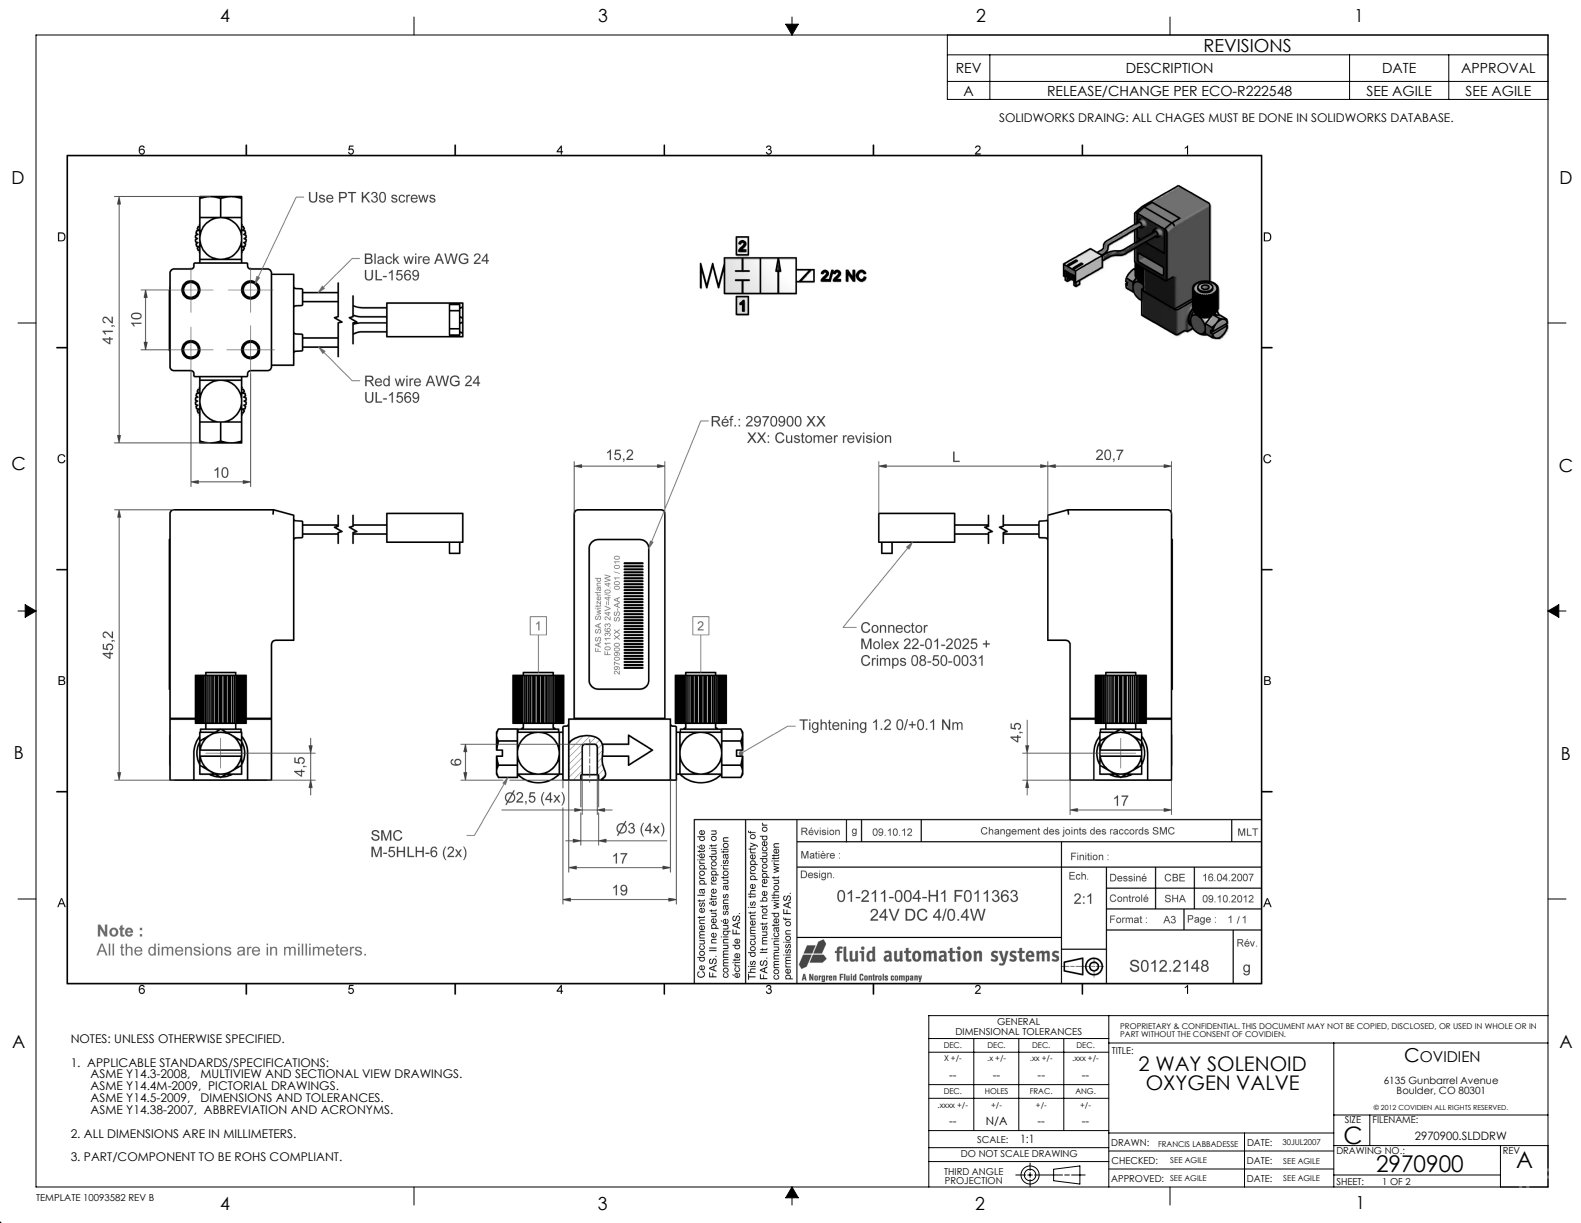
[picture p183: page 1]
2 TEMPLATE 10093582 REV B; .xxxx +/-; THIRD ANGLE; .xxx +/-; SHEET:; DATE:; DRAWING NO.:; DIMENSIONAL TOLERANCES

REVISIONS

REV | DESCRIPTION | DATE | APPROVAL
A | RELEASE/CHANGE PER ECO-R222548 | SEE AGILE | SEE AGILE

SOLIDWORKS DRAING: ALL CHAGES MUST BE DONE IN SOLIDWORKS DATABASE.

PROPRIETARY & CONFIDENTIAL. THIS DOCUMENT MAY NOT BE COPIED, DISCLOSED, OR USED IN WHOLE OR IN
PART WITHOUT THE CONSENT OF COVIDIEN.

NOTES: UNLESS OTHERWISE SPECIFIED.
1. APPLICABLE STANDARDS/SPECIFICATIONS:
ASME Y14.3-2008, MULTIVIEW AND SECTIONAL VIEW DRAWINGS.
ASME Y14.4M-2009, PICTORIAL DRAWINGS.
ASME Y14.5-2009, DIMENSIONS AND TOLERANCES.
ASME Y14.38-2007, ABBREVIATION AND ACRONYMS.
2. ALL DIMENSIONS ARE IN MILLIMETERS.
3. PART/COMPONENT TO BE ROHS COMPLIANT.

TITLE: 2 WAY SOLENOID OXYGEN VALVE | COVIDIEN 6135 Gunbarrel Avenue Boulder, CO 80301 © 2012 COVIDIEN ALL RIGHTS RESERVED. C N/A

SIZE | FILENAME: 2970900.SLDDRW

1:1 SCALE: | DRAWN: FRANCIS LABBADESSE CHECKED: SEE AGILE APPROVED: SEE AGILE | 30JUL2007 DATE: SEE AGILE DATE: SEE AGILE
DO NOT SCALE DRAWING | | | 2970900 | REV A

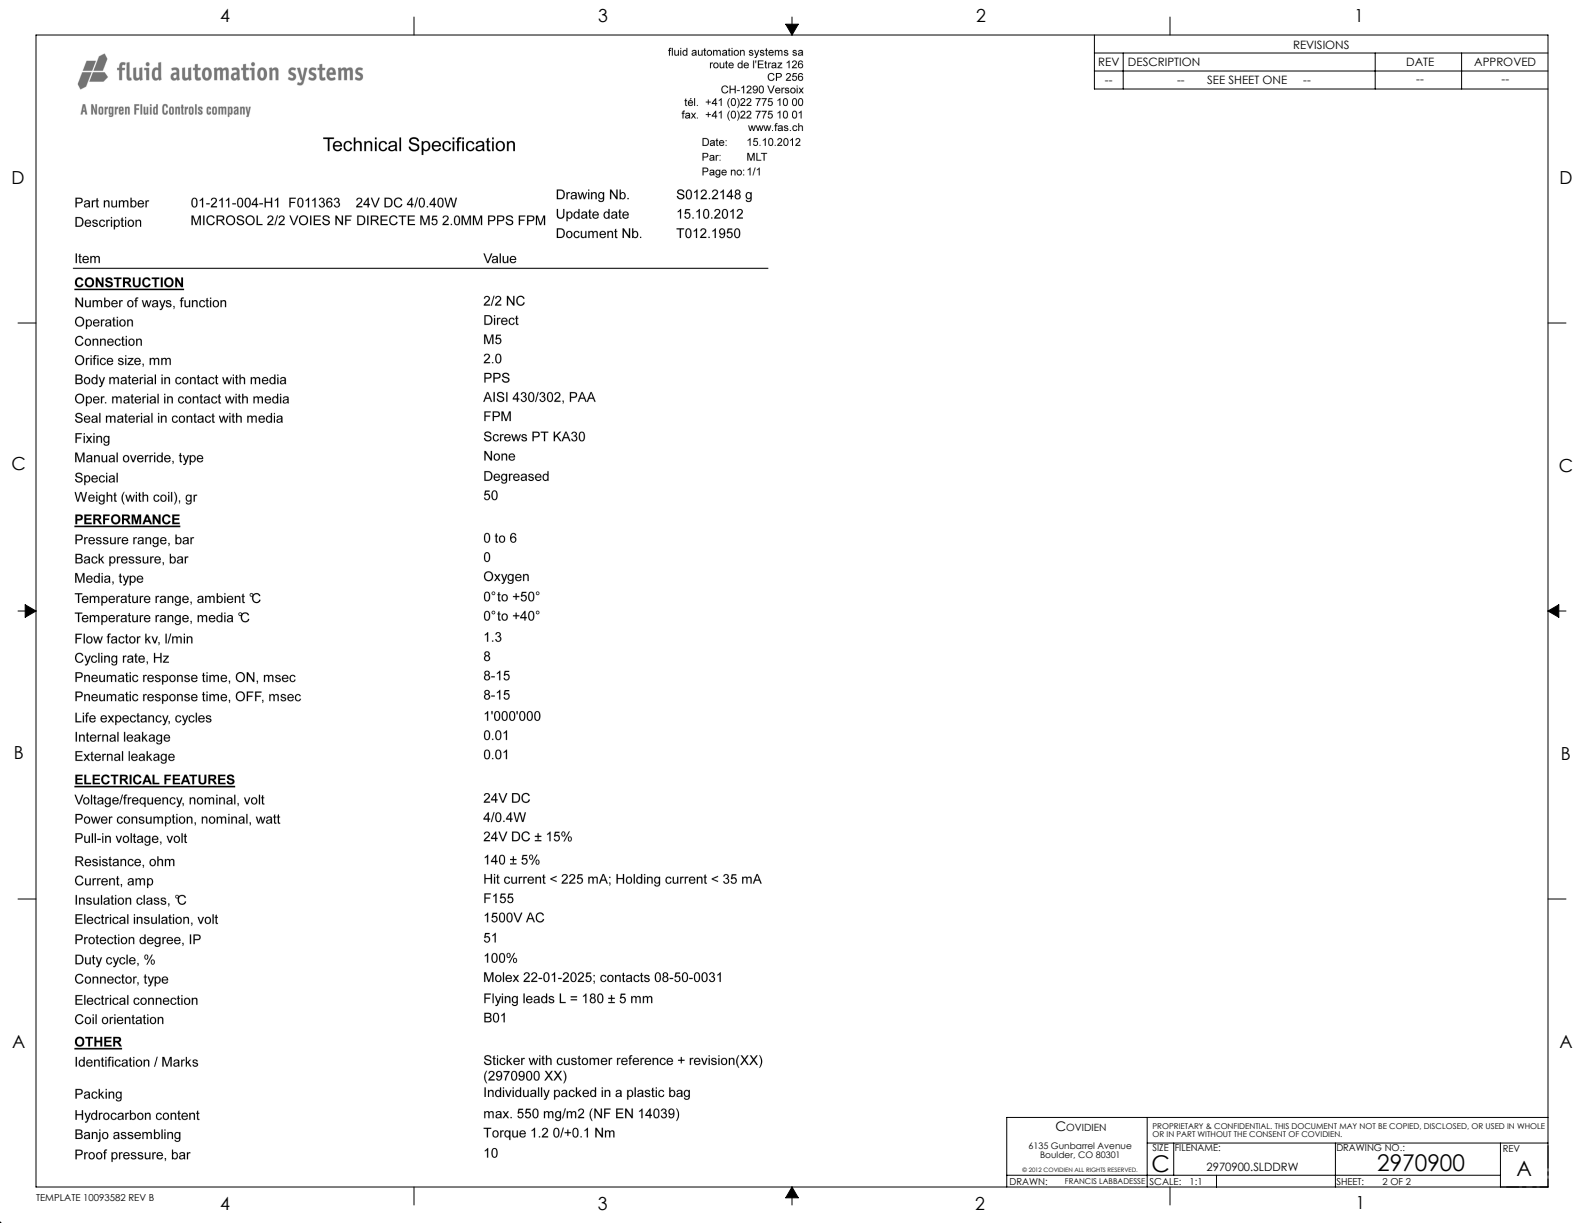
[picture p184: page 2]
2 TEMPLATE 10093582 REV B

REVISIONS

REV | DESCRIPTION | DATE | APPROVED
-- | --SEE SHEET ONE -- | -- | --

COVIDIEN 6135 Gunbarrel Avenue Boulder, CO 80301 © 2012 COVIDIEN ALL RIGHTS RESERVED. | PROPRIETARY & CONFIDENTIAL. THIS DOCUMENT MAY NOT BE COPIED, DISCLOSED, OR USED IN WHOLE OR IN PART WITHOUT THE CONSENT OF COVIDIEN.

SIZE C | FILENAME: 2970900.SLDDRW | DRAWING NO.: 2970900 | REV A

DRAWN: FRANCIS LABBADESSE | SCALE: 1:1 | | SHEET: 2 OF 2
