nsynet/electronics_project2/Medtronic_PB560呼吸机开源资料(3D图纸_原理图_说明书_软件代码等)/medtronic-pb560-ventilator-system-file-set-2/Mechanical Part Drawings/3810200/3810200A00.PDF

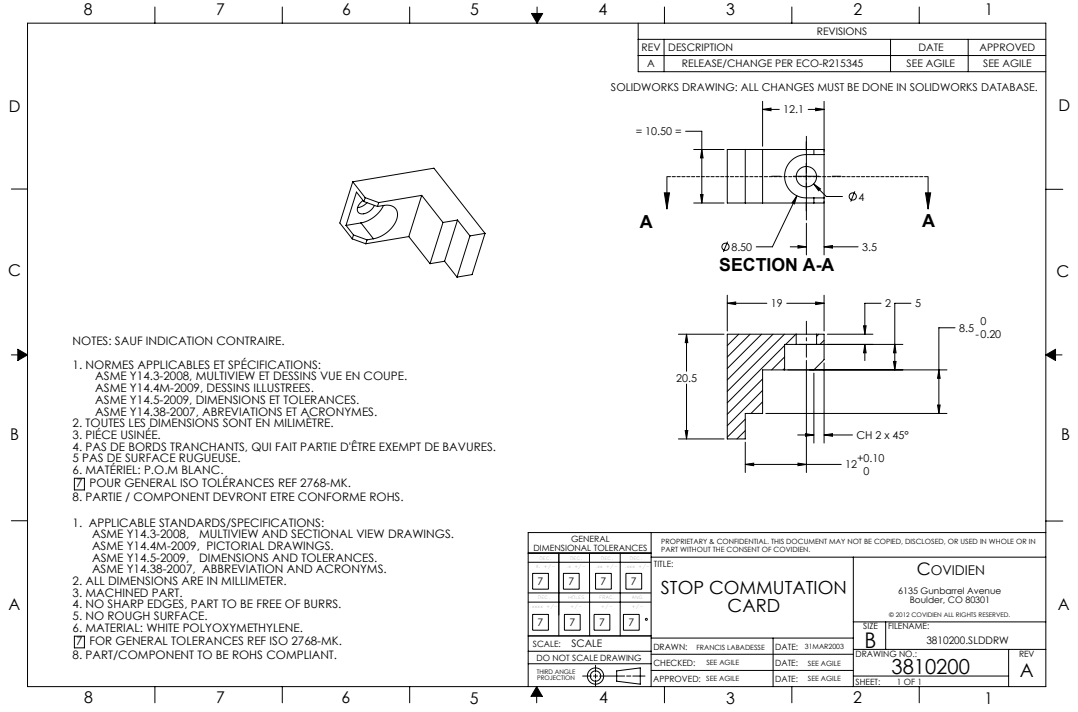
[picture p188: page 1]
SECTION A-A; POUR GENERAL ISO TOLÉRANCES REF 2768-MK.; FOR GENERAL TOLERANCES REF ISO 2768-MK.; FRANCIS LABADESSE; 31MAR2003; THIRD ANGLE; SHEET:; DATE:; DRAWING NO.:; SEE AGILE; .xxxx +/-

REVISIONS

REV | DESCRIPTION | DATE | APPROVED
A | RELEASE/CHANGE PER ECO-R215345 | SEE AGILE | SEE AGILE

SOLIDWORKS DRAWING: ALL CHANGES MUST BE DONE IN SOLIDWORKS DATABASE.

NOTES: SAUF INDICATION CONTRAIRE.
1. NORMES APPLICABLES ET SPÉCIFICATIONS:
ASME Y14.3-2008, MULTIVIEW ET DESSINS VUE EN COUPE.
ASME Y14.4M-2009, DESSINS ILLUSTREES.
ASME Y14.5-2009, DIMENSIONS ET TOLERANCES.
ASME Y14.38-2007, ABREVIATIONS ET ACRONYMES.
2. TOUTES LES DIMENSIONS SONT EN MILIMÈTRE.

3. PIÉCE USINÉE.
4. PAS DE BORDS TRANCHANTS, QUI FAIT PARTIE D'ÊTRE EXEMPT DE BAVURES.
5 PAS DE SURFACE RUGUEUSE.
6. MATÉRIEL: P.O.M BLANC.
8. PARTIE / COMPONENT DEVRONT ETRE CONFORME ROHS.
1. APPLICABLE STANDARDS/SPECIFICATIONS:
ASME Y14.3-2008, MULTIVIEW AND SECTIONAL VIEW DRAWINGS.
ASME Y14.4M-2009, PICTORIAL DRAWINGS.
ASME Y14.5-2009, DIMENSIONS AND TOLERANCES.
ASME Y14.38-2007, ABBREVIATION AND ACRONYMS.
2. ALL DIMENSIONS ARE IN MILLIMETER.
3. MACHINED PART.

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

DEC. X. +/- | DEC. DEC. DEC. .x +/-.xx +/-.xxx +/-

TITLE: STOP COMMUTATION CARD | COVIDIEN 6135 Gunbarrel Avenue Boulder, CO 80301 © 2012 COVIDIEN ALL RIGHTS RESERVED.

4. NO SHARP EDGES, PART TO BE FREE OF BURRS.
5. NO ROUGH SURFACE.
6. MATERIAL: WHITE POLYOXYMETHYLENE.
8. PART/COMPONENT TO BE ROHS COMPLIANT.

SIZE B | FILENAME: 3810200.SLDDRW

DO NOT SCALE DRAWING | | 3810200 | REV A
