nsynet/electronics_project2/Medtronic_PB560呼吸机开源资料(3D图纸_原理图_说明书_软件代码等)/medtronic-pb560-ventilator-system-file-set-2/Electronic PCBAs/GR106769_CPU_PCBA/SCH/10125623A00.sch

## EAGLE design Medtronic_PB560呼吸机开源资料(3D图纸_原理图_说明书_软件代码等)/medtronic-pb560-ventilator-system-file-set-2/Electronic PCBAs/GR106769_CPU_PCBA/SCH/10125623A00.sch (2023-12-02)

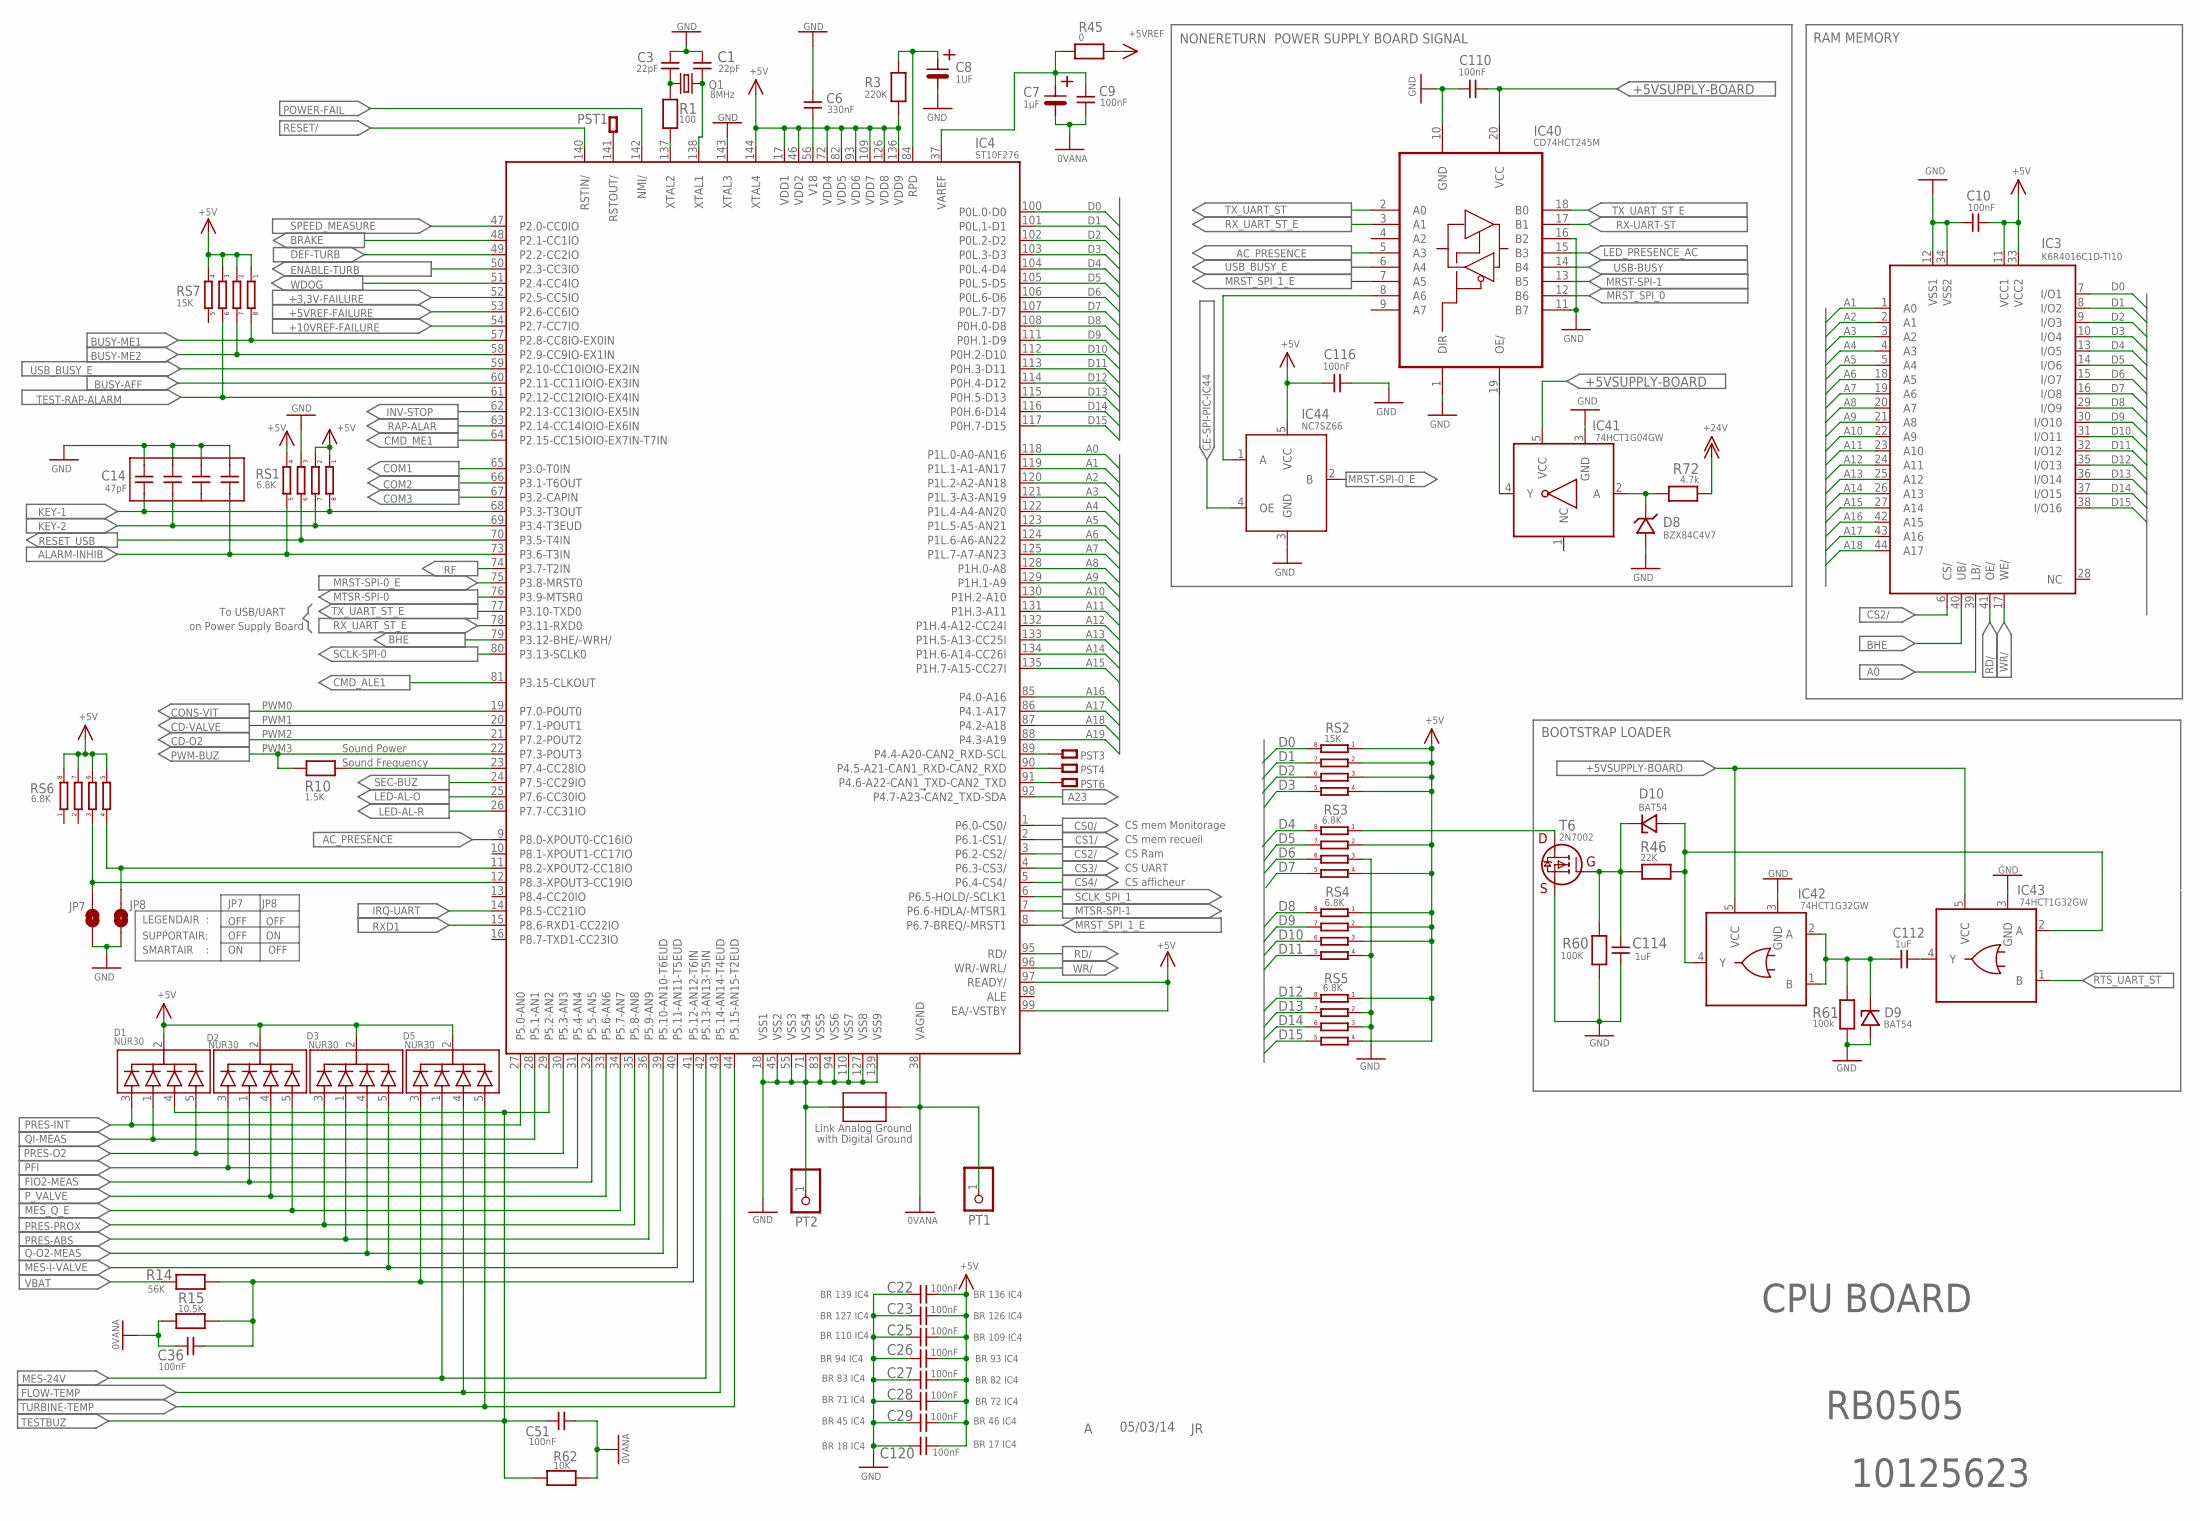
[picture p190: schematic 10125623A00.sch, sheet 1]

Parts:
C1, C3: 22pF; C0603
C6: 330nF; C0805
C7: 1µF; TANTALB
C8: 1UF; TANTALB
C9, C10, C22, C23, C25, C26, C27, C28, C29, C36, C51, C110, C116, C120: 100nF; C0805
C14: 47pF; RESEAU2
C112, C114: 1uF; C0603
D1, D2, D3, D5: NUR30; 5SOT23
D8: BZX84C4V7; SOT23DIO
D9, D10: BAT54; SOT23DIO
IC3: K6R4016C1D-TI10; TSOPIIZ4
IC4: ST10F276; TQFP144
IC40: CD74HCT245M; SO20
IC41: 74HCT1G04GW; SOT23-5
IC42, IC43: 74HCT1G32GW; SOT23-5
IC44: NC7SZ66; SOT23-5
JP7, JP8: JUMP_0U; 0805
JPL1: LIAISON_MASSES; LIAISONS_MASSES
PST1, PST3, PST4, PST6: PAST01; 1X01
PT1, PT2: PINHD-1X1; 1X01
Q1: 8MHz; SM49
R1: 100; R0805
R3: 220K; R0805
R10: 1.5K; R0805
R14: 56K; R0805
R15: 10.5K; R0805
R45: 0; R0805
R46: 22K; R0805
R60: 100K; R0805
R61: 100k; R0805
R62: 10K; R0805
R72: 4.7k; R0805
RS1, RS3, RS4, RS5, RS6: 6.8K; BCN16_4_
RS2, RS7: 15K; BCN16_4_
T6: 2N7002; SOT23MOS

Connections:
0VANA: C7.-, C9.1, C36.2, C51.2, IC4.38 (VAGND), JPL1.2, PT1.1, R15.1, R62.1
+3,3V-FAILURE: IC4.52 (P2.5-CC5IO)
+5V: C10.1, C22.2, C23.2, C25.2, C26.2, C27.2, C28.2, C29.2, C116.2, C120.2, D1.2, D2.2, D3.2, D5.2, IC3.11 (VCC1), IC3.33 (VCC2), IC4.17 (VDD1), IC4.46 (VDD2), IC4.72 (VDD4), IC4.82 (VDD5), IC4.93 (VDD6), IC4.97 (READY/), IC4.99 (EA/-VSTBY), IC4.109 (VDD7), IC4.126 (VDD8), IC4.136 (VDD9), IC4.144 (XTAL4), IC44.5 (VCC), R3.2, RS1.1, RS1.2, RS1.4, RS2.1, RS2.2, RS2.3, RS2.4, RS3.2, RS3.4, RS4.1, RS4.2, RS4.3, RS5.1, RS5.4, RS6.5, RS6.6, RS6.7, RS6.8, RS7.1, RS7.2, RS7.3, RS7.4
+5VREF: R45.2
+5VREF-FAILURE: IC4.53 (P2.6-CC6IO)
+5VSUPPLY-BOARD: C110.1, IC40.20 (VCC), IC41.5 (VCC), IC42.5 (VCC), IC43.5 (VCC)
+10VREF-FAILURE: IC4.54 (P2.7-CC7IO)
+24V: R72.1
A0: IC3.39 (LB/), IC4.118 (P1L.0-A0-AN16)
A1: IC3.1 (A0), IC4.119 (P1L.1-A1-AN17)
A2: IC3.2 (A1), IC4.120 (P1L.2-A2-AN18)
A3: IC3.3 (A2), IC4.121 (P1L.3-A3-AN19)
A4: IC3.4 (A3), IC4.122 (P1L.4-A4-AN20)
A5: IC3.5 (A4), IC4.123 (P1L.5-A5-AN21)
A6: IC3.18 (A5), IC4.124 (P1L.6-A6-AN22)
A7: IC3.19 (A6), IC4.125 (P1L.7-A7-AN23)
A8: IC3.20 (A7), IC4.128 (P1H.0-A8)
A9: IC3.21 (A8), IC4.129 (P1H.1-A9)
A10: IC3.22 (A9), IC4.130 (P1H.2-A10)
A11: IC3.23 (A10), IC4.131 (P1H.3-A11)
A12: IC3.24 (A11), IC4.132 (P1H.4-A12-CC24I)
A13: IC3.25 (A12), IC4.133 (P1H.5-A13-CC25I)
A14: IC3.26 (A13), IC4.134 (P1H.6-A14-CC26I)
A15: IC3.27 (A14), IC4.135 (P1H.7-A15-CC27I)
A16: IC3.42 (A15), IC4.85 (P4.0-A16)
A17: IC3.43 (A16), IC4.86 (P4.1-A17)
A18: IC3.44 (A17), IC4.87 (P4.2-A18)
A19: IC4.88 (P4.3-A19)
A23: IC4.92 (P4.7-A23-CAN2_TXD-SDA)
AC_PRESENCE: IC4.9 (P8.0-XPOUT0-CC16IO), IC40.5 (A3)
ALARM-INHIB: C14.8, IC4.73 (P3.6-T3IN), RS1.5
BHE: IC3.40 (UB/), IC4.79 (P3.12-BHE/-WRH/)
BLOAD: RS3.1, T6.D
BRAKE: IC4.48 (P2.1-CC1IO)
BUSY-AFF: IC4.60 (P2.11-CC11IOIO-EX3IN)
BUSY-ME1: IC4.57 (P2.8-CC8IO-EX0IN), RS7.8
BUSY-ME2: IC4.58 (P2.9-CC9IO-EX1IN), RS7.7
CD-O2: IC4.21 (P7.2-POUT2)
CD-VALVE: IC4.20 (P7.1-POUT1)
CE-SPI-PIC-IC44: IC44.4 (OE)
CMD_ALE1: IC4.81 (P3.15-CLKOUT)
CMD_ME1: IC4.64 (P2.15-CC15IOIO-EX7IN-T7IN)
COM1: IC4.65 (P3.0-T0IN)
COM2: IC4.66 (P3.1-T6OUT)
COM3: IC4.67 (P3.2-CAPIN)
CONS-VIT: IC4.19 (P7.0-POUT0)
CS0/: IC4.1 (P6.0-CS0/)
CS1/: IC4.2 (P6.1-CS1/)
CS2/: IC3.6 (CS/), IC4.3 (P6.2-CS2/)
CS3/: IC4.4 (P6.3-CS3/)
CS4/: IC4.5 (P6.4-CS4/)
D0: IC3.7 (I/O1), IC4.100 (P0L.0-D0), RS2.8
D1: IC3.8 (I/O2), IC4.101 (P0L.1-D1), RS2.7
D2: IC3.9 (I/O3), IC4.102 (P0L.2-D2), RS2.6
D3: IC3.10 (I/O4), IC4.103 (P0L.3-D3), RS2.5
D4: IC3.13 (I/O5), IC4.104 (P0L.4-D4), RS3.8
D5: IC3.14 (I/O6), IC4.105 (P0L.5-D5), RS3.7
D6: IC3.15 (I/O7), IC4.106 (P0L.6-D6), RS3.6
D7: IC3.16 (I/O8), IC4.107 (P0L.7-D7), RS3.5
D8: IC3.29 (I/O9), IC4.108 (P0H.0-D8), RS4.8
D9: IC3.30 (I/O10), IC4.111 (P0H.1-D9), RS4.7
D10: IC3.31 (I/O11), IC4.112 (P0H.2-D10), RS4.6
D11: IC3.32 (I/O12), IC4.113 (P0H.3-D11), RS4.5
D12: IC3.35 (I/O13), IC4.114 (P0H.4-D12), RS5.8
D13: IC3.36 (I/O14), IC4.115 (P0H.5-D13), RS5.7
D14: IC3.37 (I/O15), IC4.116 (P0H.6-D14), RS5.6
D15: IC3.38 (I/O16), IC4.117 (P0H.7-D15), RS5.5
DEF-TURB: IC4.49 (P2.2-CC2IO)
ENABLE-TURB: IC4.50 (P2.3-CC3IO)
FIO2-MEAS: D2.1 (3), IC4.32 (P5.5-AN5)
FLOW-TEMP: D5.4, IC4.43 (P5.14-AN14-T4EUD)
GND: C1.2, C3.2, C6.2, C8.-, C10.2, C14.1, C14.2, C14.3, C14.4, C22.1, C23.1, C25.1, C26.1, C27.1, C28.1, C29.1, C110.2, C114.1, C116.1, C120.1, D8.1 (A), D9.1 (A), IC3.12 (VSS1), IC3.34 (VSS2), IC4.18 (VSS1), IC4.45 (VSS2), IC4.55 (VSS3), IC4.71 (VSS4), IC4.83 (VSS5), IC4.94 (VSS6), IC4.110 (VSS7), IC4.127 (VSS8), IC4.139 (VSS9), IC4.143 (XTAL3), IC40.1 (DIR), IC40.10 (GND), IC40.11 (B7), IC40.16 (B2), IC41.3 (GND), IC42.3 (GND), IC43.3 (GND), IC44.3 (GND), JP7.1, JP8.1, JPL1.1, PT2.1, R60.1, R61.2, RS1.3, RS3.3, RS4.4, RS5.2, RS5.3, T6.S
INV-STOP: IC4.62 (P2.13-CC13IOIO-EX5IN)
IRQ-UART: IC4.14 (P8.5-CC21IO)
KEY-1: C14.5, IC4.68 (P3.3-T3OUT), RS1.8
KEY-2: C14.6, IC4.69 (P3.4-T3EUD), RS1.7
LED-AL-O: IC4.25 (P7.6-CC30IO)
LED-AL-R: IC4.26 (P7.7-CC31IO)
LED_PRESENCE_AC: IC40.15 (B3)
MES-24V: D5.1 (3), IC4.42 (P5.13-AN13-T5IN)
MES-I-VALVE: D3.5, IC4.40 (P5.11-AN11-T5EUD)
MES_Q_E: D2.5, IC4.34 (P5.7-AN7)
MRST-SPI-0_E: IC4.75 (P3.8-MRST0), IC44.2 (B)
MRST-SPI-1: IC40.13 (B5)
MRST_SPI_0: IC40.12 (B6)
MRST_SPI_1_E: IC4.8 (P6.7-BREQ/-MRST1), IC40.7 (A5)
MTSR-SPI-0: IC4.76 (P3.9-MTSR0)
MTSR-SPI-1: IC4.7 (P6.6-HDLA/-MTSR1)
unnamed: C3.1, Q1.1, R1.1
unnamed: IC4.137 (XTAL2), R1.2
unnamed: C8.+, IC4.84 (RPD), R3.1
unnamed: IC4.23 (P7.4-CC28IO), R10.2
unnamed: IC4.141 (RSTOUT/), PST1.1
unnamed: IC4.89 (P4.4-A20-CAN2_RXD-SCL), PST3.1
unnamed: IC4.90 (P4.5-A21-CAN1_RXD-CAN2_RXD), PST4.1
unnamed: IC4.91 (P4.6-A22-CAN1_TXD-CAN2_TXD), PST6.1
unnamed: C7.+, C9.2, IC4.37 (VAREF), R45.1
unnamed: C1.1, IC4.138 (XTAL1), Q1.2
unnamed: IC4.11 (P8.2-XPOUT2-CC18IO), JP8.2, RS6.4
unnamed: C36.1, D5.3 (1), IC4.41 (P5.12-AN12-T6IN), R14.2, R15.2
unnamed: IC4.12 (P8.3-XPOUT3-CC19IO), JP7.2, RS6.3
unnamed: D10.1 (A), IC42.4 (Y), IC43.2 (A), R46.2
unnamed: IC40.19 (OE/), IC41.4 (Y)
unnamed: D8.3 (K), IC41.2 (A), R72.2
unnamed: C112.2, IC43.4 (Y)
unnamed: C112.1, D9.3 (K), IC42.1 (B), IC42.2 (A), R61.1
unnamed: IC40.8 (A6), IC44.1 (A)
unnamed: C6.1, IC4.56 (V18)
unnamed: C114.2, D10.3 (K), R46.1, R60.2, T6.G
PFI: D2.3 (1), IC4.31 (P5.4-AN4)
POWER-FAIL: IC4.142 (NMI/)
PRES-ABS: D3.1 (3), IC4.36 (P5.9-AN9)
PRES-INT: D1.3 (1), IC4.27 (P5.0-AN0)
PRES-O2: D1.5, IC4.30 (P5.3-AN3)
PRES-PROX: D3.3 (1), IC4.35 (P5.8-AN8)
PWM-BUZ: IC4.22 (P7.3-POUT3), R10.1
P_VALVE: D2.4, IC4.33 (P5.6-AN6)
Q-O2-MEAS: D3.4, IC4.39 (P5.10-AN10-T6EUD)
QI-MEAS: D1.1 (3), IC4.28 (P5.1-AN1)
RAP-ALAR: IC4.63 (P2.14-CC14IOIO-EX6IN)
RD/: IC3.41 (OE/), IC4.95 (RD/)
RESET/: IC4.140 (RSTIN/)
RESET_USB: IC4.70 (P3.5-T4IN), RS1.6
RF: IC4.74 (P3.7-T2IN)
RTS_UART_ST: IC43.1 (B)
RX-UART-ST: IC40.17 (B1)
RXD1: IC4.15 (P8.6-RXD1-CC22IO)
RX_UART_ST_E: IC4.78 (P3.11-RXD0), IC40.3 (A1)
SCLK-SPI-0: IC4.80 (P3.13-SCLK0)
SCLK_SPI_1: IC4.6 (P6.5-HOLD/-SCLK1)
SEC-BUZ: IC4.24 (P7.5-CC29IO)
SPEED_MEASURE: IC4.47 (P2.0-CC0IO)
TEST-RAP-ALARM: IC4.61 (P2.12-CC12IOIO-EX4IN), RS7.6
TESTBUZ: C51.1, D1.4, IC4.29 (P5.2-AN2), R62.2
TURBINE-TEMP: D5.5, IC4.44 (P5.15-AN15-T2EUD)
TX_UART_ST: IC40.2 (A0)
TX_UART_ST_E: IC4.77 (P3.10-TXD0), IC40.18 (B0)
USB-BUSY: IC40.14 (B4)
USB_BUSY_E: IC4.59 (P2.10-CC10IOIO-EX2IN), IC40.6 (A4)
VBAT: R14.1
WDOG: IC4.51 (P2.4-CC4IO)
WR/: IC3.17 (WE/), IC4.96 (WR/-WRL/)

Notes on the sheet:
RAM MEMORY
BR 139 IC4
BR 127 IC4
BR 110 IC4
BR 94 IC4
BR 83 IC4
BR 71 IC4
BR 45 IC4
BR 136 IC4
BR 126 IC4
BR 109 IC4
BR 93 IC4
BR 82 IC4
BR 72 IC4
BR 46 IC4
Link Analog Ground
with Digital Ground
CPU BOARD
RB0505
CS afficheur
CS mem Monitorage
CS mem recueil
CS Ram
PWM0
PWM2
PWM3
Sound Frequency
Sound Power
10125623
BR 18 IC4
BR 17 IC4
CS UART
To USB/UART
on Power Supply Board
05/03/14
PWM1
JP7 JP8
SMARTAIR :
LEGENDAIR :
SUPPORTAIR:
OFF OFF
OFF ON
ON OFF
BOOTSTRAP LOADER
NONERETURN POWER SUPPLY BOARD SIGNAL

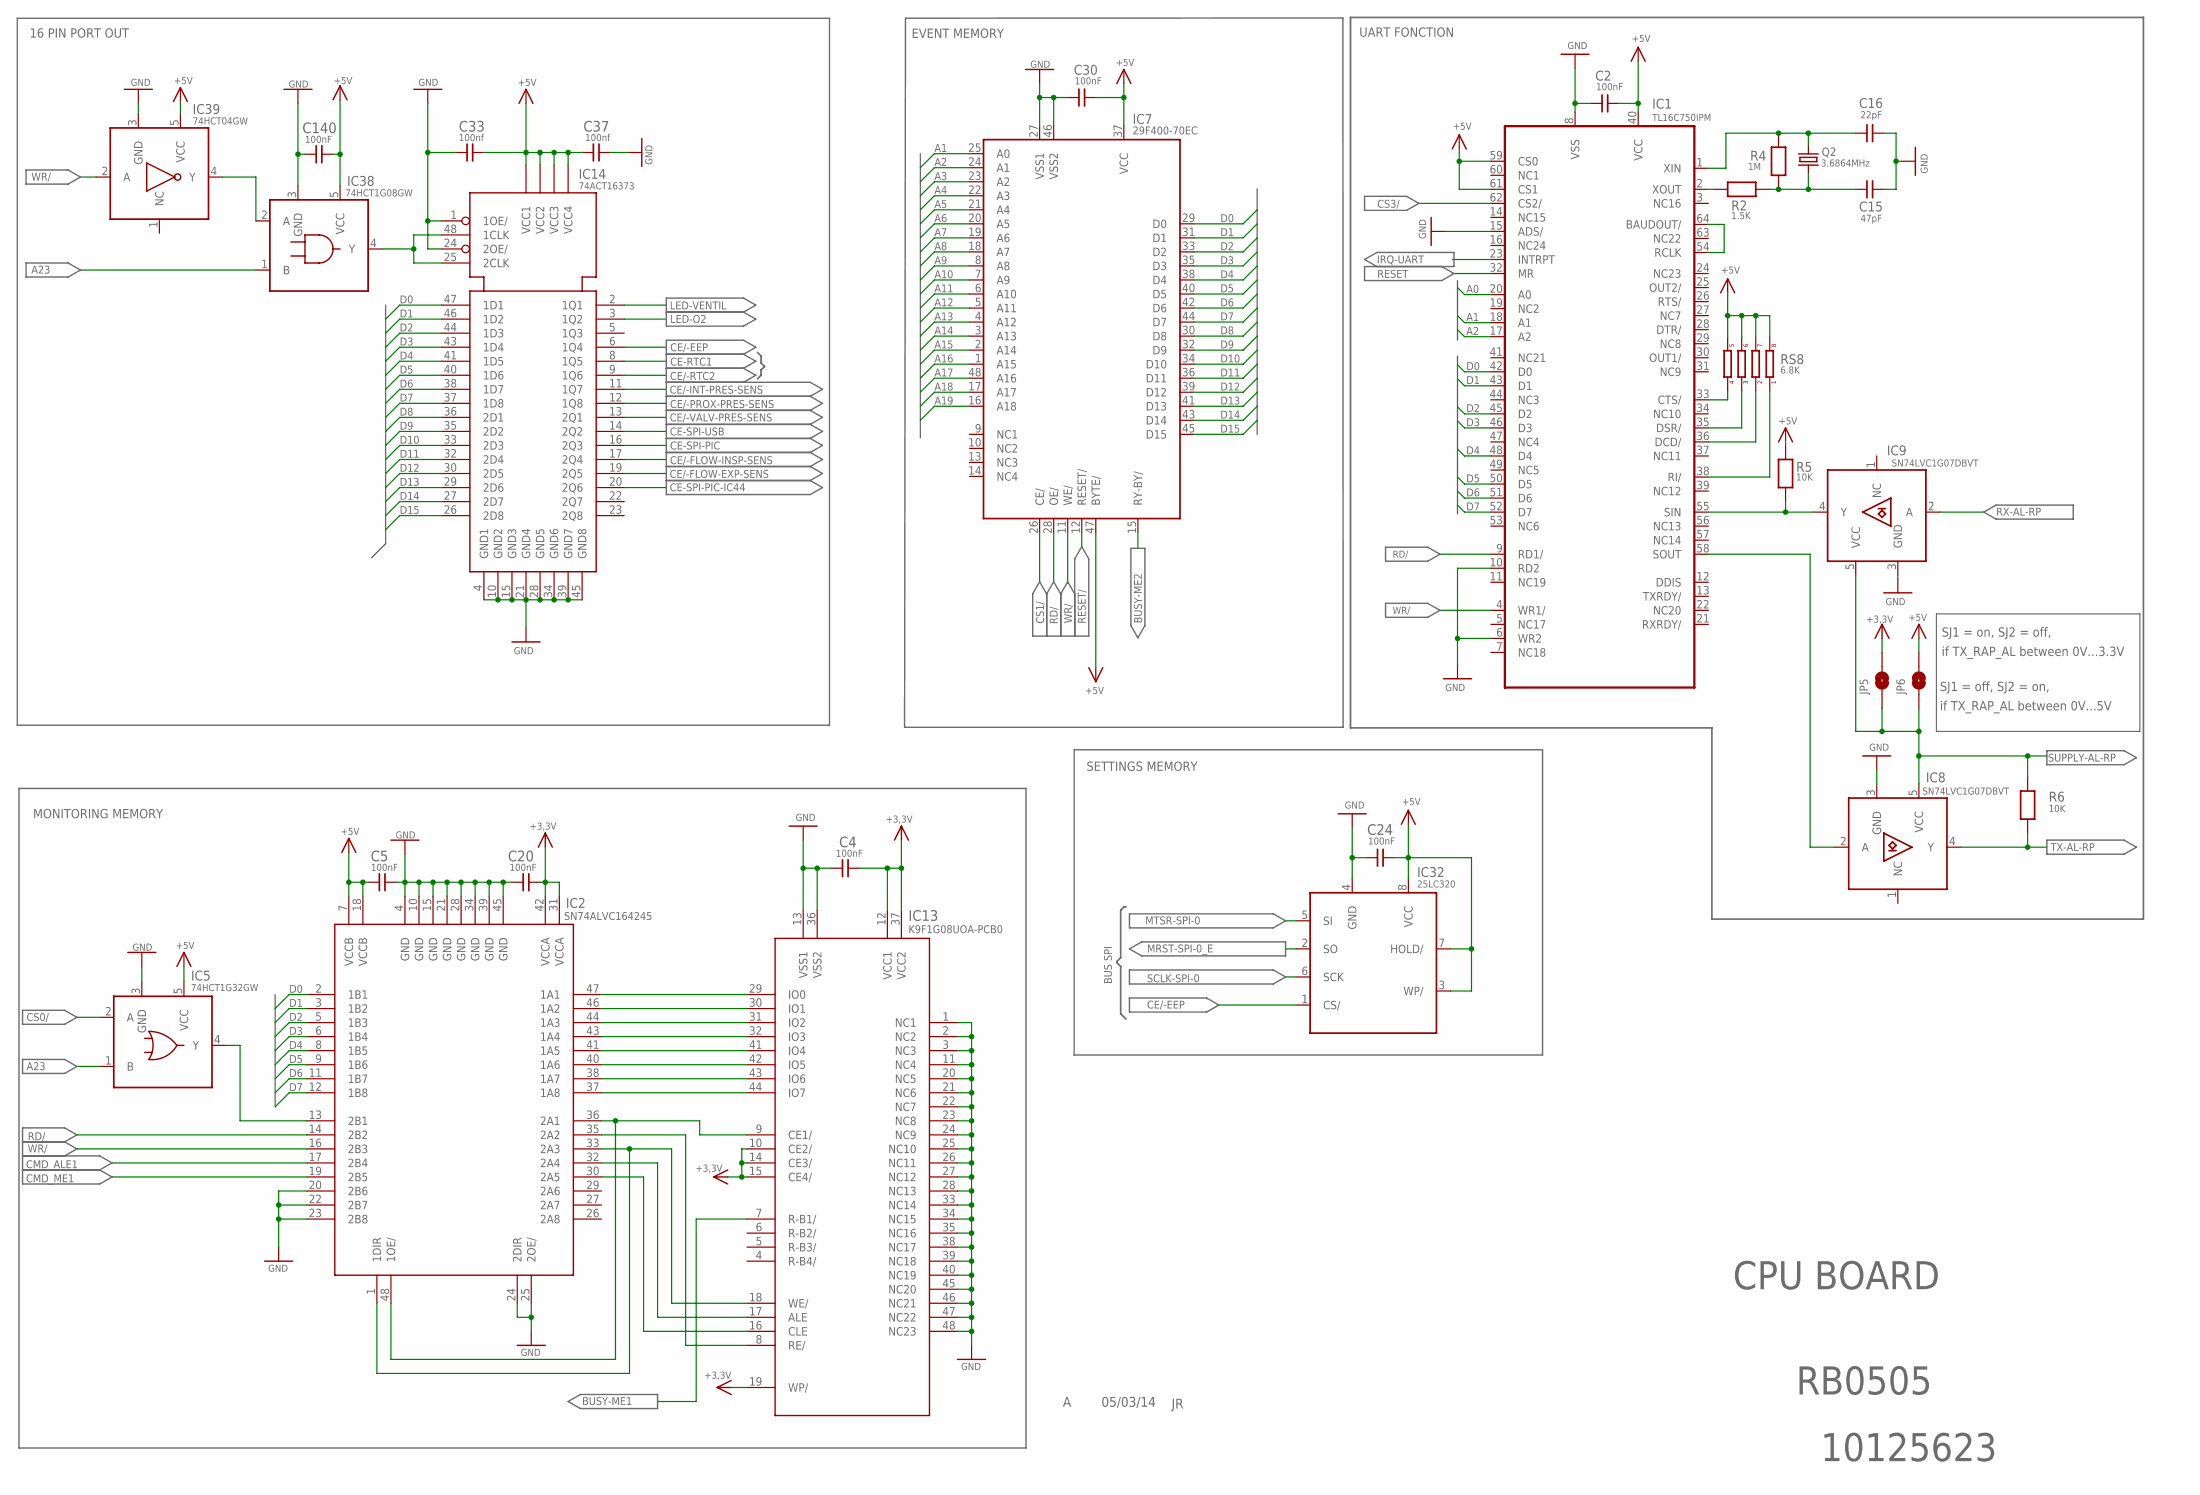
[picture p191: schematic 10125623A00.sch, sheet 2]

Parts:
C2, C4, C24, C30, C140: 100nF; C0805
C5, C20: 100nF; C0603
C15: 47pF; C0805
C16: 22pF; C0805
C33, C37: 100nf; C0805
IC1: TL16C750IPM; TQFP64
IC2: SN74ALVC164245; TSSOP48
IC5: 74HCT1G32GW; SOT23-5
IC7: Am29F400-EC; TS048
IC8, IC9: SN74LVC1G07DBVT; SOT753_DBV
IC13: K9F1G08UOA-PCB0; TS048
IC14: 74ACT16373; TSSOP48
IC32: 25LC320; SOIC8
IC38: 74HCT1G08GW; SOT23-5
IC39: 74HCT04GW; SOT23-5
JP5, JP6: JUMP_0U; 0805
Q2: 3.6864MHz; HC49UP
R2: 1.5K; R0805
R4: 1M; R0805
R5, R6: 10K; R0805
RS8: 6.8K; BCN16_4_

Connections:
+3,3V: C4.1, C20.1, IC2.31 (VCCA), IC2.42 (VCCA), IC13.10 (CE2/), IC13.12 (VCC1), IC13.14 (CE3/), IC13.15 (CE4/), IC13.19 (WP/), IC13.37 (VCC2), JP5.2
+5V: C2.1, C5.2, C24.1, C30.1, C33.1, C37.2, C140.2, IC1.40 (VCC), IC1.59 (CS0), IC1.61 (CS1), IC2.7 (VCCB), IC2.18 (VCCB), IC5.5 (VCC), IC7.37 (VCC), IC7.47 (BYTE/), IC14.7 (VCC1), IC14.18 (VCC2), IC14.31 (VCC3), IC14.42 (VCC4), IC32.3 (WP/), IC32.7 (HOLD/), IC32.8 (VCC), IC38.5 (VCC), IC39.5 (VCC), JP6.2, R5.2, RS8.5, RS8.6, RS8.7, RS8.8
A0: IC1.20 (A0)
A1: IC1.18 (A1), IC7.25 (A0)
A2: IC1.17 (A2), IC7.24 (A1)
A3: IC7.23 (A2)
A4: IC7.22 (A3)
A5: IC7.21 (A4)
A6: IC7.20 (A5)
A7: IC7.19 (A6)
A8: IC7.18 (A7)
A9: IC7.8 (A8)
A10: IC7.7 (A9)
A11: IC7.6 (A10)
A12: IC7.5 (A11)
A13: IC7.4 (A12)
A14: IC7.3 (A13)
A15: IC7.2 (A14)
A16: IC7.1 (A15)
A17: IC7.48 (A16)
A18: IC7.17 (A17)
A19: IC7.16 (A18)
A23: IC5.1 (B), IC38.1 (B)
BUSY-ME1: IC13.7 (R-B1/)
BUSY-ME2: IC7.15 (RY-BY/)
CE-RTC1: IC14.8 (1Q5)
CE-SPI-PIC: IC14.16 (2Q3)
CE-SPI-PIC-IC44: IC14.20 (2Q6)
CE-SPI-USB: IC14.14 (2Q2)
CE/-EEP: IC14.6 (1Q4), IC32.1 (CS/)
CE/-FLOW-EXP-SENS: IC14.19 (2Q5)
CE/-FLOW-INSP-SENS: IC14.17 (2Q4)
CE/-INT-PRES-SENS: IC14.11 (1Q7)
CE/-PROX-PRES-SENS: IC14.12 (1Q8)
CE/-RTC2: IC14.9 (1Q6)
CE/-VALV-PRES-SENS: IC14.13 (2Q1)
CMD_ALE1: IC2.17 (2B4)
CMD_ME1: IC2.19 (2B5)
CS0/: IC5.2 (A)
CS1/: IC7.26 (CE/)
CS3/: IC1.62 (CS2/)
D0: IC1.42 (D0), IC2.2 (1B1), IC7.29 (D0), IC14.47 (1D1)
D1: IC1.43 (D1), IC2.3 (1B2), IC7.31 (D1), IC14.46 (1D2)
D2: IC1.45 (D2), IC2.5 (1B3), IC7.33 (D2), IC14.44 (1D3)
D3: IC1.46 (D3), IC2.6 (1B4), IC7.35 (D3), IC14.43 (1D4)
D4: IC1.48 (D4), IC2.8 (1B5), IC7.38 (D4), IC14.41 (1D5)
D5: IC1.50 (D5), IC2.9 (1B6), IC7.40 (D5), IC14.40 (1D6)
D6: IC1.51 (D6), IC2.11 (1B7), IC7.42 (D6), IC14.38 (1D7)
D7: IC1.52 (D7), IC2.12 (1B8), IC7.44 (D7), IC14.37 (1D8)
D8: IC7.30 (D8), IC14.36 (2D1)
D9: IC7.32 (D9), IC14.35 (2D2)
D10: IC7.34 (D10), IC14.33 (2D3)
D11: IC7.36 (D11), IC14.32 (2D4)
D12: IC7.39 (D12), IC14.30 (2D5)
D13: IC7.41 (D13), IC14.29 (2D6)
D14: IC7.43 (D14), IC14.27 (2D7)
D15: IC7.45 (D15), IC14.26 (2D8)
GND: C2.2, C4.2, C5.1, C15.2, C16.1, C20.2, C24.2, C30.2, C33.2, C37.1, C140.1, IC1.6 (WR2), IC1.8 (VSS), IC1.10 (RD2), IC1.15 (ADS/), IC2.4 (GND), IC2.10 (GND), IC2.15 (GND), IC2.20 (2B6), IC2.21 (GND), IC2.22 (2B7), IC2.23 (2B8), IC2.24 (2DIR), IC2.25 (2OE/), IC2.28 (GND), IC2.34 (GND), IC2.39 (GND), IC2.45 (GND), IC5.3 (GND), IC7.27 (VSS1), IC7.46 (VSS2), IC8.3 (GND), IC9.3 (GND), IC13.1 (NC1), IC13.2 (NC2), IC13.3 (NC3), IC13.11 (NC4), IC13.13 (VSS1), IC13.20 (NC5), IC13.21 (NC6), IC13.22 (NC7), IC13.23 (NC8), IC13.24 (NC9), IC13.25 (NC10), IC13.26 (NC11), IC13.27 (NC12), IC13.28 (NC13), IC13.33 (NC14), IC13.34 (NC15), IC13.35 (NC16), IC13.36 (VSS2), IC13.38 (NC17), IC13.39 (NC18), IC13.40 (NC19), IC13.45 (NC20), IC13.46 (NC21), IC13.47 (NC22), IC13.48 (NC23), IC14.1 (1OE/), IC14.4 (GND1), IC14.10 (GND2), IC14.15 (GND3), IC14.21 (GND4), IC14.24 (2OE/), IC14.28 (GND5), IC14.34 (GND6), IC14.39 (GND7), IC14.45 (GND8), IC32.4 (GND), IC38.3 (GND), IC39.3 (GND)
IRQ-UART: IC1.23 (INTRPT)
LED-O2: IC14.3 (1Q2)
LED-VENTIL: IC14.2 (1Q1)
MRST-SPI-0_E: IC32.2 (SO)
MTSR-SPI-0: IC32.5 (SI)
unnamed: IC2.47 (1A1), IC13.29 (IO0)
unnamed: IC38.2 (A), IC39.4 (Y)
unnamed: C16.2, IC1.1 (XIN), Q2.1, R4.2
unnamed: IC2.13 (2B1), IC5.4 (Y)
unnamed: IC14.25 (2CLK), IC14.48 (1CLK), IC38.4 (Y)
unnamed: C15.1, Q2.2, R2.2, R4.1
unnamed: IC1.2 (XOUT), R2.1
unnamed: IC1.54 (RCLK), IC1.64 (BAUDOUT/)
unnamed: IC2.36 (2A1), IC2.48 (1OE/), IC13.9 (CE1/)
unnamed: IC2.46 (1A2), IC13.30 (IO1)
unnamed: IC2.44 (1A3), IC13.31 (IO2)
unnamed: IC2.43 (1A4), IC13.32 (IO3)
unnamed: IC1.33 (CTS/), RS8.4
unnamed: IC1.35 (DSR/), RS8.3
unnamed: IC1.36 (DCD/), RS8.2
unnamed: IC1.38 (RI/), RS8.1
unnamed: IC1.58 (SOUT), IC8.2 (A)
unnamed: IC2.41 (1A5), IC13.41 (IO4)
unnamed: IC2.40 (1A6), IC13.42 (IO5)
unnamed: IC2.35 (2A2), IC13.8 (RE/)
unnamed: IC2.32 (2A4), IC13.17 (ALE)
unnamed: IC2.30 (2A5), IC13.16 (CLE)
unnamed: IC2.38 (1A7), IC13.43 (IO6)
unnamed: IC2.37 (1A8), IC13.44 (IO7)
unnamed: IC2.1 (1DIR), IC2.33 (2A3), IC13.18 (WE/)
RD/: IC1.9 (RD1/), IC2.14 (2B2), IC7.28 (OE/)
RESET: IC1.32 (MR)
RESET/: IC7.12 (RESET/)
RX-AL-RP: IC9.2 (A)
RXD2: IC1.55 (SIN), IC9.4 (Y), R5.1
SCLK-SPI-0: IC32.6 (SCK)
SUPPLY-AL-RP: IC8.5 (VCC), IC9.5 (VCC), JP5.1, JP6.1, R6.2
TX-AL-RP: IC8.4 (Y), R6.1
WR/: IC1.4 (WR1/), IC2.16 (2B3), IC7.11 (WE/), IC39.2 (A)

Notes on the sheet:
MONITORING MEMORY
16 PIN PORT OUT
UART FONCTION
SJ1 = on, SJ2 = off,
if TX_RAP_AL between 0V...3.3V
SJ1 = off, SJ2 = on,
if TX_RAP_AL between 0V...5V
BUS SPI
SETTINGS MEMORY
CPU BOARD
RB0505
10125623
05/03/14
EVENT MEMORY
29F400-70EC

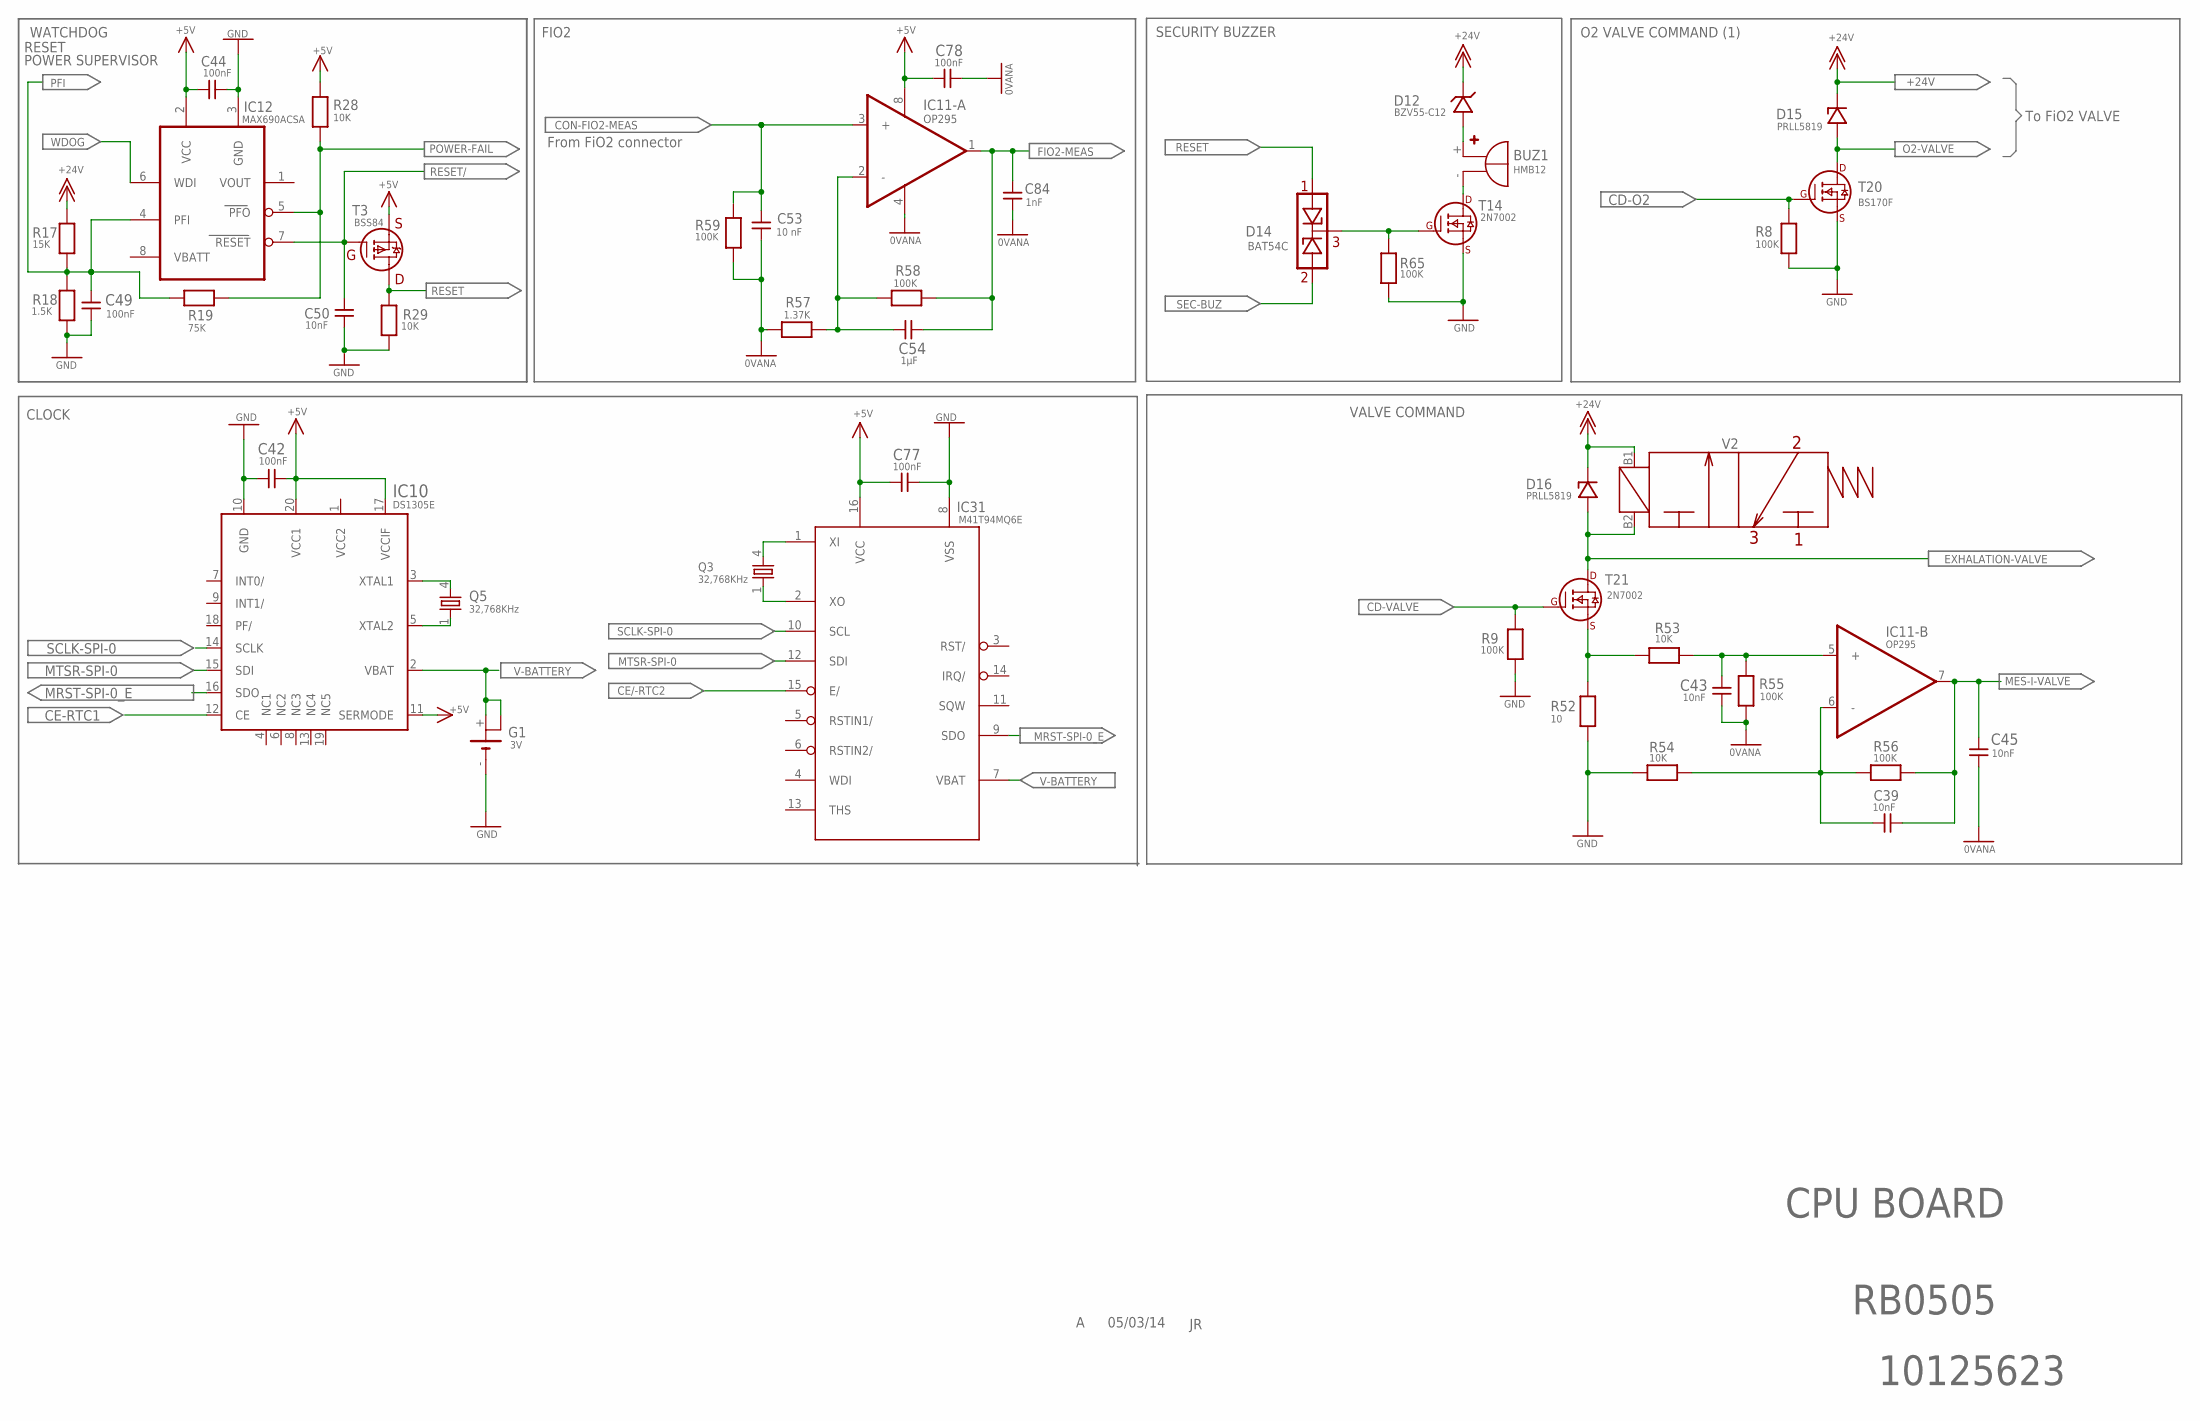
[picture p192: schematic 10125623A00.sch, sheet 3]

Parts:
BUZ1: HMB12; F/HMB
C39, C43, C45, C50: 10nF; C0805
C42, C44, C49, C77, C78: 100nF; C0805
C53: 10 nF; C0805
C54: 1µF; C0805
C84: 1nF; C0805
D12: BZV55-C12; SOT23DIO
D14: BAT54C; SOT23_DI
D15, D16: PRLL5819; SOD87
G1: 3V; KEY_3000
IC10: DS1305E; TSSOP20
IC11: OP295; SO8
IC12: MAX690ACSA; SO08
IC31: M41T94MQ6E; SO16
Q3, Q5: 32,768KHz; 86SMX
R8, R9, R55, R56, R58, R59, R65: 100K; R0805
R17: 15K; R0805
R18: 1.5K; R0805
R19: 75K; R0805
R28, R29, R53, R54: 10K; R0805
R52: 10; R0805
R57: 1.37K; R0805
T3: BSS84; SOT23MOS
T14, T21: 2N7002; DPAK
T20: BS170F; DPAK
V2: FAS-PPS-1P-3NIP-INJ

Connections:
0VANA: C43.1, C45.1, C53.1, C78.1, C84.1, IC11.4 (GND), R55.1, R57.1, R59.1
+5V: C42.1, C44.1, C77.2, C78.2, IC10.11 (SERMODE), IC10.17 (VCCIF), IC10.20 (VCC1), IC11.8 (VCC), IC12.2 (VCC), IC31.16 (VCC), R28.2, T3.S
+24V: D12.3 (K), D15.K, D16.K, R17.2, V2.B1
CD-O2: R8.2, T20.G (GATE)
CD-VALVE: R9.2, T21.G (GATE)
CE-RTC1: IC10.12 (CE)
CE/-RTC2: IC31.15 (E/)
CON-FIO2-MEAS: C53.2, IC11.3 (+), R59.2
EXHALATION-VALVE: D16.A, T21.D (DRAIN), V2.B2
FIO2-MEAS: C54.2, C84.2, IC11.1 (OUT), R58.2
GND: C42.2, C44.2, C49.1, C50.1, C77.1, G1.-, IC10.10 (GND), IC12.3 (GND), IC31.8 (VSS), R8.1, R9.1, R18.1, R29.2, R52.1, R54.1, R65.1, T14.S (SOURCE), T20.S (SOURCE)
IC11-B: C39.2, IC11.6 (-), R54.2, R56.2
MES-I-VALVE: C39.1, C45.2, IC11.7 (OUT), R56.1
MRST-SPI-0_E: IC10.16 (SDO), IC31.9 (SDO)
MTSR-SPI-0: IC10.15 (SDI), IC31.12 (SDI)
unnamed: C54.1, IC11.2 (-), R57.2, R58.1
unnamed: BUZ1.+, D12.1 (A)
unnamed: IC10.3 (XTAL1), Q5.4 (2)
unnamed: IC10.5 (XTAL2), Q5.1
unnamed: IC31.1 (XI), Q3.4 (2)
unnamed: IC31.2 (XO), Q3.1
unnamed: R52.2, R53.1, T21.S (SOURCE)
unnamed: C43.2, IC11.5 (+), R53.2, R55.2
unnamed: BUZ1.-, T14.D (DRAIN)
unnamed: D14.3, R65.2, T14.G (GATE)
O2-VALVE: D15.A, T20.D (DRAIN)
PFI: C49.2, IC12.4 (PFI), R17.1, R18.2, R19.1
POWER-FAIL: IC12.5 (PFO), R19.2, R28.1
RESET: D14.1, R29.1, T3.D
RESET/: C50.2, IC12.7 (RESET), T3.G
SCLK-SPI-0: IC10.14 (SCLK), IC31.10 (SCL)
SEC-BUZ: D14.2
V-BATTERY: G1.+, G1.PLUS, IC10.2 (VBAT), IC31.7 (VBAT)
WDOG: IC12.6 (WDI)

Notes on the sheet:
CLOCK
SECURITY BUZZER
O2 VALVE COMMAND (1)
To FiO2 VALVE
VALVE COMMAND
FIO2
From FiO2 connector
CPU BOARD
RB0505
10125623
05/03/14
WATCHDOG
RESET
POWER SUPERVISOR
